opencomputeproject/Time-Appliance-Project/SOM/FPGA/Binaries/200T/README.md

# 200T FPGA version for the Artix 7 AC7200 SOM Module

* TimeCard200T.bit to flash the FPGA (volatile)
* Factory_TimeCard200T.bin to load the SPI flash via JTAG (Golden Image + Update Image)
* **IMPORTANT**: TimeCard200T.bin to updated the SPI flash via SPI starting @ **0x00800000** (Update Image only)
* TimeCard200T_Gotham.bin is basically the same as TimeCard200T.bin but the file has additional header information ([See tft tool](https://github.com/opencomputeproject/Time-Appliance-Project/tree/master/Software/tft))
