opencomputeproject/Time-Appliance-Project/FPGA/Binary/Production/Readme_Production.pdf

## 1 Design Overview

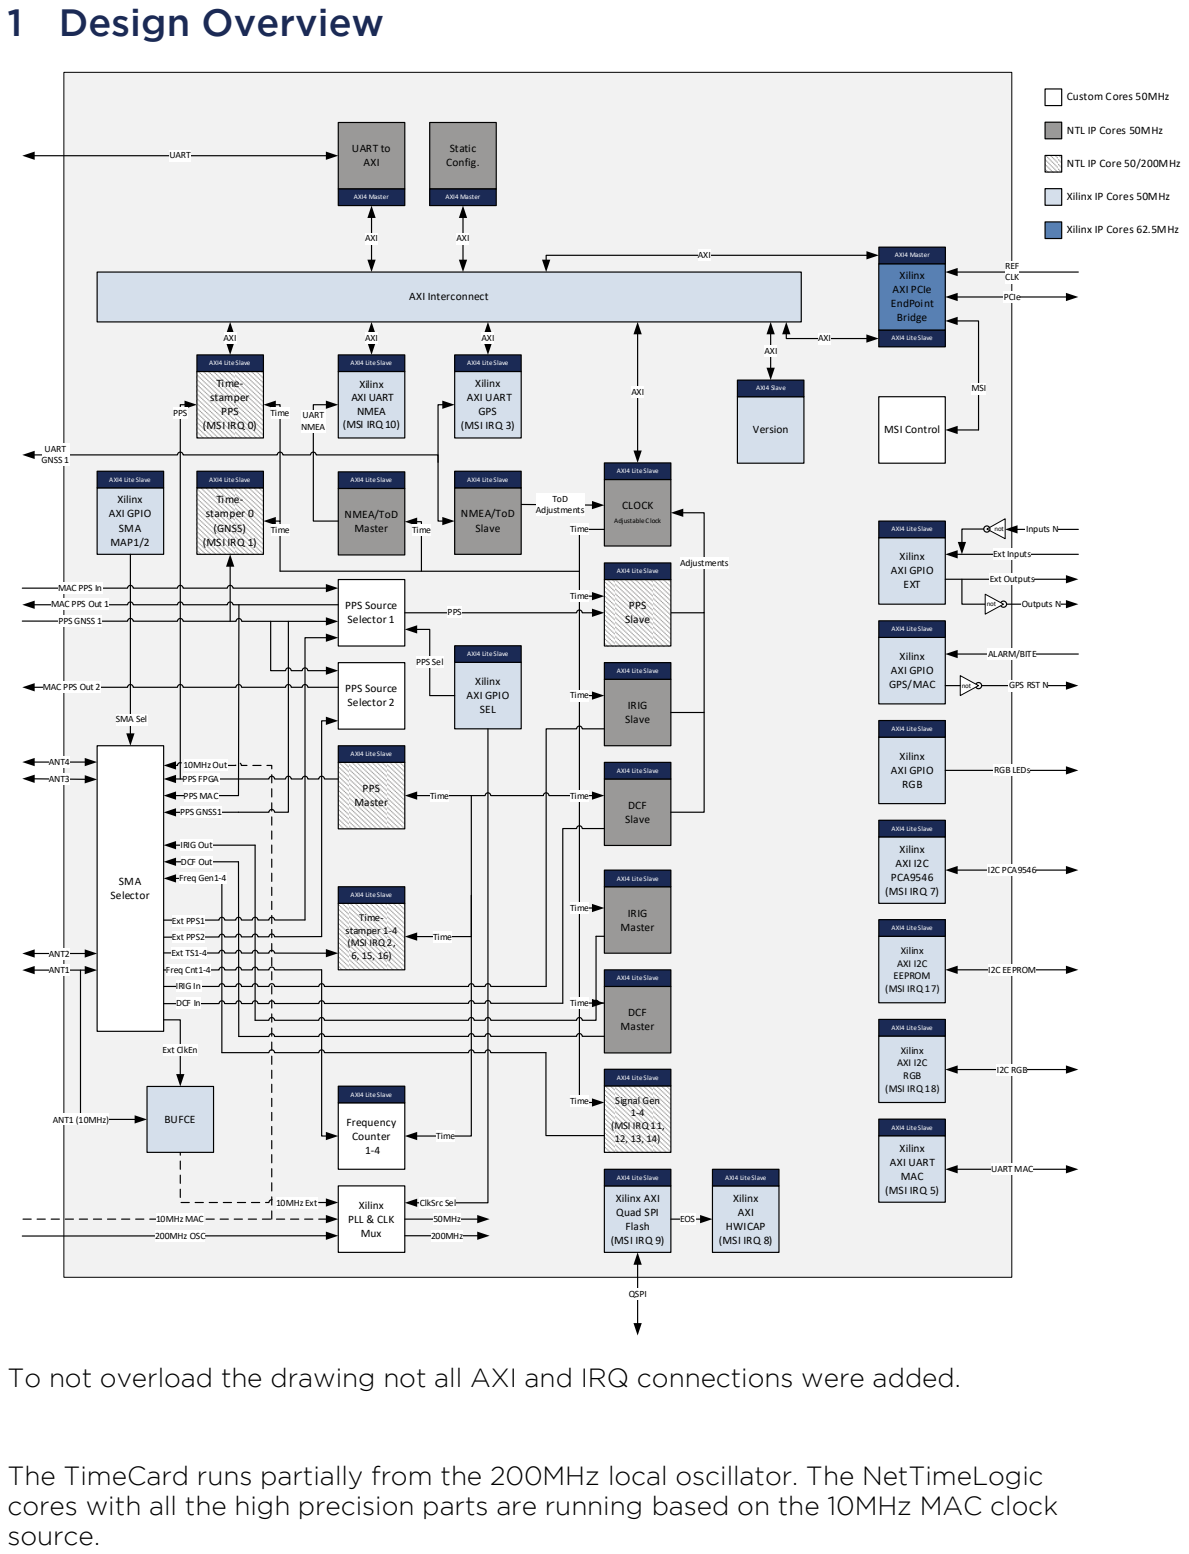
[picture p84: page 1]
Time; PPS; 200MHz OSC; ToD Adjustments; Adjustments; 50MHz; 200MHz; 10MHz Out; Xilinx AXI GPIO GPS/MAC; AXI4 Lite Slave; Xilinx AXI GPIO EXT; (MSI IRQ 5); Ext Outputs; Ext Inputs; GPS RST N; ALARM/BITE; not; 10MHz Ext; Xilinx AXI I2C PCA9546 (MSI IRQ 7); I2C PCA9546; AXI; Xilinx AXI Quad SPI Flash (MSI IRQ 9); QSPI; Xilinx AXI HWICAP (MSI IRQ 8); EOS; ANT2; ANT1; ANT4; ANT3; SMA Selector; Ext ClkEn; ANT1 (10MHz); BUFCE; Xilinx AXI PCIe EndPoint Bridge; AXI4 Master; PCIe; REF CLK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

NTL IP Cores 50MHz

NTL IP Core 50/200MHz

Xilinx IP Cores 50MHz

Xilinx IP Cores 62.5MHz

NMEA/ToD Master

MAC PPS In
MAC PPS Out 1
PPS GNSS 1

MAC PPS Out 2

AXI4 Lite Slave
Xilinx
AXI UART MAC

PLL & CLK Mux

To not overload the drawing not all AXI and IRQ connections were added.

The TimeCard runs partially from the 200MHz local oscillator. The NetTimeLogic
cores with all the high precision parts are running based on the 10MHz MAC clock
source.

## 1.1 Status LEDs

At the moment the Status LEDs are not connected to the AXI GPIO Ext and they

are used directly by the FPGA.

LED1: Alive LED of the FPGA internal Clock (50MHz)

LED2: Alive LED of the PCIe clocking part (62.5MHz)

LED3: PPS of the FPGA (Time of the Local Clock via PPS Master)

LED4: PPS of the MAC (differential inputs from the MAC via diff-buffer)

The RGB LEDs (SMA1-4 and GNSS) can be controlled via I2C or GPIO (depending

on assembly option).
In case the Fall-Back image is loaded all four SMA LEDs are blinking red.

## 1.2 AXI Address Mapping

The AXI interconnect has three masters which all have access to the slaves. One is the AXI PCIe interface and the other UART to AXI have all the time access. The

Static Configuration only does a basic configuration after reset.

The AXI Slave Interfaces have following addresses:

AXI Slave interface | Slave | Offset Address | High Address
S_AXI_CTL | AXI PCIe Control | 0x0001_0000 | 0x0001_0FFF
axi4l_slave | Version | 0x0002_0000 | 0x0002_0FFF
S_AXI | AXI GPIO Ext | 0x0010_0000 | 0x0010_0FFF
S_AXI | AXI GPIO GPS/MAC | 0x0011_0000 | 0x0011_0FFF
S_AXI | AXI GPIO SEL | 0x0013_0000 | 0x0013_0FFF
S_AXI | AXI GPIO SMA MAP1 | 0x0014_0000 | 0x0014_0FFF
S_AXI | AXI I2C PCA9546 | 0x0015_0000 | 0x0015_FFFF
S_AXI | AXI UART 16550 GPS | 0x0016_0000 | 0x0016_FFFF
S_AXI | AXI UART 16550 GPS2 | 0x0017_0000 | 0x0017_FFFF
S_AXI | AXI UART 16550 MAC | 0x0018_0000 | 0x0018_FFFF
S_AXI | AXI UART 16550 NMEA | 0x0019_0000 | 0x0019_FFFF
S_AXI | AXI I2C EEPROM | 0x0020_0000 | 0x0020_FFFF
S_AXI | AXI I2C RGB | 0x0021_0000 | 0x0021_FFFF
S_AXI | AXI GPIO SMA MAP2 | 0x0022_0000 | 0x0022_0FFF
S_AXI | AXI GPIO RGB | 0x0023_0000 | 0x0023_FFFF
S_AXI_LITE | AXI HWICAP | 0x0030_0000 | 0x0030_FFFF
AXI_LITE | AXI Quad SPI Flash | 0x0031_0000 | 0x0031_FFFF
axi4l_slave | NTL Adj. Clock | 0x0100_0000 | 0x0100_FFFF

axi4l_slave | NTL Signal TS0 (GNSS) | 0x0101_0000 | 0x0101_FFFF
axi4l_slave | NTL Signal TS1 | 0x0102_0000 | 0x0102_FFFF
axi4l_slave | NTL PPS Master | 0x0103_0000 | 0x0103_FFFF
axi4l_slave | NTL PPS Slave | 0x0104_0000 | 0x0104_FFFF
axi4l_slave | NTL TOD Slave | 0x0105_0000 | 0x0105_FFFF
axi4l_slave | NTL Signal TS2 | 0x0106_0000 | 0x0106_FFFF
axi4l_slave | NTL IRIG Slave | 0x0107_0000 | 0x0107_FFFF
axi4l_slave | NTL IRIG Master | 0x0108_0000 | 0x0108_FFFF
axi4l_slave | NTL DCF Slave | 0x0109_0000 | 0x0109_FFFF
axi4l_slave | NTL DCF Master | 0x010A_0000 | 0x010A_FFFF
axi4l_slave | NTL TOD Master | 0x010B_0000 | 0x010B_FFFF
axi4l_slave | NTL Signal TS PPS | 0x010C_0000 | 0x010C_FFFF
axi4l_slave | NTL Signal Generator1 | 0x010D_0000 | 0x010D_FFFF
axi4l_slave | NTL Signal Generator2 | 0x010E_0000 | 0x010E_FFFF
axi4l_slave | NTL Signal Generator3 | 0x010F_0000 | 0x010F_FFFF
axi4l_slave | NTL Signal Generator4 | 0x0110_0000 | 0x0110_FFFF
axi4l_slave | NTL Signal TS3 | 0x0111_0000 | 0x0111_FFFF
axi4l_slave | NTL Signal TS4 | 0x0112_0000 | 0x0112_FFFF
axi4l_slave | Frequency Counter 1 | 0x0120_0000 | 0x0120_FFFF
axi4l_slave | Frequency Counter 2 | 0x0121_0000 | 0x0121_FFFF
axi4l_slave | Frequency Counter 3 | 0x0122_0000 | 0x0122_FFFF
axi4l_slave | Frequency Counter 4 | 0x0123_0000 | 0x0123_FFFF

NOTE:

The Version Slave has one single 32-Bit Register. The upper 16 Bits show the version number of the golden image and the lower 16 Bits the version number of

the regular image.

E.g.
Register 0x0200_0000 of the Golden image shows: 0x8001_0000

Register 0x0200_0000 of the Regular image shows: 0x0000_8003

If the lower 16 Bits are 0x0000 the Golden image has booted. Additionally, the SMA LEDs are blinking red.

## 1.3 Clock Adjustment Sources

The Adjustable Clock supports different adjustment sources:

- PPS (with GNSS) (register value 3)
- IRIG (register value 2)
- DCF (register value 6)

By default, PPS with GNSS is selected. The other time sources can be selected via

the NTL Adj. Clock ClockSelect Register (Offset: 0x0100_0008).

## 1.4 Message-Signaled Interrupt Mapping

The interrupts in the design are connected to the MSI Vector of the AXI Memory

Mapped to PCI Express Core via a MSI controller. The PCI Express Core needs to set the MSI_enable to ‘1’. The MSI controller sends INTX_MSI Request with the

MSI_Vector_Num to the PCI Express Core and with the INTX_MSI_Grant the interrupt is acknowledged. If there are several interrupts pending the messages are sent with the round-robin principle. Level interrupts (e.g. AXI UART 16550) are taking at least one round for the next interrupt.

MSI Number | Interrupt Source
0 | NTL Signal TS PPS
1 | NTL Signal TS0
2 | NTL Signal TS1
3 | AXI UART 16550 GPS
4 | AXI UART 16550 GPS2
5 | AXI UART 16550 MAC
6 | NTL Signal TS2
7 | AXI I2C PCA9546
8 | AXI HWICAP
9 | AXI Quad SPI Flash
10 | AXI UART 16550 NMEA
11 | NTL Signal Generator1
12 | NTL Signal Generator2
13 | NTL Signal Generator3
14 | NTL Signal Generator4
15 | NTL Signal TS3
16 | NTL Signal TS4
17 | AXI I2C EEPROM
18 | AXI I2C RGB

## 1.5 Connectors (SMA) / SMA Connection Matrix

The SMA connectors have following default mapping:

ANT1:

10MHz Clock input

ANT2:

PPS Input

ANT3:
10MHz Clock output (looped 10MHz Clock →MAC RF OUT

(after clock buffer)

ANT4:
PPS Output from the PPS Master

This default mapping and the direction can be changed via AXI GPIO SMA MAP1 and AXI GPIO SMA MAP2.

GPIO is used to select the inputs and GPIO2 to select the outputs.

AXI GPIO SMA MAP1

Mapping of Input 1 (ANT1) with GPIO Bit 15 downto 0:

0 | 10MHz Clock from SMA connector (default)
1 | External PPS 1 (goes to PPS Source Selector 1)
2 | External PPS 2 (goes to PPS Source Selector 2)
4 | Signal goes to TS1
8 | Signal goes to TS2
16 | Signal goes IRIG Slave
32 | Signal goes to DCF Slave
64 | Signal goes to TS3
128 | Signal goes to TS4
256 | Signal goes to Frequency Counter 1
512 | Signal goes to Frequency Counter 2

1024 Signal goes to Frequency Counter 3

2048 Signal goes to Frequency Counter 4

32768 | Input Enable (default 1 → ANT1 is input)

The input can be mapped to several sinks. As example with the value 5 the

input is mapped as external PPS 1 and additionally it goes to TS1.

NOTE:
To use ANT1 as a system clock source only 0 is possible.

GNSS

INPUT: Default 10MHz

INPUT: Default 1 PPS

Output: Default 10MHz

Output: Default 1 PPS

ANT1

ANT2

ANT3

ANT4

Mapping of Input 2 (ANT2) with GPIO Bit 31 downto 16:

0 | no mapping of ANT2
1 | External PPS 1 (goes to PPS Source Selector 1) (default)
2 | External PPS 2 (goes to PPS Source Selector 2)
4 | Signal goes to TS1
8 | Signal goes to TS2
16 | Signal goes IRIG Slave
32 | Signal goes to DCF Slave
64 | Signal goes to TS3
128 | Signal goes to TS4
256 | Signal goes to Frequency Counter 1
512 | Signal goes to Frequency Counter 2

1024 Signal goes to Frequency Counter 3

2048 Signal goes to Frequency Counter 4

32768 | Input Enable (default 1 → ANT2 is input)

The input can be mapped to several sinks. As example with the value 9 the

input is mapped as external PPS 1 and additionally it goes to TS2.

NOTE:
If a lower input has already a mapping to a sink the Input2 mapping will be

ignored.

Mapping of Output 3 (ANT3) with GPIO2 Bit 15 downto 0:
0 | 10MHz Clock Output from the MAC (default)
1 | PPS from the FPGA (PPS Master)
2 | PPS from the MAC
4 | PPS from GNSS 1
8 | PPS from GNSS 2
16 | IRIG Master Output
32 | DCF Master Output
64 | Signal Generator 1 Output
128 | Signal Generator 2 Output
256 | Signal Generator 3 Output
512 | Signal Generator 4 Output

8192 GND

16384 VCC

32768 | Output Enable (default 1 → ANT3 is output)

Every other value maps the 10MHz Clock Output from the MAC to the

output

Mapping of Output 4 (ANT4) with GPIO2 Bit 31 downto 16:

0 | 10MHz Clock Output from the MAC
1 | PPS from the FPGA (PPS Master) (default)
2 | PPS from the MAC
4 | PPS from GNSS 1
8 | PPS from GNSS 2
16 | IRIG Master Output
32 | DCF Master Output
64 | Signal Generator 1 Output
128 | Signal Generator 2 Output
256 | Signal Generator 3 Output
512 | Signal Generator 4 Output

8192 GND
16384 VCC
32768 | Output Enable (default 1 → ANT4 is output)

Every other value maps the PPS from the FPGA (PPS Master) to the output

AXI GPIO SMA MAP2
Mapping of Input 3 (ANT3) with GPIO Bit 15 downto 0:
0 | no mapping of ANT3
1 | External PPS 1 (goes to PPS Source Selector 1)
2 | External PPS 2 (goes to PPS Source Selector 2)
4 | Signal goes to TS1
8 | Signal goes to TS2
16 | Signal goes IRIG Slave
32 | Signal goes to DCF Slave
64 | Signal goes to TS3
128 | Signal goes to TS4
256 | Signal goes to Frequency Counter 1
512 | Signal goes to Frequency Counter 2

1024 Signal goes to Frequency Counter 3

2048 Signal goes to Frequency Counter 4

32768 | Input Enable (default 0 → ANT3 is output)

The input can be mapped to several sinks. As example with the value 5 the

input is mapped as external PPS 1 and additionally it goes to TS1.

Mapping of Input 4 (ANT4) with GPIO Bit 31 downto 16:

0 | no mapping of ANT2
1 | External PPS 1 (goes to PPS Source Selector 1)
2 | External PPS 2 (goes to PPS Source Selector 2)
4 | Signal goes to TS1
8 | Signal goes to TS2
16 | Signal goes IRIG Slave
32 | Signal goes to DCF Slave
64 | Signal goes to TS3
128 | Signal goes to TS4
256 | Signal goes to Frequency Counter 1
512 | Signal goes to Frequency Counter 2

1024 Signal goes to Frequency Counter 3

2048 Signal goes to Frequency Counter 4

32768 | Input Enable (default 0 → ANT4 is output)

The input can be mapped to several sinks. As example with the value 9 the

input is mapped as external PPS 1 and additionally it goes to TS2.

NOTE:
If a lower input has already a mapping to a sink the Input4 mapping will be ignored.

Mapping of Output 1 (ANT1) with GPIO2 Bit 15 downto 0:

0 | 10MHz Clock Output from the MAC
1 | PPS from the FPGA (PPS Master)
2 | PPS from the MAC
4 | PPS from GNSS 1
8 | PPS from GNSS 2
16 | IRIG Master Output
32 | DCF Master Output
64 | Signal Generator 1 Output
128 | Signal Generator 2 Output
256 | Signal Generator 3 Output
512 | Signal Generator 4 Output

8192 GND

16384 VCC

32768 | Output Enable (default 0 → ANT1 is input)

Every other value maps the 10MHz Clock Output from the MAC to the

output

Mapping of Output 2 (ANT2) with GPIO2 Bit 31 downto 16:
0 | 10MHz Clock Output from the MAC
1 | PPS from the FPGA (PPS Master)
2 | PPS from the MAC
4 | PPS from GNSS 1
8 | PPS from GNSS 2
16 | IRIG Master Output
32 | DCF Master Output
64 | Signal Generator 1 Output
128 | Signal Generator 2 Output
256 | Signal Generator 3 Output
512 | Signal Generator 4 Output

8192 GND

16384 VCC

32768 | Output Enable (default 0 → ANT2 is input)

Every other value maps the PPS from the FPGA (PPS Master) to the output.

## 1.6 GPIO Mapping

GPIO (Offset 0x0000)
GPIO2 (Offset 0x0008)

Inputs or Outputs might high or low active for the external signal level. The inversion is done in the FPGA. On the AXI GPIO always

active high is used. The inverted signals are underlined in the tables below.

AXI GPIO Ext

REG | Bit7 | Bit6 | Bit5 | Bit4 | Bit3 | Bit2 | Bit1 | Bit0
GPIO (in) | - Board | Rev2 | Board Rev1 | Board Rev0 | - | - | - | -
GPIO2 (out) | - | - | - | EEPROM WP | LED4 (NC atm) | LED3 (NC atm) | LED2 (NC atm) | LED1 (NC atm)
REG | Bit15 | Bit14 | Bit13 | Bit12 | Bit11 | Bit10 | Bit9 | Bit8
GPIO (in) | - | - | - | Bno Int | Lm75B Int3 | Lm75B Int2 | Lm75B Int1 | Sht3x Alert
GPIO2 (out) | - | Debug USB MuxSel | SMBUS I2C BufEn | Bno Boot | Bno Rst | Sht3x Rst | RGB Shut Down | Pca9546 Rst

AXI GPIO GPS/MAC

REG | Bit7 | Bit6 | Bit5 | Bit4 | Bit3 | Bit2 | Bit1 | Bit0
GPIO (in) | - | - | - | - | - | - | MAC BITE | MAC ALARM
GPIO2 (out) | - | - | - | - | - | - | - | GPS RST

AXI GPIO SEL

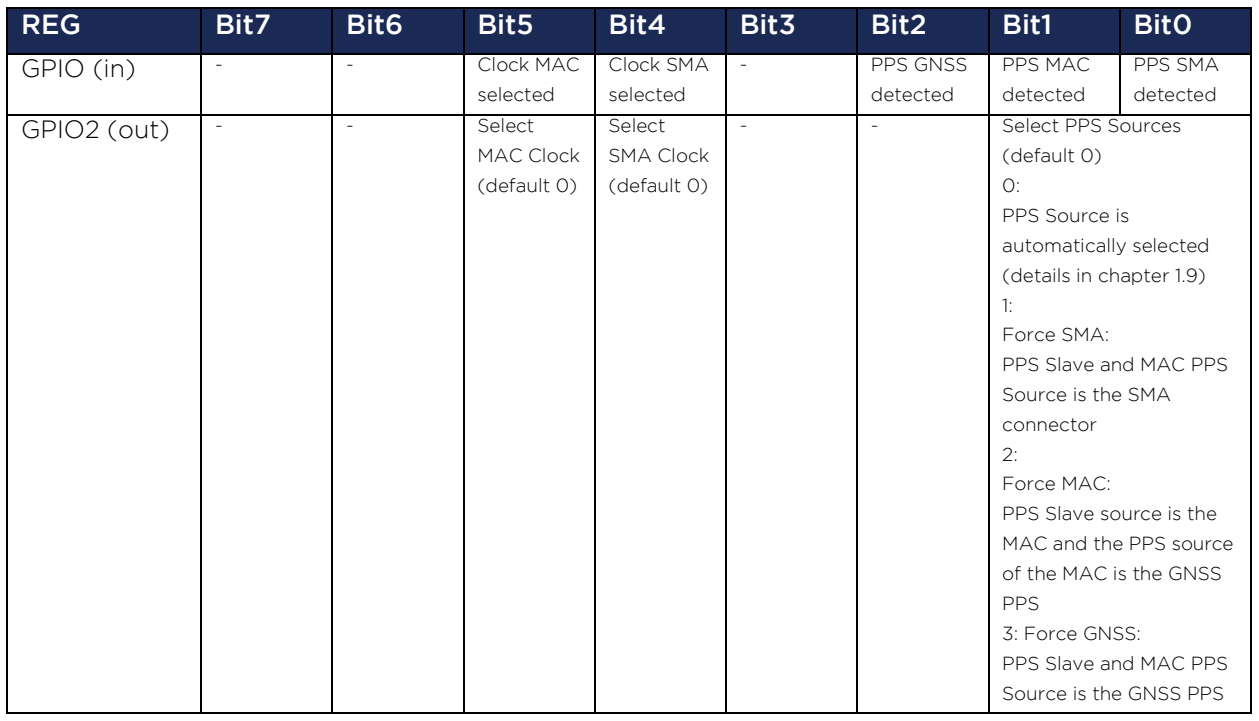
[picture p85: figure]
GPIO2 (out); Select; MAC Clock; (default 0); SMA Clock; Select PPS Sources; PPS Source is; automatically selected; (details in chapter 1.9); Force SMA:; PPS Slave and MAC PPS; Source is the SMA; connector; Force MAC:; PPS Slave source is the; MAC and the PPS source; of the MAC is the GNSS; PPS; 3: Force GNSS:; Source is the GNSS PPS

REG | Bit7 | Bit6 | Bit5 | Bit4 | Bit3 | Bit2 | Bit1 | Bit0
GPIO (in) | - | - | Clock MAC selected | Clock SMA selected | - PPS GNSS | detected | PPS MAC detected | PPS SMA detected

AXI GPIO RGB

‘1’: ON; ‘0’: OFF

| Bit7 | Bit6 | Bit5 | Bit4 | Bit3 | Bit2 | Bit1 | Bit0
GPIO (out) | - | SMA2 Blue | SMA2 Green | SMA2 Red | - SMA1 | Blue | SMA1 Green | SMA1 Red
| Bit15 | Bit14 | Bit13 | Bit12 | Bit11 | Bit10 | Bit9 | Bit8
GPIO (out) | - | SMA4 Blue | SMA4 Green | SMA4 Red | - SMA3 | Blue | SMA3 Green | SMA3 Red

| Bit23 | Bit22 | Bit21 | Bit20 | Bit19 | Bit18 | Bit17 | Bit16
GPIO (out) | - | - | - | - | - | GNSS Blue | GNSS Green | GNSS Red

AXI GPIO SMA MAP1 (ANT1/ANT2 as inputs, ANT3/ANT4 as outputs)

REG | Bit15 | Bit14-12 | Bit11 | B10 | Bit9 | Bit8 | Bit7 | Bit6 | Bit5 | Bit4 | Bit3 | Bit2 | Bit1 | Bit0
GPIO (out) | Input Enable | unused | ANT1 to Freq Cnt 4 input | ANT1 to Freq Cnt 3 input | ANT1 to Freq Cnt 2 input | ANT1 to Freq Cnt 1 input | ANT1 to TS4 input | ANT1 to TS3 input | ANT1 to DCF Slave | ANT1 to IRIG Slave | ANT1 to TS2 input | ANT1 to TS1 input | ANT1 to PPS 2 input | ANT1 to PPS 1 input
GPIO2 (out) | Output Enable

Bit 14-0 are 0: 10MHz to ANT3

Bit 0 is set: FPGA PPS to ANT3

Bit 1 is set: MAC PPS to ANT3

Bit 2 is set: GNSS1 PPS to ANT3

Bit 3 is set: GNSS2 PPS to ANT3

Bit 4 is set: IRIG Output to ANT3

Bit 5 is set: DCF Output to ANT3

Bit 6 is set: Signal Generator 1 to ANT3

Bit 7 is set: Signal Generator 2 to ANT3

Bit 8 is set: Signal Generator 3 to ANT3

Bit 9 is set: Signal Generator 4 to ANT3

Bit 13 is set: GND to ANT3

Bit 14 is set: VCC to ANT3

NOTE: only one single Bit (of Bit 14-0) can be set at the same time
REG | Bit31 | Bit30-28 | Bit27 | Bit26 | Bit25 | Bit24 | Bit23 | Bit22 | Bit21 | Bit20 | Bit19 | Bit18 | Bit17 | Bit16
GPIO (out) | Input Enable | unused | ANT2 to Freq Cnt 4 input | ANT2 to Freq Cnt 3 input | ANT2 to Freq Cnt 2 input | ANT2 to Freq Cnt 1 input | ANT2 to TS4 input | ANT2 to TS3 input | ANT2 to DCF Slave | ANT2 to IRIG Slave | ANT2 to TS2 input | ANT2 to TS1 input | ANT2 to PPS 2 input | ANT2 to PPS 1 input
GPIO2 (out) | Output Enable | Bit 30-16 are 0: 10MHz to ANT4 Bit 16 is set: FPGA PPS to ANT4

Bit 17 is set: MAC PPS to ANT4

Bit 18 is set: GNSS1 PPS to ANT4

Bit 19 is set: GNSS2 PPS to ANT4

Bit 20 is set: IRIG Output to ANT4

Bit 21 is set: DCF Output to ANT4

Bit 22 is set: Signal Generator 1 to ANT4

Bit 23 is set: Signal Generator 2 to ANT4

Bit 24 is set: Signal Generator 3 to ANT4

Bit 25 is set: Signal Generator 4 to ANT4

Bit 26 is set: GND to ANT4

Bit 27 is set: VCC to ANT4

NOTE: only one single Bit (of Bit 30-16) can be set at the same time

AXI GPIO SMA MAP2 (ANT1/ANT2 as outputs, ANT3/ANT4 as inputs)

REG | Bit15 | Bit14-12 | Bit11 | B10 | Bit9 | Bit8 | Bit7 | Bit6 | Bit5 | Bit4 | Bit3 | Bit2 | Bit1 | Bit0
GPIO (out) | Input Enable | unused | ANT3 to Freq Cnt 4 input | ANT3 to Freq Cnt 3 input | ANT3 to Freq Cnt 2 input | ANT3 to Freq Cnt 1 input | ANT3 to TS4 input | ANT3 to TS3 input | ANT3 to DCF Slave | ANT3 to IRIG Slave | ANT3 to TS2 input | ANT3 to TS1 input | ANT3 to PPS 2 input | ANT3 to PPS 1 input
GPIO2 (out) | Output Enable

Bit 14-0 are 0: 10MHz to ANT1

Bit 0 is set: FPGA PPS to ANT1

Bit 1 is set: MAC PPS to ANT1

Bit 2 is set: GNSS1 PPS to ANT1

Bit 3 is set: GNSS2 PPS to ANT1

Bit 4 is set: IRIG Output to ANT1

Bit 5 is set: DCF Output to ANT1

Bit 6 is set: Signal Generator 1 to ANT1

Bit 7 is set: Signal Generator 2 to ANT1

Bit 8 is set: Signal Generator 3 to ANT1

Bit 9 is set: Signal Generator 4 to ANT1

Bit 13 is set: GND to ANT1

Bit 14 is set: VCC to ANT1

NOTE: only one single Bit (of Bit 14-0) can be set at the same time

REG | Bit31 | Bit30-28 | Bit27 | Bit26 | Bit25 | Bit24 | Bit23 | Bit22 | Bit21 | Bit20 | Bit19 | Bit18 | Bit17 | Bit16
GPIO (out) | Input Enable | unused | ANT4 to Freq Cnt 4 input | ANT4 to Freq Cnt 3 input | ANT4 to Freq Cnt 2 input | ANT4 to Freq Cnt 1 input | ANT4 to TS4 input | ANT4 to TS3 input | ANT4 to DCF Slave | ANT4 to IRIG Slave | ANT4 to TS2 input | ANT4 to TS1 input | ANT4 to PPS 2 input | ANT4 to PPS 1 input
GPIO2 (out) | Output Enable

Bit 30-16 are 0: 10MHz to ANT2

Bit 16 is set: FPGA PPS to ANT2

Bit 17 is set: MAC PPS to ANT2

Bit 18 is set: GNSS1 PPS to ANT2

Bit 19 is set: GNSS2 PPS to ANT2

Bit 20 is set: IRIG Output to ANT2

Bit 21 is set: DCF Output to ANT2

Bit 22 is set: Signal Generator 1 to ANT2

Bit 23 is set: Signal Generator 2 to ANT2

Bit 24 is set: Signal Generator 3 to ANT2

Bit 25 is set: Signal Generator 4 to ANT2

Bit 26 is set: GND to ANT2

Bit 27 is set: VCC to ANT2

NOTE: only one single Bit (of Bit 30-16) can be set at the same time

AXI GPIO SMA Status (all inputs):

REG | Bit13 | Bit12 | Bit11 | B10 | Bit9 | Bit8 | Bit7 | Bit6 | Bit5 | Bit4 | Bit3 | Bit2 | Bit1 | Bit0
GPIO (in) | ANT4 Input Value ‘0’ → low ‘1’ → high | ANT4 Input valid | - | - | ANT3 Input Value ‘0’ → low ‘1’ → high | ANT3 Input valid | - | - | ANT2 Input Value ‘0’ → low ‘1’ → high | ANT2 Input valid | - | - | ANT1 Input Value ‘0’ → low ‘1’ → high | ANT1 Input valid

## 1.7 Register Description

The detailed register descriptions of the NetTimeLogic Cores are available in the reference manuals:

../TimeCard/Doc/

The Documentations of the Xilinx Cores are online available.

AXI Memory Mapped to PCI Express:

https://www.xilinx.com/support/documentation/ip_documentation/axi_pcie/v2_8/pg055-axi-bridge-pcie.pdf
AXI GPIO:

https://www.xilinx.com/support/documentation/ip_documentation/axi_gpio/v2_0/pg144-axi-gpio.pdf
AXI I2C:

https://www.xilinx.com/support/documentation/ip_documentation/axi_iic/v2_0/pg090-axi-iic.pdf
AXI UART 16550:

https://www.xilinx.com/support/documentation/ip_documentation/axi_uart16550/v2_0/pg143-axi-uart16550.pdf
AXI Quad SPI:

https://www.xilinx.com/support/documentation/ip_documentation/axi_quad_spi/v3_2/pg153-axi-quad-spi.pdf
AXI HWICAP :

https://www.xilinx.com/support/documentation/ip_documentation/axi_hwicap/v3_0/pg134-axi-hwicap.pdf

### 1.7.1 IP Version remarks

In some FPGA upgrades new features were added. This means that some registers

might be only available in the latest version.
Read from not existing registers cause an AXI bus fault.

1.7.1.1 Production TimeCard V10

- New GNSS Status information/registers added (check TOD Slave reference

manual for all details)

- Added TSIPv1 message support for GNSS modules (check TOD Slave

reference manual for all details)

- Reduced Address Range of AXI GPIO IPs to 4k (0x0FFF)

### 1.7.2 Frequency Counter Registers

Since the frequency counter does not have a complete manual the register description is directly here:

Control Reg

Reg Description

31 | 30 | 29 | 28 | 27 | 26 | 25 | 24 | 23 | 22 | 21 | 20 | 19 | 18 | 17 | 16 | 15 | 14 | 13 | 12 | 11 | 10 | 9 | 8 | 7 | 6 | 5 | 4 | 3 | 2 | 1 | 0
- Number of Seconds
- Enable
RO | RW | RO | RW
Reset: 0x00000100

Offset: 0x0000

Name | Description | Bits | Access
- | Reserved, read 0 | Bit: 31:16 | RO
Number of Seconds | Number of seconds to measure the frequency over | Bit: 15:8 | RW
- | Reserved, read 0 | Bit: 7:1 | RO
Enable | Enable the Frequency Counter | Bit: 0 | RW

Frequency Reg

Reg Description

31 | Error 30 | Overrun 29 | 28 27 26 25 24 | 23 22 21 20 19 18 17 16 15 14 13 12 11 10 9 8 7 6 5 4 3 2 1 0 Valid
RO | RO | RO | RO | RO
- Frequency

Reset: 0x00000000

Offset: 0x0004

Name | Description | Bits | Access
Valid | Measurement is valid | Bit: 31 | RO
Error | Measurement error | Bit: 30 | RO
Overrun | Measurement exceeded 10000000 | Bit: 29 | RO
- | Reserved, read 0 | Bit: 28:24 | RO
Frequency | Frequency in Hz, min 0, max 10000000 | Bit: 23:0 | RO

## 1.8 Clock Selector

The design can run on different source clocks. It’s important that at least the source

clock of the SOM module is always available. In the FPGA design an automatic

source clock selection is running. The design detects if a clock is available and does

then the selection base on following priorities:

1. External 10MHz Clock from SMA connector
2. 10MHz Clock of MAC

This selection can be overwritten by the AXI GPIO Sel GPIO2. When a clock is selected the FPGA checks if this clock is available. If the selected clock is not

detected the automatic selection is applied.

Via the GPIO Sel GPIO it can be checked which one is the selected clock. If all

values are 0 the full design is running from the SOM Module Clock.

## 1.9 PPS Source Selector

The PPS Source Selector 1 can be controlled by AXI GPIO Sel GPIO2 Bit 0 and 1. There are three different PPS Sources (GNSS, MAC, SMA Connector) which can go to the two PPS Sinks (PPS Slave, MAC PPS Input). By default, the selection is done

automatically. The source selector checks if a PPS is detected.

Depending on the availability the automatic selection has following priorities:

1. PPS SMA connector
2. PPS MAC
3. PPS GNSS

The switch happens once the PPS Sources are logical 0.

Following selection is done if a source is available:

1. SMA PPS is detected:

SMA PPS source to PPS MAC sink

SMA PPS source to PPS Slave sink

2. MAC PPS is detected:

GNSS PPS source to PPS MAC sink

MAC PPS source to PPS Slave sink

3. GNSS PPS is detected:
GNSS PPS source to PPS MAC sink

GNSS PPS source to PPS Slave sink

The PPS Source Selector 2 selects only the PPS toward the MAC PPS 2. There is no

control or supervision via GPIO available. Possible sources are the 2

nd GNSS PPS
and a PPS from ANT1/2. From the available sources the ANT1/2 has higher priority

over the 2

nd GNSS PPS.

## 1.10GNSS Requirements

The GNSS Source must be GPS, Galileo or Beidou. GLONASS only will not work.

## 1.11 Static configuration

The FPGA starts with a static configuration with following settings:

- PPS (including TOD) is used as correction input for the clock
- PPS Slave Pulse detection on rising edge
- PPS Slave cable delay 0
- TOD Slave UART Baudrate is 115200
- TOD Slave UART polarity default
- TOD Slave in UBX Mode, all GNSS and no messages disabled
- PPS Master polarity rising edge
- PPS Master cable delay 0
- PPS Master pulse width 100 ms
- Clock, PPS Slave, TOD Slave and PPS Master are enabled
- All Timestampers are disabled
- IRIG Slave/Master are disabled
- DCF Slave/Master are disabled
- TOD/NMEA Master is disabled

## 2 Program FPGA and SPI Flash

For the initial programming of the FPGA and SPI Flash the JTAG programmer is

needed and has to be connected to the USB JTAG.
After a successfully programmed FPGA, the design contains an AXI QUAD SPI Core which allows field updates.

## 2.1 Bitstreams with Fallback Configuration

The FPGA design in split into two different bitstreams/bin-files to allow a failsafe

field update. The FPGA configuration starts always at Addr0 where the Golden

image with the start address of the Update image is located. It jumps directly to

this address and tries to load the Update image. If this load fails it falls back to the

Golden image.

Details about this Multiboot/Fallback approach can be found in following

Application Note:

https://www.xilinx.com/support/documentation/application_notes/xapp1246-multiboot-bpi.pdf

The Golden/Fallback image contains only a limited functionality which provides

access to the SPI Flash. The second image is used for normal operation and it is the

one which is replaced in a field update.

Factory_TimeCardProduction.bin
This image contains two bitstreams and it shall be used to program the SPI flash

for the first time as example in the factory. The first bitstream is the Golden/Fallback image and the second the latest version of the regular image.

This combined image has following structure:

===================================

Configuration Memory information

===================================

File Format | BIN
Interface | SPIX4
Size | 32M
Start Address | 0x00000000
End Address | 0x01FFFFFF
Addr1 | Addr2 | File(s)
0x00000000 | 0x002856FF | Golden_TimeCardProduction.bit
0x00400000 | 0x0069B5AB | TimeCardProduction.bit

TimeCardProduction.bin
This is the update/regular image and it shall be used for the field update via SPI.

For the update this bitstream must be placed at 0x00400000 in the SPI flash.

## 2.2 JTAG Programming (volatile)

This will only load the FPGA SRAM, after a power cycle this will be lost.

1. Go to the Hardware Manager in Vivado and Select “Open Target” → “Auto

Connect”. After this step following view is available:


2. Right klick on “xc7a100t_0(1)”, a menu will popup
3. Choose “Program Device” from the menu, the following window will pop up


4. Select the bitstream you want to program:

TimeCardProduction.bit
5. Press Program and wait for completion
6. The RUN LED will blink

## 2.3 SPI Programming (non-volatile)

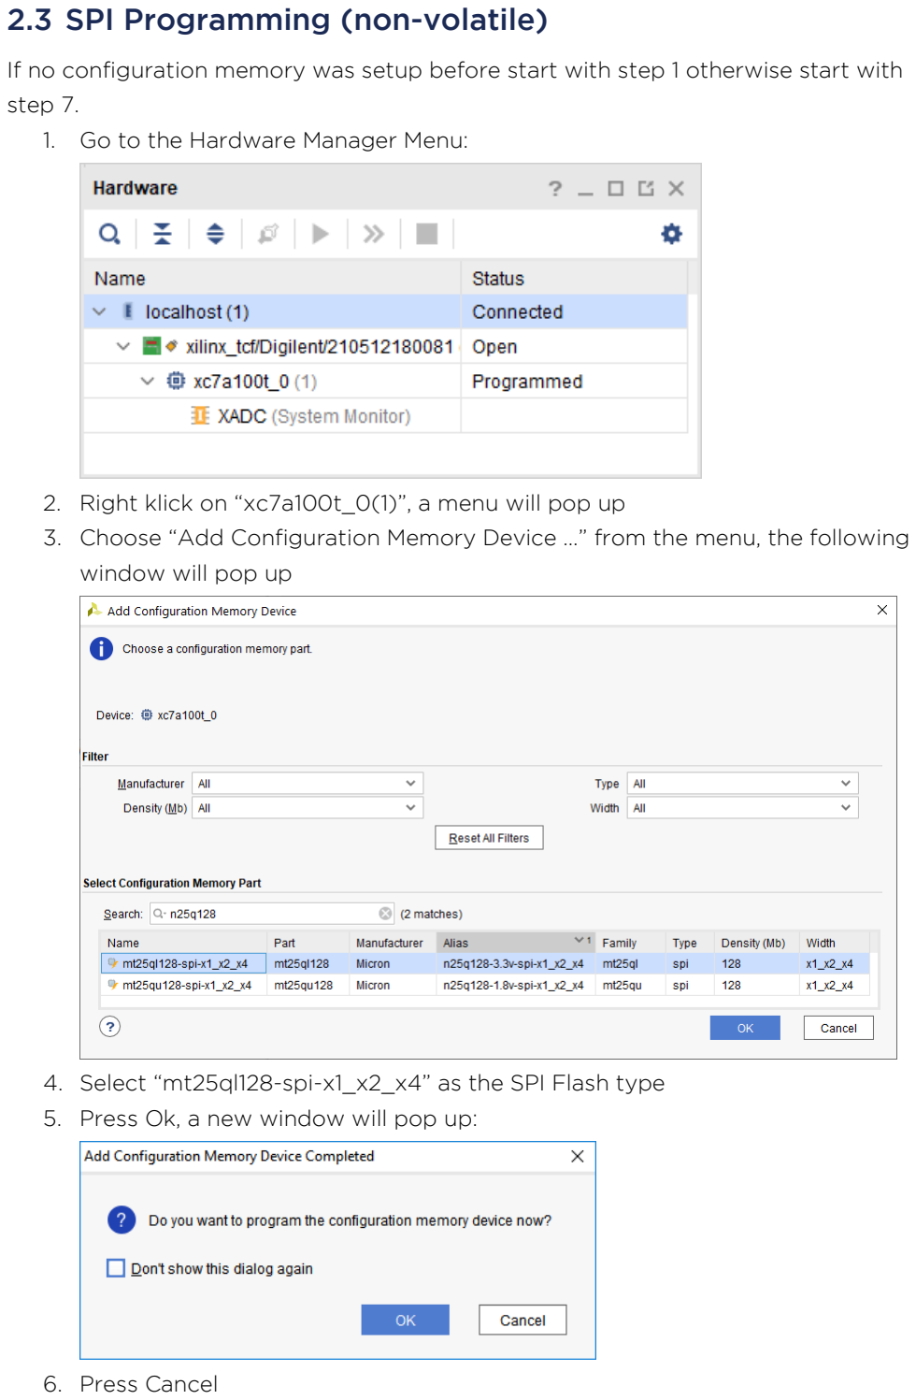
[picture p86: page 22]

If no configuration memory was setup before start with step 1 otherwise start with

step 7.
1. Go to the Hardware Manager Menu:
2. Right klick on “xc7a100t_0(1)”, a menu will pop up
3. Choose “Add Configuration Memory Device …” from the menu, the following

window will pop up

4. Select “mt25ql128-spi-x1_x2_x4” as the SPI Flash type
5. Press Ok, a new window will pop up:
6. Press Cancel

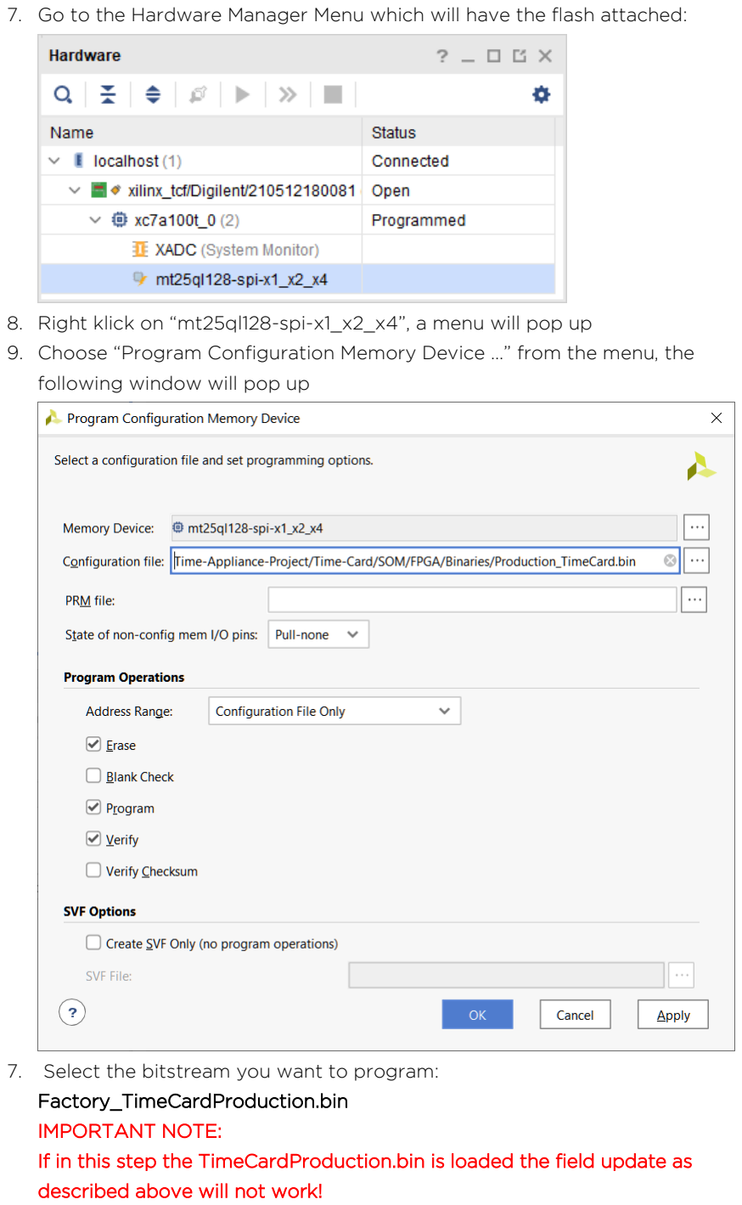
[picture p87: page 23]

7. Go to the Hardware Manager Menu which will have the flash attached:
8. Right klick on “mt25ql128-spi-x1_x2_x4”, a menu will pop up
9. Choose “Program Configuration Memory Device …” from the menu, the

following window will pop up

7. Select the bitstream you want to program:

Factory_TimeCardProduction.bin

IMPORTANT NOTE:
If in this step the TimeCardProduction.bin is loaded the field update as

described above will not work!

8. Press Ok and wait for completion
9. Disconnect the JTAG interface from the board
10. Power cycle or Reset the board / Cold start of the PC
11. The RUN LED will blink

## 2.4 Connect NetTimeLogic Configuration Manager to FPGA

1. Connect the USB/UART to a Host PC running Windows.
2. Start NetTimeLogic’s UniversalConfigurationManager Tool
3. Select the COM Port where the Board is connected to and press Open. Then the Address map of the cores instantiated are shown and 111 new Tabs

appear (CLK Clock, PPS Master, PPS Slave, TOD Slave, IRIG Slave, IRIG

Master, DCF Slave, DCF Master, TOD Master, Clk Signal Generator and Clk

Timestamper):


4. Change your configuration as you need it and press write. E.g.
In the Advanced Tab it is possible to load configuration files by selecting a

config file and pressing Load Config. Additionally, manual read or write of

registers with the Field Address and Value is possible.

NOTE:
The Universal Configuration Manager communicates via UART commands and an

internal IP Core converts them into AXI Memory Mapped register accesses.

Details about the protocol which can be used over any serial terminal is available

here:
https://www.nettimelogic.com/resources/Ucm_UniversalConfigurationManager_R

eferenceManual.pdf (https://www.nettimelogic.com/resources/Ucm_UniversalConfigurationManager_ReferenceManual.pdf)

## 3 TestApp

The TestApp is used to do some basic testing of the Hardware. It basically uses

mmap to the address space of the PCIe mapped address.

Before access two the PCIe end device is possible two steps are required. First the PCIe device must be detected by the system this can be checked with following

command:

lspci -v

01:00.0 Memory controller: Xilinx Corporation Device 7011

Subsystem: Xilinx Corporation Device 0007

Flags: fast devsel

Memory at 90000000 (32-bit, non-prefetchable) [disabled] [size=32M]

Capabilities: <access denied>

The PCIe device is detected at address 0x9000_0000 but it is disabled. As a

second step the device must be enabled:

sudo setpci -s "01:00.0" COMMAND=0x02

Now the TestApp is ready to start. The TestApp requires the PCIe base address as

an argument:

sudo ./TestApp 0x90000000

The App reads the version of the NetTimeLogic IP cores and set the system time to

the Adjustable Clock. After that it ready every second the time back from the

Adjustable Clock:

PCIe Base Address is set to 0x90000000

Clock IP Core Version = 0x1020000

Signal TS IP Core Version = 0x1020001

Signal TS IP Core Version = 0x1020001

PPS Master IP Core Version = 0x1020000

PPS Slave IP Core Version = 0x1020000

TOD Slave IP Core Version = 0x2000001

Selected Clk Source is: PPS

Selected Clk Source is: REGS

Set the current local time and date: Fri Oct 23 14:00:35 2020

The time is: 14:00:35 and 3240 ns

The time is: 14:00:36 and 305900 ns

The time is: 14:00:37 and 490780 ns

The time is: 14:00:38 and 671200 ns

The time is: 14:00:39 and 1031680 ns

The time is: 14:00:40 and 1359140 ns

The time is: 14:00:41 and 1542180 ns

The time is: 14:00:42 and 1671980 ns

The time is: 14:00:43 and 1799580 ns
