opencomputeproject/Time-Appliance-Project/SOM/FPGA/Binaries/LitePCIe/README.md

**IMPORTANT**

**This is a preliminary (experimental) version of the Time Card with the [LitePcie](https://github.com/enjoy-digital/litepcie) core as the PCIe to AXIMM bridge.**

The Version with LitePCIe has different Memory-Mapped Offsets (+ 0x0200_0000) as well as different MSI-Numbers (+ 32).
The latest driver supports both versions of the Time Card

The LitePCIe Core supports MSI-X as well as PTM.
More details about PTM and LitePCIe can be found here: https://github.com/enjoy-digital/litepcie_ptm_test
