opencomputeproject/Time-Appliance-Project/GNSS/UBlox/NEO-M9N/Configs/README.md

# UBX NEO-M9N module configurations

- NEO-M9N-00B-00

In the subfolder are example base configurations available which should work with the Time-Card. They have the correct messages enabled and the correct settings for the Pulse Per Second. However, depending on the use-case there might be changes required.

# Required Messages
- NAV_TIME_UTC
- NAV_TIME_LS

# Optional Messages (for additional status information)
- NAV_STATUS
- MON_HW
- NAV_SAT
