opencomputeproject/Time-Appliance-Project/HW/MCAD/PCIE Bracket V4/time_card_bracket_v4.pdf

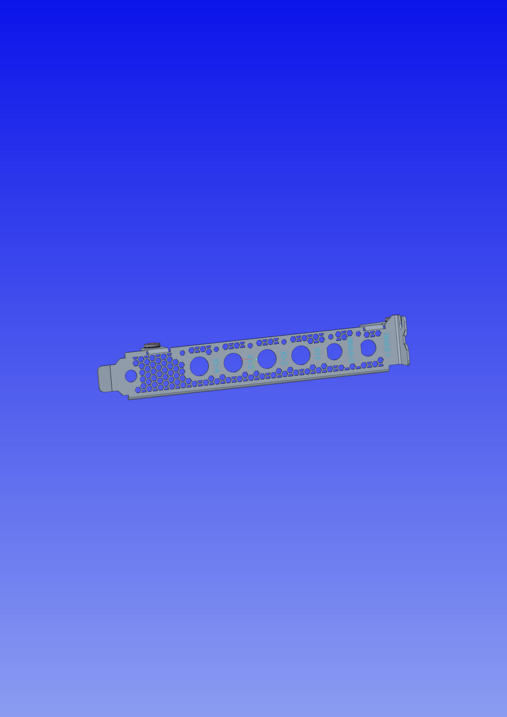
[picture p174: page 1]
