opencomputeproject/Time-Appliance-Project/DOC/Artwork/background.jpg

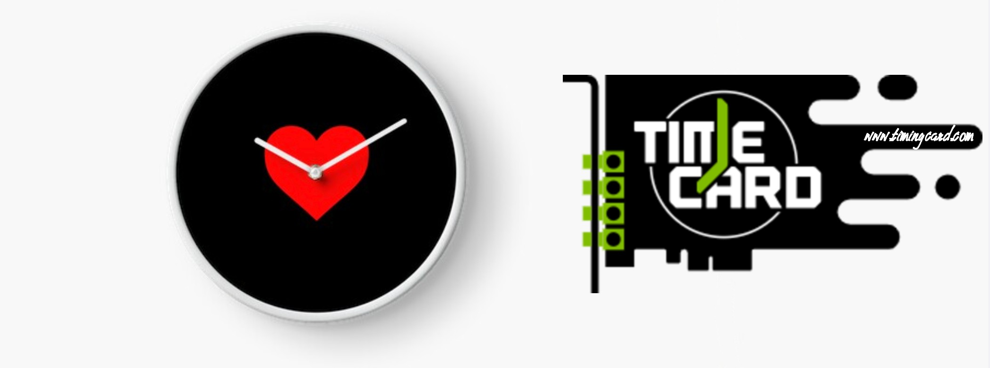
DOC/Artwork/background.jpg
