opencomputeproject/Time-Appliance-Project/DOC/Artwork/TIMECARD.jpg

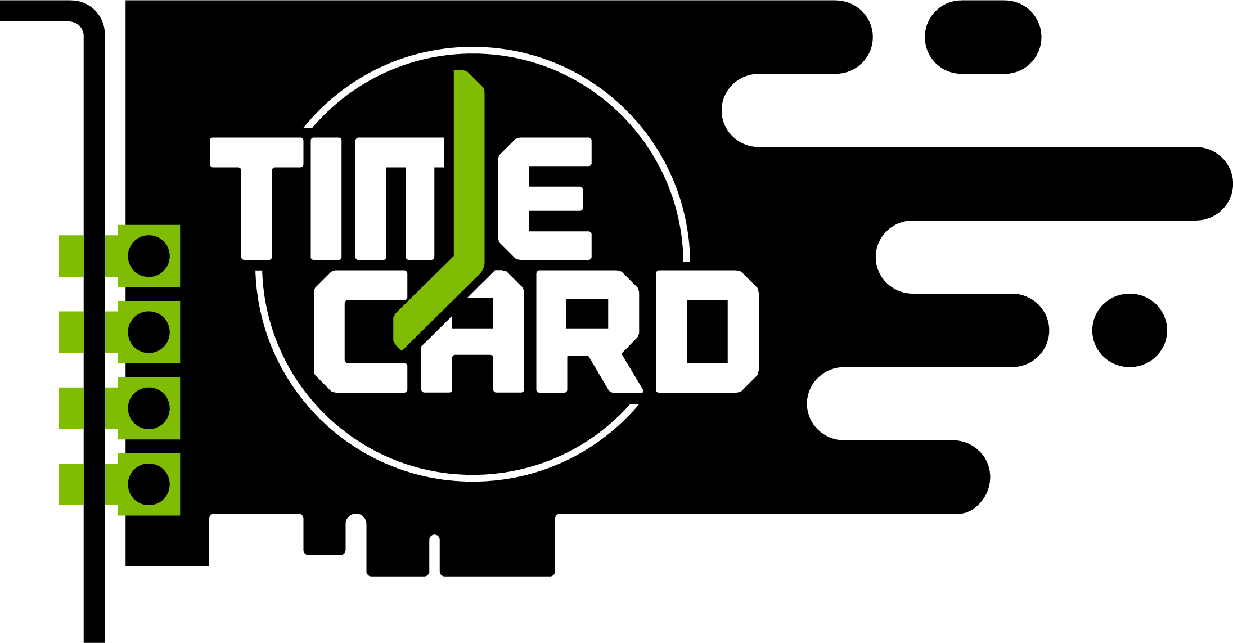
DOC/Artwork/TIMECARD.jpg
