opencomputeproject/Time-Appliance-Project/GNSS/UBlox/NEO-M9N/Altium/Stackup/Stack-Up.PNG

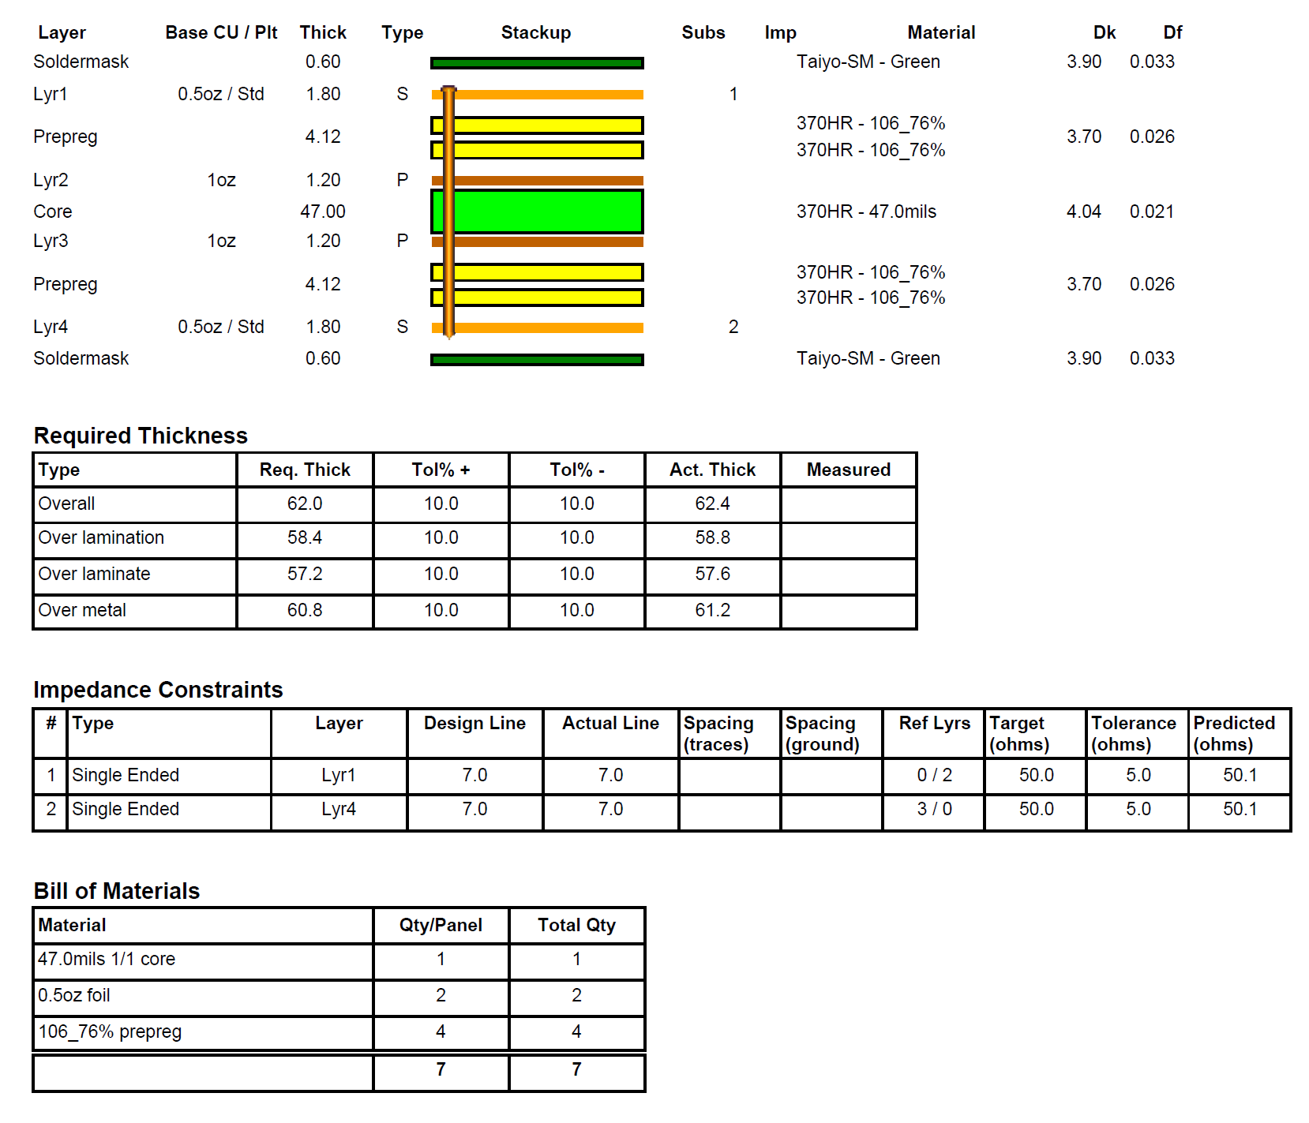
GNSS/UBlox/NEO-M9N/Altium/Stackup/Stack-Up.PNG
