opencomputeproject/Time-Appliance-Project/GNSS/UBlox/RCB-F9T/remote_access_GNSS.png

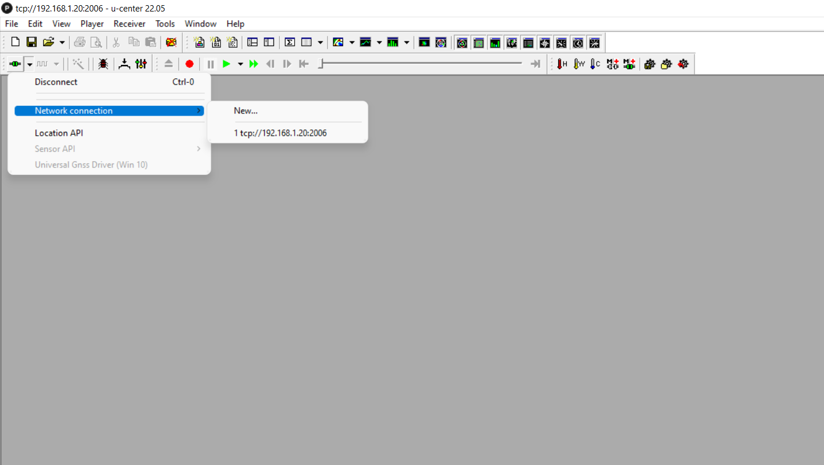
GNSS/UBlox/RCB-F9T/remote_access_GNSS.png
