opencomputeproject/Time-Appliance-Project/images/idea-2.png

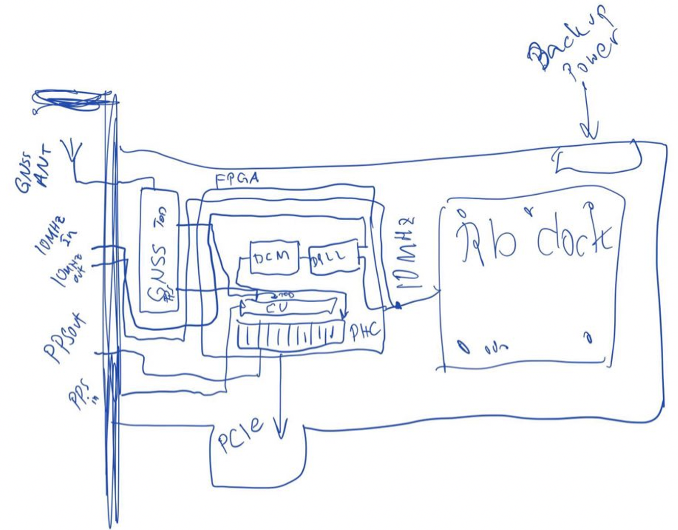
images/idea-2.png
