opencomputeproject/Time-Appliance-Project/images/overall-2.png

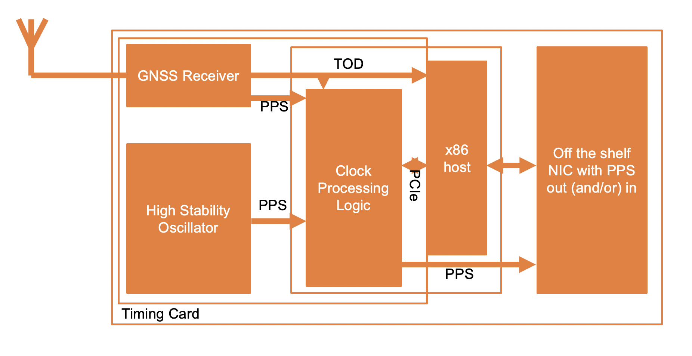
images/overall-2.png
