opencomputeproject/Time-Appliance-Project/images/precision_pps.png

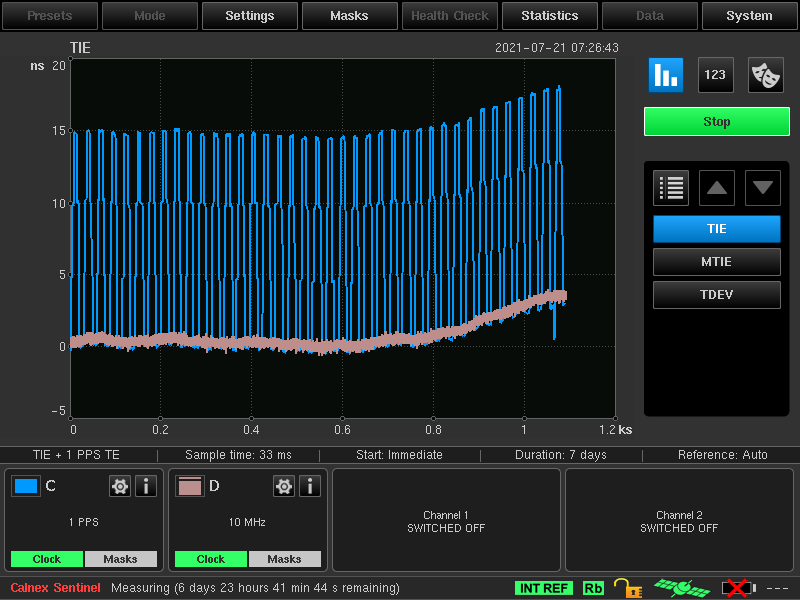
images/precision_pps.png
