opencomputeproject/Time-Appliance-Project/images/timecard-7.jpg

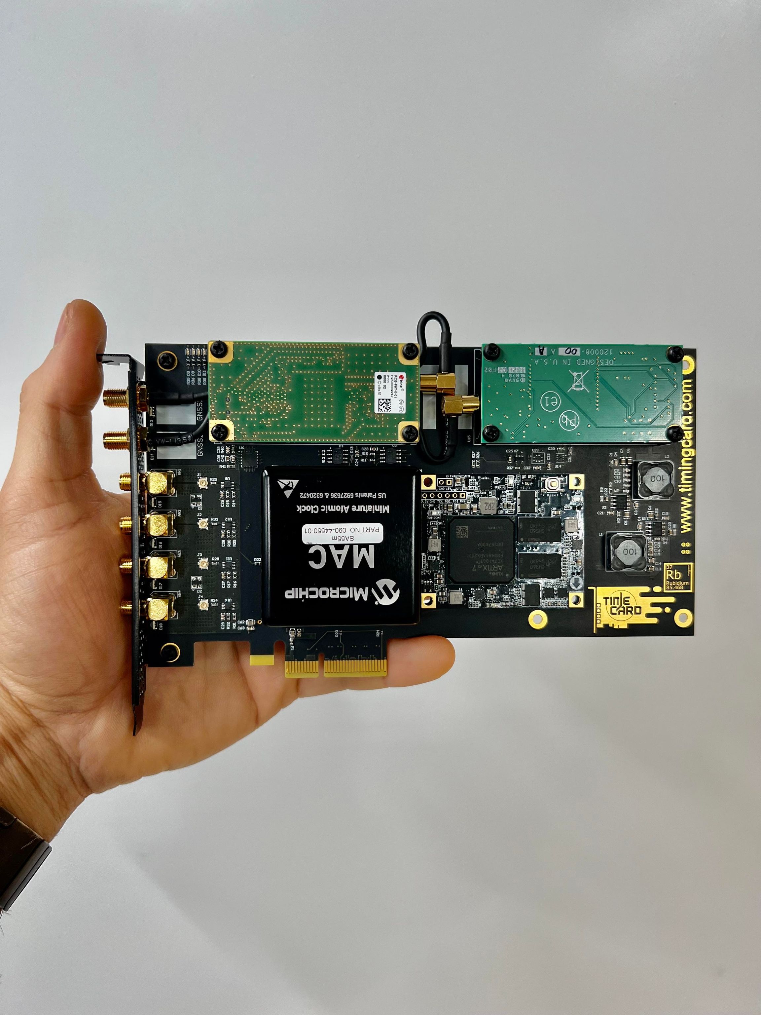
images/timecard-7.jpg
