opencomputeproject/Time-Appliance-Project/Time-Card/images/timecard-2.png

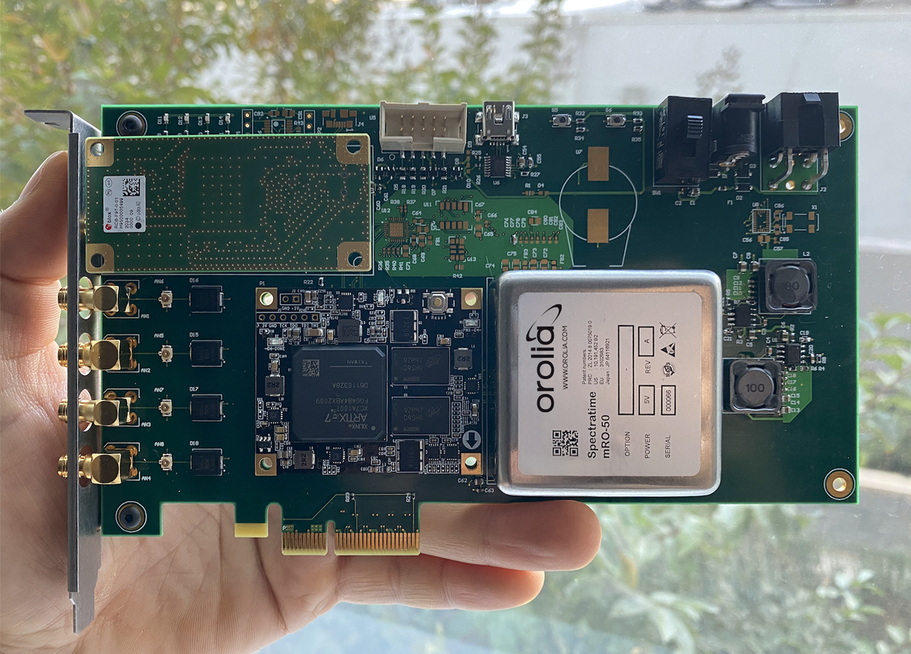
Time-Card/images/timecard-2.png
