opencomputeproject/Time-Appliance-Project/GNSS/UBlox/RCB-F9T/Altium/FAB/GPS_MODULE_ZED-F9T-00B_BOM_smb_ver.xlsx

Designator | Quantity | Manufacturer | Manufacturer 1 | Manufacturer Part Number | Manufacturer Part Number 1 | Supplier 1 | Supplier Part Number 1 | Description | Case/Package
C1, C2, C3, C4, C5 | 5 | Murata |  | GRM155R61E105KA12D |  | Digikey | 490-10017-1-ND | CAP, CER, X5R, 1UF, 10%, 25V, 0402, 0.55MM T | 0402 (1005 Metric)
C6, C7, C8, C9 | 4 |  | Taiyo Yuden |  | UMK105BJ104KV-F | Farnell | 2779049 | None | 0402
C10 | 1 |  | Murata |  | GRM033R71C103KE14D | Farnell | 2990695 | Chip Multilayer Ceramic Capacitors for General Purpose, 0201, 10000pF, X7R, 15%, 10%, 16V
D1 | 1 | Littelfuse Inc. | Littelfuse | PESD0402-140 | PESD0402-140 | Future Electronics | 1128358 | TVS DIODE 14V 40V 0402
DS1, DS2, DS3 | 3 | Lumex Opto/Components Inc. |  | SML-LXFM0603SUGCTR |  | Digikey | 67-2320-1-ND | LED, GREEN, 574NM, 20MA, 20MCD MIN, 2.5VF MAX, 0603, 1.10MM T | 0603 (1608 Metric)
J1 | 1 | Sullins | Sullins | NRPN042MAMS-RC | NRPN042MAMS-RC | Digi-Key | S6009-04-ND | Dual Row 8 Position 2 mm Pitch Surface Mount Header
J2 | 1 | Bel Cinch | Bel Cinch | 142-0711-301 | 142-0711-301 | Digi-Key | J717-ND | Rf Coaxial Board Mount Connector | SMB
L1 | 1 |  | Murata |  | LQG15HS47NJ02D | Future Electronics | 1091743 | Multilayer type RF Inductor 47nH ±5% 0.72Ω 300mA 0402 | 0402
Q1 | 1 | onsemi |  | NTR2101PT1G |  | Digikey | NTR2101PT1GOSCT-ND | MOSFET, P-CH, 8VDS, 3.7A ID, 0.052 OHM RDS(ON)@4.5VGS/3.5A, SOT-23-3 | TO-236-3, SC-59, SOT-23-3
R1, R2, R3, R10, R13, R14 | 6 |  | Stackpole Electronics |  | RMCF0402FT1K00 | Future Electronics | 6297634 | 1kΩ ±1% 0.063W 0402 Thick Film Chip Resistor AEC-Q200 compliant | 0402
R4, R7, R8 | 3 |  | Stackpole Electronics |  | RMCF0402FT10K0 | Future Electronics | 1731694 | 10kΩ ±1% 0.063W 0402 Thick Film Chip Resistor AEC-Q200 compliant | 0402
R9, R11 | 2 |  | Stackpole Electronics |  | RMCF0402FT100K | Future Electronics | 8519472 | 100kΩ ±1% 0.063W 0402 Thick Film Chip Resistor AEC-Q200 compliant | 0402
R12 | 1 | Vishay |  | RCP0603W25R0GEB |  | Digikey | 541-2654-1-ND | RES, 25 OHM, 2%, 1.5W, 150PPM/C, 0603 | 0603 (1608 Metric)
U1 | 1 | u-blox | u-blox | ZED-F9T-00B | ZED-F9T-00B | Digi-Key | 672-1197-1-ND | Multi-band GNSS Receiver with Nanosecond-level Timing Accuracy | SMD/SMT
U2, U3 | 2 | Texas Instruments | Texas Instruments |  | SN74LVC3G07DCUR | Farnell | 2460000 | Triple Buffer/Driver With Open-Drain Output, DCU0008A, LARGE T&R
U4 | 1 | Texas Instruments | TI National Semiconductor |  | LPV511MGX/NOPB | Digi-Key | 296-44295-1-ND | micropower Rail-to-Rail Input and Output Operational Amplifier, 5-pin SC-70, Pb-Free
