opencomputeproject/Time-Appliance-Project/Time-Card/HW/BOM/Latest/V7/Timingcard_PROJECT_BOMv7.xlsx

Line # | DNP | Name | Description | Designator | Revision ID | Revision State | Revision Status | Quantity | Manufacturer 1 | Manufacturer Part Number 1 | Manufacturer Lifecycle 1 | Supplier 1 | Supplier Part Number 1 | Supplier Unit Price 1 | Supplier Subtotal 1
 |  | AT24MAC402-STUM-T | IC EEPROM 2K I2C 1MHZ SOT23-5 | U7 | CMP-06313-000011-1 | New From Design | Up to date | 1 | Microchip | AT24MAC402-STUM-T | Unknown | Digi-Key | AT24MAC402-STUM-TCT-ND | 0.42 | 0.42
 |  | LTST-C191TBKT | LED BLUE CLEAR CHIP SMD | D3, D9, D10, D11 | CMP-22017-000008-1 | New From Design | Up to date | 4 | Vishay Lite-On | LTST-C191TBKT | Volume Production | Digi-Key | 160-1647-1-ND | 0.33 | 1.32
 |  | STPS5L60S | DIODE SCHOTTKY 60V 5A SMC | D12, D19 | CMP-12187-000009-2 | New From Design | Up to date | 2 | STMicroelectronics | STPS5L60S | Volume Production | Digi-Key | 497-8487-1-ND | 0.97 | 1.94
 |  | TMK212BBJ106KG-T | None | C34, C35, C58, C60 | CMP-14477-000079-2 | New From Design | Out of date | 4 | Taiyo Yuden | TMK212BBJ106KG-T | Volume Production | Digi-Key | 587-2985-1-ND | 0.18 | 0.72
 | DNP | BME280 | SENSOR PRESSURE HUMIDITY TEMP | U14 | CMP-2000-05073-3 | New From Design | Up to date | 1
 | DNP | BMX160 | IMU ACCEL/GYRO/MAG | U13 | CMP-191067-000010-1 | New From Design | Out of date | 1
 |  | 39-30-1060 | CONN, HDR, 2X3, R/A, 4.2MM, TH, MINI-FIT JR | J38 |  | Not managed |  | 1 | Molex | 105314-1206 | Volume Production | Digi-Key | WM14977-ND | 2.27 | 2.27
 |  | 155124M173200 | LED (Multiple) | D13, D14, D15, D16, D17, D18 |  | Not managed |  | 6 | Wurth Electronics | 155124M173200 | Unknown | Digi-Key | 732-11414-1-ND | 0.53 | 3.18
 |  | AUX Sensor | Header, 4-Pin | P1 |  | Not managed |  | 1 | Molex | 87937-0406 | Unknown | Digi-Key | WM20573-ND | 0.49 | 0.49
 |  | BAT54SW | DIO, SCHOTTKY, BAT54S, DUAL SERIES, 30V, 200MA, SC-70 | D5, D6, D7, D8 |  | Not managed |  | 4 | Diodes | BAT54SWQ-7-F | Volume Production | Digi-Key | BAT54SWQ-7-FDICT-ND | 0.35 | 1.4
 |  | CAP_0402_0.1UF_50V | CAP, CER, 0.1UF, 50V, 10%, X7R, AEC-Q200, 0402 | C44, C45, C46, C47, C48, C49, C50, C51, C52, C53 |  | Not managed |  | 10 | TDK | CGA2B3X7R1H104K050BB | Volume Production | Digi-Key | 445-6899-1-ND | 0.103 | 1.03
 |  | CAP_0603_0.01UF_50V | CAP, CER, 0.01UF, 50V, 10%, X7R, 0603 | C3, C4 |  | Not managed |  | 2 | KEMET | C0603C103K5RACTU | Volume Production | Digi-Key | 399-1091-1-ND
 |  | CAP_0805_10UF_25V | CAP, CER, 10.UF, 25V, 10%, X5R, 0805 | C1, C5, C6, C7, C8, C13, C14, C62 |  | Not managed |  | 8 | Taiyo Yuden | TMK212BBJ106KG-T | Volume Production | Mouser | 963-TMK212BBJ106KG-T | 0.081 | 0.81
 |  | CRCW080533R0FKEA | RES, 33 OHM, 1%, 1/8W, TF, 0805 | R18, R19, R20, R21 |  | Not managed |  | 4 | Vishay | CRCW080533R0FKEA | Volume Production | Digi-Key | 541-33.0CCT-ND | 0.1 | 0.4
 |  | ERJ-2GE0R00X | RES, 0. OHM, 1%, 1/16W, TF, AEC-Q200, 0402 | R23, R24 |  | Not managed |  | 2 | Panasonic | ERJ-2GE0R00X | Volume Production | Digi-Key | P0.0JCT-ND | 0.1 | 0.2
 |  | ERJ-3EKF1002V | RES, 10K, 1%, 1/10W, TF, 0603 | R6, R7 |  | Not managed |  | 2 | Panasonic | ERJ-3EKF1002V | Volume Production | Digi-Key | P10.0KHCT-ND | 0.1 | 0.2
 |  | ERJ-3EKF2000V | RES, 200 OHM, 1%, 1/10W, TF, 0603 | R1 |  | Not managed |  | 1 | Panasonic | ERJ-3EKF2000V | Volume Production | Digi-Key | P200HCT-ND
 |  | ERJ-3EKF2201V | RES, 2.2K, 1%, 1/10W, TF, 0603 | R8, R9 |  | Not managed |  | 2 | Panasonic | ERJ-3EKF2201V | Volume Production | Digi-Key | P2.20KHCT-ND | 0.1 | 0.2
 |  | ERJ-3EKF2612V | RES, 26.1K, 1%, 1/10W, TF, 0603 | R5 |  | Not managed |  | 1 | Panasonic | ERJ-3EKF2612V | Volume Production | Digi-Key | P26.1KHCT-ND | 0.1 | 0.1
 |  | ERJ-3EKF4701V | RES, 4.7K, 1%, 1/10W, TF, 0603 | R22 |  | Not managed |  | 1 | Panasonic | ERJ-3EKF4701V | Volume Production | Digi-Key | P4.70KHCT-ND | 0.1 | 0.1
 |  | ERJ-3EKF4702V | RES, 47K, 1%, 1/10W, TF, 0603 | R2, R3, R4 |  | Not managed |  | 3 | Panasonic | ERJ-3EKF4702V | Unknown | Digi-Key | P47.0KHCT-ND
 |  | FUSE_0603_2.00A | FUSE SLOW 2.00A 32V M 0603 | F1 |  | Not managed |  | 1 | Bourns | SF-0603S200-2 | Volume Production | Digi-Key | SF-0603S200-2CT-ND | 0.71 | 0.71
 |  | GNSS Header | 8-pin GNSS header | J6, J13 |  | Not managed |  | 2 | Samtec | SQW-104-01-F-D-VS | Volume Production | Digi-Key | SAM11876-ND | 2.59 | 5.18
 |  | GNSS Standoff |  | J5, J7, J8, J9, J10, J11, J12, J14 |  | Not managed |  | 8 | Keystone Electronics | 24393 | Volume Production | Digi-Key | 36-24393-ND | 0.75 | 6
 |  | IS32FL3207 |  | U6 |  | Not managed |  | 1 | ISSI | IS32FL3207-QWLA3-TR | Unknown | Digi-Key | 2521-IS32FL3207-QWLA3-TRCT-ND | 2.35 | 2.35
 |  | M3 screw |  | J15, J16, J17, J18, J19, J20, J21, J22, J23, J24, J25, J26, J27, J28, J29, J30, J32, J33 |  | Not managed |  | 18 | APM Hexseal | RM3X6MM2701 | Volume Production | Digi-Key | 335-1156-ND | 0.454 | 8.17
 |  | MP1482DS-LF | IC, DC/DC, MP1482DS, >4.75VIN, 0.923-15V OUT, SOIC8 | U1, U2 |  | Not managed |  | 2 | Monolithic Power Systems | MP1482DS-LF-Z | Unknown | Digi-Key | 1589-1524-1-ND | 3.1 | 6.2
 |  | NC7WV125K8X | Integrated Circuit | U8, U11, U12, U16 |  | Not managed |  | 4 | ON Semiconductor / Fairchild | NC7WV125K8X | Volume Production | Digi-Key | NC7WV125K8XCT-ND | 0.8 | 3.2
 |  | PM124SH-100M-RC | IND, PWR, 10.uH, 20%, 4A, 0.04DCR, 12.5X12.5MM, SHLD | L1, L2 |  | Not managed |  | 2 | Bourns JW Miller | PM124SH-100M-RC | Volume Production | Digi-Key | PM124SH-100M-RCCT-ND | 1.18 | 2.36
 |  | RED | LED, RED, SML-LX0603, 635NM, 2V, 20MA, 0603 | D4 |  | Not managed |  | 1 | Lumex | SML-LX0603IW-TR | Volume Production | Digi-Key | 67-1548-1-ND | 0.33 | 0.33
 |  | SA53_Header |  | J31 |  | Not managed |  | 1 | Molex | 0529910208+ | Unknown | Digi-Key | WM24007CT-ND | 1.46 | 1.46
 |  | Single FPGA Conn |  | J34, J35, J36, J37 |  | Not managed |  | 4 | Panasonic | AXK680347YG | Volume Production | Digi-Key | 255-3246-1-ND | 3.13 | 12.52
 |  | HTST-105-01-L-DV-A | CONN, HDR, 2X5, VERT, 0.1IN SHROUDED, SMT, HTSH SERIES | U5 |  | Not managed |  | 1 | Samtec | HTST-105-01-L-DV-A | Volume Production | Digi-Key | SAM8809-ND | 4.42 | 4.42
 | DNP | EXT GPIO | Header, 6-Pin, Dual row | P3 |  | Not managed |  | 1
 | DNP | MAC-SA5X | MOD, MAC, MAC-SA5X, ATOMIC CLOCK | U10 |  | Not managed |  | 1
 | DNP | PCIex4 | PCIE x4 Edge Connector,OrCAD Symbol,NC | P2 |  | Not managed |  | 1
 | DNP | RCB-F9T | MOD, GPS | U9 |  | Not managed |  | 1 | u-blox | RCB-F9T | Unknown | Digi-Key | 672-RCB-F9T-ND | 247.5 | 247.5
 | DNP | RCB-F9T-1 | MOD, GPS | U15 |  | Not managed |  | 1 | u-blox | RCB-F9T | Unknown | Digi-Key | 672-RCB-F9T-ND | 247.5 | 247.5
 |  | 901-143-6RFX | Coaxial connector, 50 Ohm, -65 to 165 degC, 5-Pin THD, RoHS, Bulk | AN1, AN2, AN3, AN4 | CMP-2000-05705-1 | Released | Up to date | 4 | Amphenol RF | 901-143-6RFX | Volume Production
 |  | 1909763-1 | Ultra Miniature Coaxial Connector Jack, 60 V, 50 Ohm, -40 to 90 degC, RoHS, Tape and Reel | J1, J2, J3, J4 | CMP-2000-07505-1 | Released | Out of date | 4 | TE Connectivity AMP | 1909763-1 | Volume Production | Digi-Key | A118077CT-ND | 0.6 | 2.4
 |  | 8240136 | TVS Diode WE-TVS-HS, VRWM=3.3V | D1, D2 | CMP-1486-00002-1 | Released | Up to date | 2 | Wurth Electronics | 8240136 | Volume Production | Digi-Key | 732-4472-1-ND | 1.28 | 2.56
 |  | C0603C105K3PACTU | CAP CER 1UF 25V X5R 0603 | C38 | CMP-2006-02216-3 | Released | Up to date | 1 | KEMET | C0603C105K3PACTU | Volume Production | Digi-Key | 399-C0603C105K3PAC7867CT-ND | 0.18 | 0.18
 |  | C0603X104K5RACAUTO |  | C2, C9, C10, C11, C12, C15, C16, C17, C18, C19, C21, C23, C24, C25, C26, C27, C28, C29, C30, C31, C32, C33, C36, C37, C39, C40, C59, C61, C63 | CMP-2006-00003-1 | Released | Out of date | 29 | KEMET | C0603X104K5RACAUTO | Volume Production | Digi-Key | 399-6912-1-ND | 0.133 | 3.86
 |  | CRCW0603110RFKEA |  | R12 | CMP-2000-03854-1 | Released | Up to date | 1 | Vishay | CRCW0603110RFKEA | Volume Production
 |  | CRCW12060000Z0EAHP |  | R45 | CMP-2003-04873-1 | Released | Up to date | 1 | Vishay Dale | CRCW12060000Z0EAHP | Volume Production | Digi-Key | 541-0.0UBCT-ND | 0.37 | 0.37
 |  | DS90LV027AQMA | Automotive LVDS Dual Differential Driver, 8-pin Narrow SOIC | U3 | CMP-0058-01000-2 | Released | Up to date | 1
 |  | DS90LV028AQMA | Automotive LVDS Dual Differential Line Receiver, 8-pin Narrow SOIC | U4 | CMP-0058-01010-2 | Released | Up to date | 1
 |  | ERJ-3EKF2000V |  | R35, R36, R38, R39 | CMP-2000-00316-1 | Released | Out of date | 4 | Panasonic | ERJ-3EKF2000V | Volume Production
 |  | ERJ-3EKF4701V | Precision Thick Film Chip Resistor, 4.7 KOhm, +/- 1%, -55 to 155 degC, 0603 (1608 Metric), RoHS, Tape and Reel | R14, R15, R16, R17, R26, R27, R29, R30, R31, R32, R41 | CMP-1012-00586-3 | Released | Up to date | 11 | Yageo | RC0603FR-074K7L | Volume Production | Digi-Key | 311-4.70KHRCT-ND | 0.021 | 0.231
 |  | GCM188R71H333KA55D |  | C20, C22 | CMP-2006-02385-1 | Released | Up to date | 2 | Murata | GCM188R71H333KA55D | Unknown | Digi-Key | 490-8025-1-ND | 0.25 | 0.5
 |  | RC0603FR-074K7L | Chip Resistor, 4.7 KOhm, +/- 1%, 0.1 W, -55 to 155 degC, 0603 (1608 Metric), RoHS, Tape and Reel | R10, R11 | CMP-2000-06942-1 | Released | Up to date | 2 | Yageo | RC0603FR-074K7L | Volume Production | Digi-Key | 311-4.70KHRCT-ND | 0.1 | 0.2
 |  | RC0603FR-0749R9L | General Purpose Chip Resistor, 49.9 Ohm, +/- 1%, -55 to 155 degC, 0603 (1608 Metric), RoHS, Tape and Reel | R13, R25, R28, R33, R34 | CMP-1659-00036-1 | Released | Up to date | 5 | Yageo | RC0603FR-0749R9L | Volume Production | Digi-Key | 311-49.9HRCT-ND | 0.021 | 0.21
 |  | RC0603FR-07100KL | RES SMD 100K OHM 1% 1/10W 0603 | R40 | CMP-2100-03662-2 | Released | Up to date | 1 | Yageo | RC0603FR-07100KL | Volume Production | Digi-Key | 311-100KHRCT-ND | 0.1 | 0.1
 |  | RMCF0603FT10K0 | Chip Resistor, 10 KOhm, +/- 1%, 0.1 W, -55 to 155 degC, 0603 (1608 Metric), RoHS, Tape and Reel | R37 | CMP-2000-06990-1 | Released | Out of date | 1 | Stackpole Electronics | RMCF0603FT10K0 | Volume Production | Digi-Key | RMCF0603FT10K0CT-ND | 0.1 | 0.1
