opencomputeproject/Time-Appliance-Project/SOM/FPGA/Binaries/FirmwareUpdateTest/README.md

# Firmware Update Test Version

This is two times the same firmware with only a difference in the version number.

0x0016

and 

0x0017
