opencomputeproject/Time-Appliance-Project/images/Measurements/PTM/TimeCardLitePCIe_TGPIO.png

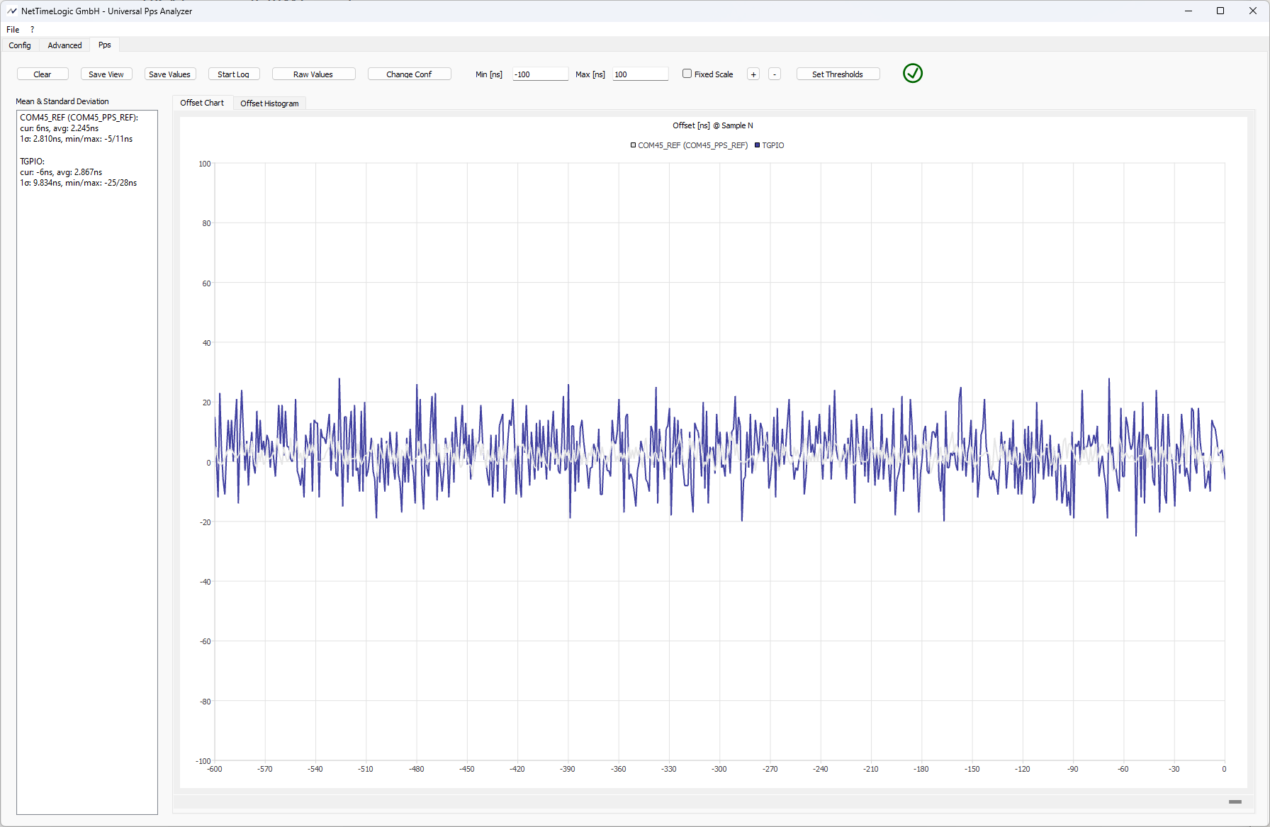
images/Measurements/PTM/TimeCardLitePCIe_TGPIO.png
