opencomputeproject/Time-Appliance-Project/images/Measurements/PTM/TimeCardPLitePCIe_TGPIO.png

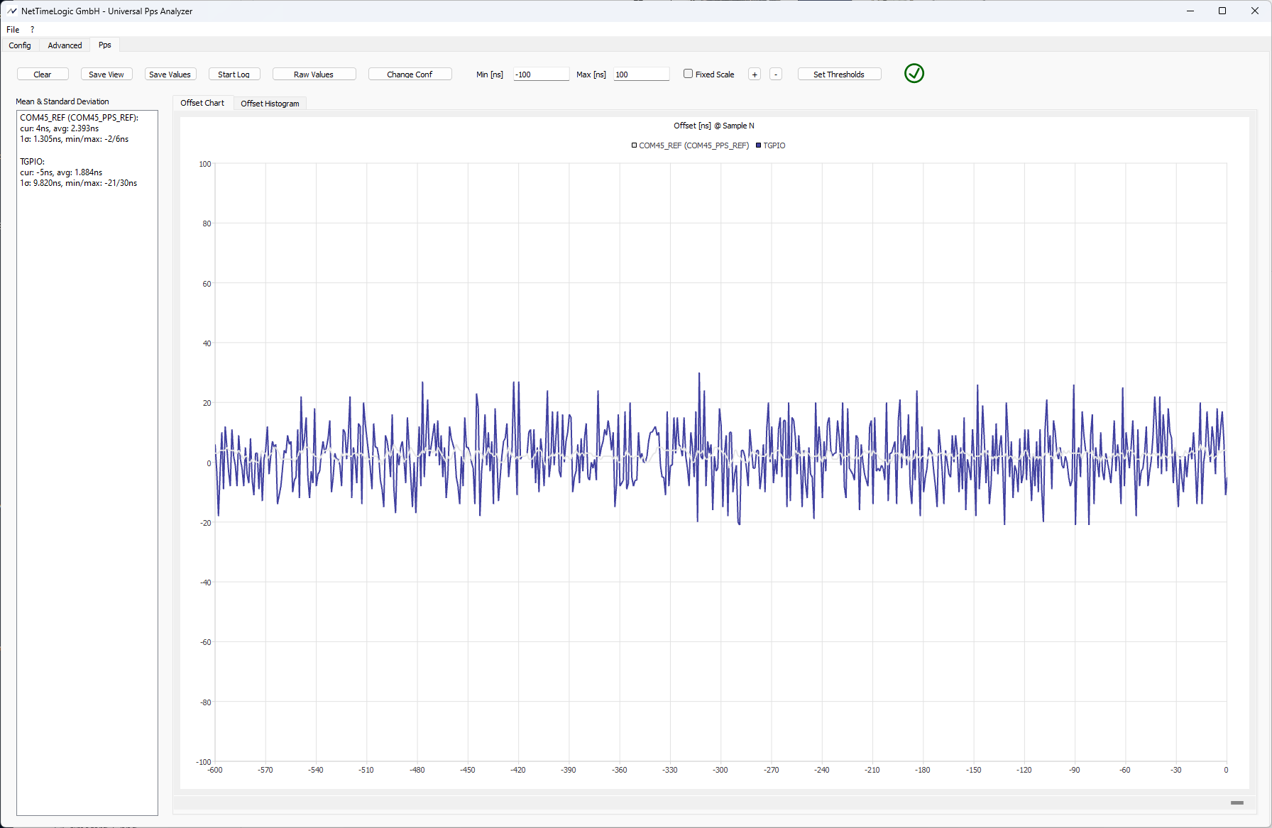
images/Measurements/PTM/TimeCardPLitePCIe_TGPIO.png
