opencomputeproject/Time-Appliance-Project/HW/ECAD/Latest/TimeCardV9_Schematic_8-28-2023.pdf

# INPUT/OUTPUT SIGNALS

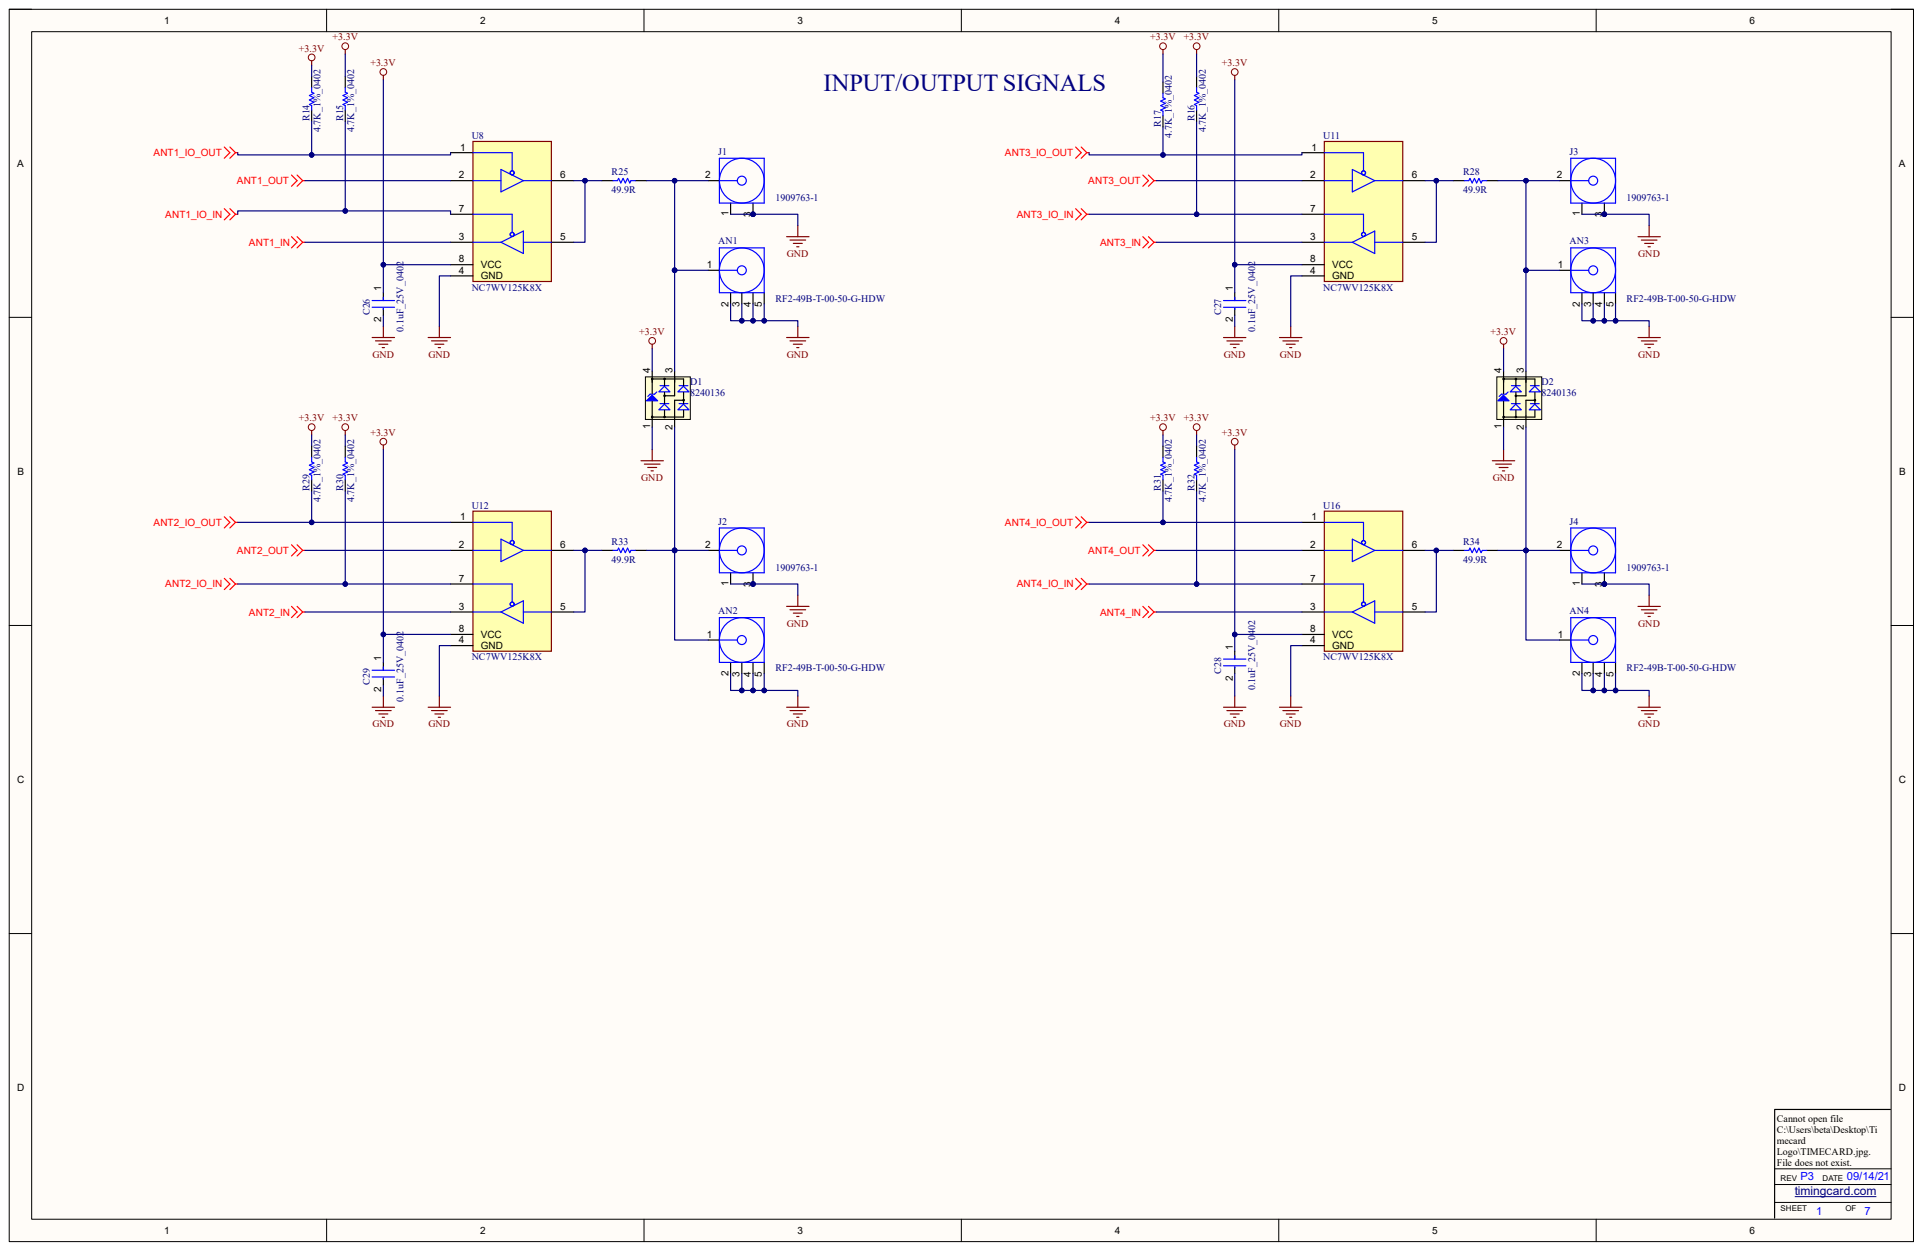
[picture p226: page 1]

Cannot open file
C:\Users\beta\Desktop\Ti
mecard
Logo\TIMECARD.jpg.
File does not exist.
timingcard.com

# SYSTEM STATUS LEDS

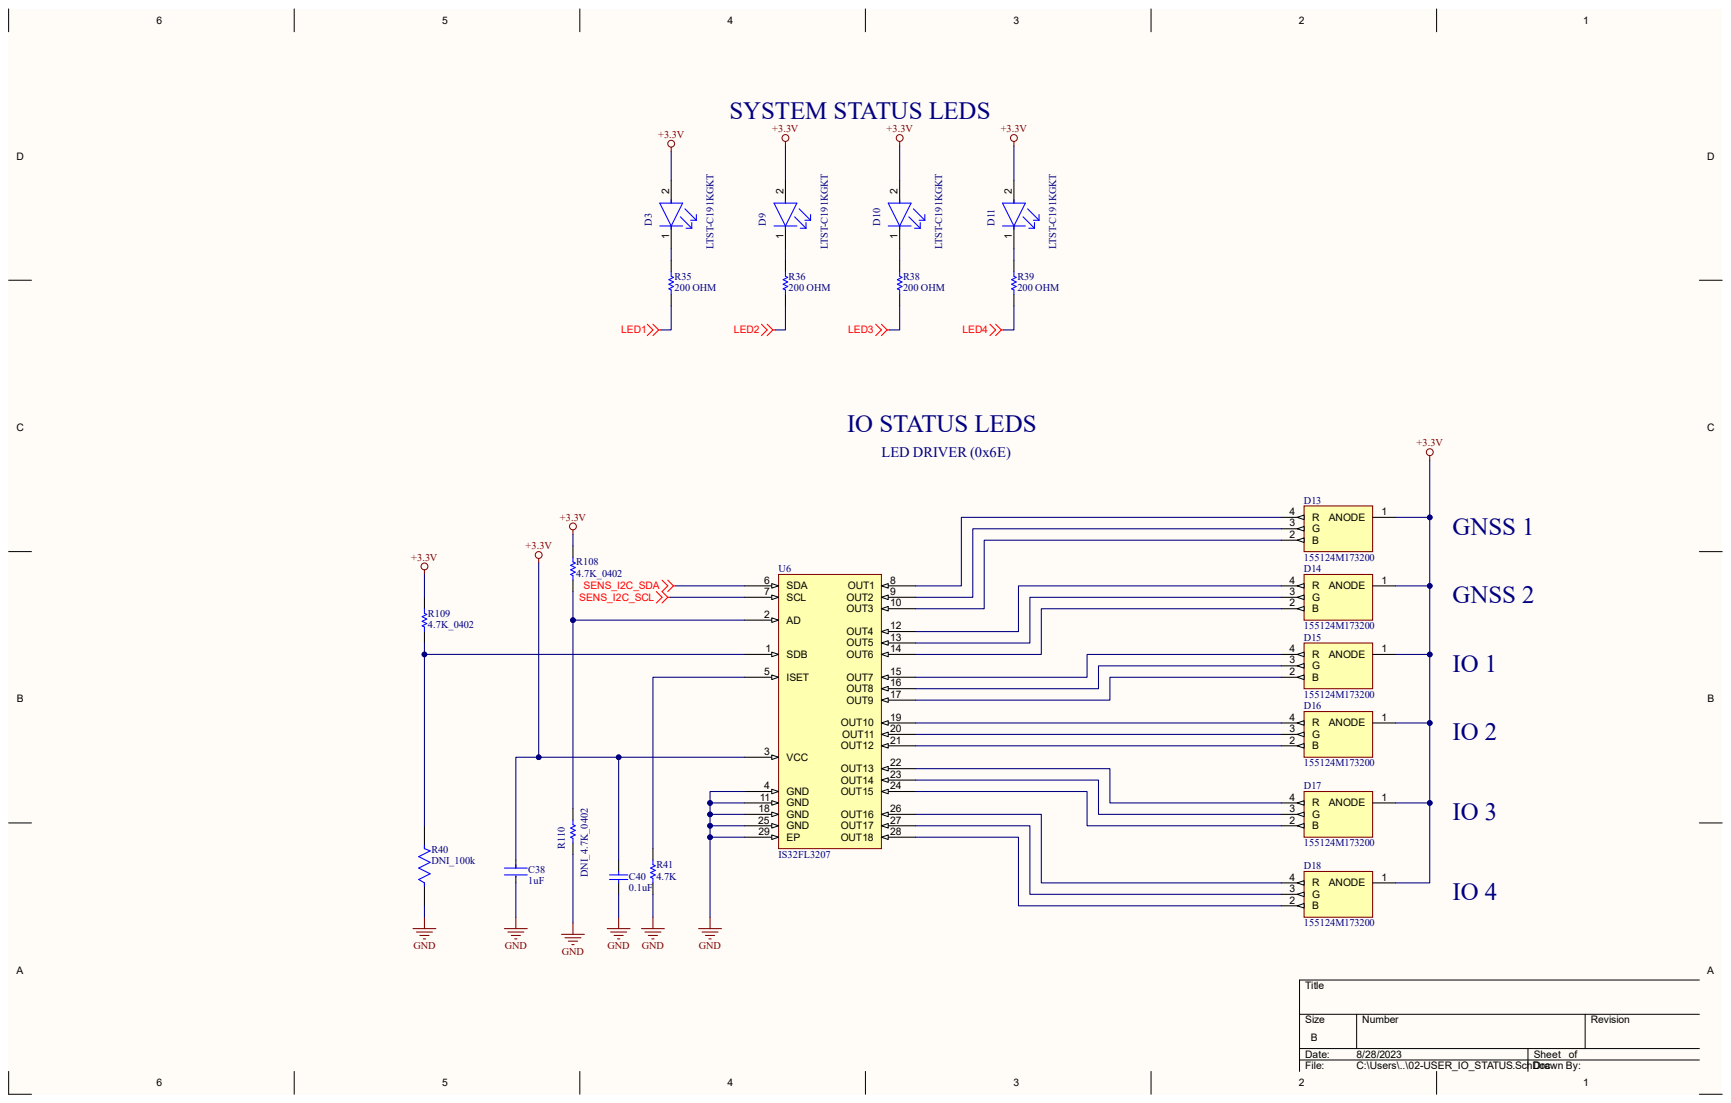
[picture p227: page 2]

# Two power supply options

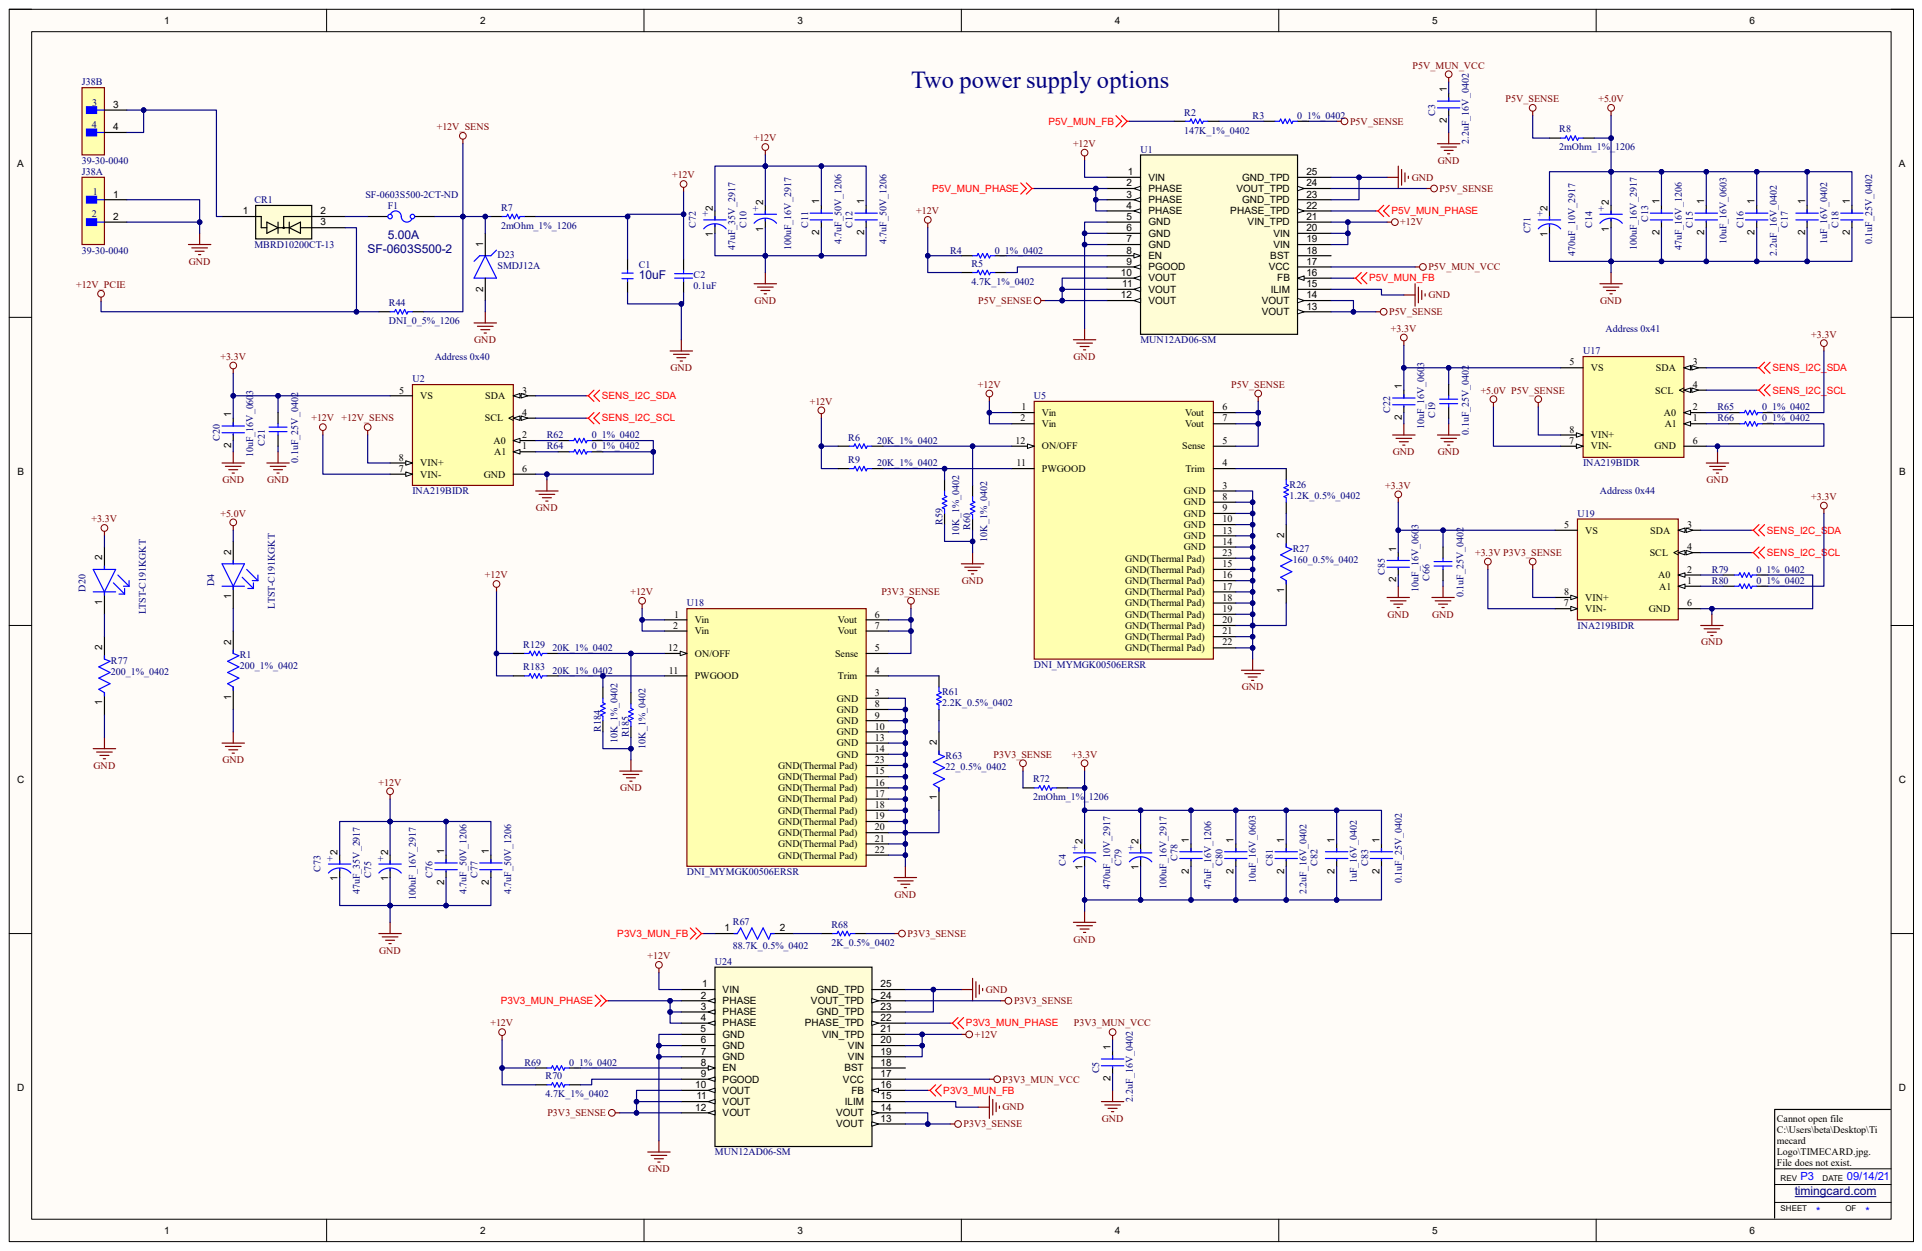
[picture p228: page 3]
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

# PCIe Connector

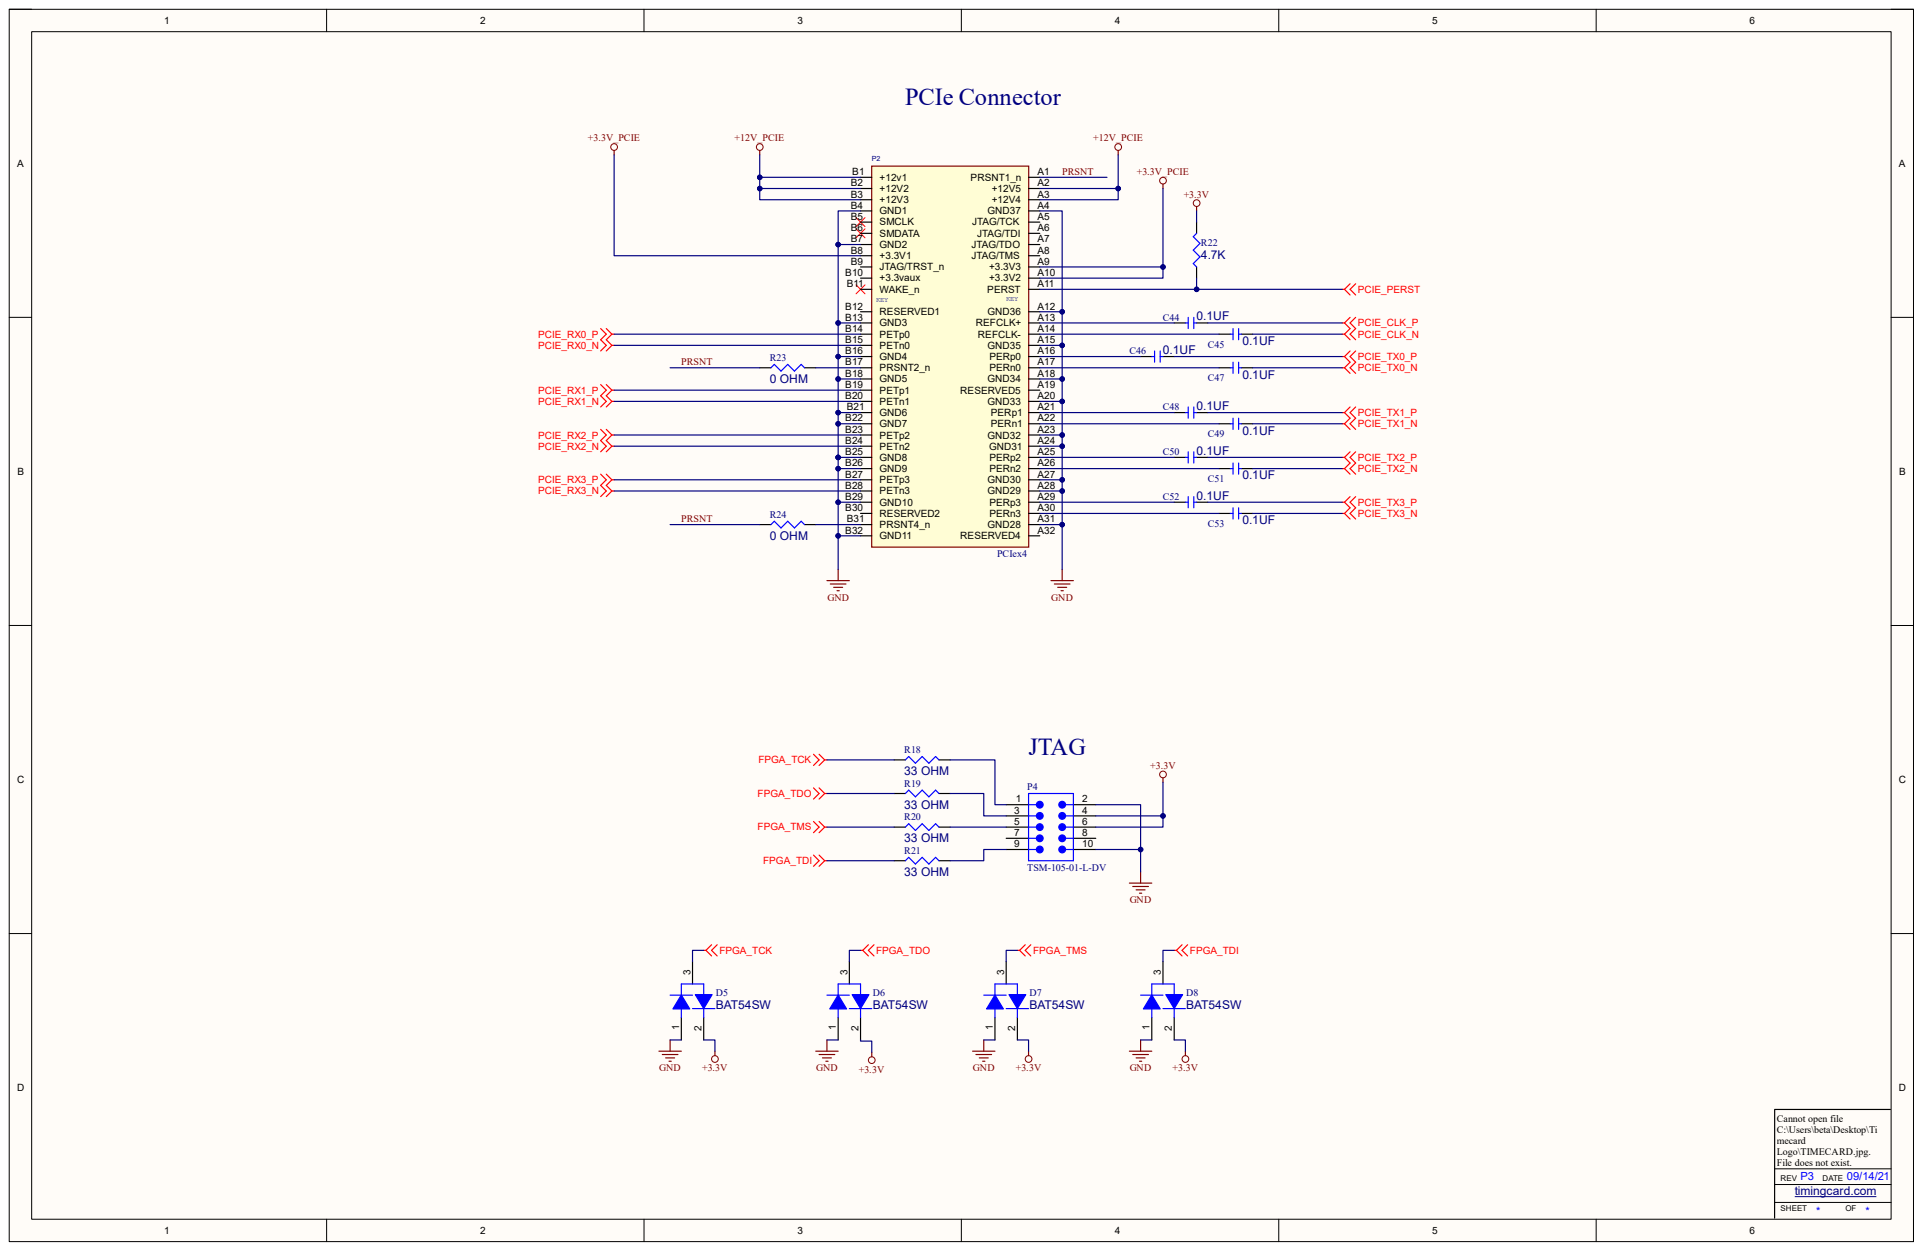
[picture p229: page 4]
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

# GPS

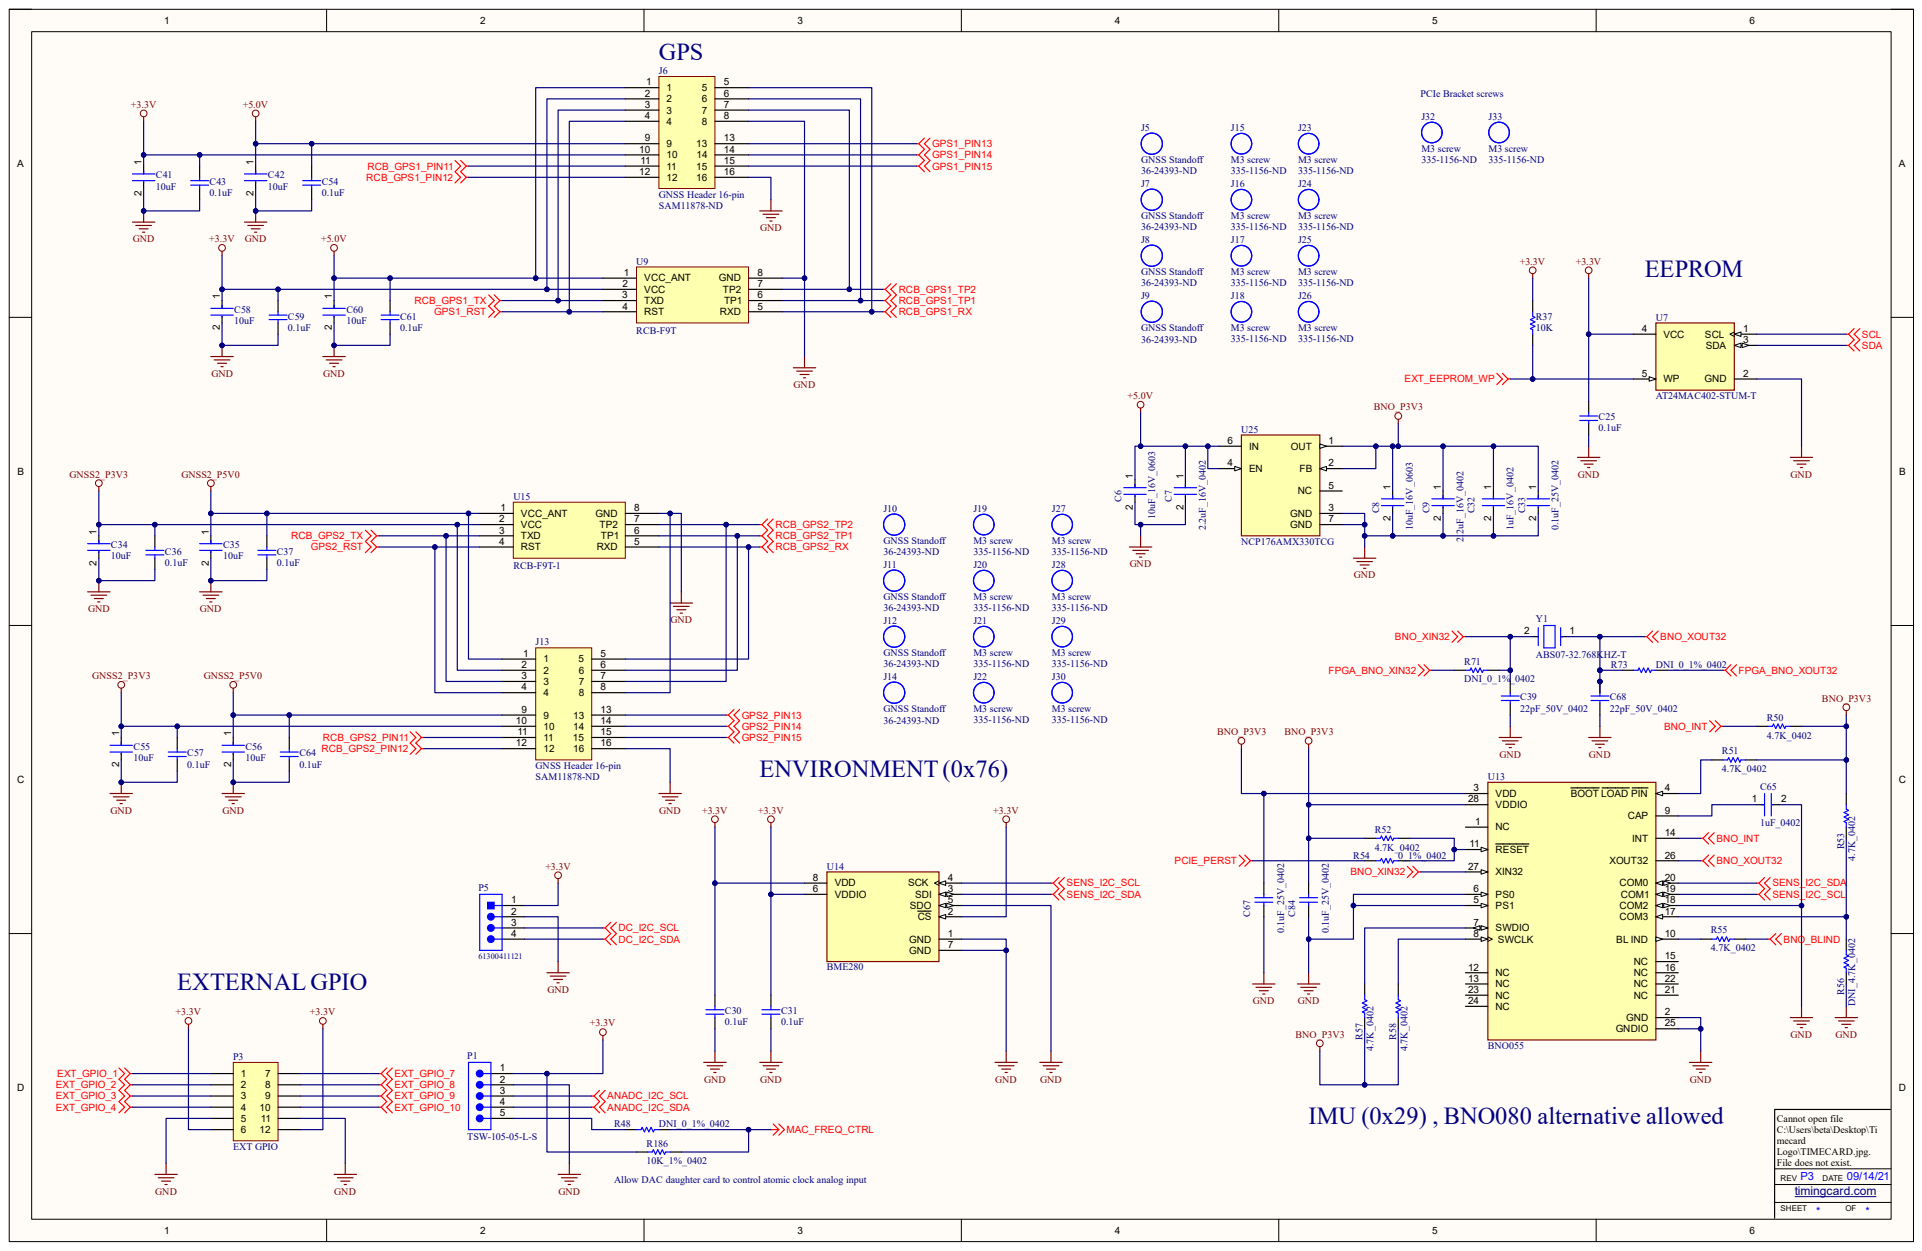
[picture p230: page 5]

ANADC_I2C_SCL
ANADC_I2C_SDA
Allow DAC daughter card to control atomic clock analog input

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

# MAC

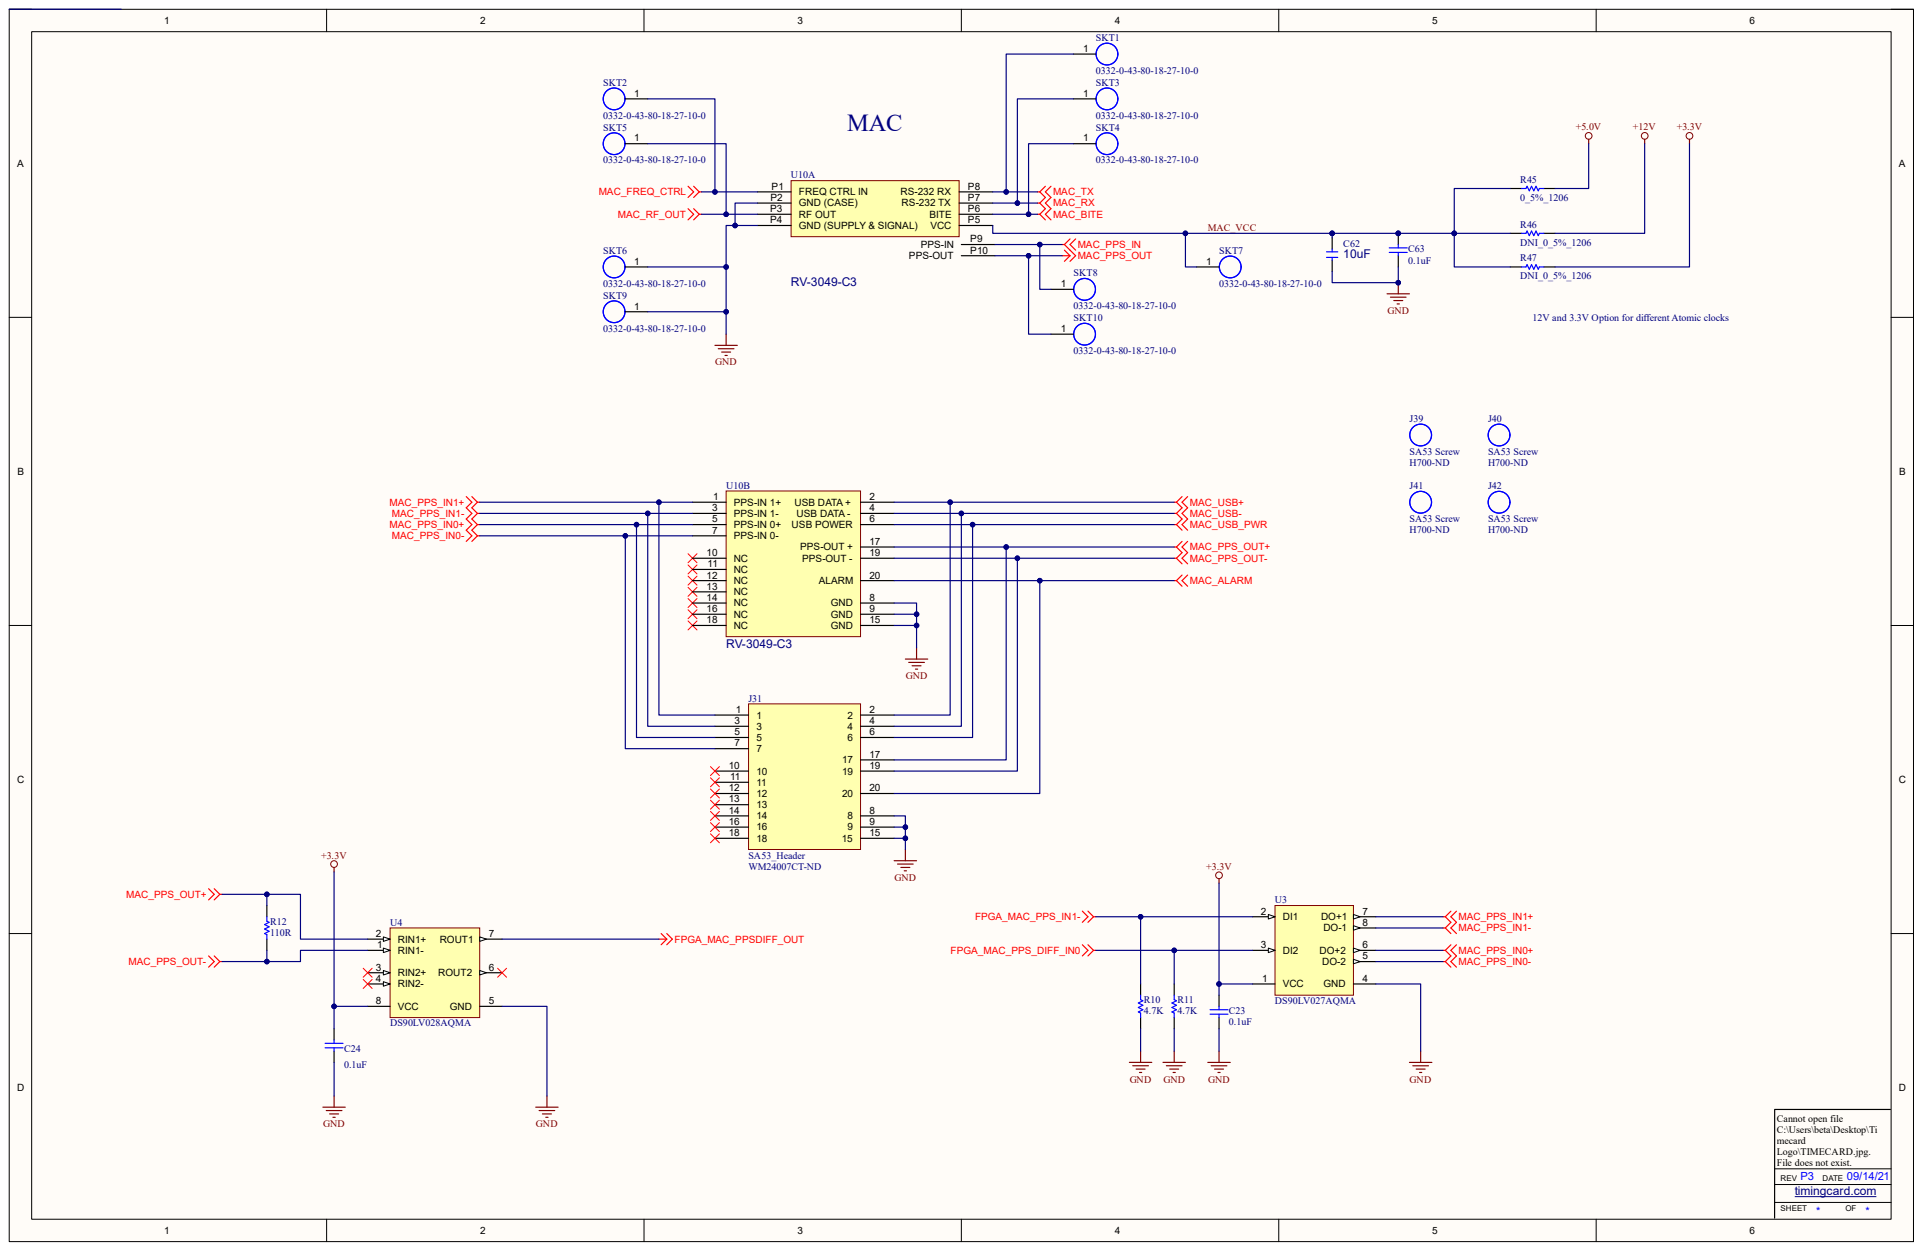
[picture p231: page 6]

12V and 3.3V Option for different Atomic clocks

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

# AXK680347YG 1

# AXK680347YG 1

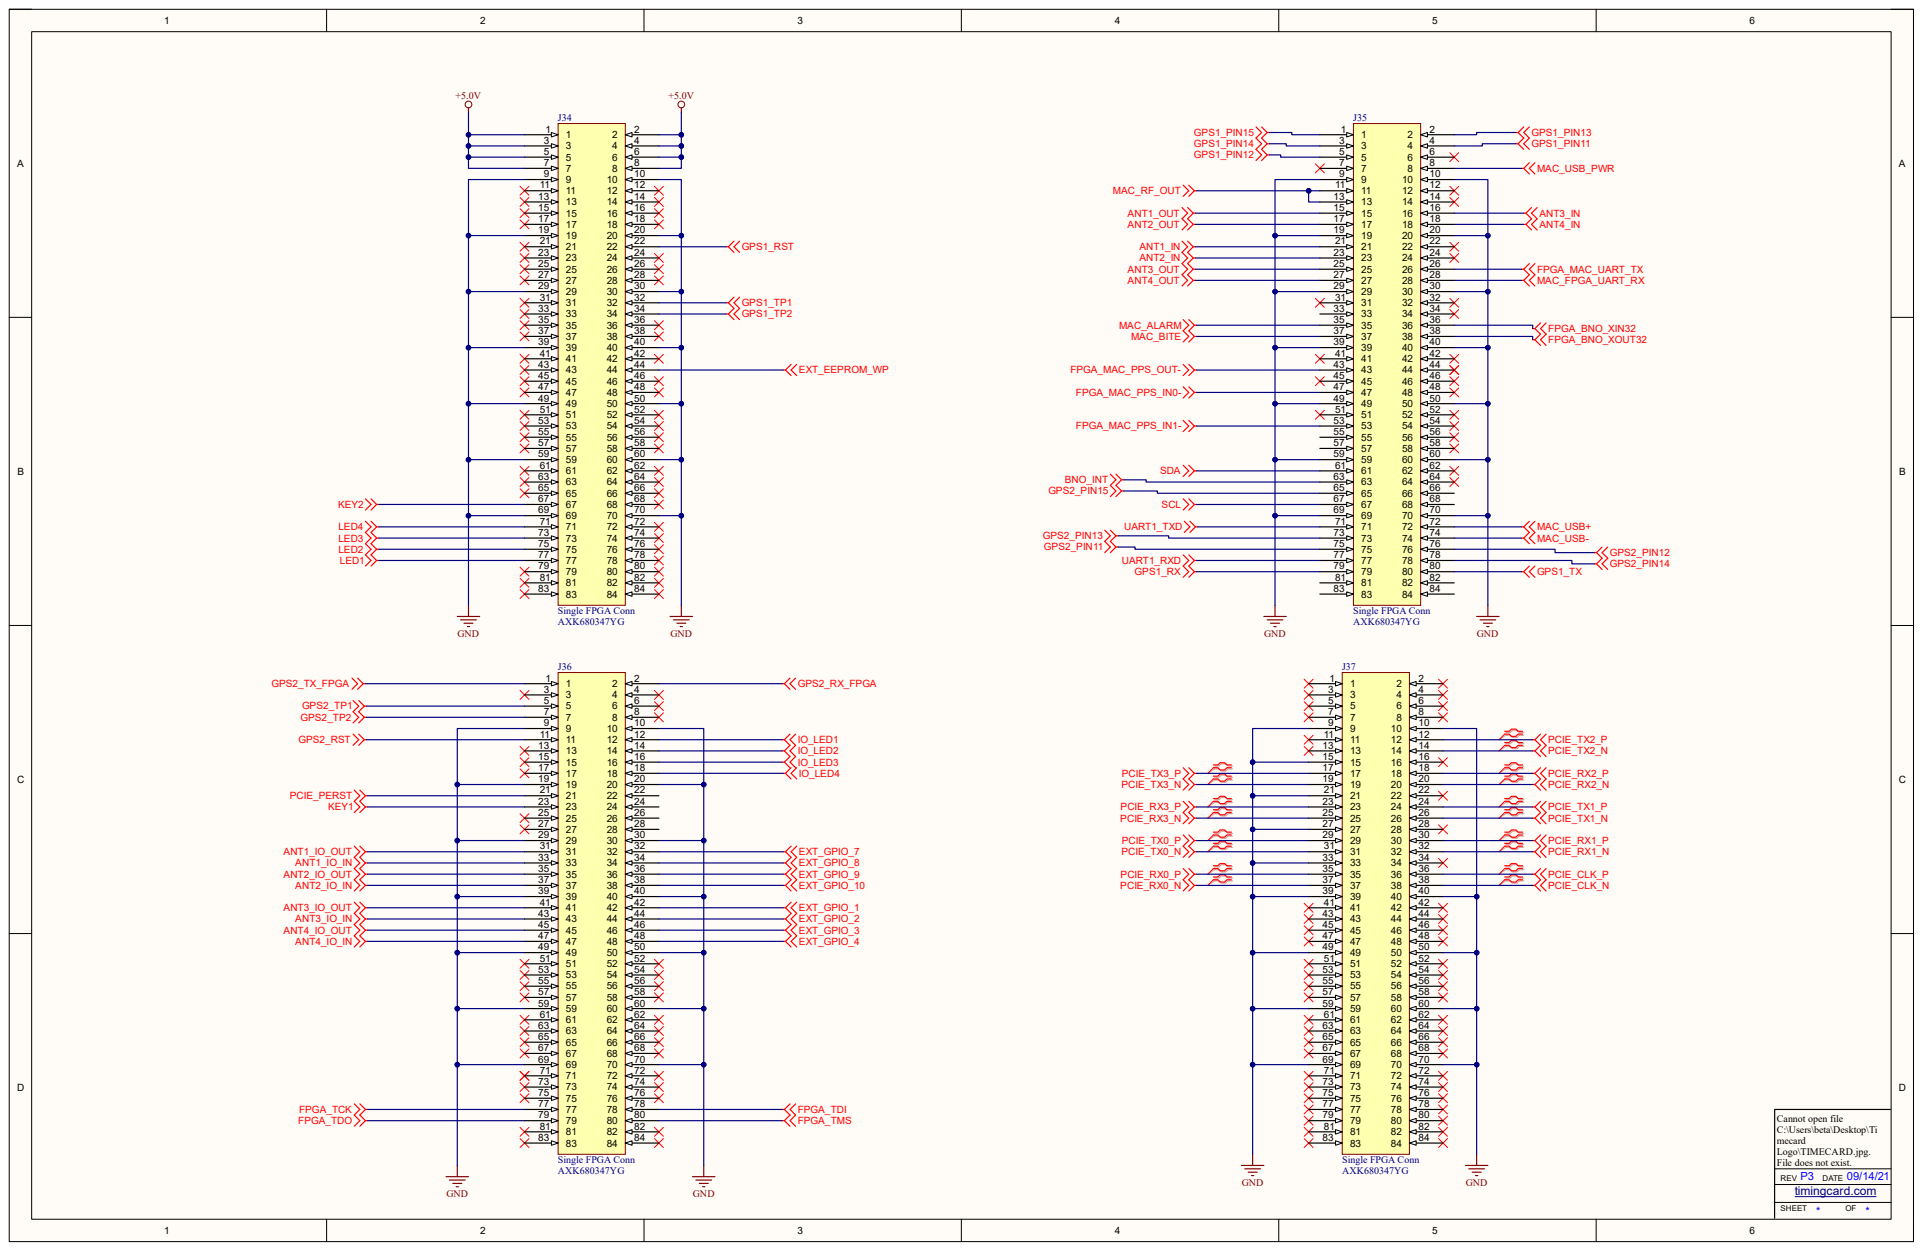
[picture p232: page 7]
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

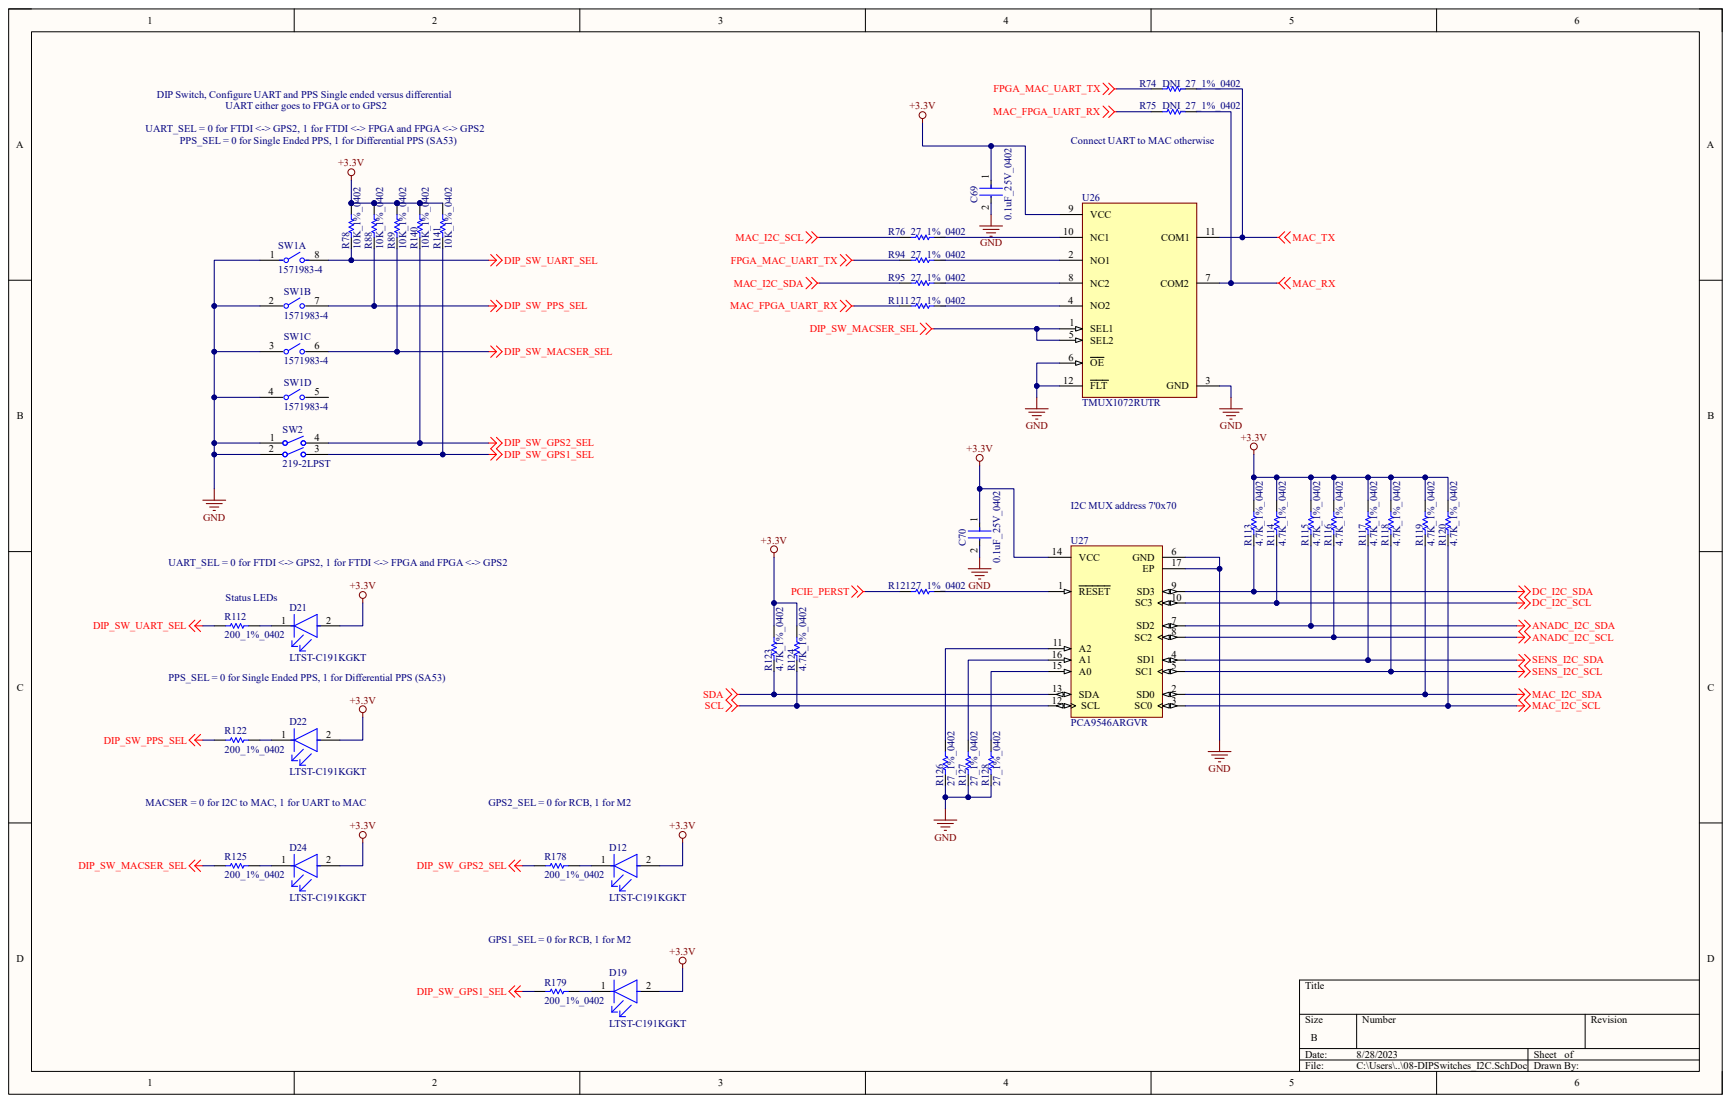
[picture p233: page 8]

DIP Switch, Configure UART and PPS Single ended versus differential

UART either goes to FPGA or to GPS2 R⁷⁸ 10K_1%_0402

UART_SEL = 0 for FTDI <-> GPS2, 1 for FTDI <-> FPGA and FPGA <-> GPS2

PPS_SEL = 0 for Single Ended PPS, 1 for Differential PPS (SA53) R⁸⁹ 10K_1%_0402

Connect UART to MAC otherwise

I2C MUX address 7'0x70 R¹²⁶ 27_1%_0402 R¹²⁷ 27_1%_0402 R¹²⁸ 27_1%_0402

PPS_SEL = 0 for Single Ended PPS, 1 for Differential PPS (SA53)

MACSER = 0 for I2C to MAC, 1 for UART to MAC

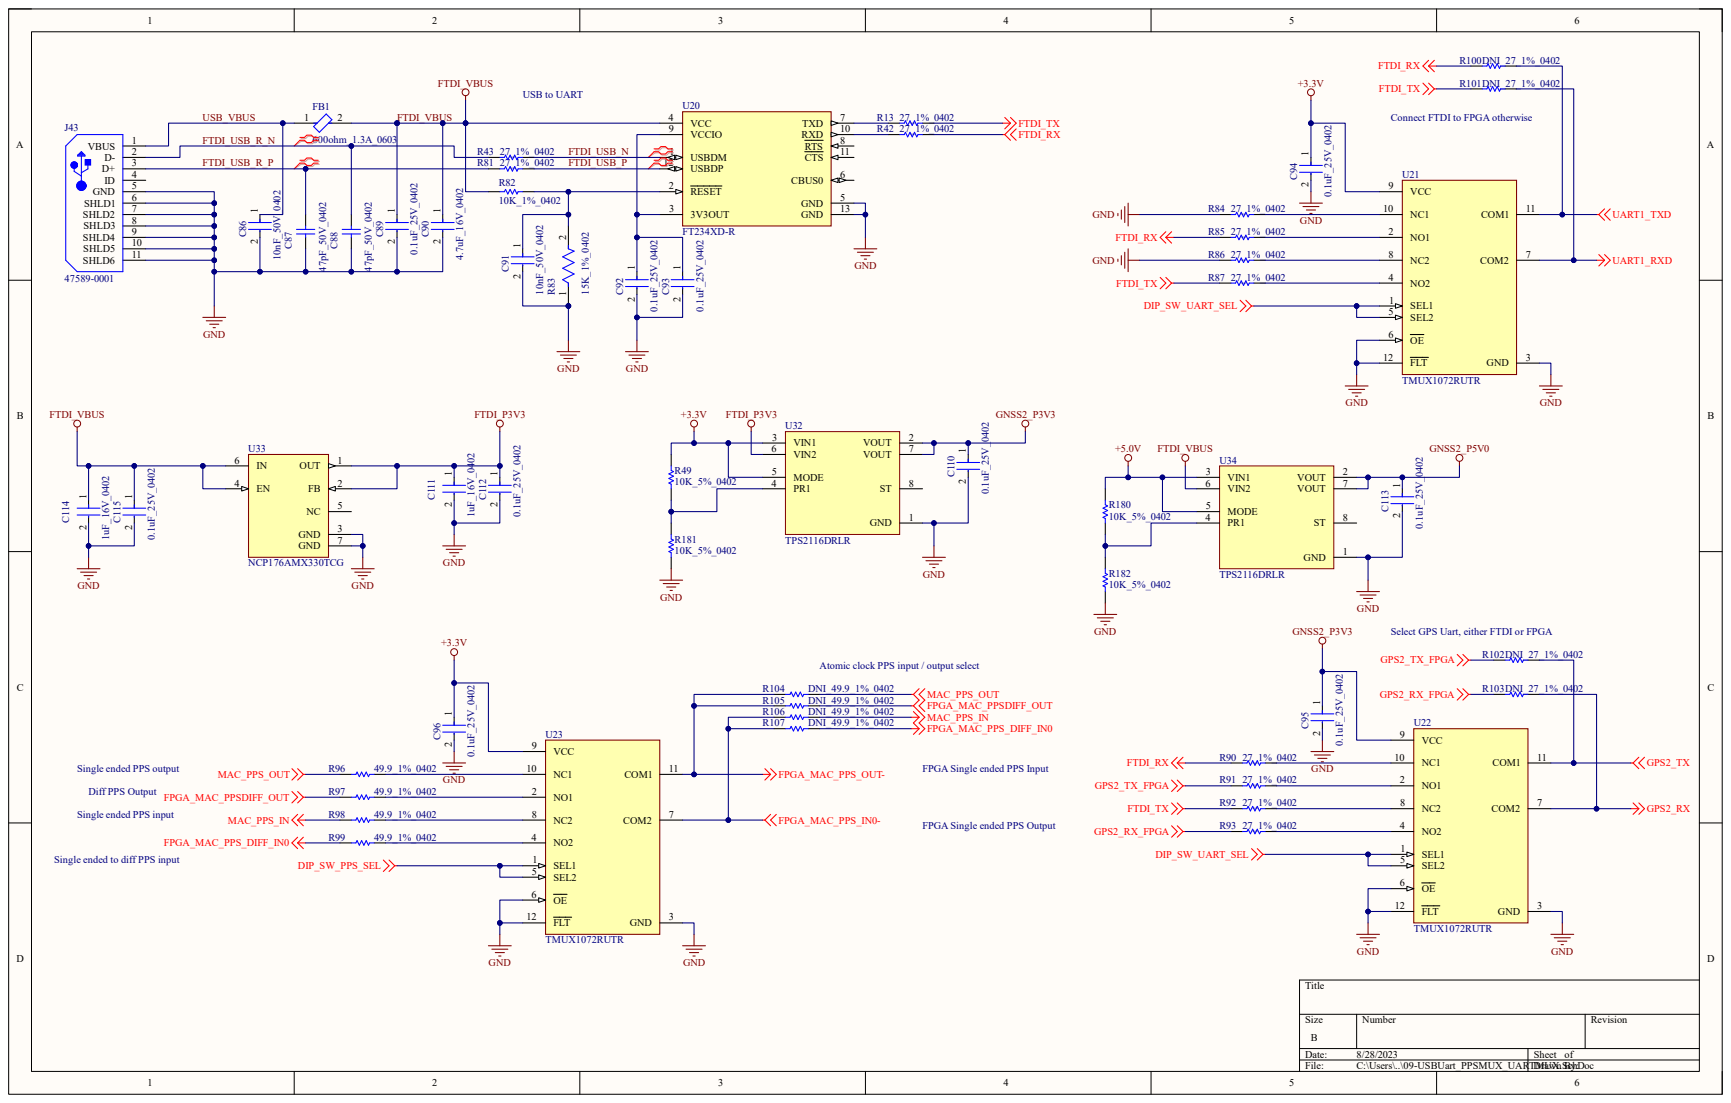
[picture p234: page 9]

Connect FTDI to FPGA otherwise

Select GPS Uart, either FTDI or FPGA

Atomic clock PPS input / output select

Single ended PPS input

Single ended to diff PPS input

# Socket 2 Key B PCIe-based WWAN Adapter Pinout , table 3-21 in M.2 spec

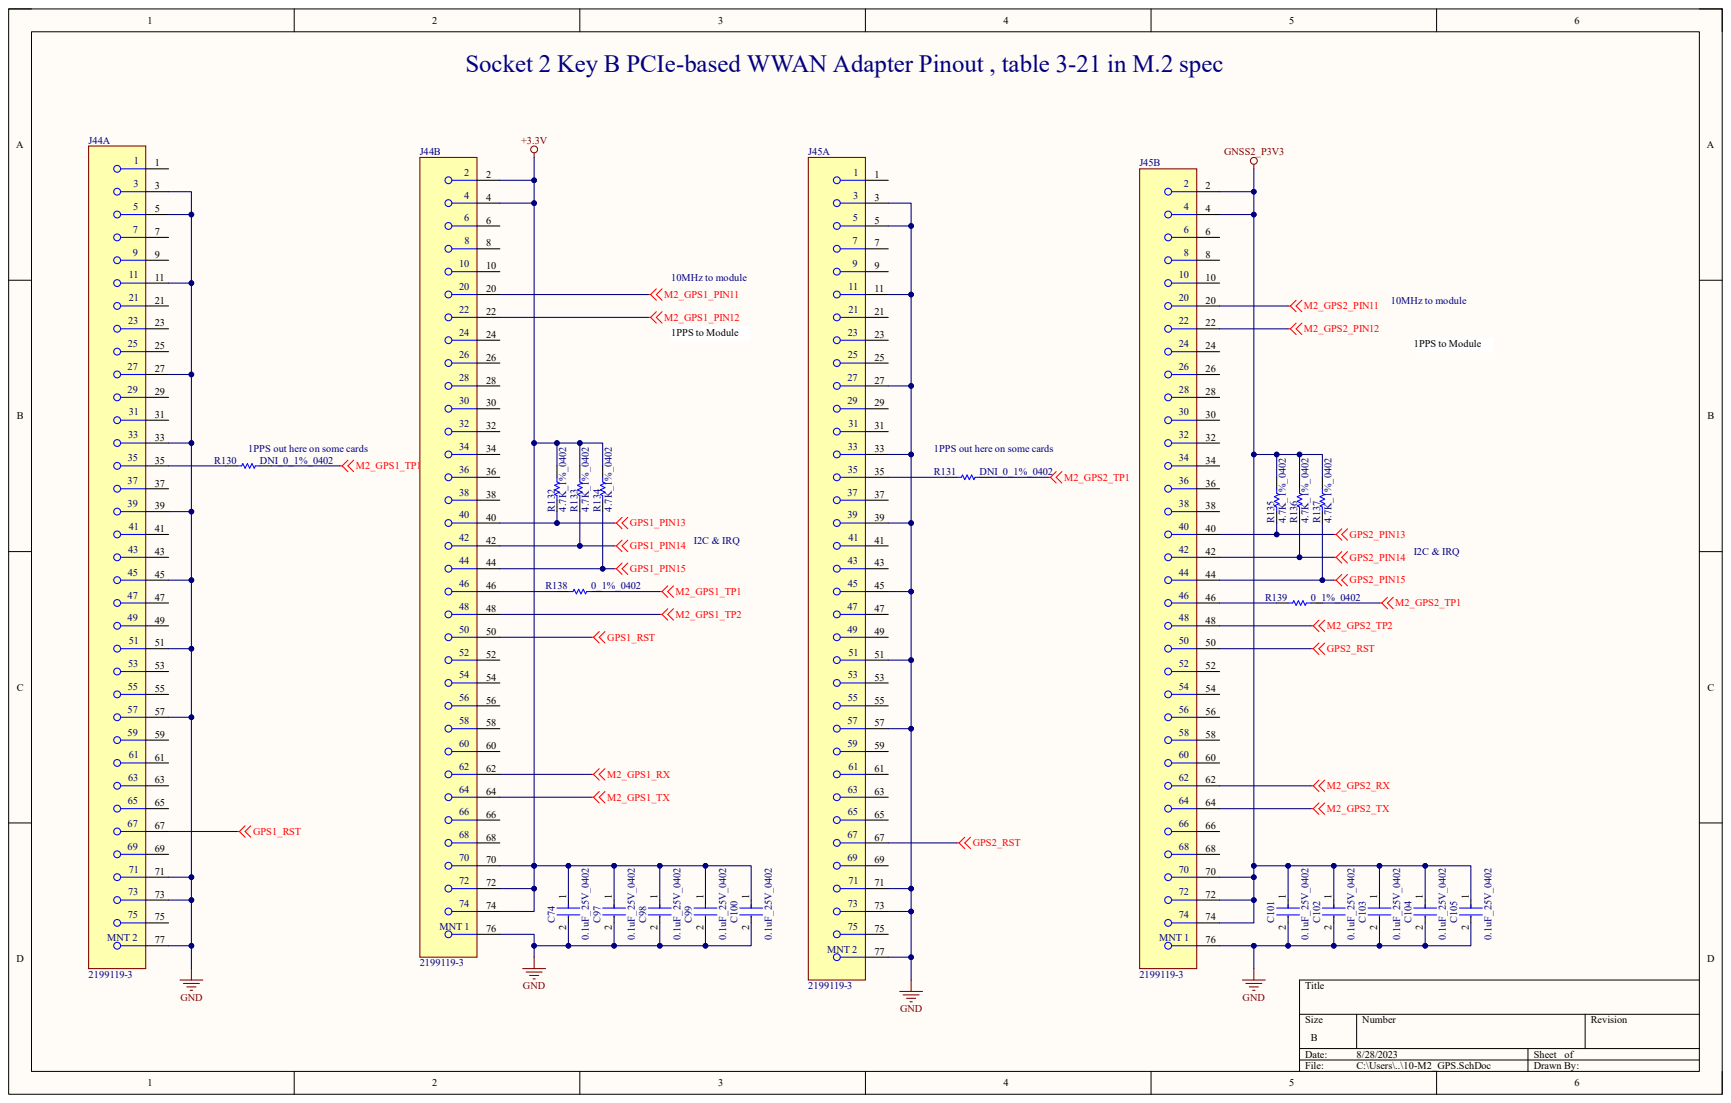
[picture p235: page 10]

1PPS out here on some cards

I2C & IRQ R¹³² 4.7K_1%_0402 R¹³³ 4.7K_1%_0402 R¹³⁴ 4.7K_1%_0402

I2C & IRQ R¹³⁵ 4.7K_1%_0402 R¹³⁶ 4.7K_1%_0402 R¹³⁷ 4.7K_1%_0402

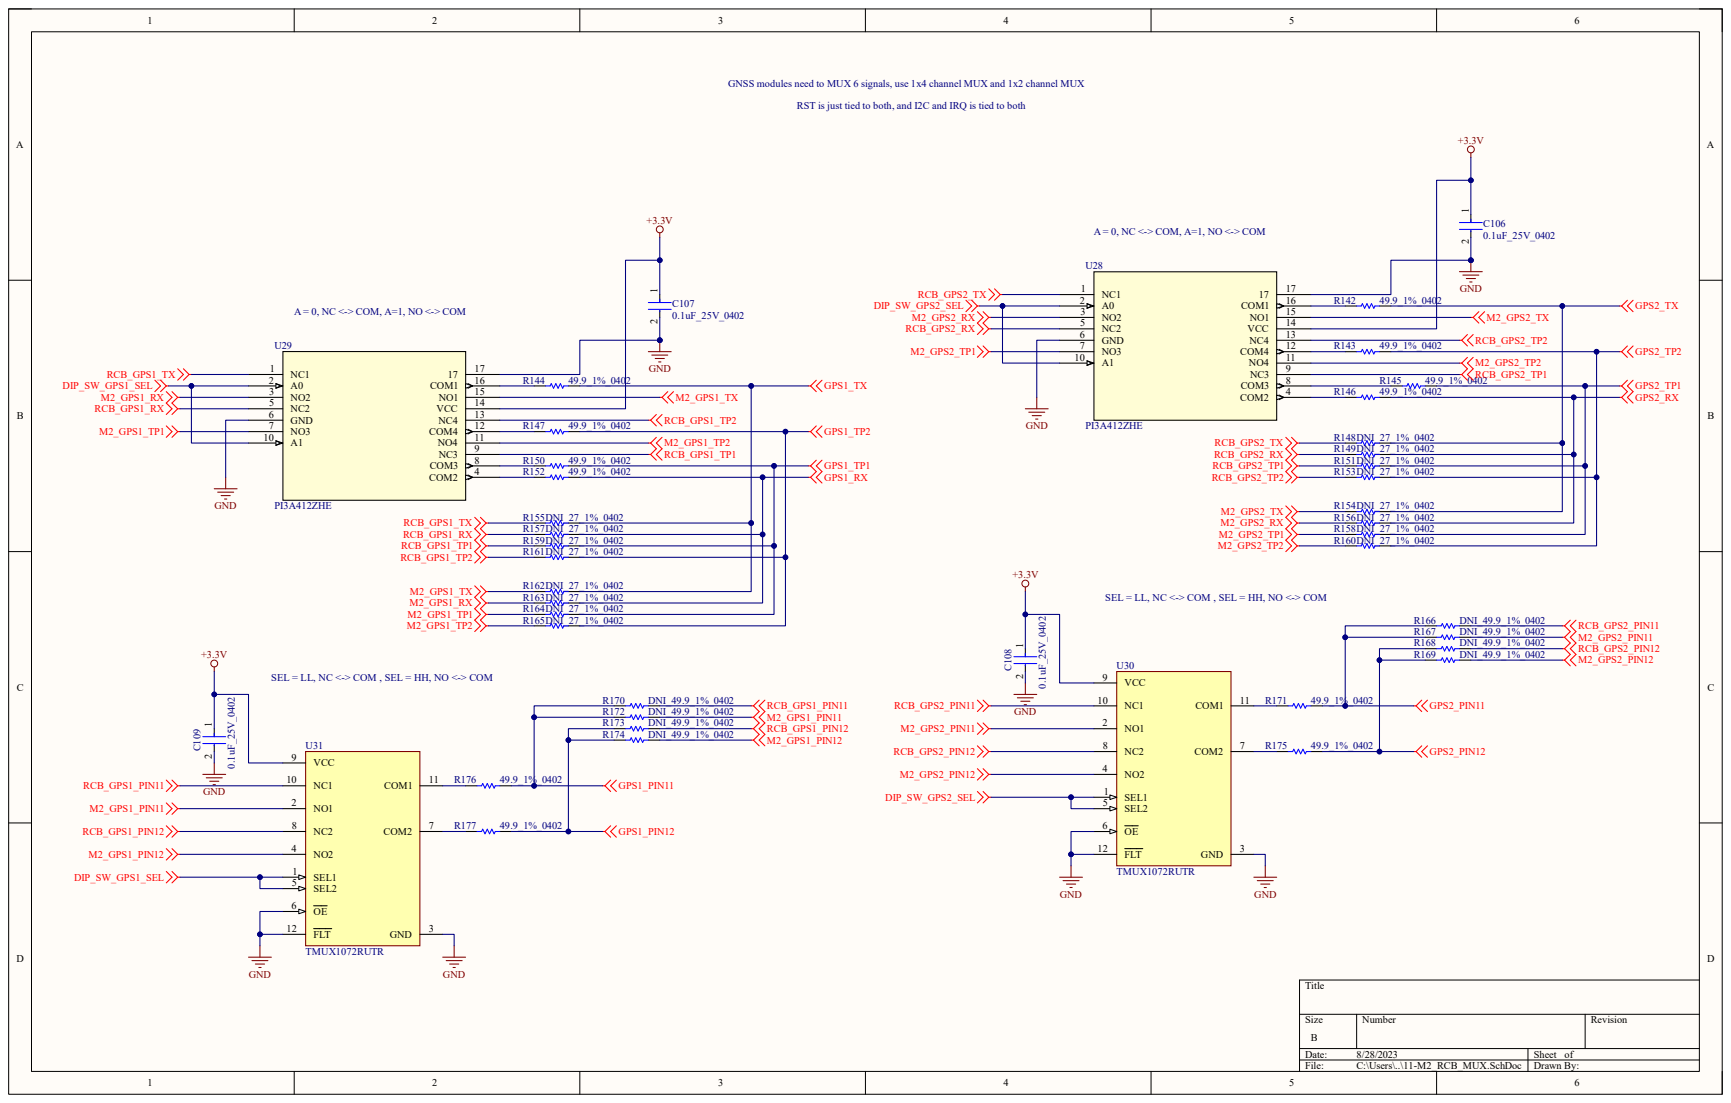
[picture p236: page 11]

GNSS modules need to MUX 6 signals, use 1x4 channel MUX and 1x2 channel MUX 1 2

RST is just tied to both, and I2C and IRQ is tied to both

A = 0, NC <-> COM, A=1, NO <-> COM

SEL = LL, NC <-> COM , SEL = HH, NO <-> COM
