opencomputeproject/Time-Appliance-Project/HW/Production/R4006-G0001-03-SC-REV02.pdf

## CR-1 : @TIMECARD_LIB.TIMECARD(SCH_1):PAGE1

4

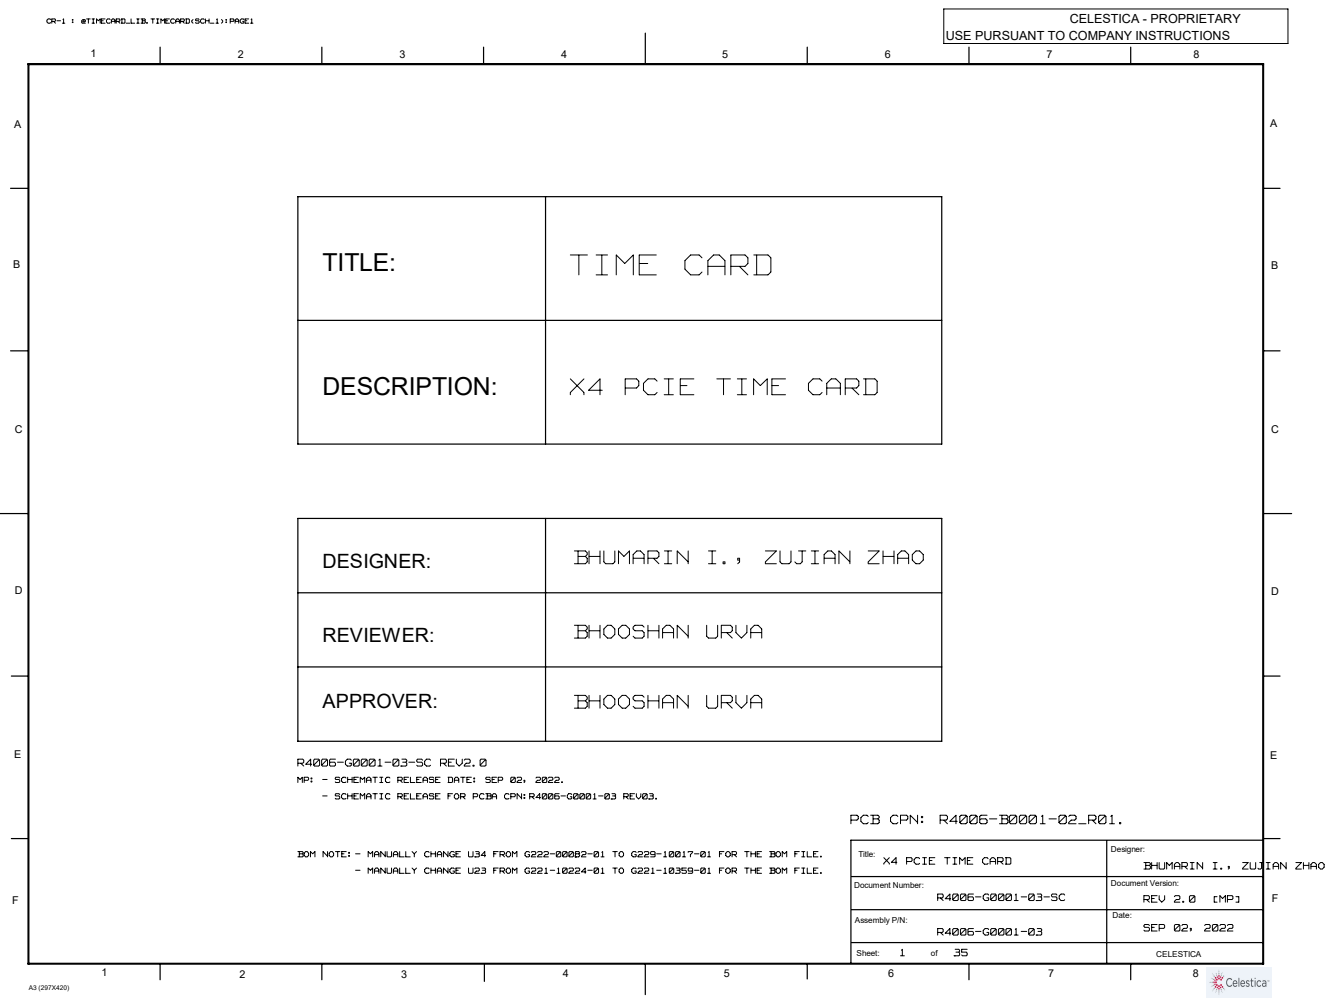
[picture p239: page 1]
PCB CPN: R4006-B0001-02_R01.; BOM NOTE:; CELESTICA - PROPRIETARY

USE PURSUANT TO COMPANY INSTRUCTIONS

TITLE: | TIME CARD

DESCRIPTION: | X4 PCIE TIME CARD

DESIGNER: | BHUMARIN I., ZUJIAN ZHAO

REVIEWER: | BHOOSHAN URVA

APPROVER: | BHOOSHAN URVA

R4006-G0001-03-SC REV2.0
MP: - SCHEMATIC RELEASE DATE: SEP 02, 2022.
- SCHEMATIC RELEASE FOR PCBA CPN:R4006-G0001-03 REV03.

- MANUALLY CHANGE U34 FROM G222-00082-01 TO G229-10017-01 FOR THE BOM FILE.
- MANUALLY CHANGE U23 FROM G221-10224-01 TO G221-10359-01 FOR THE BOM FILE.

Title: X4 PCIE TIME CARD | Designer:

BHUMARIN I., ZUJIAN ZHAO

Document Number: R4006-G0001-03-SC | Document Version: REV 2.0 [MP]

Assembly P/N: R4006-G0001-03 | Date: SEP 02, 2022

1 35 Sheet: of | CELESTICA

# PAGE 1

# PAGE 25

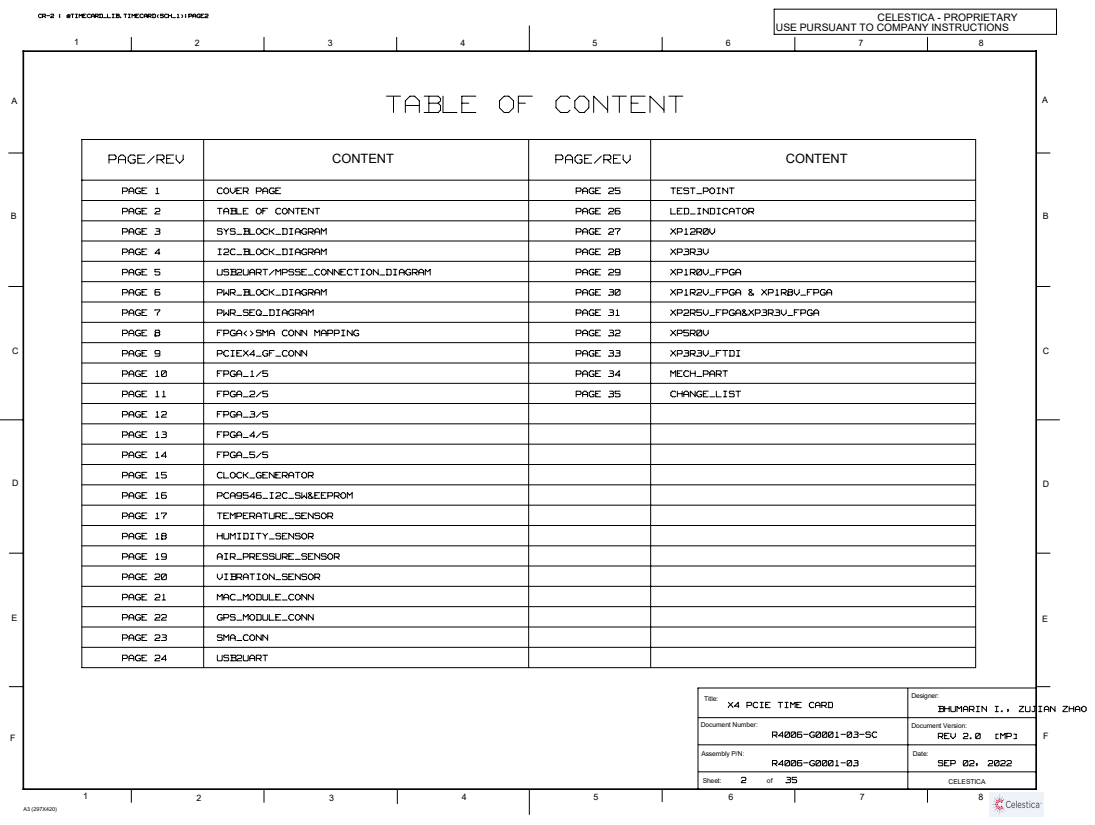
[picture p240: page 2]
PAGE 7; PAGE 5; PAGE 6; PAGE 8; PAGE 11; PAGE 20; PAGE 23; PAGE 4; PAGE 10; PAGE 3; PAGE 12; PAGE 18; PAGE 2; PAGE 17; PAGE 22; PAGE 19; PAGE 21; PAGE 31; PAGE 28; PAGE 29; PAGE 26; MECH_PART; XP1R2V_FPGA & XP1R8V_FPGA; XP3R3V_FTDI; XP2R5V_FPGA&XP3R3V_FPGA; CHANGE_LIST; PAGE 27; PAGE 30; PAGE 33; PAGE 32; PAGE 34; PAGE 35; XP1R0V_FPGA; LED_INDICATOR; TEST_POINT; SYS_BLOCK_DIAGRAM; I2C_BLOCK_DIAGRAM; USB2UART/MPSSE_CONNECTION_DIAGRAM; PWR_BLOCK_DIAGRAM; COVER PAGE; TABLE OF CONTENT; PAGE 15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

TABLE OF CONTENT

Title: X4 PCIE TIME CARD | Designer:

BHUMARIN I., ZUJIAN ZHAO

Document Number: R4006-G0001-03-SC | Document Version: REV 2.0 [MP]

Assembly P/N: R4006-G0001-03 | Date: SEP 02, 2022

Sheet: 2 35 of

# SYS_BLOCK_DIAGRAM

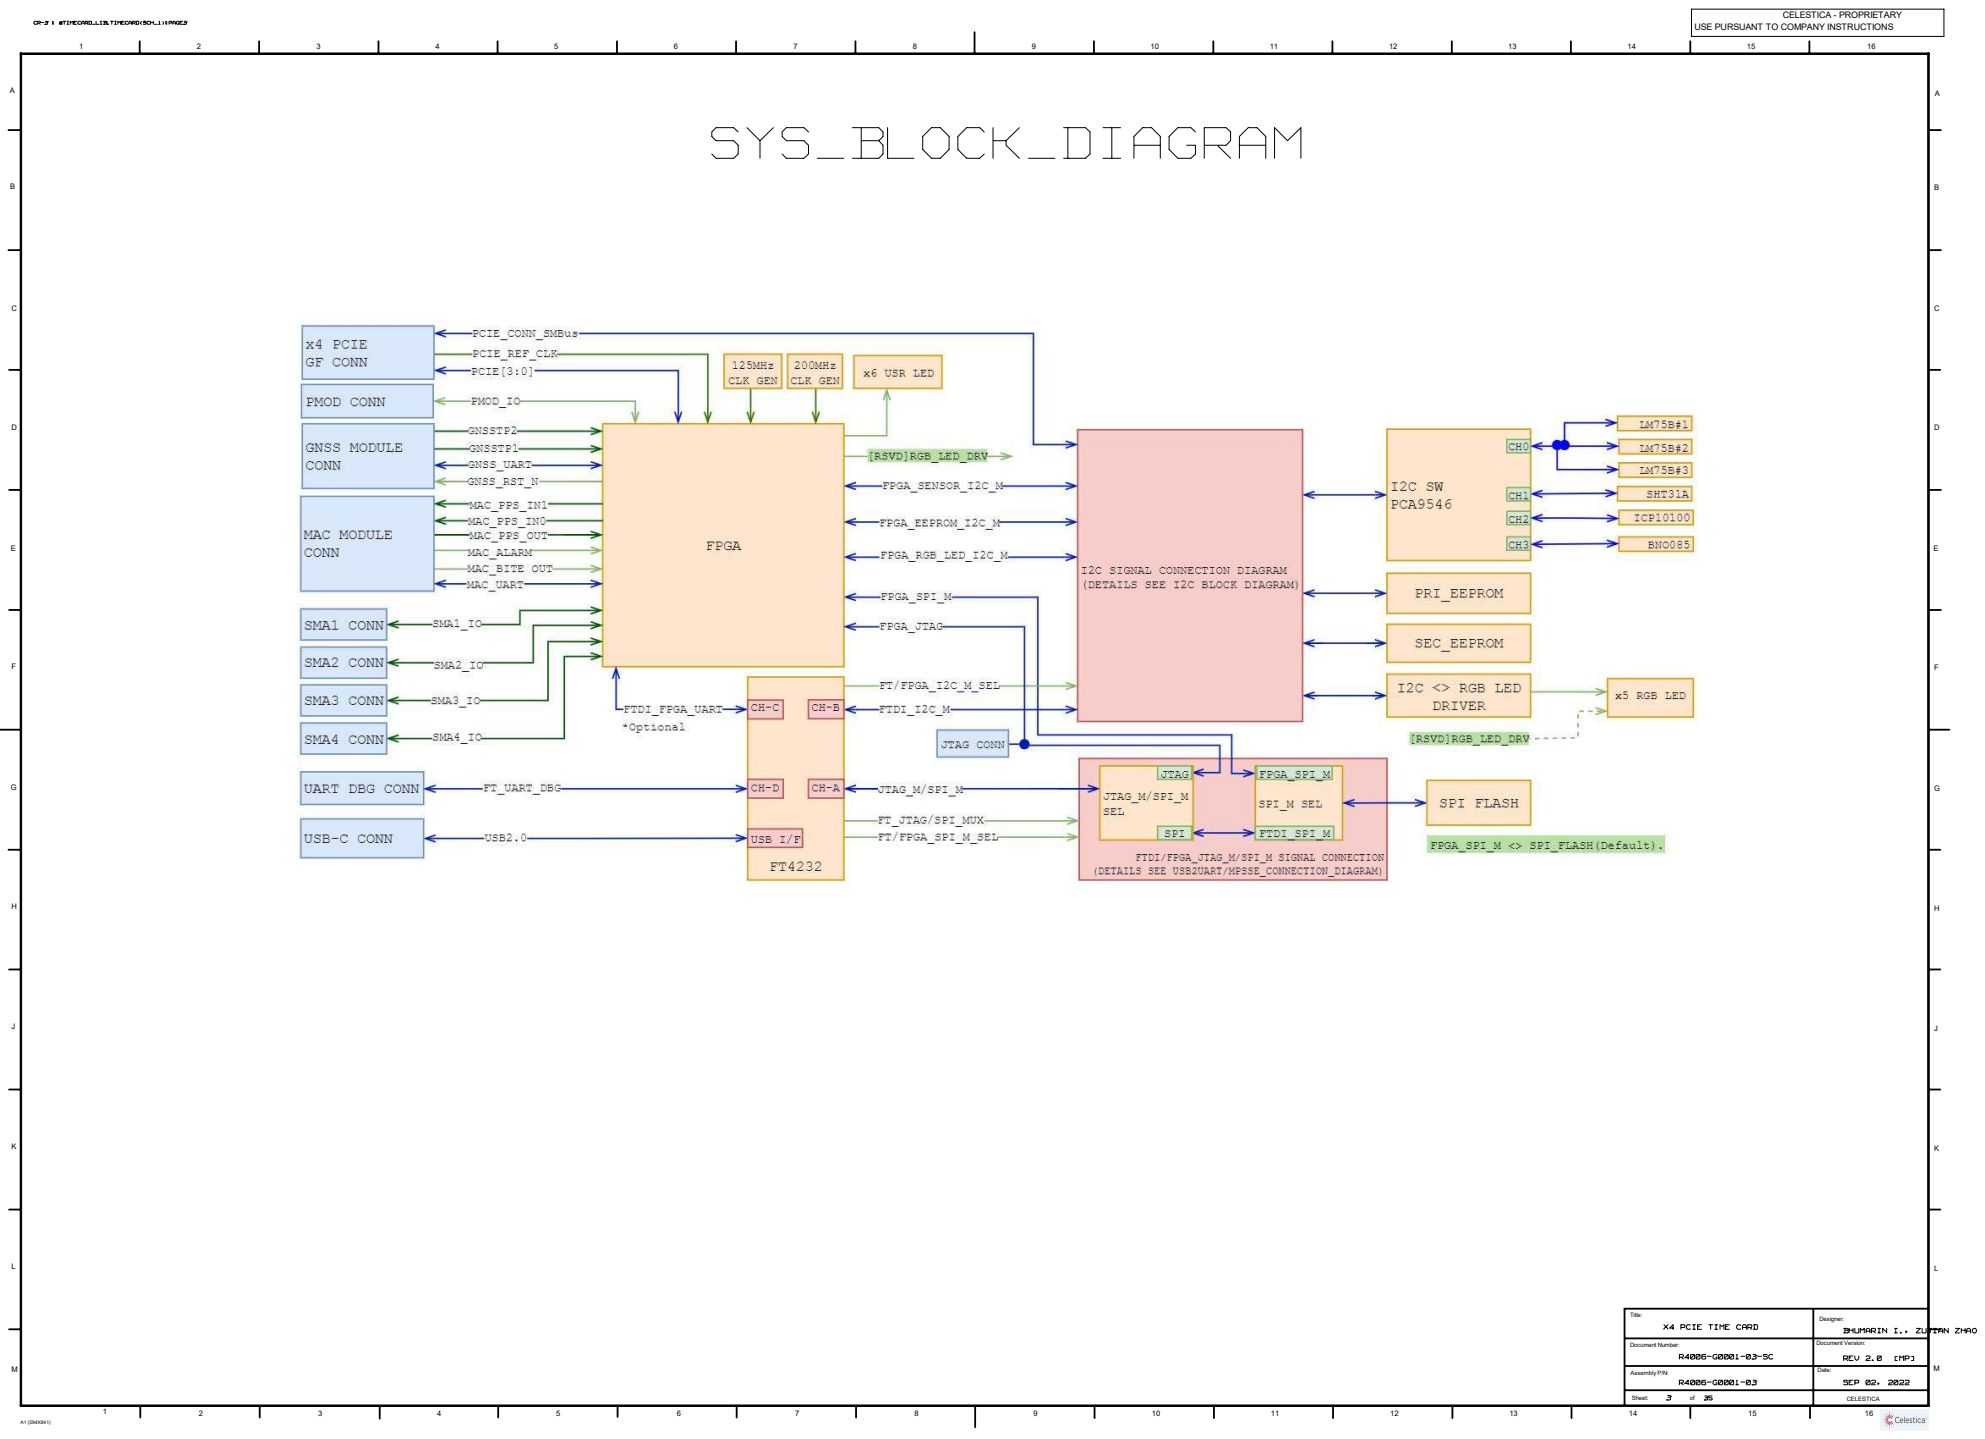
[picture p241: page 3]
CR-3 : @TIMECARD_LIB.TIMECARD(SCH_1):PAGE3; X4 PCIE TIME CARD; BHUMARIN I., ZUJIAN ZHAO

Title: | Designer:

Document Number: R4006-G0001-03-SC | Document Version: REV 2.0 [MP]

R4006-G0001-03 | Date: Assembly P/N: SEP 02, 2022

Sheet: of 35

# I2C_BLOCK_DIAGRAM

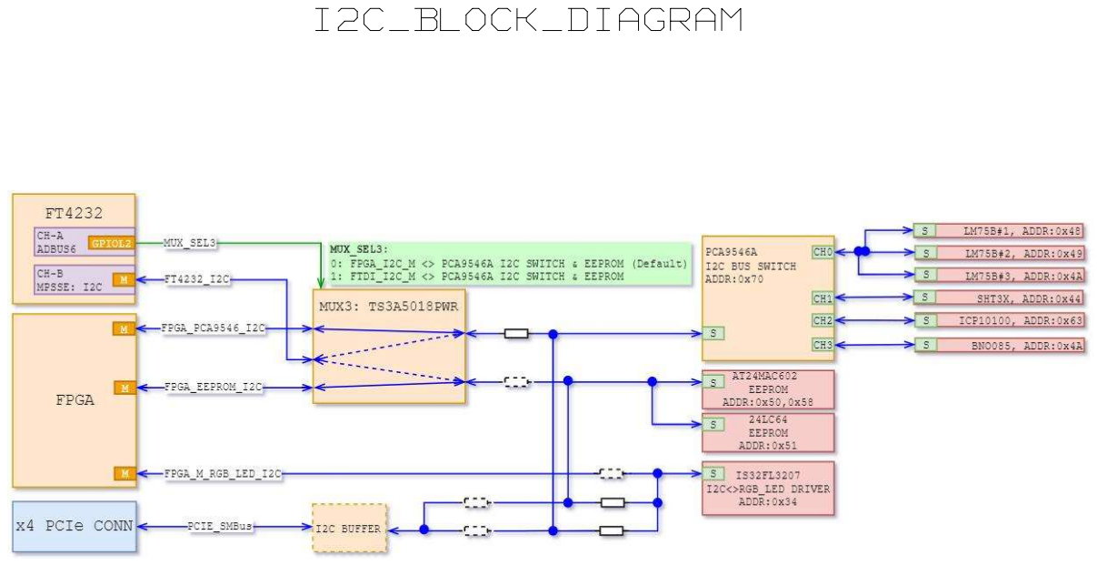
[picture p242: page 4]
CR-4 : @TIMECARD_LIB.TIMECARD(SCH_1):PAGE4; X4 PCIE TIME CARD; BHUMARIN I., ZUJIAN ZHAO

Title: | Designer:

Document Number: R4006-G0001-03-SC | Document Version:

# USB2UART/MPSSE_CONNECTION_DIAGRAM

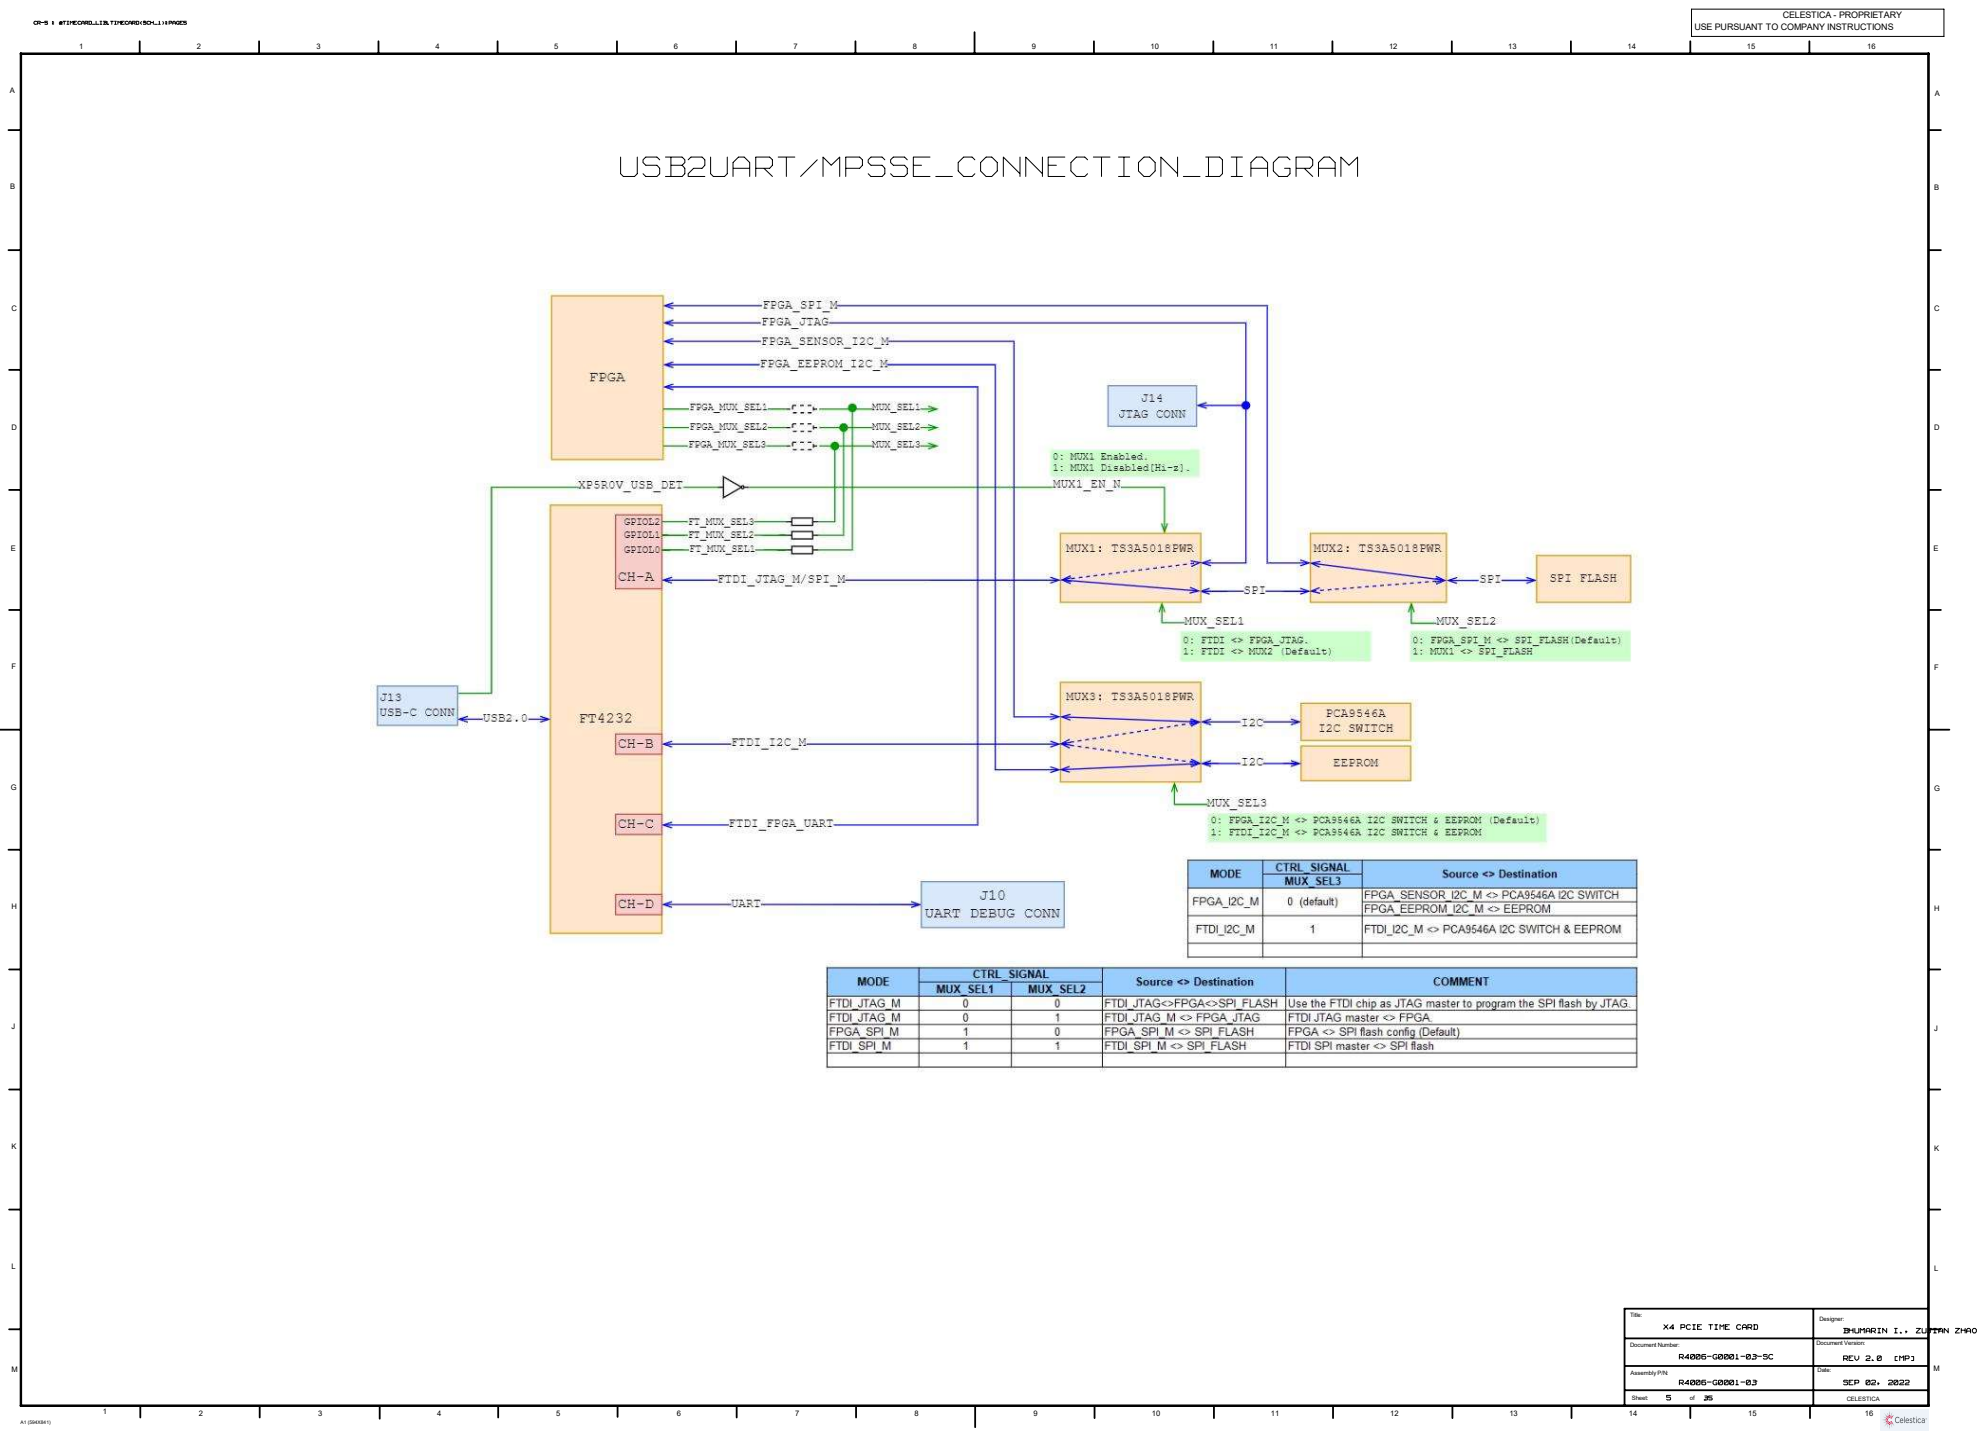
[picture p243: page 5]
CR-5 : @TIMECARD_LIB.TIMECARD(SCH_1):PAGE5; X4 PCIE TIME CARD; BHUMARIN I., ZUJIAN ZHAO

Title: | Designer:

Document Number: R4006-G0001-03-SC | Document Version:

# PWR_BLOCK_DIAGRAM

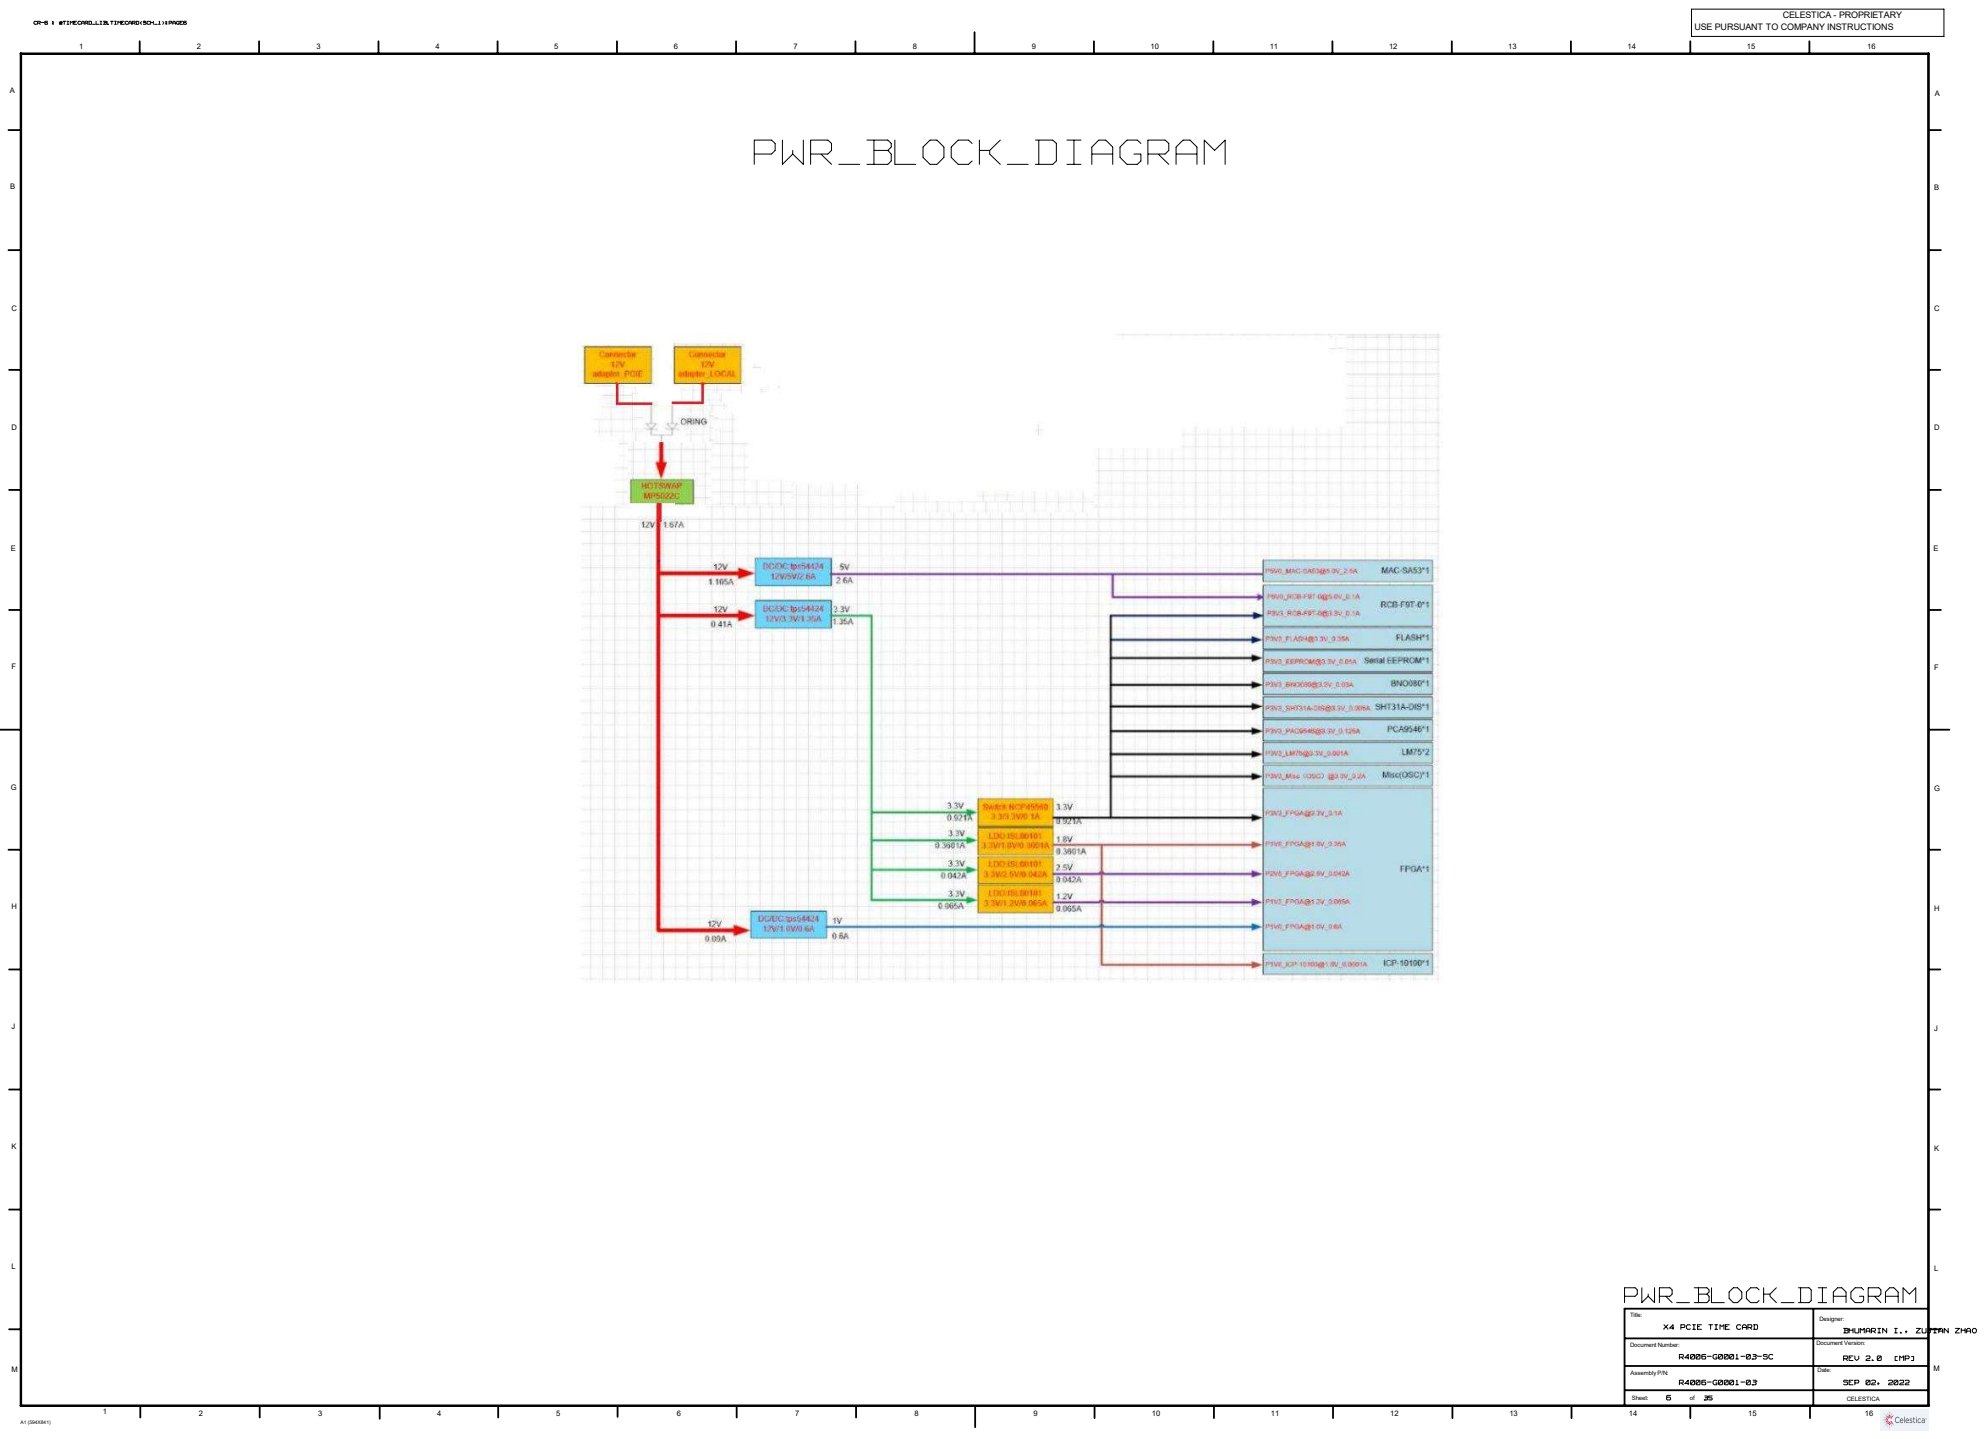
[picture p244: page 6]
CR-6 : @TIMECARD_LIB.TIMECARD(SCH_1):PAGE6; X4 PCIE TIME CARD; BHUMARIN I., ZUJIAN ZHAO; PWR_BLOCK_DIAGRAM

Title: | Designer:

Document Number: R4006-G0001-03-SC | Document Version:

# PWR_SEQ_DIAGRAM

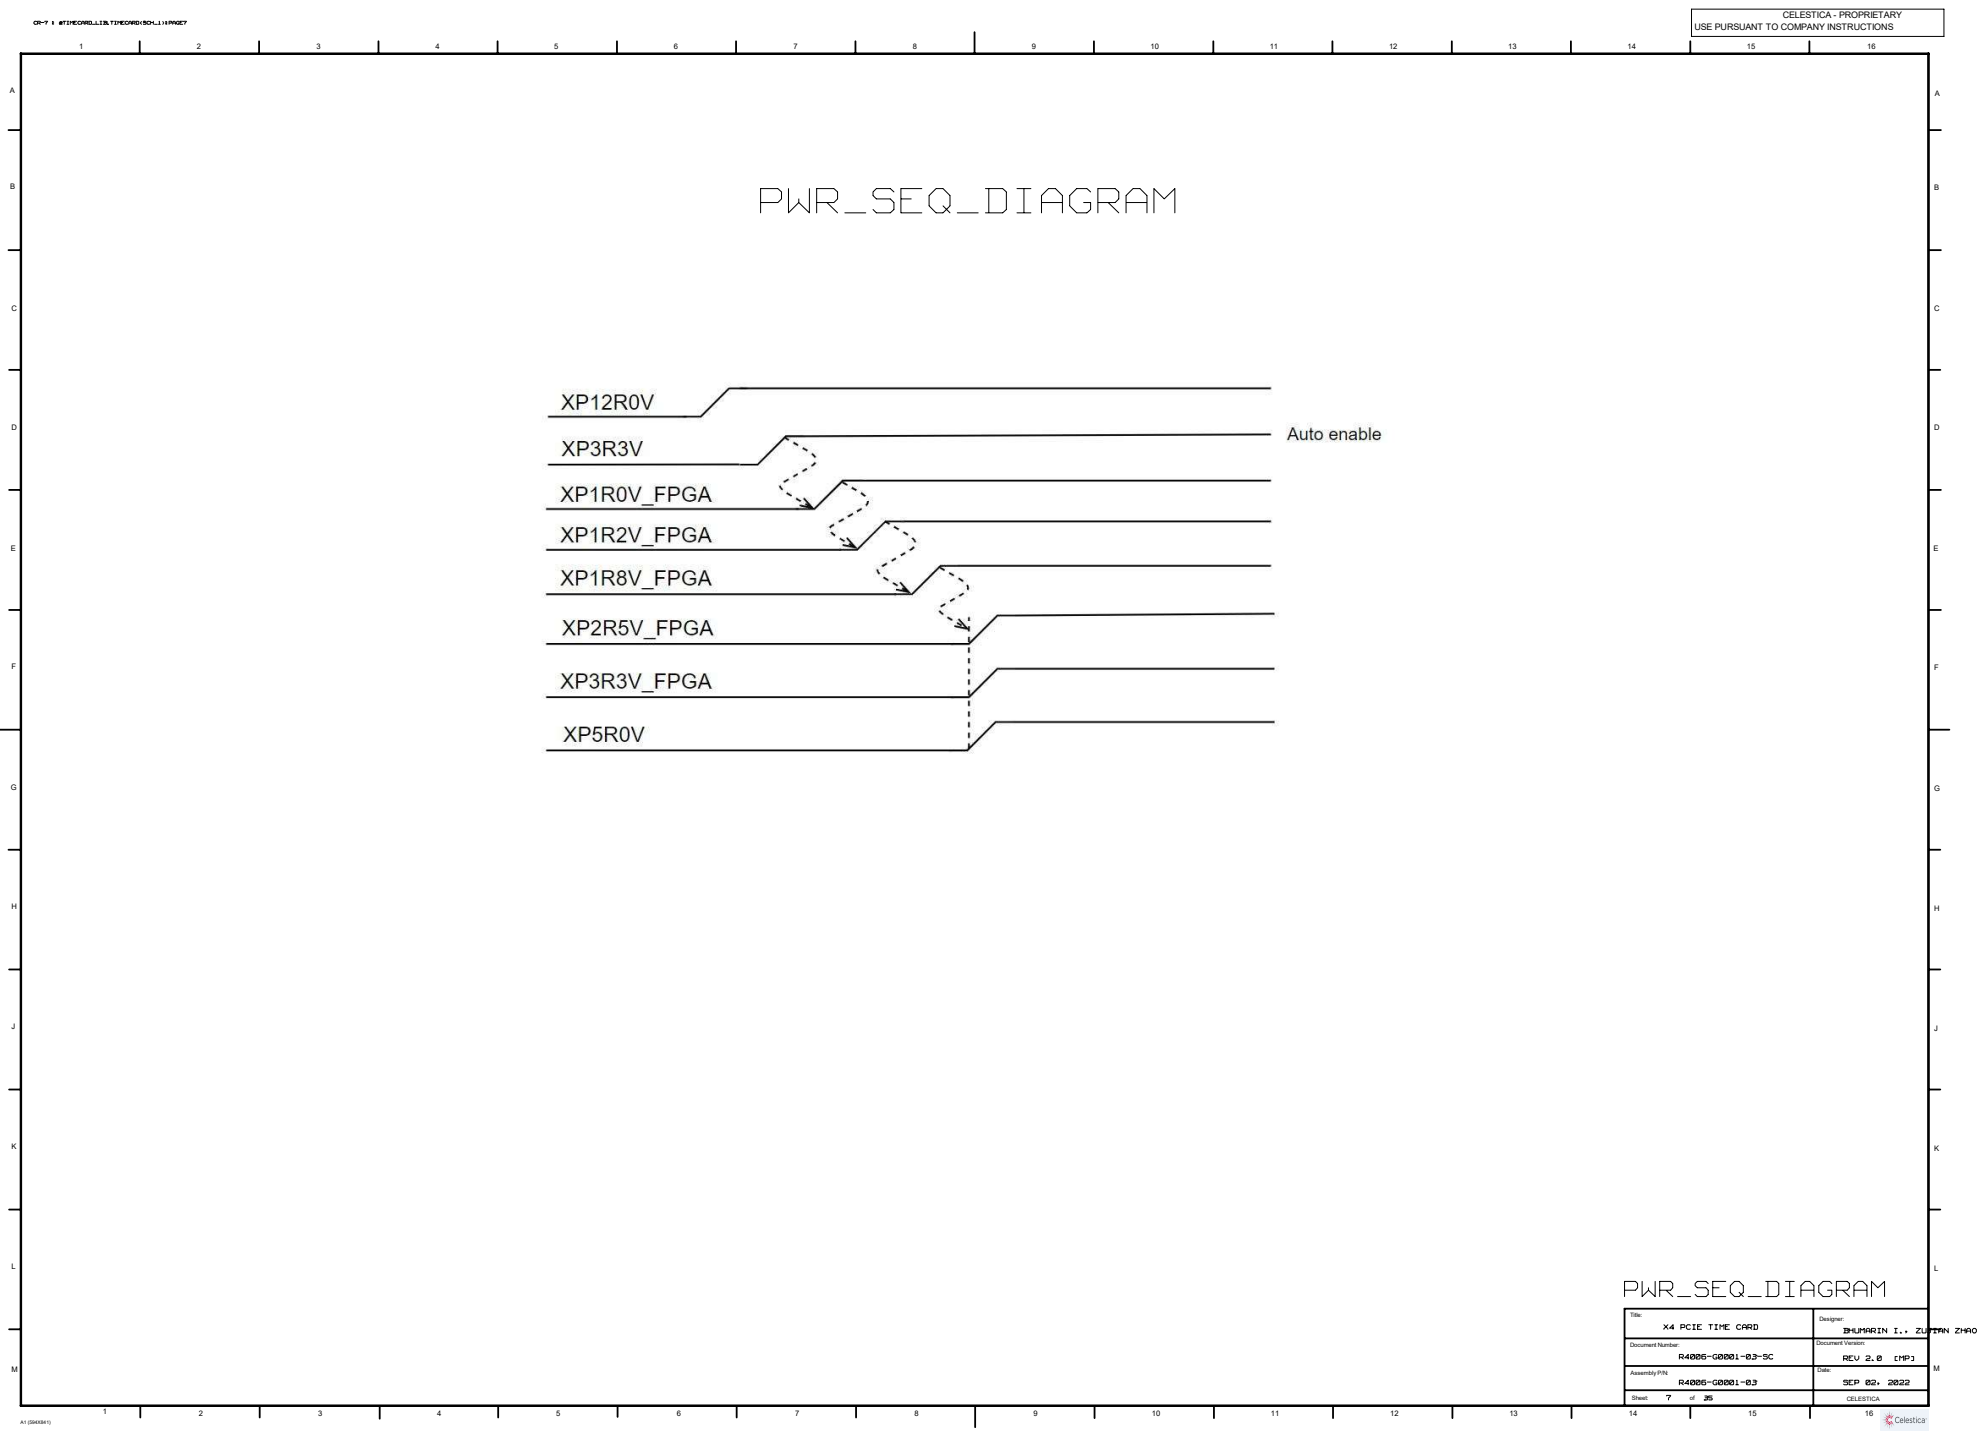
[picture p245: page 7]
CR-7 : @TIMECARD_LIB.TIMECARD(SCH_1):PAGE7; X4 PCIE TIME CARD; BHUMARIN I., ZUJIAN ZHAO; PWR_SEQ_DIAGRAM

Title: | Designer:

Document Number: R4006-G0001-03-SC | Document Version:

# FPGA<>SMA CONN MAPPING

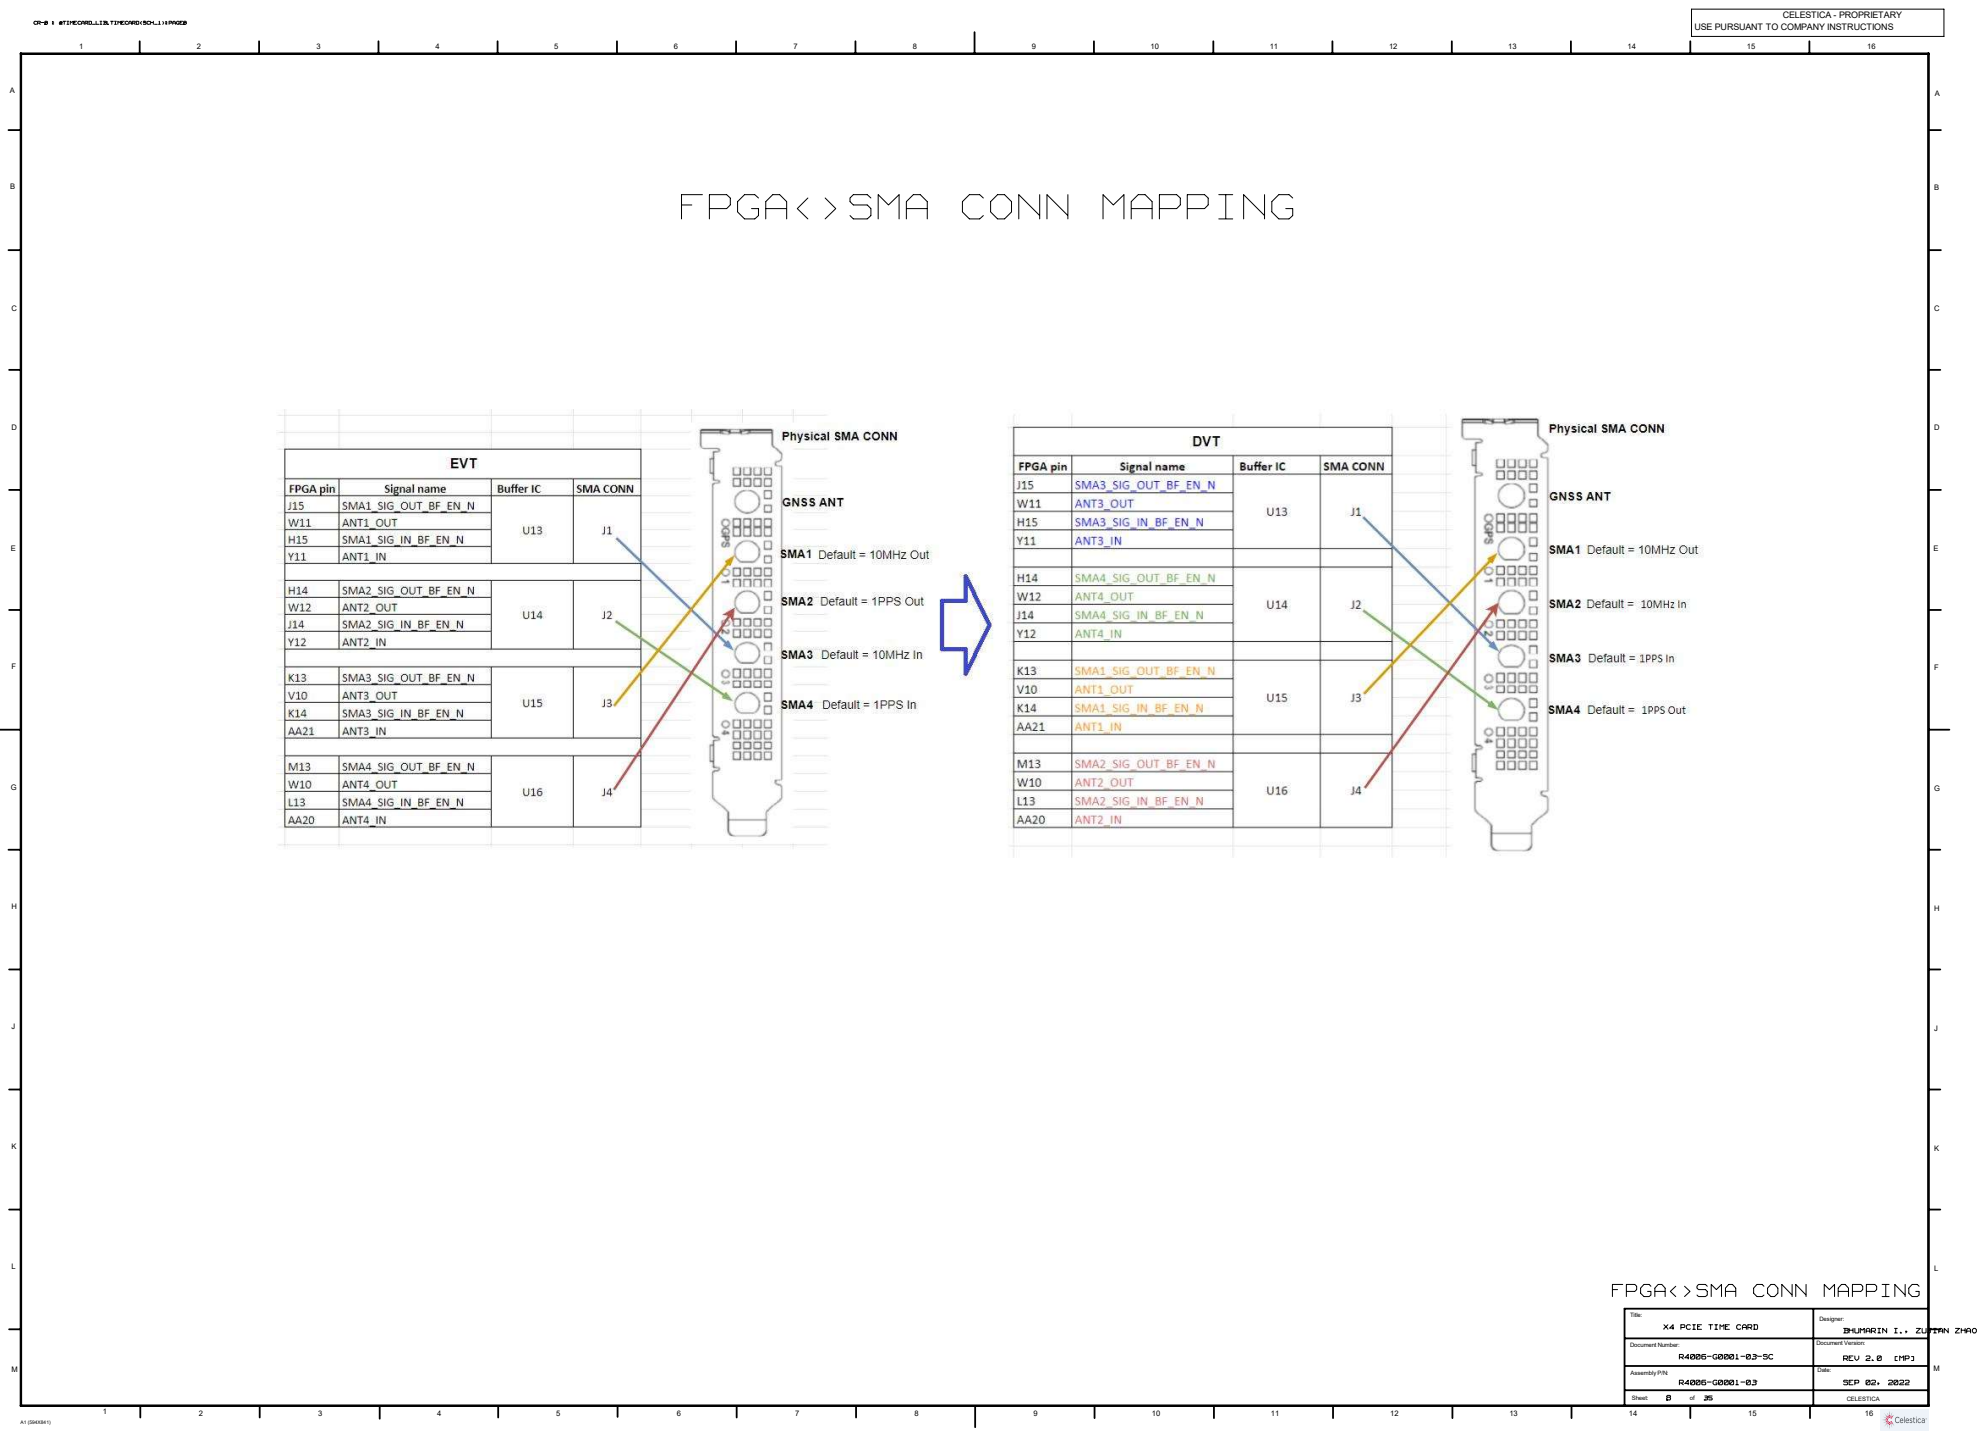
[picture p246: page 8]
CR-8 : @TIMECARD_LIB.TIMECARD(SCH_1):PAGE8; X4 PCIE TIME CARD; BHUMARIN I., ZUJIAN ZHAO

FPGA<>SMA CONN MAPPING

Title: | Designer:

Document Number: R4006-G0001-03-SC | Document Version:

# PCIE_X4_GF_CONN

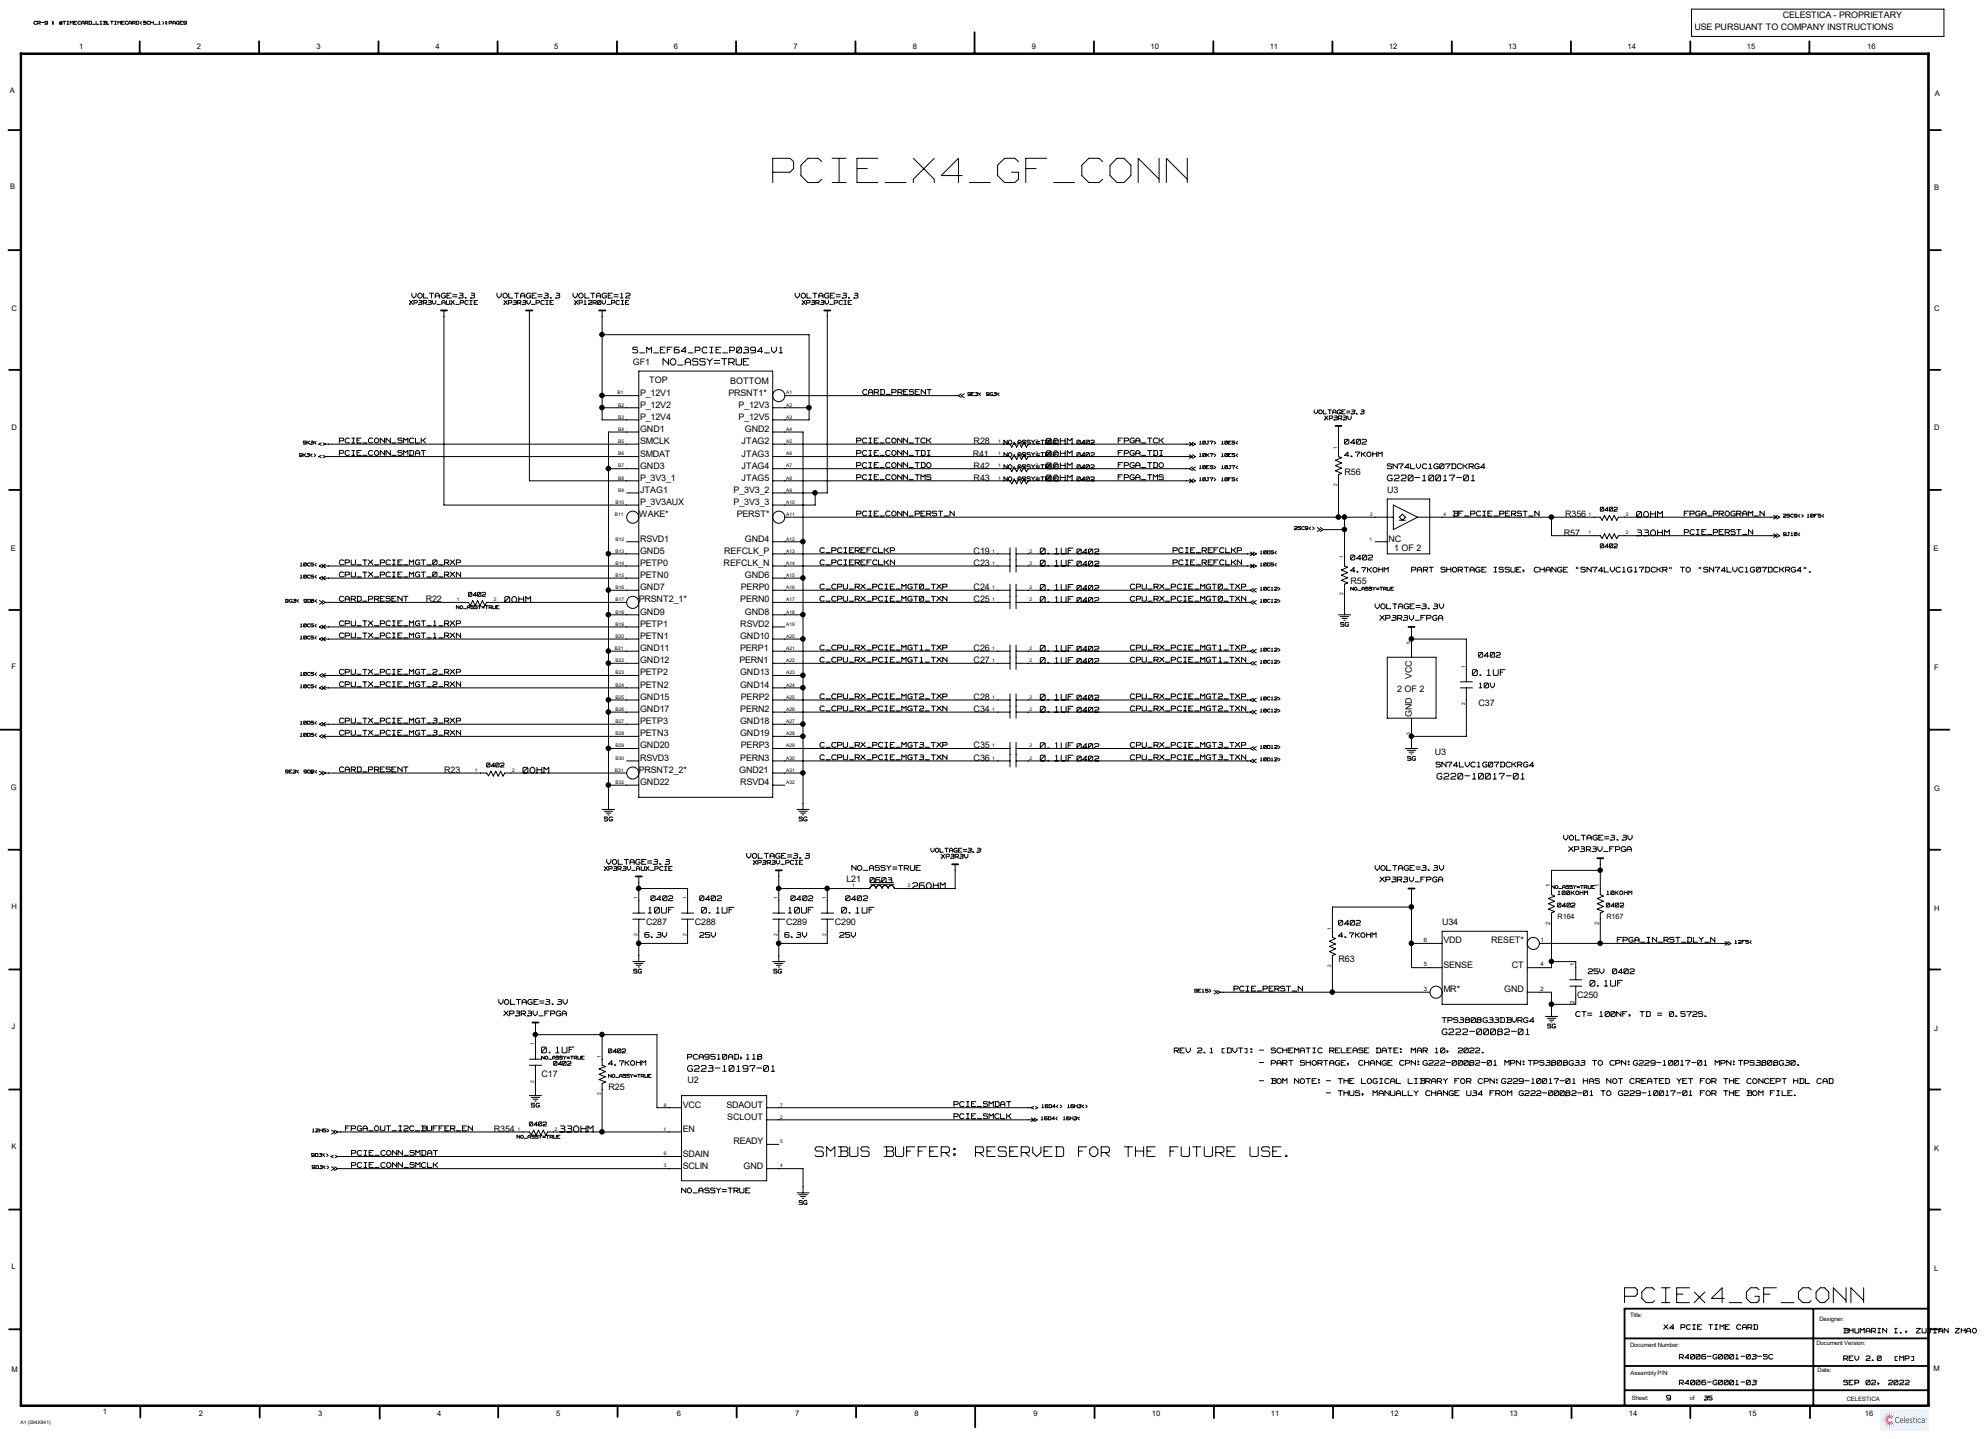
[picture p247: page 9]

PART SHORTAGE ISSUE, CHANGE "SN74LVC1G17DCKR" TO "SN74LVC1G07DCKRG4".

- SCHEMATIC RELEASE DATE: MAR 10, 2022.
- PART SHORTAGE, CHANGE CPN:G222-00082-01 MPN:TPS3808G33 TO CPN:G229-10017-01 MPN:TPS3808G30.
- BOM NOTE:

- THE LOGICAL LIBRARY FOR CPN:G229-10017-01 HAS NOT CREATED YET FOR THE CONCEPT HDL CAD
- THUS, MANUALLY CHANGE U34 FROM G222-00082-01 TO G229-10017-01 FOR THE BOM FILE.

SMBUS BUFFER: RESERVED FOR THE FUTURE USE.

Title: | Designer:

Document Number: R4006-G0001-03-SC | Document Version:

# FPGA 1/5

G240-10069-01

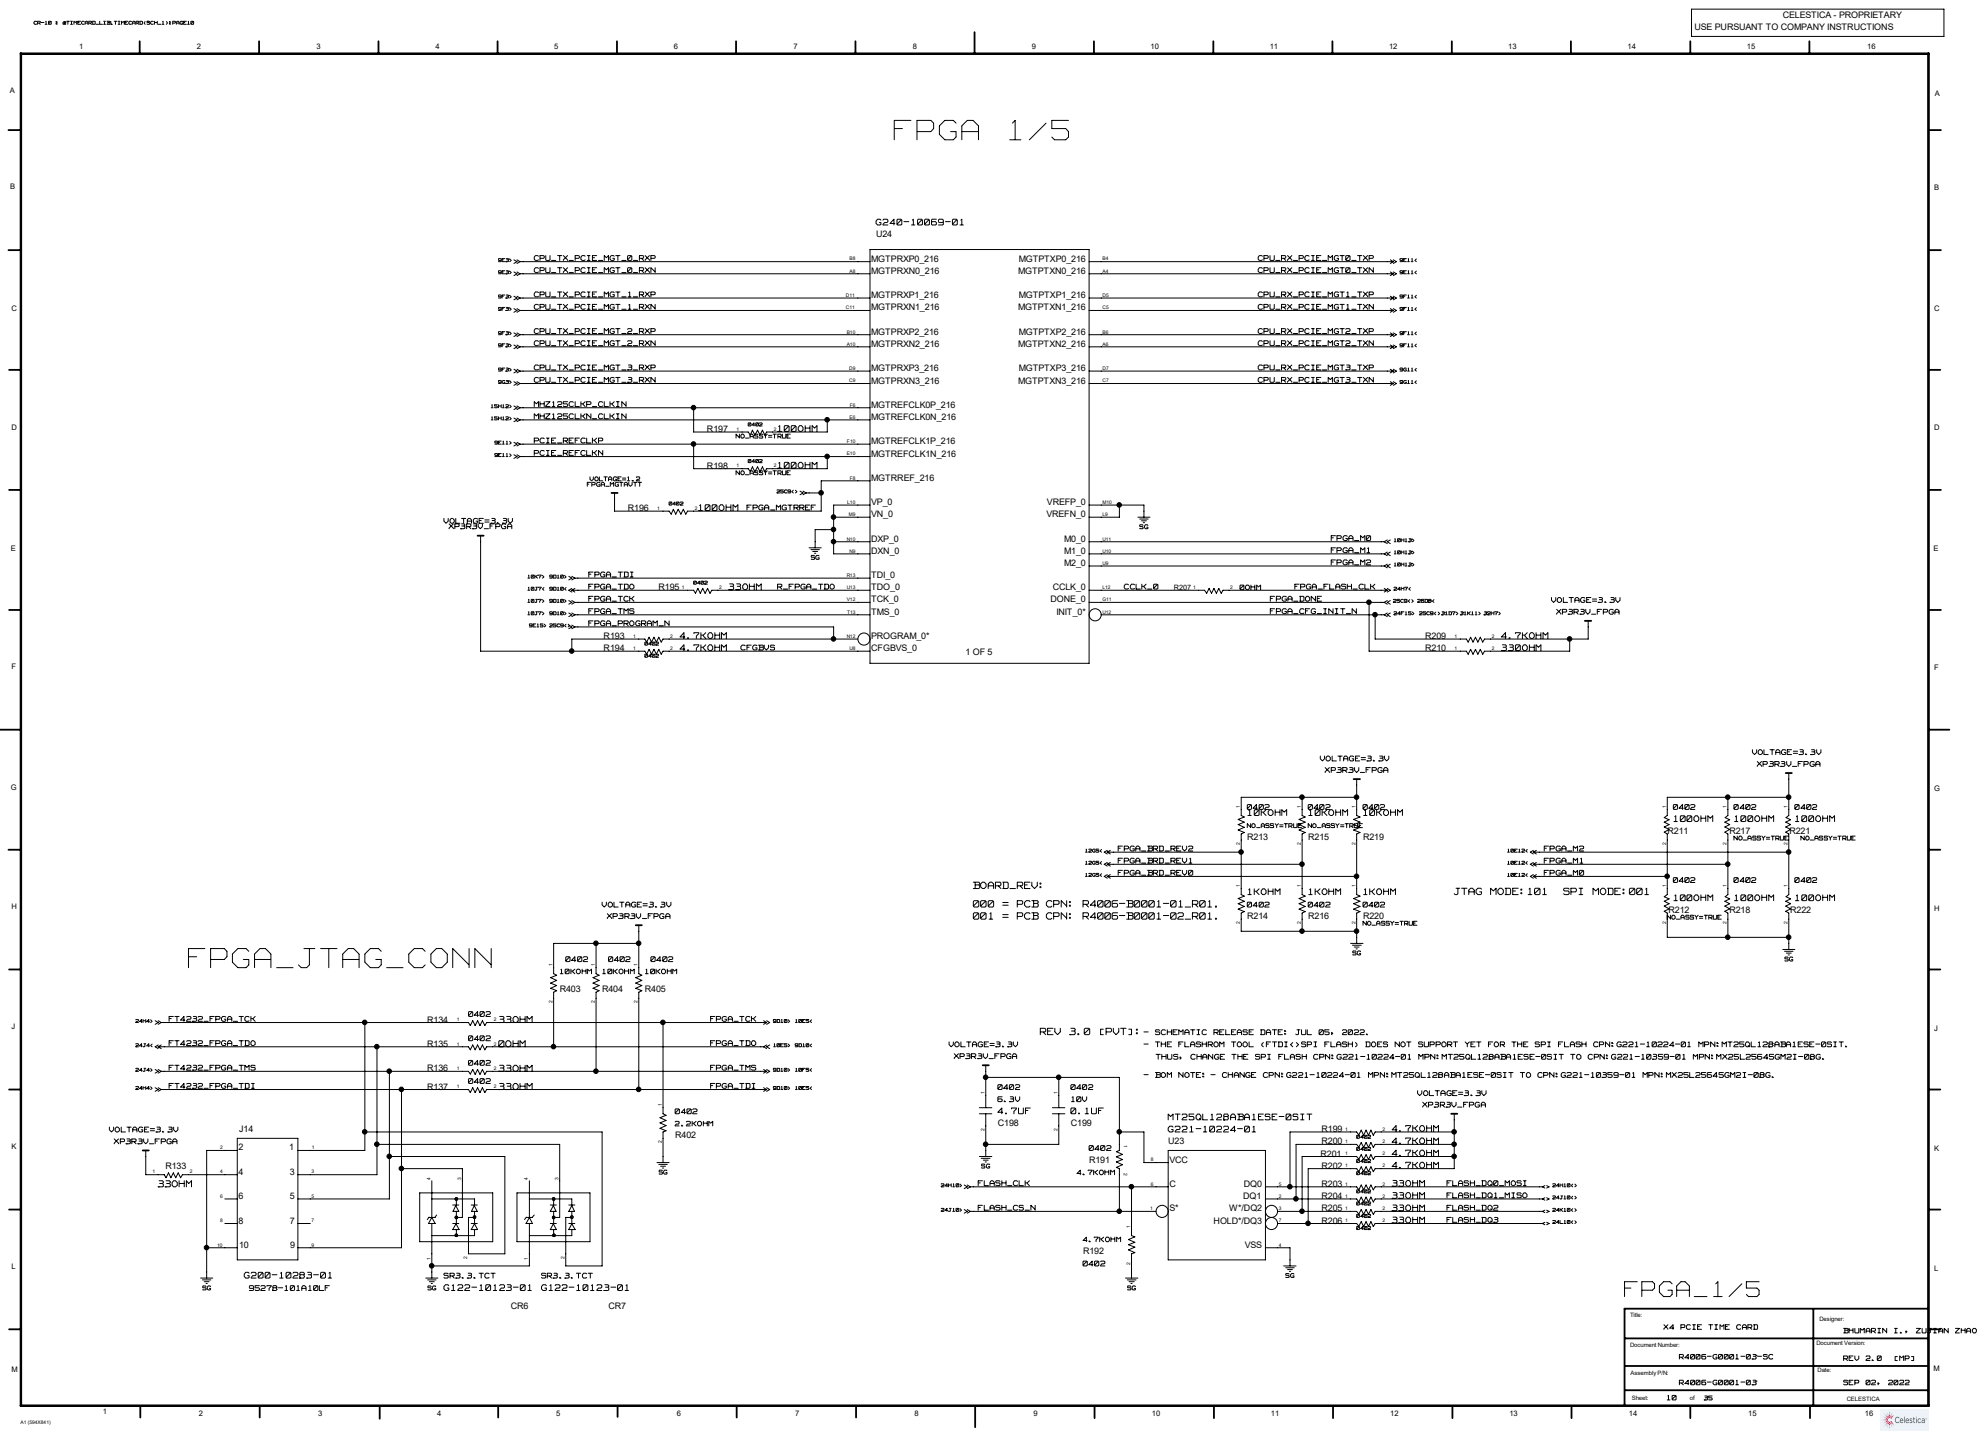
[picture p248: page 10]

REV 3.0 [PVT]: - SCHEMATIC RELEASE DATE: JUL 05, 2022.

- THE FLASHROM TOOL (FTDI<>SPI FLASH) DOES NOT SUPPORT YET FOR THE SPI FLASH CPN:G221-10224-01 MPN:MT25QL128ABA1ESE-0SIT.
THUS, CHANGE THE SPI FLASH CPN:G221-10224-01 MPN:MT25QL128ABA1ESE-0SIT TO CPN:G221-10359-01 MPN:MX25L25645GM2I-08G.
- BOM NOTE:

- CHANGE CPN:G221-10224-01 MPN:MT25QL128ABA1ESE-0SIT TO CPN:G221-10359-01 MPN:MX25L25645GM2I-08G.

Title: | Designer:

Document Number: R4006-G0001-03-SC | Document Version:

# FPGA 2/5

G240-10069-01

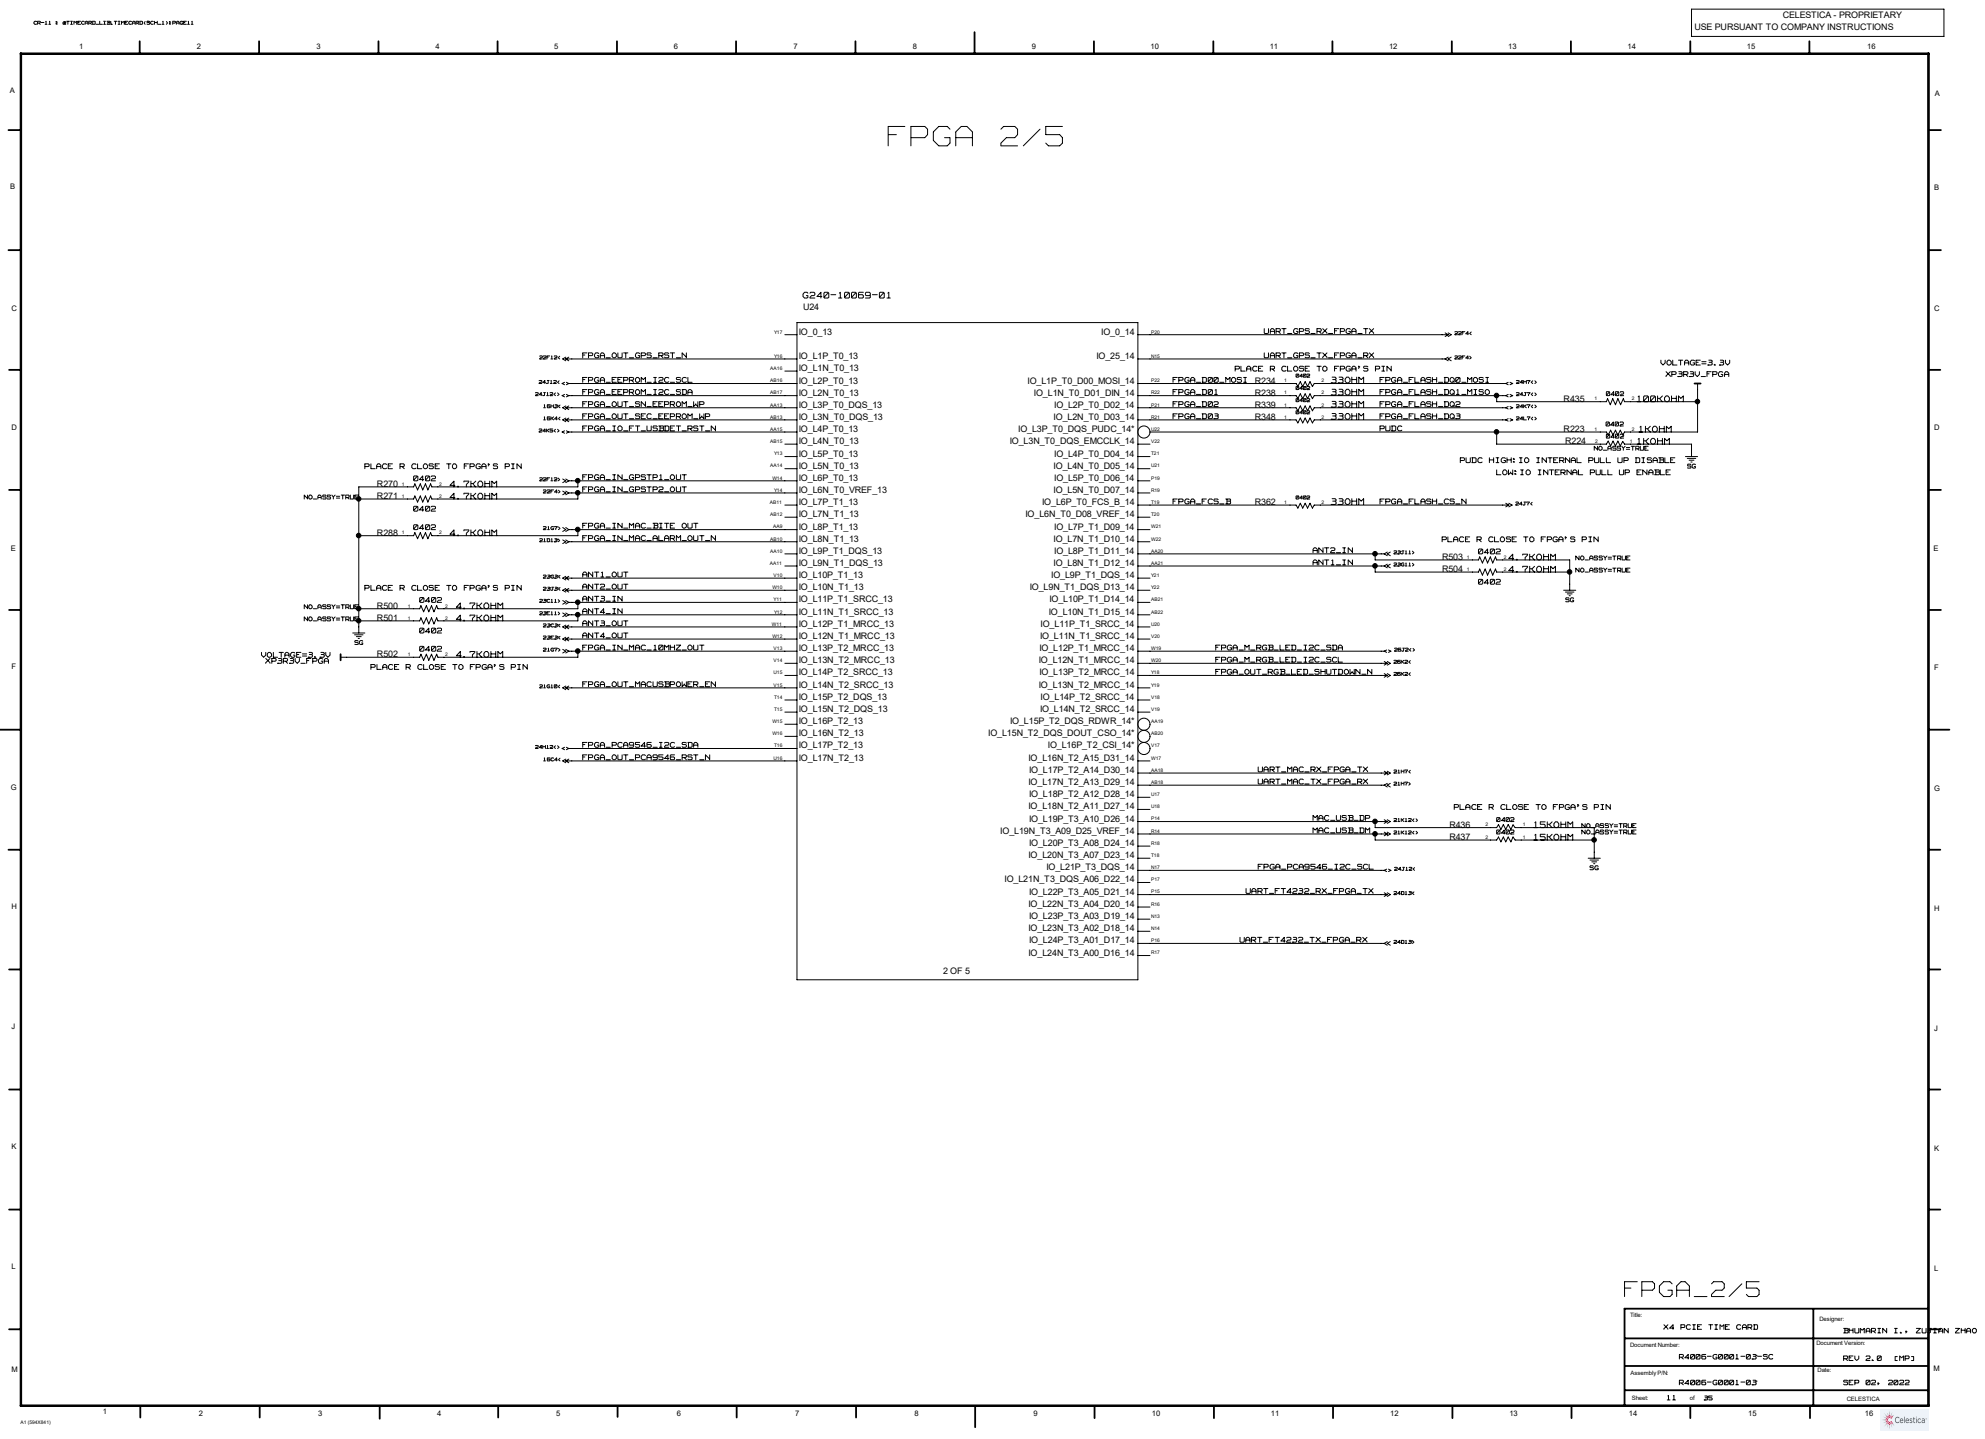
[picture p249: page 11]

PUDC HIGH:IO INTERNAL PULL UP DISABLE

LOW:IO INTERNAL PULL UP ENABLE

PLACE R CLOSE TO FPGA'S PIN

Title: | Designer:

Document Number: R4006-G0001-03-SC | Document Version:

# FPGA 3/5

G240-10069-01

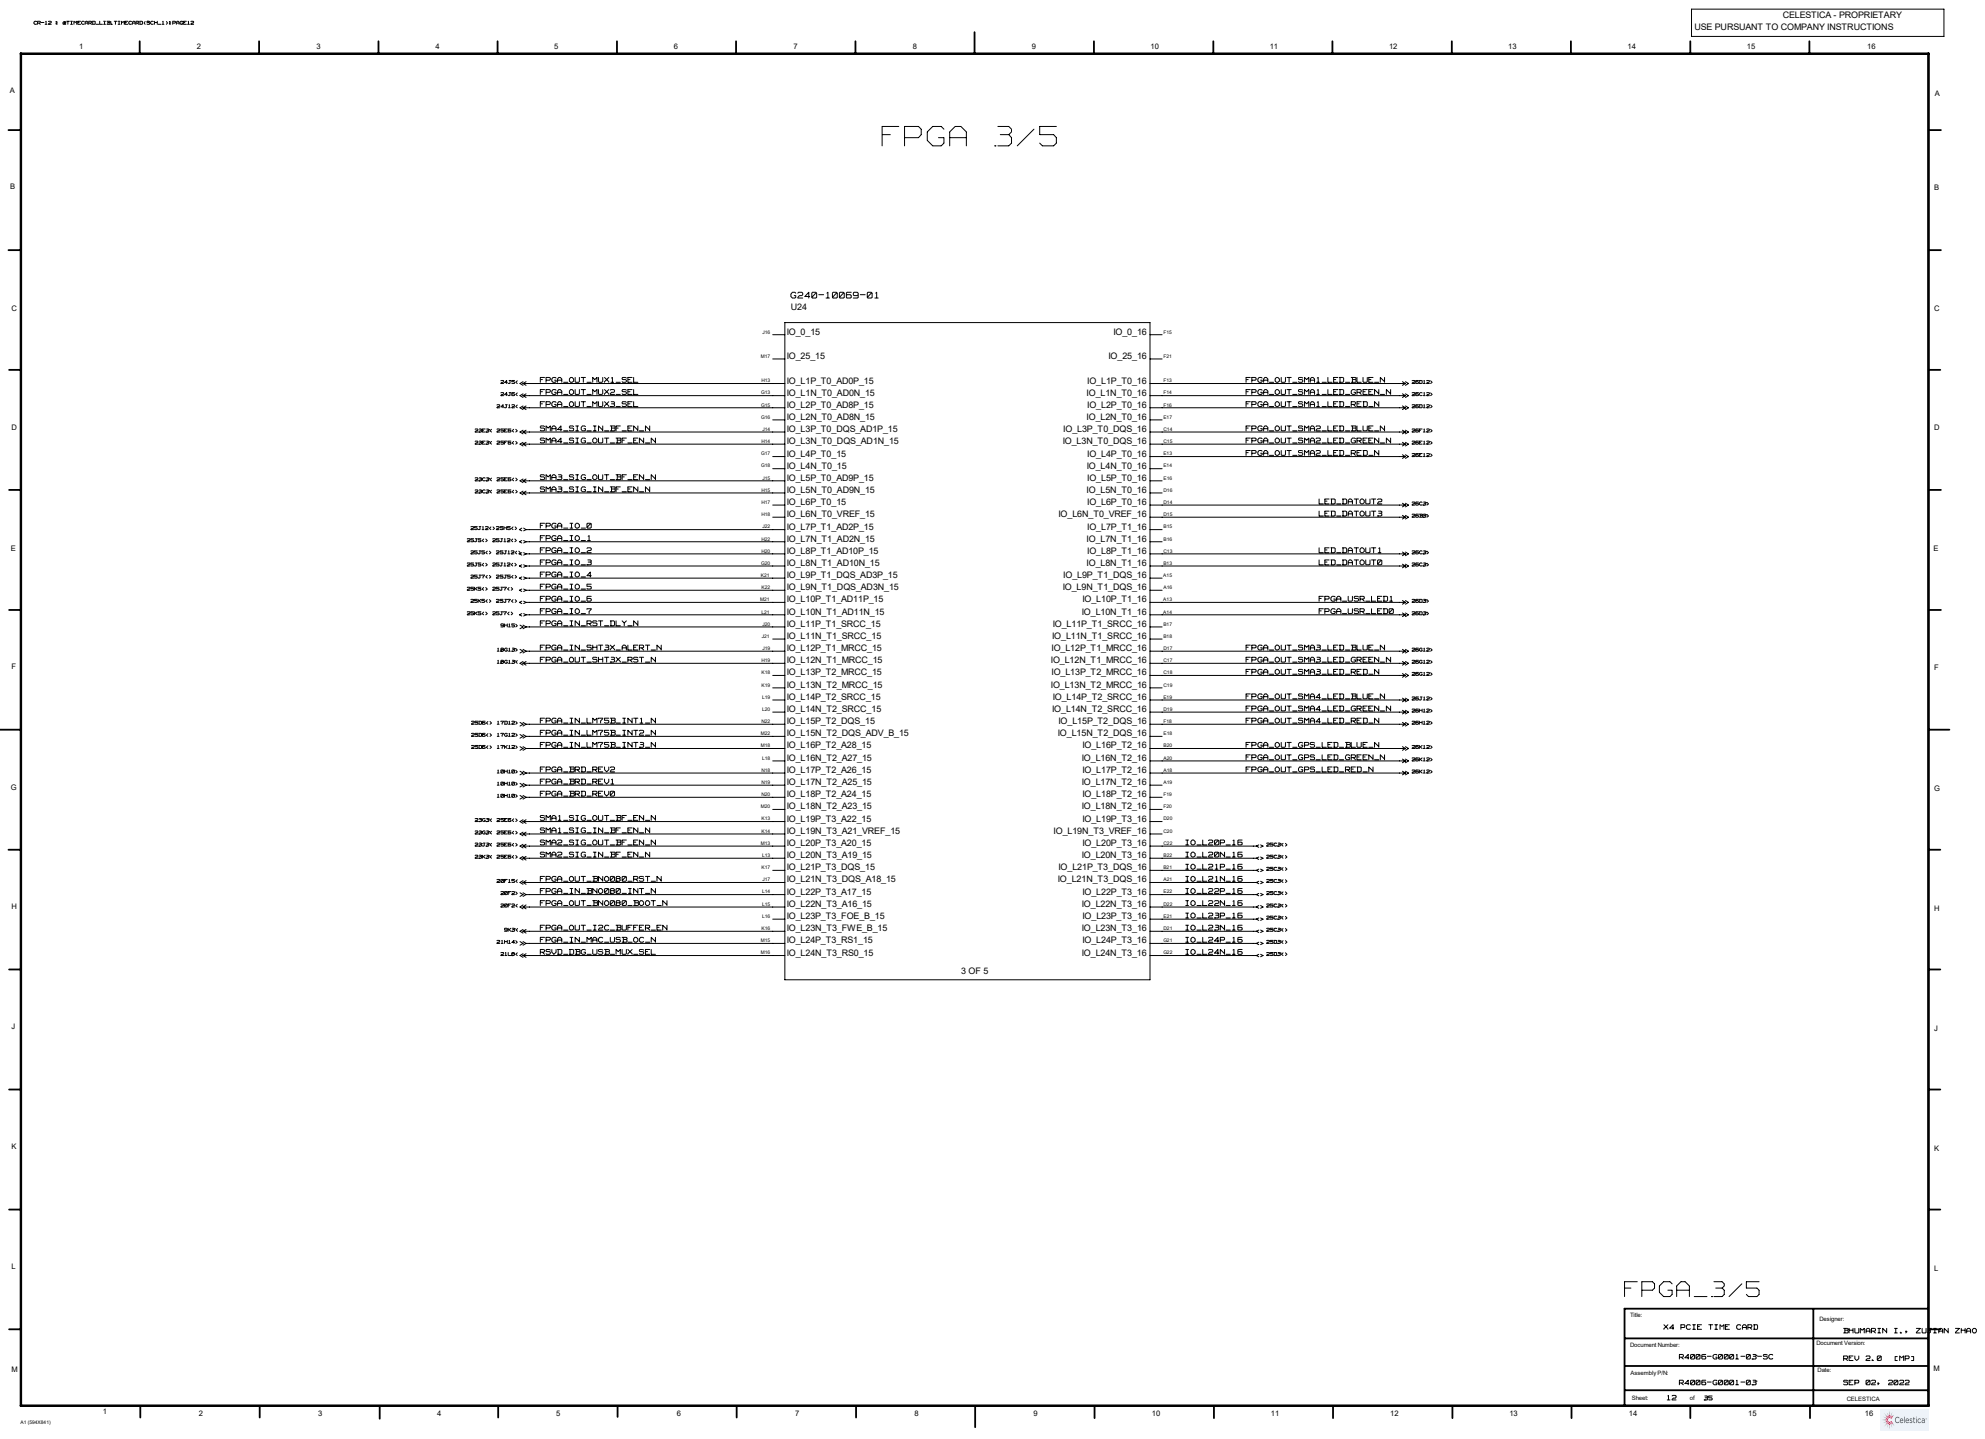
[picture p250: page 12]

Title: | Designer:

Document Number: R4006-G0001-03-SC | Document Version:

VCCIO = 2.5V.

# FPGA 4/5

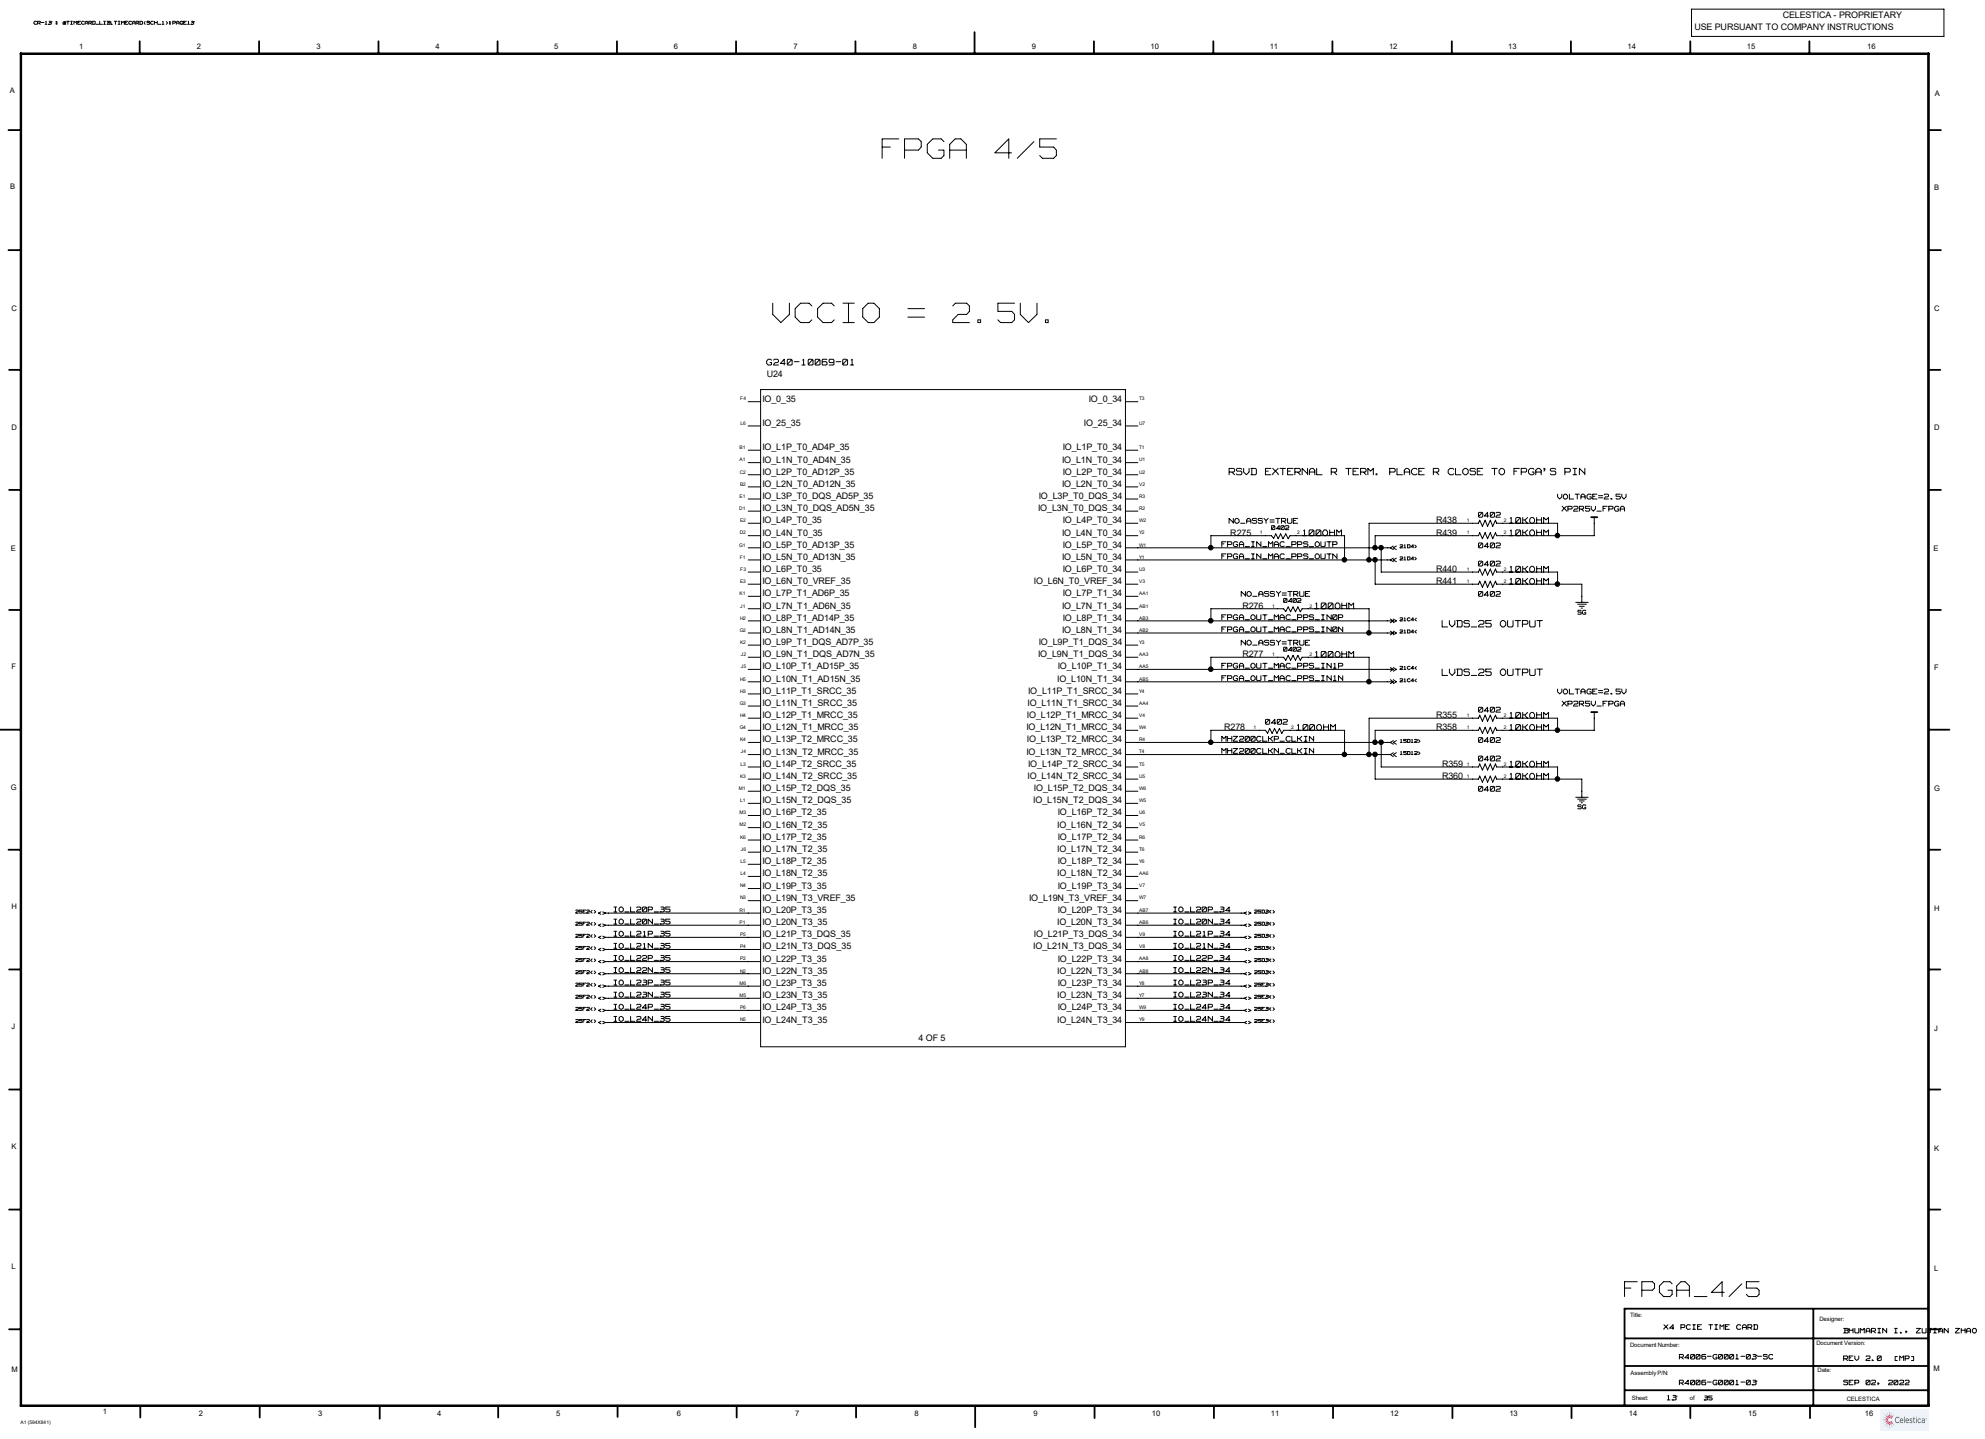
[picture p251: page 13]

RSVD EXTERNAL R TERM. PLACE R CLOSE TO FPGA'S PIN

Title: | Designer:

Document Number: R4006-G0001-03-SC | Document Version:

# FPGA 5/5

### 120OHM

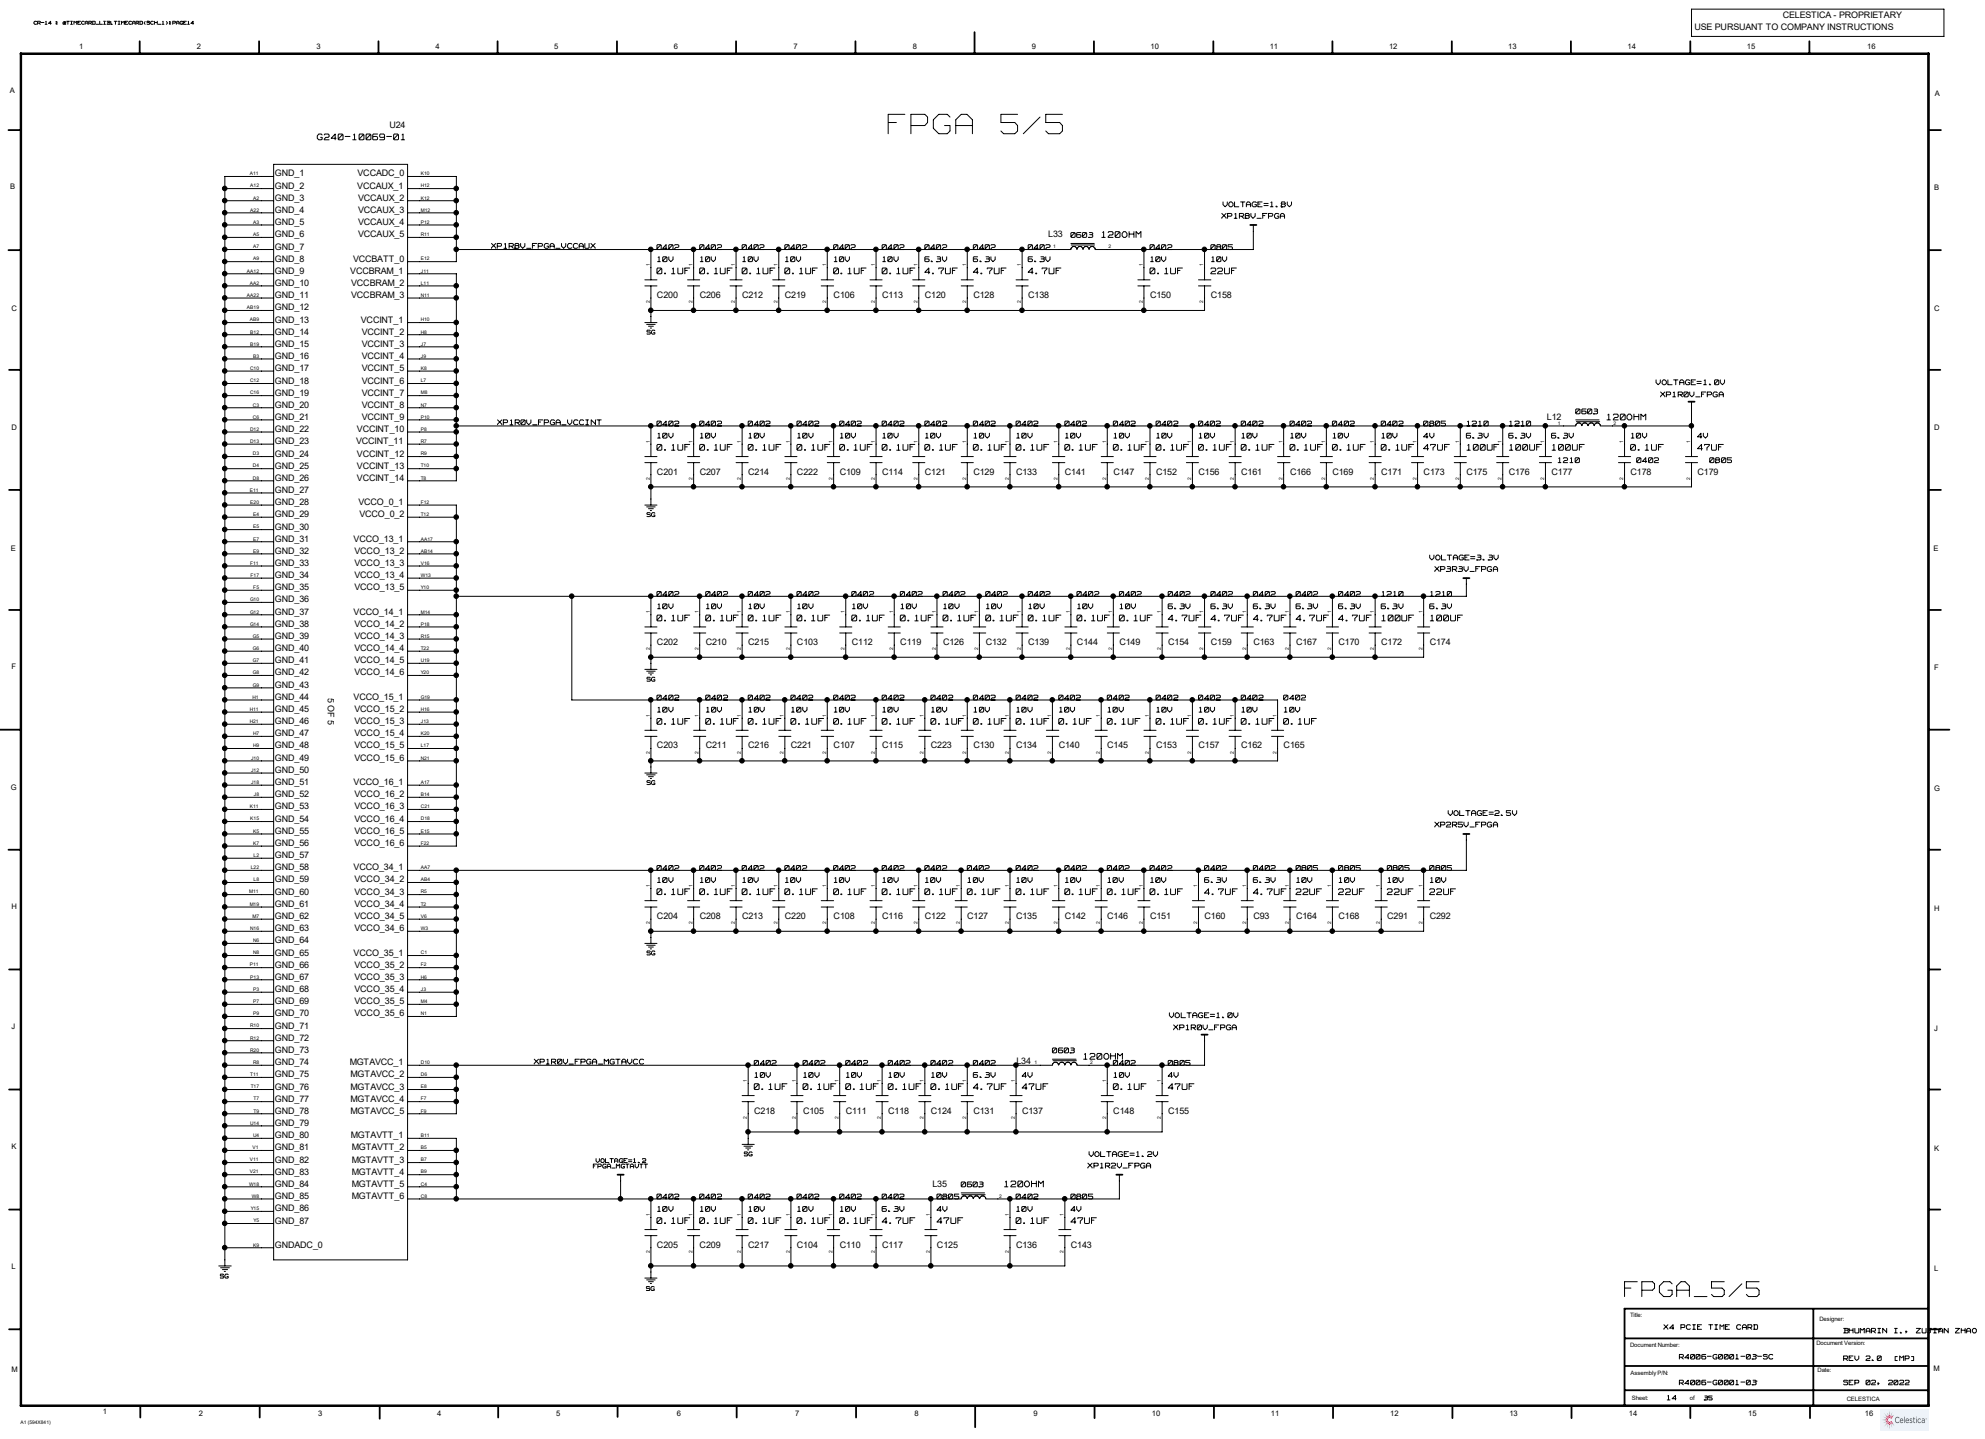
[picture p252: page 14]

Title: | Designer:

Document Number: R4006-G0001-03-SC | Document Version:

# CLOCK_GENERATOR

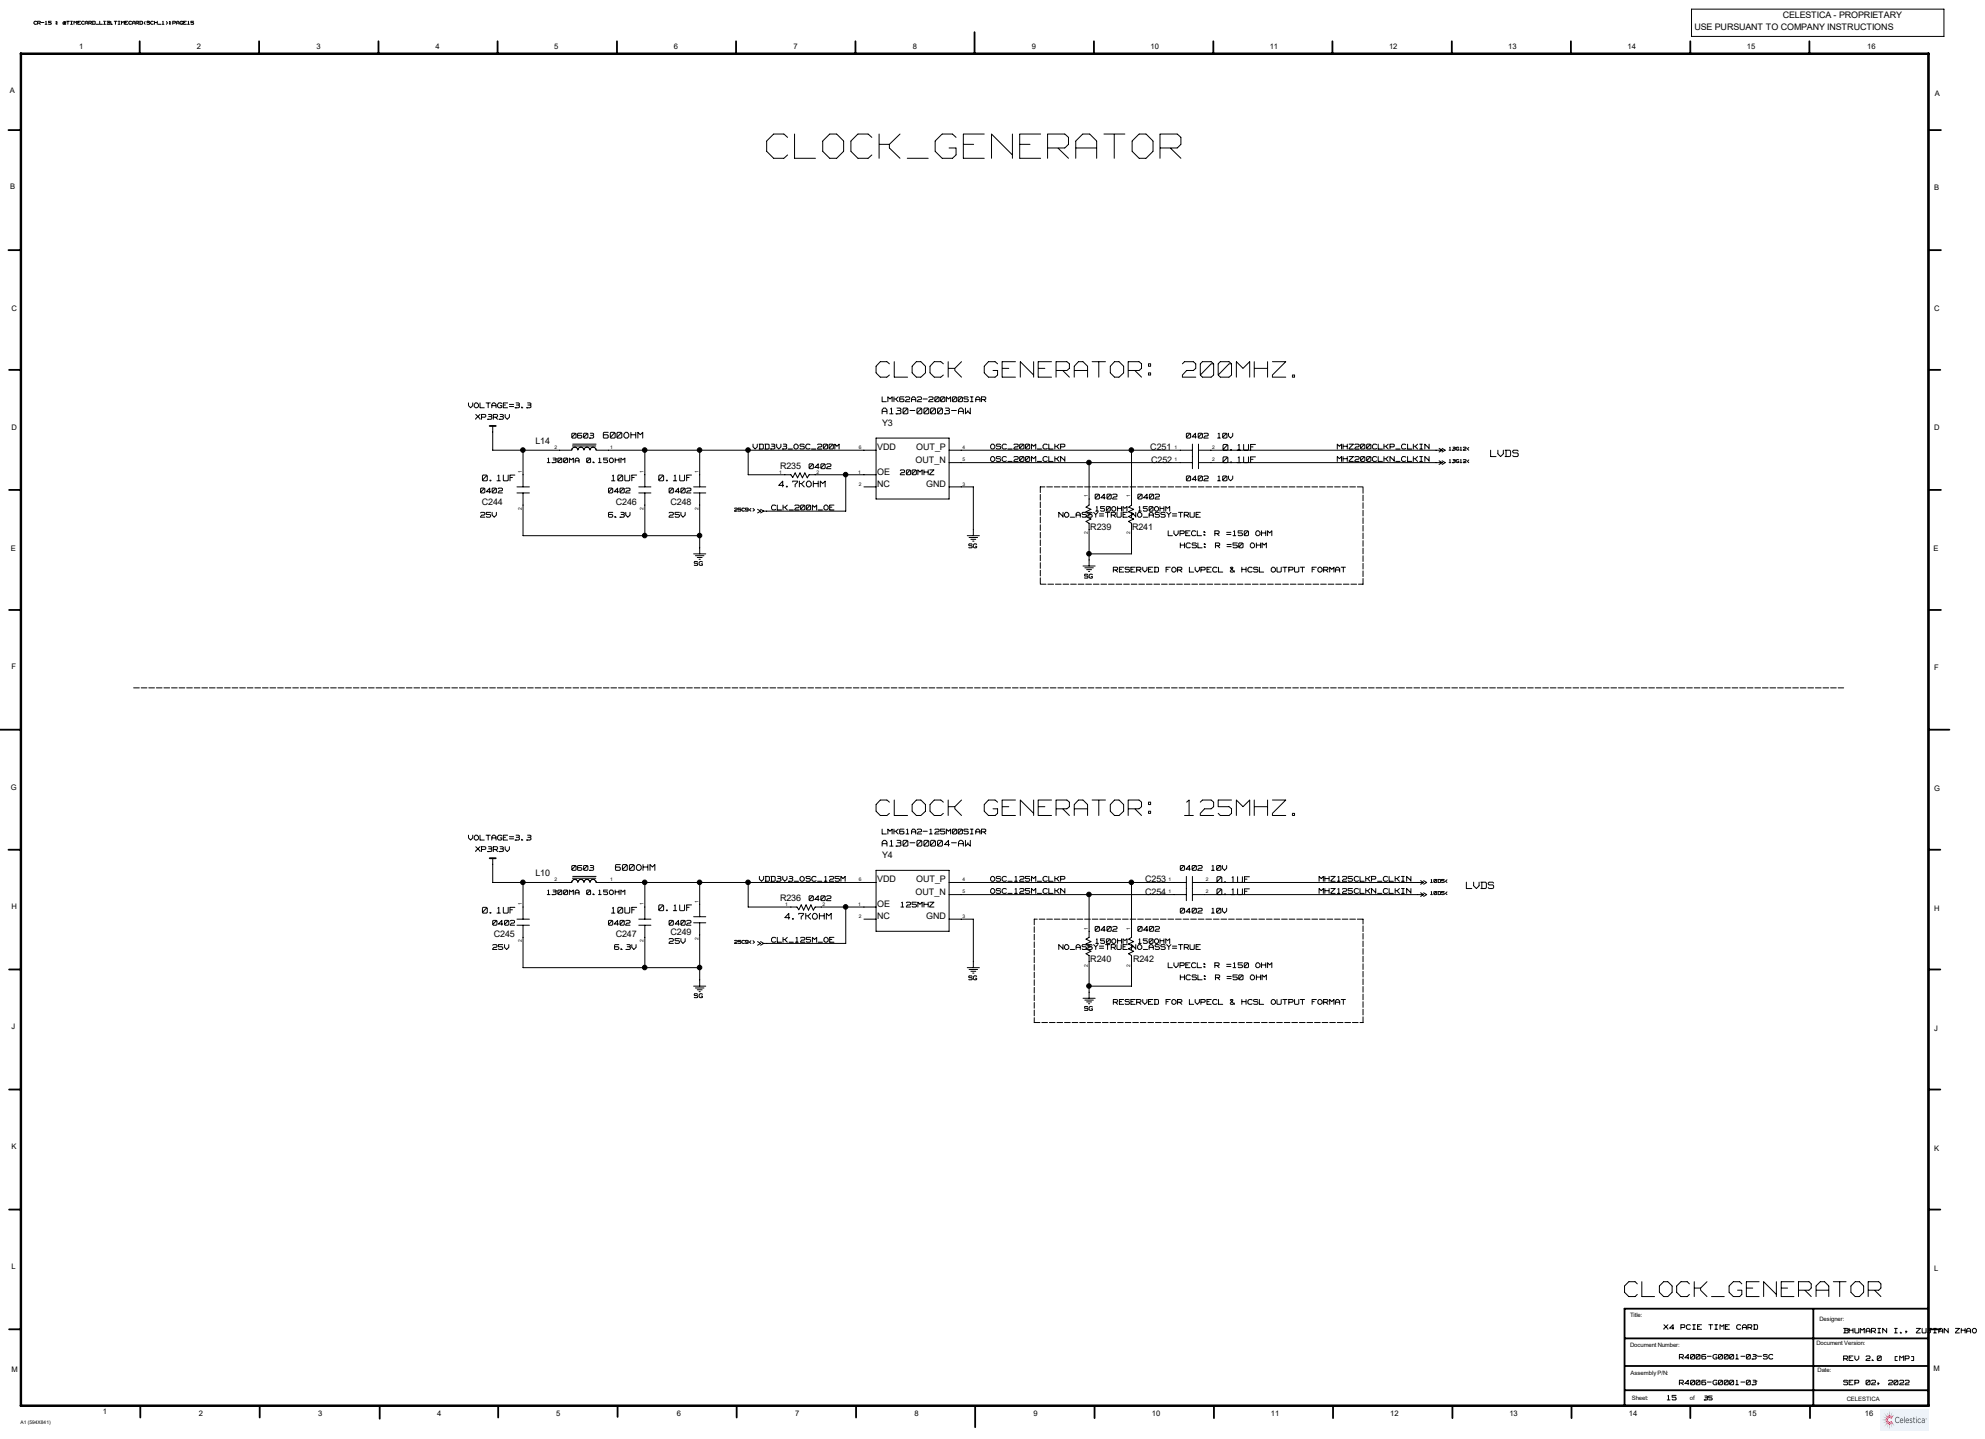
[picture p253: page 15]

RESERVED FOR LVPECL & HCSL OUTPUT FORMAT

Title: | Designer:

Document Number: R4006-G0001-03-SC | Document Version:

# PCA9546A_I2C_SWITCH

### 10KOHM

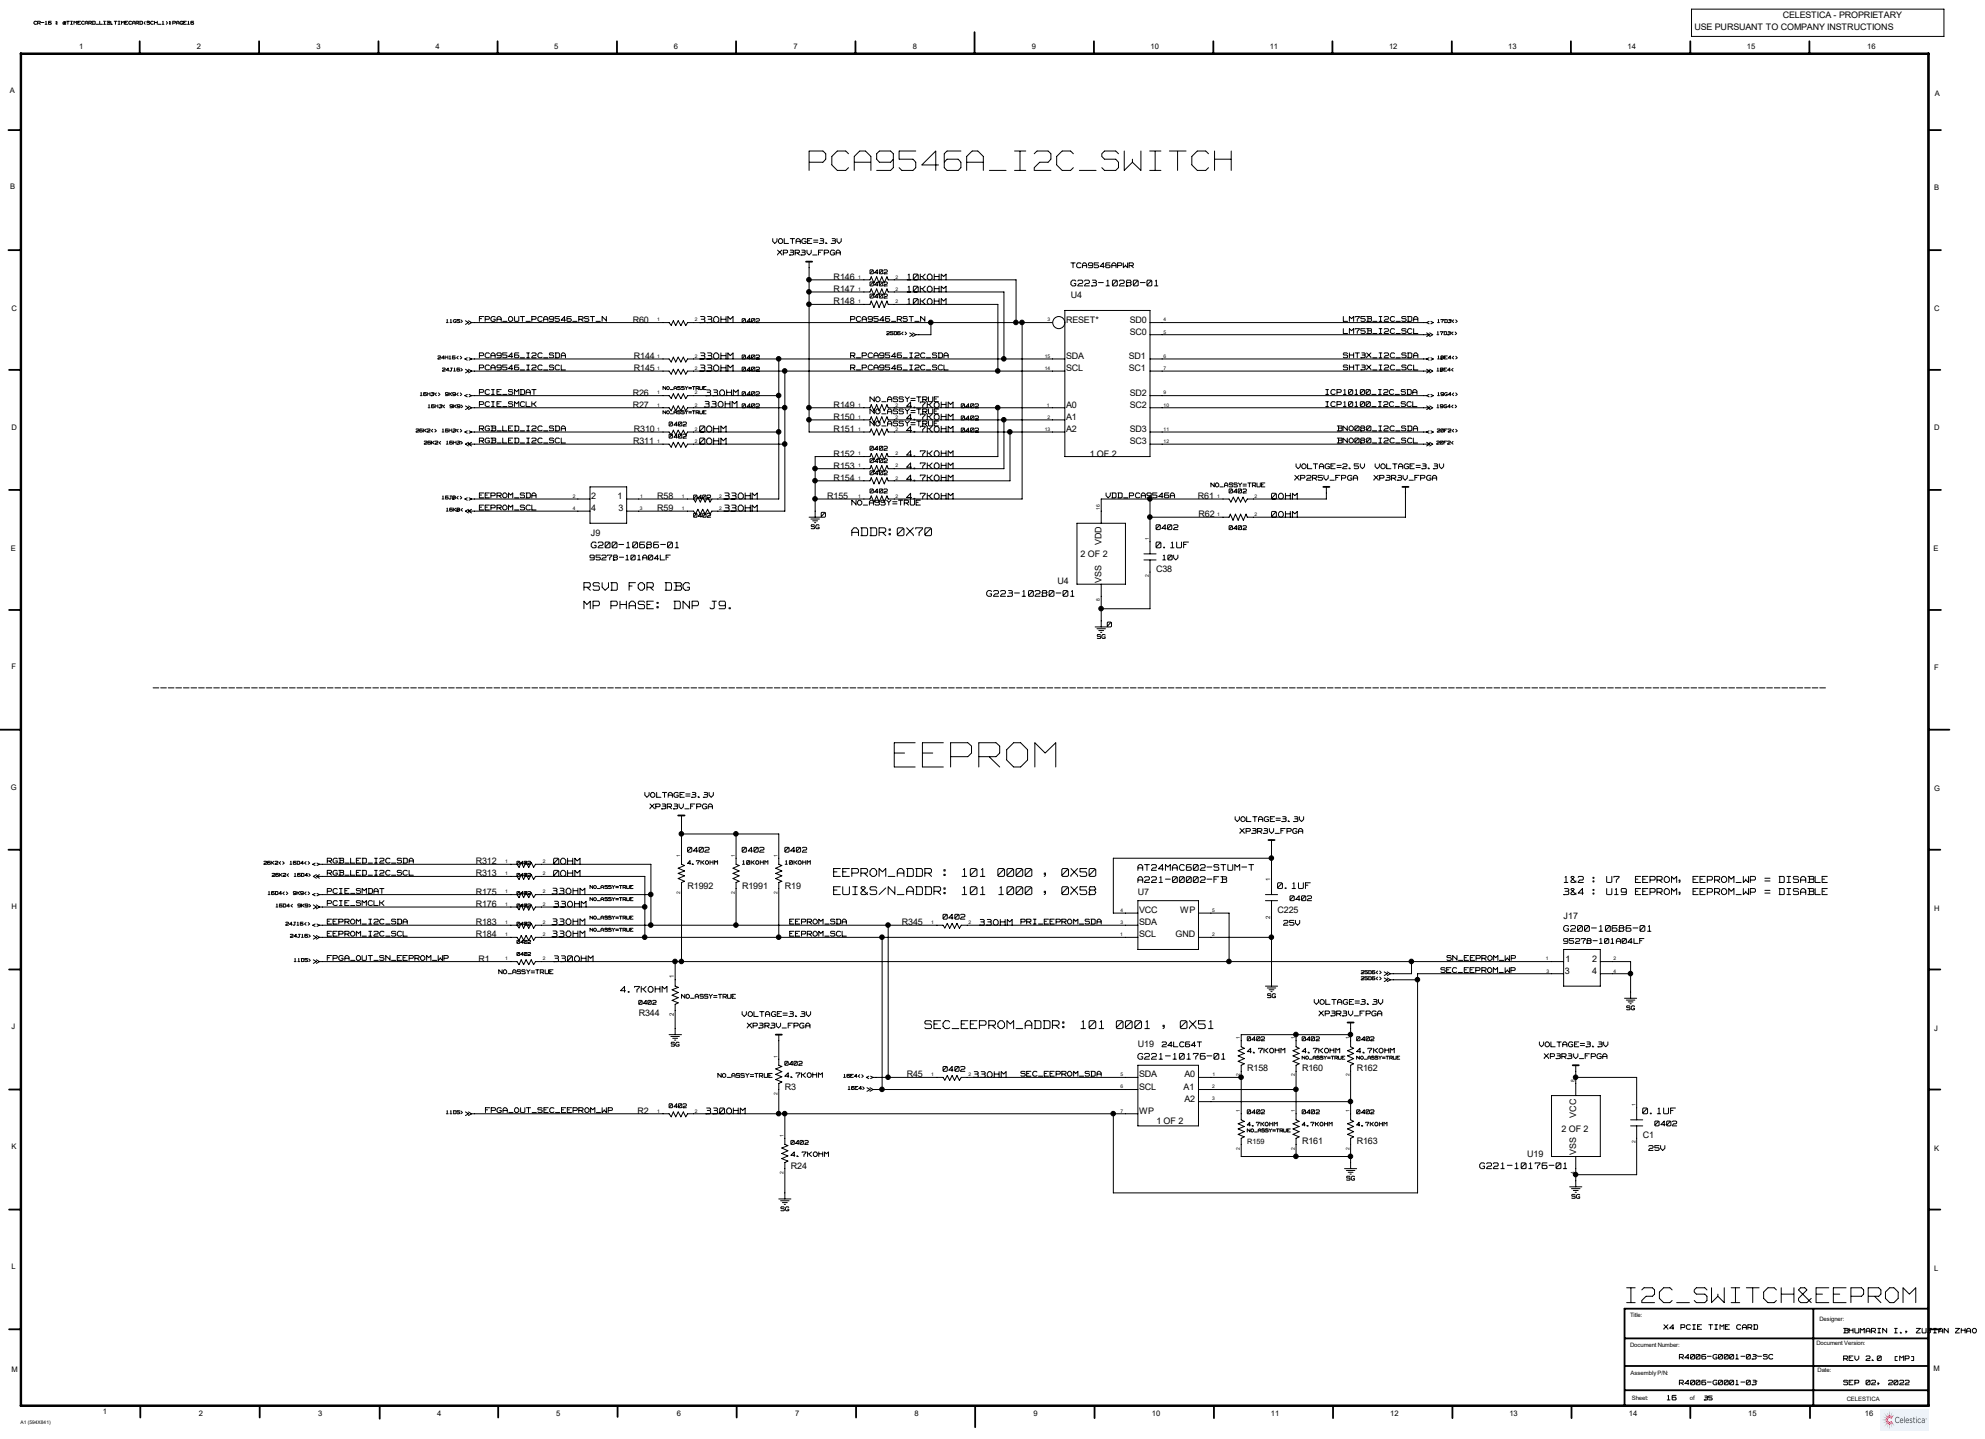
[picture p254: page 16]

Title: | Designer:

Document Number: R4006-G0001-03-SC | Document Version:

# TEMPERATURE_SENSOR

# LM75B_#1

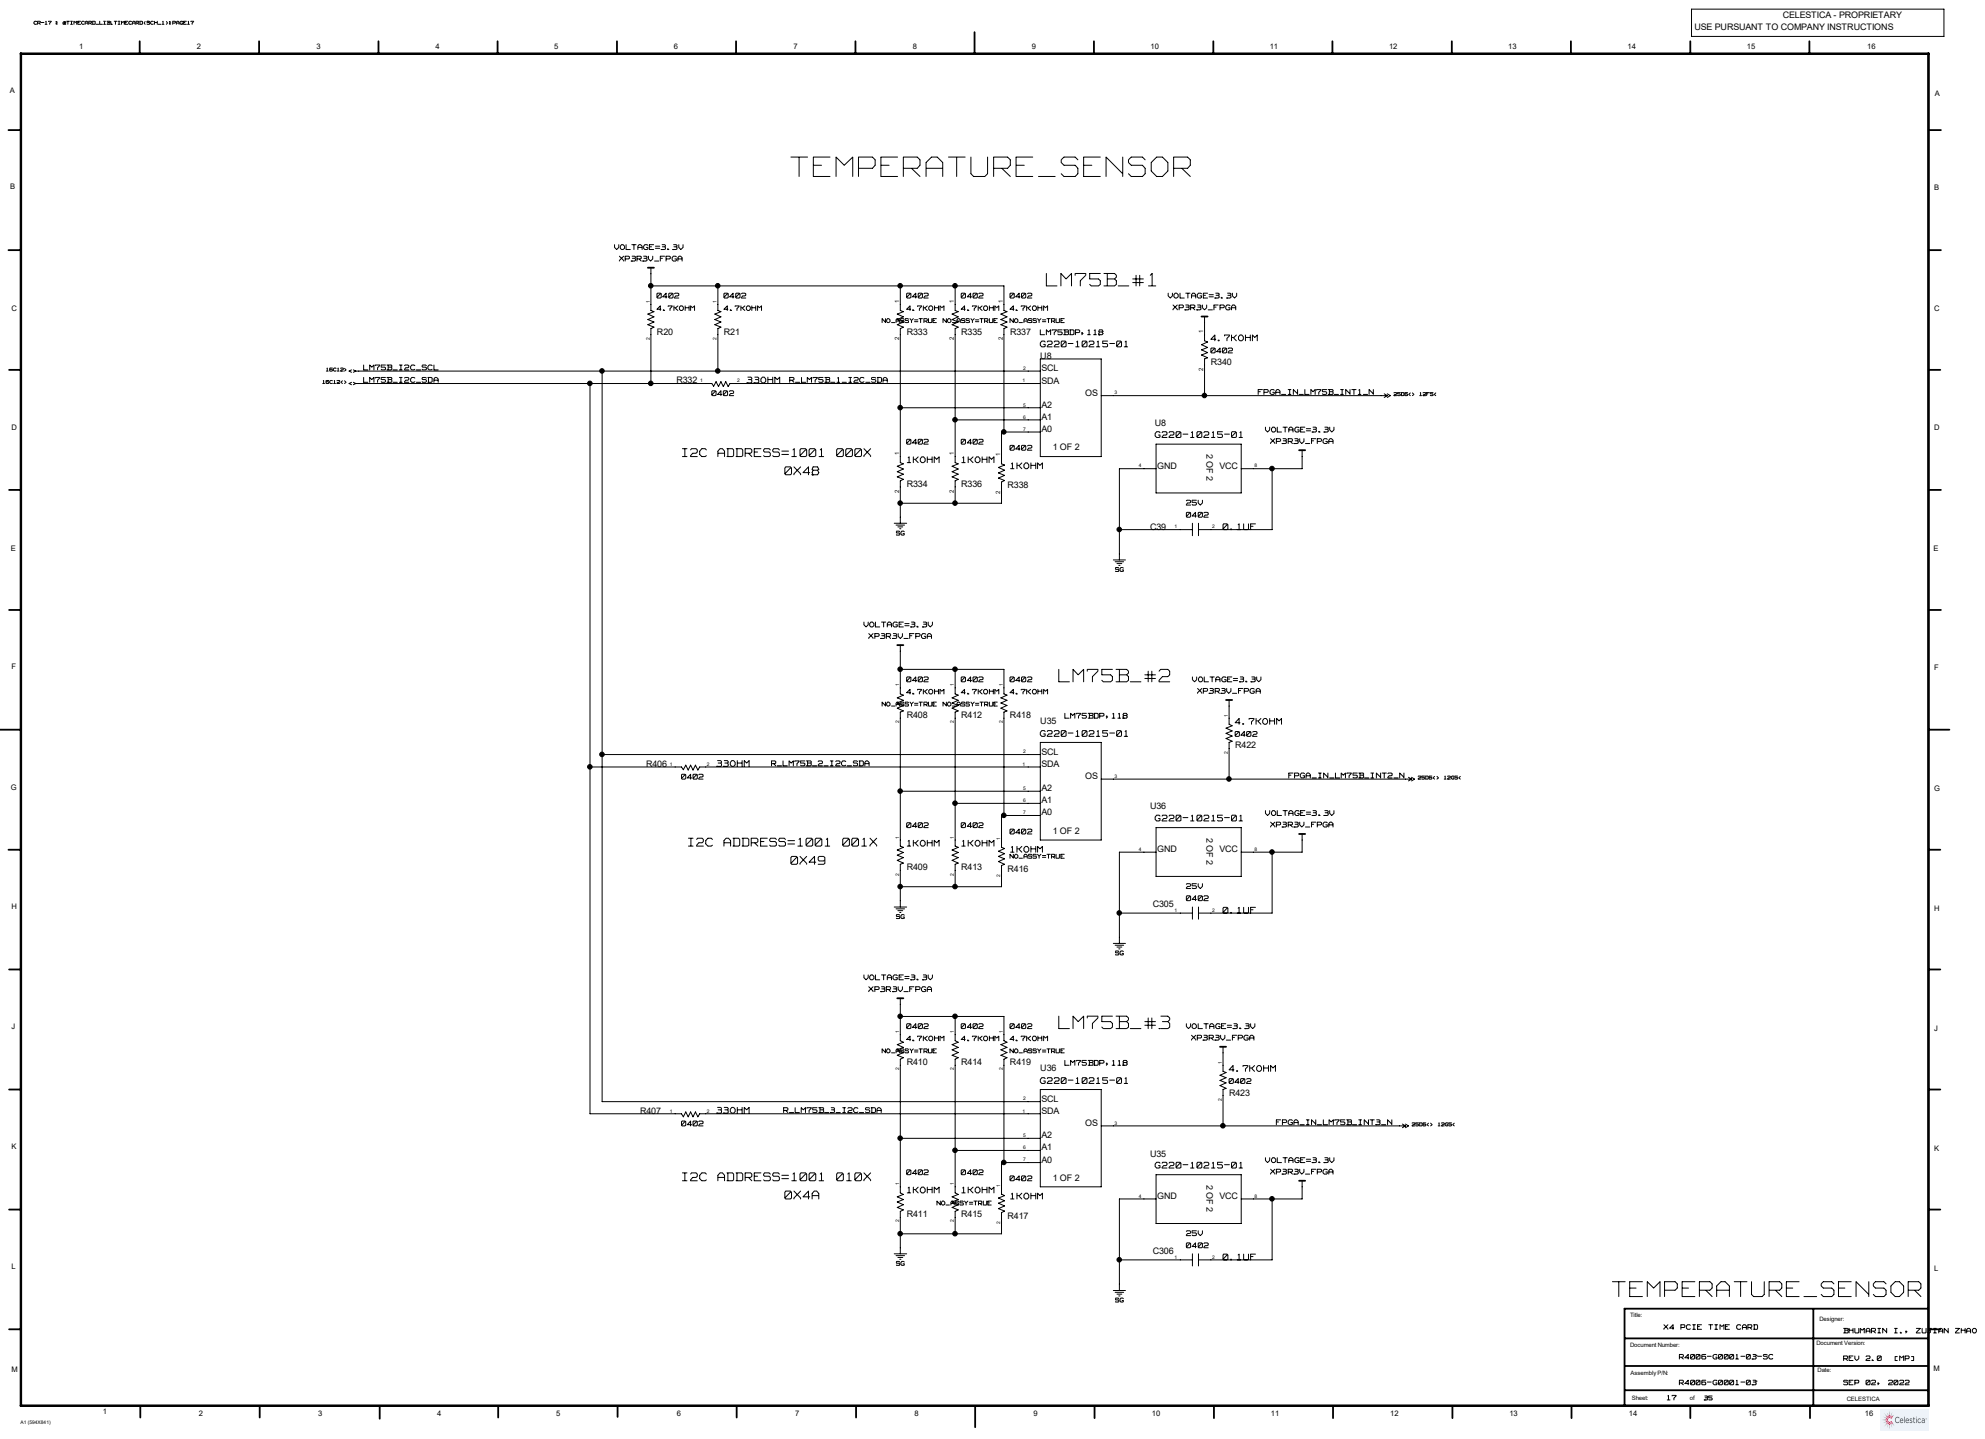
[picture p255: page 17]

Title: | Designer:

Document Number: R4006-G0001-03-SC | Document Version:

# HUMIDITY_SENSOR

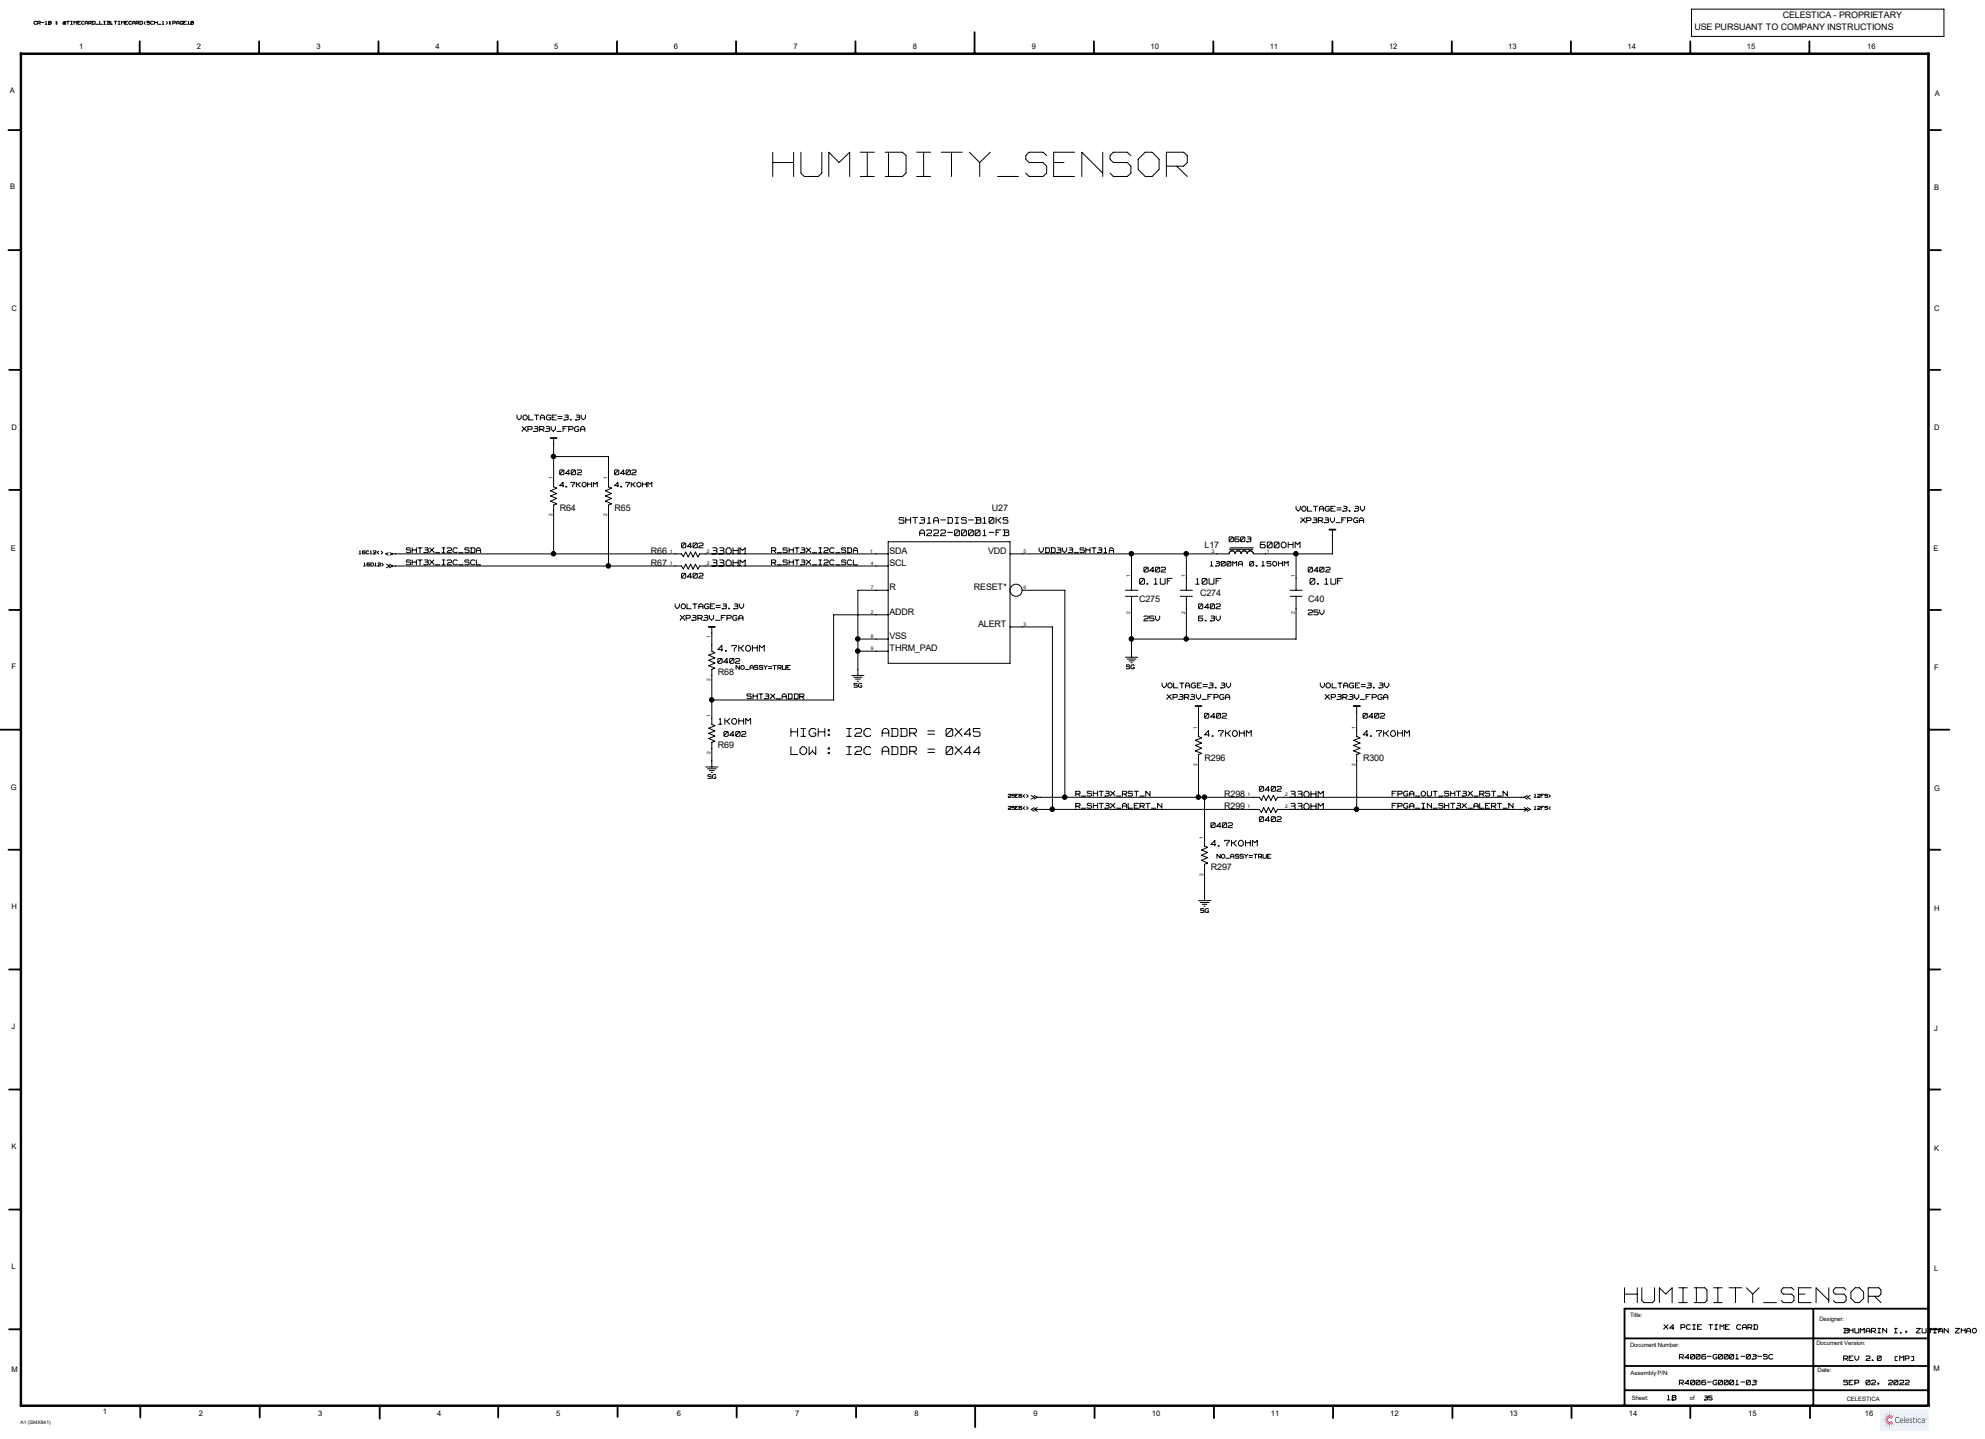
[picture p256: page 18]

Title: | Designer:

Document Number: R4006-G0001-03-SC | Document Version:

# AIR_PRESSURE_SENSOR

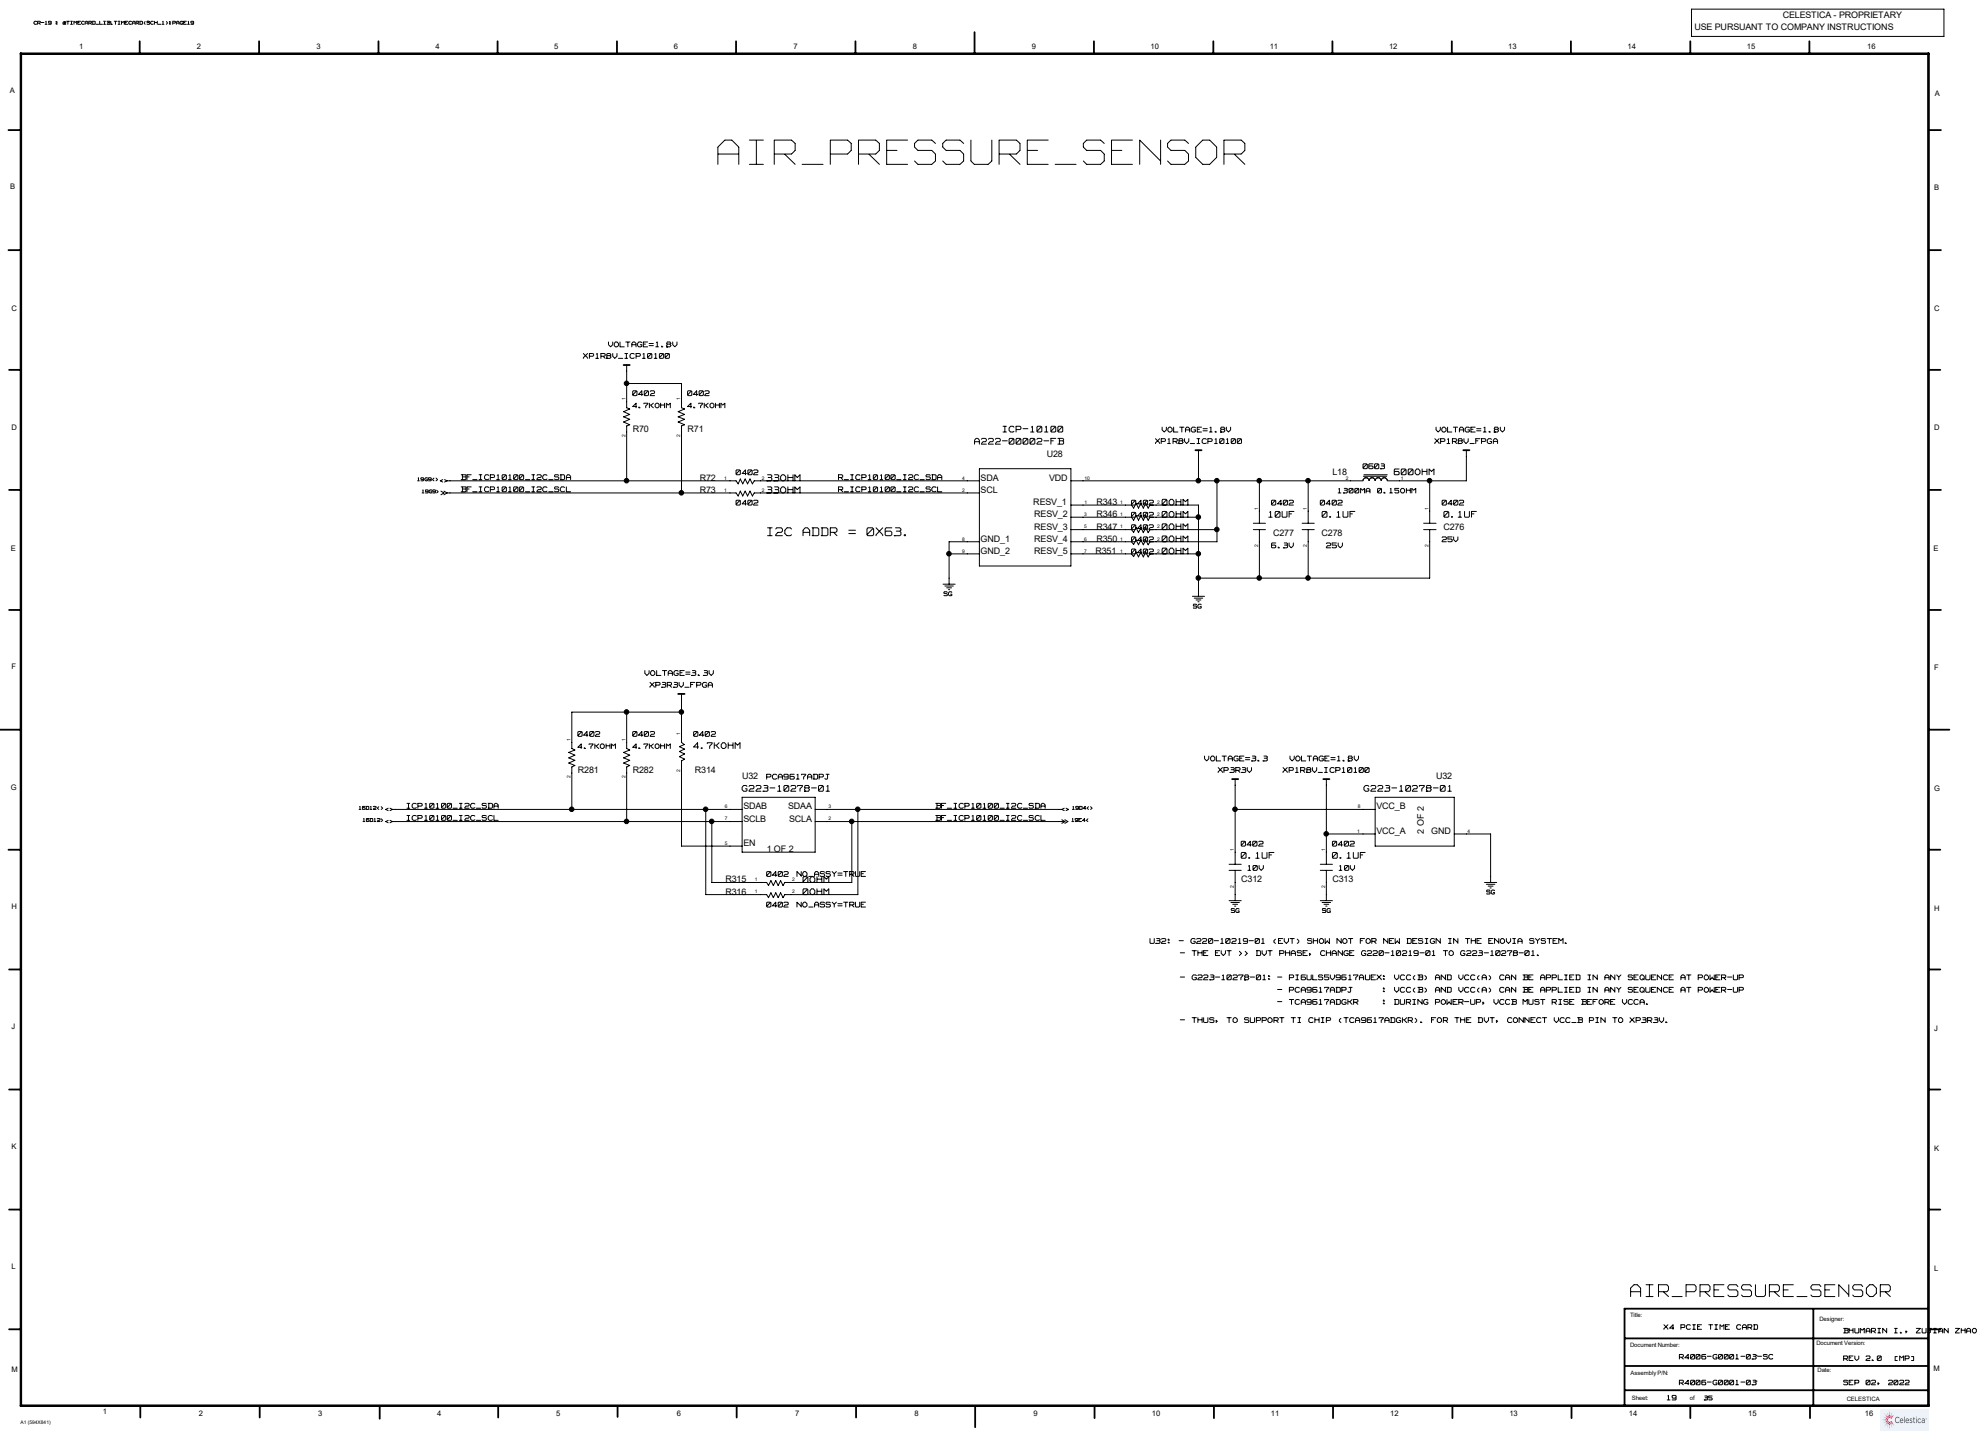
[picture p257: page 19]

U32: - G220-10219-01 (EVT) SHOW NOT FOR NEW DESIGN IN THE ENOVIA SYSTEM.
- THE EVT >> DVT PHASE, CHANGE G220-10219-01 TO G223-10278-01.

- PI6ULS5V9617AUEX: VCC(B) AND VCC(A) CAN BE APPLIED IN ANY SEQUENCE AT POWER-UP

- THUS, TO SUPPORT TI CHIP (TCA9617ADGKR). FOR THE DVT, CONNECT VCC_B PIN TO XP3R3V.

Title: | Designer:

Document Number: R4006-G0001-03-SC | Document Version:

# VIBRATION_SENSOR

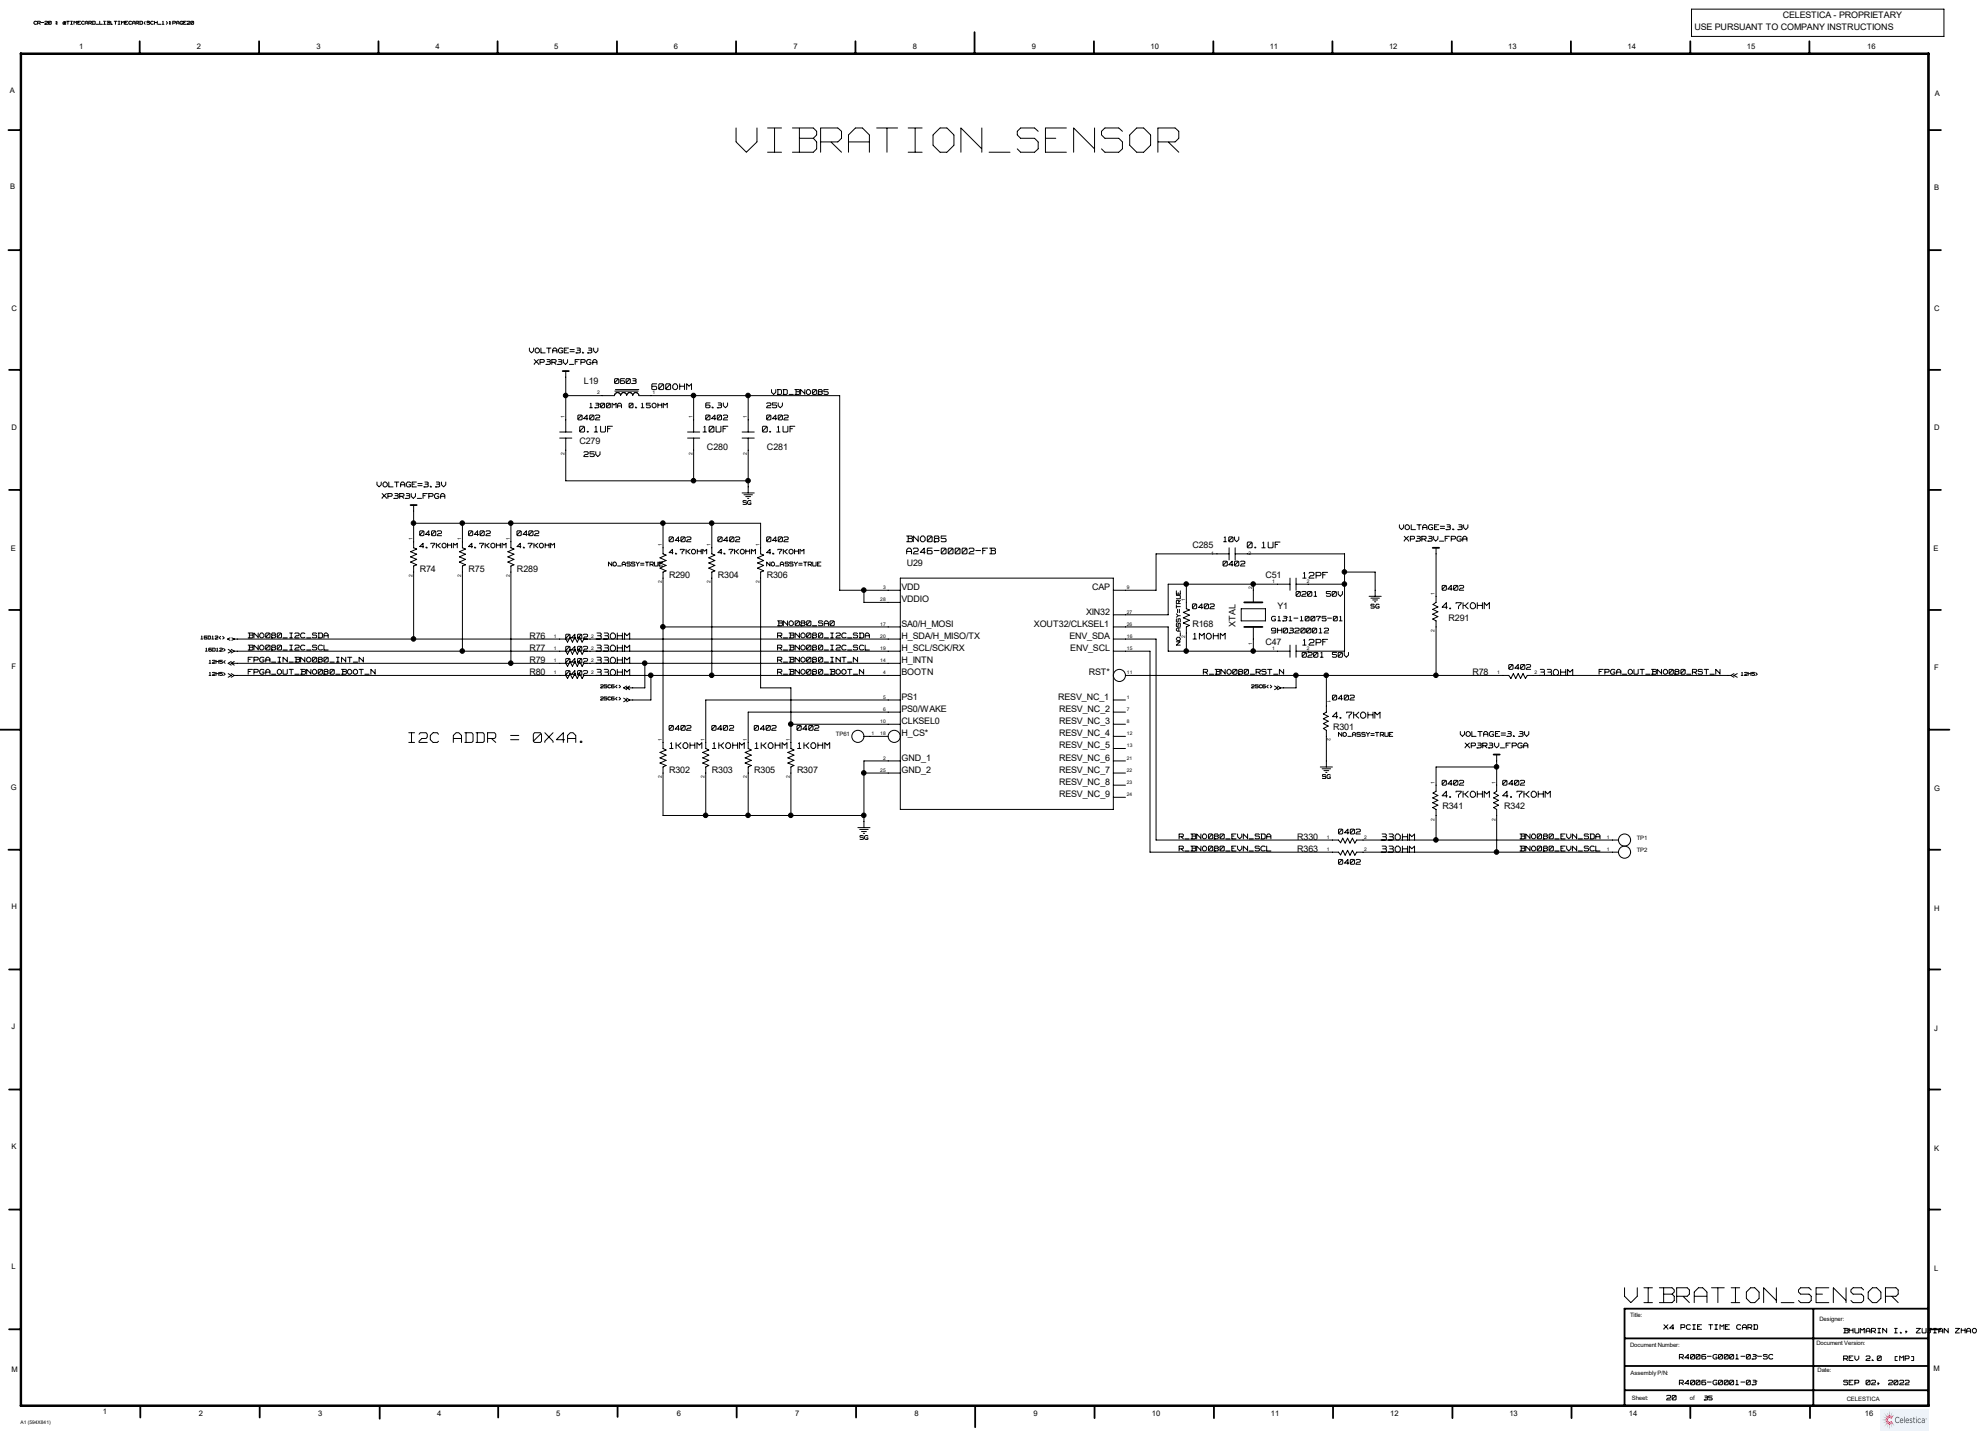
[picture p258: page 20]

Title: | Designer:

Document Number: R4006-G0001-03-SC | Document Version:

# MINIATURE_ATOMIC_CLOCK_MODULE

### 0OHM

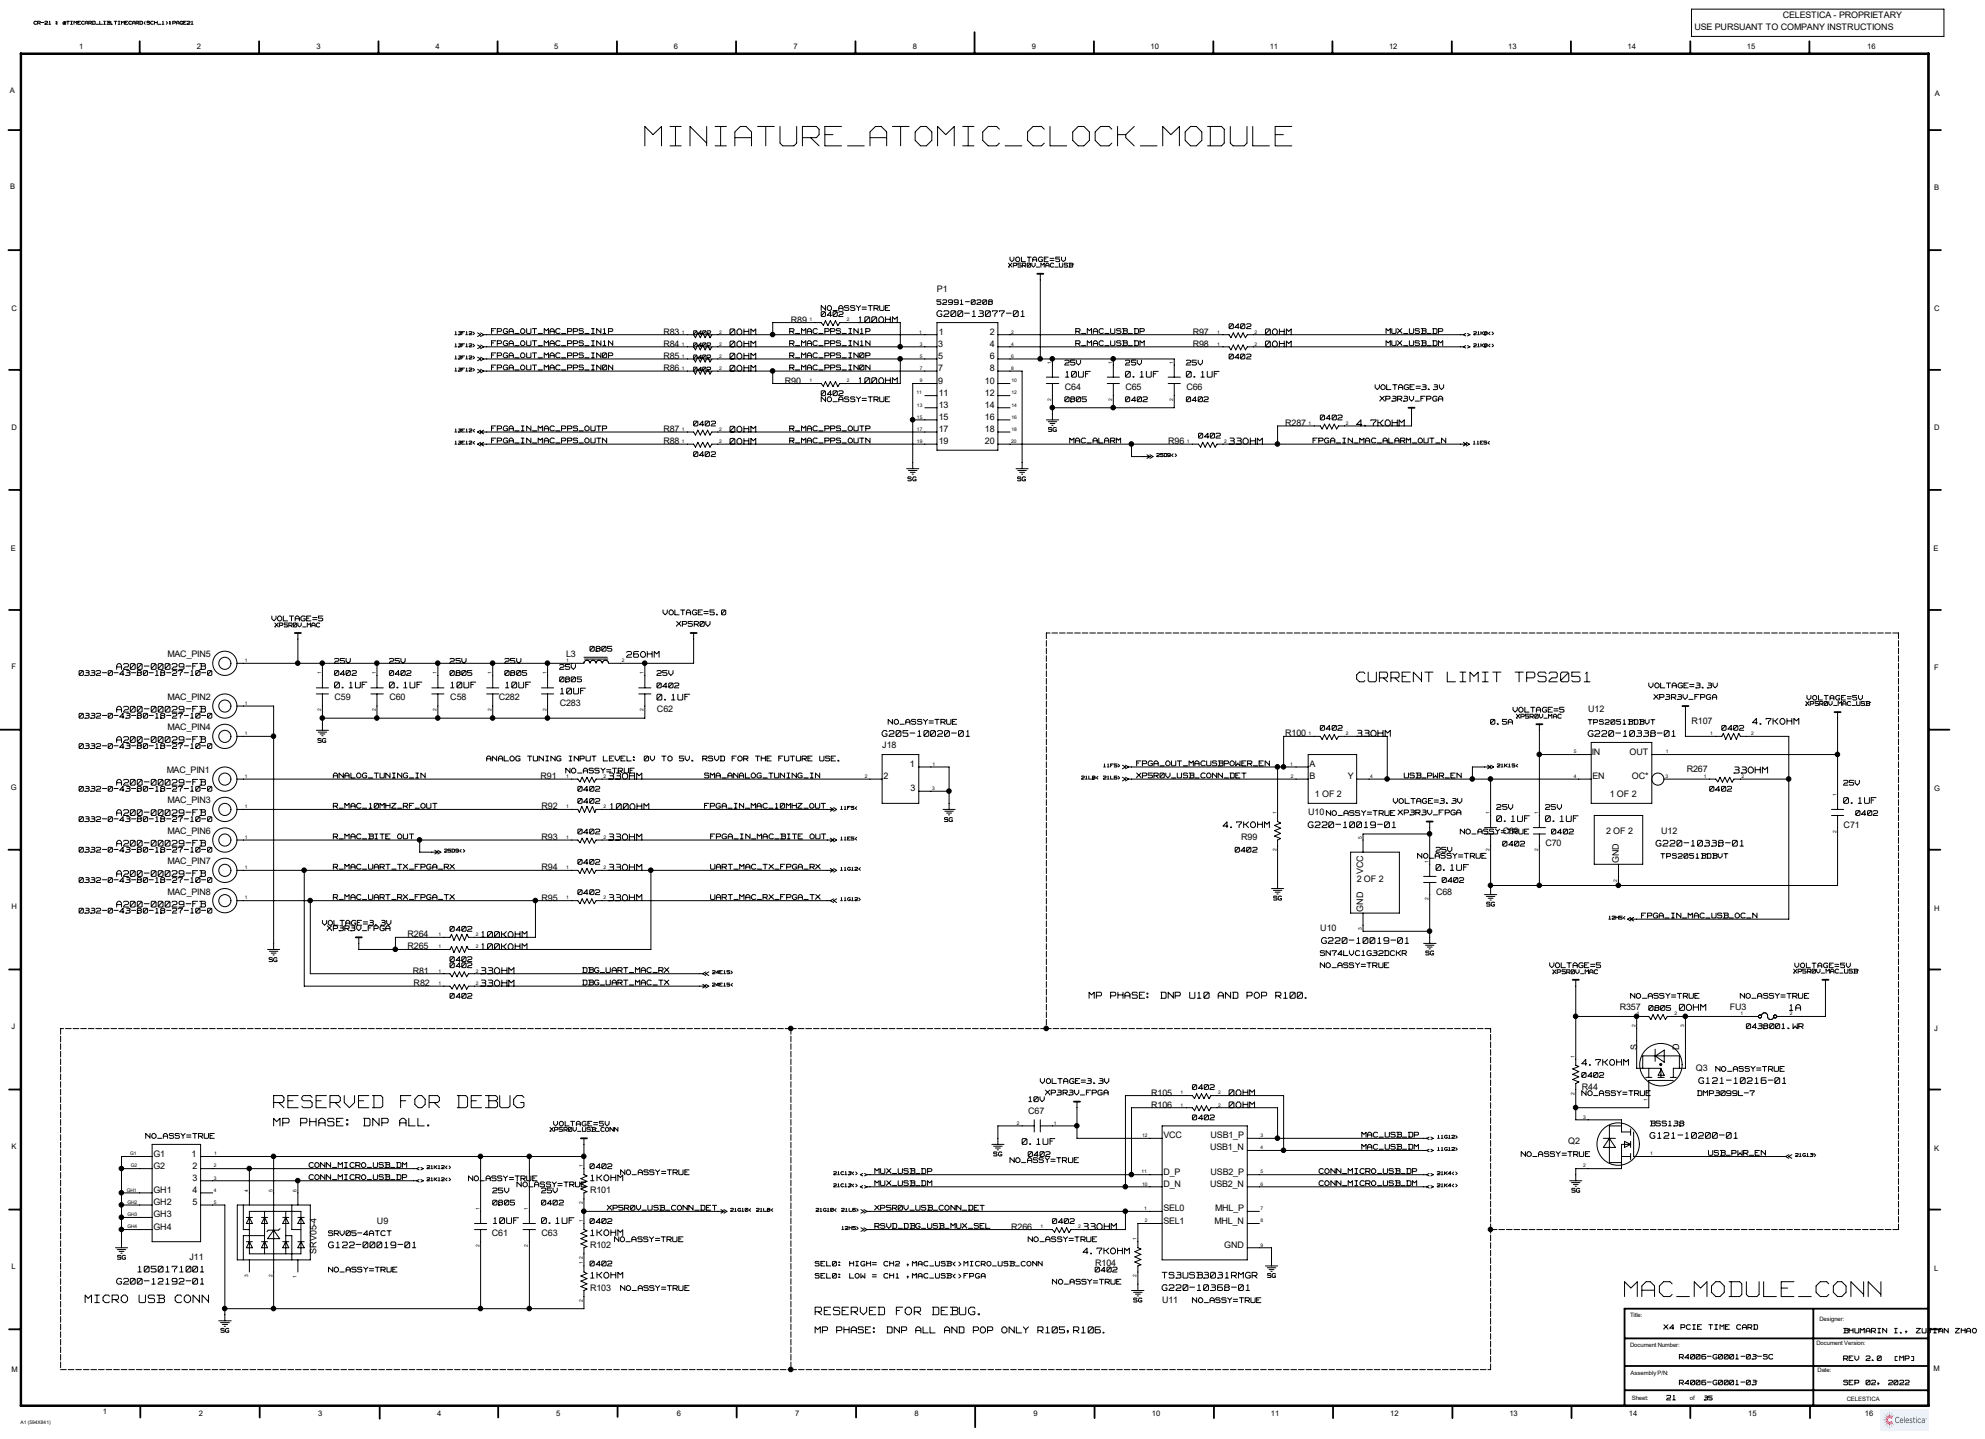
[picture p259: page 21]

ANALOG TUNING INPUT LEVEL: 0V TO 5V. RSVD FOR THE FUTURE USE.

MP PHASE: DNP U10 AND POP R100.

RESERVED FOR DEBUG
MP PHASE: DNP ALL.

RESERVED FOR DEBUG.
MP PHASE: DNP ALL AND POP ONLY R105,R106.

Title: | Designer:

Document Number: R4006-G0001-03-SC | Document Version:

# GPS_MODULE_CONN

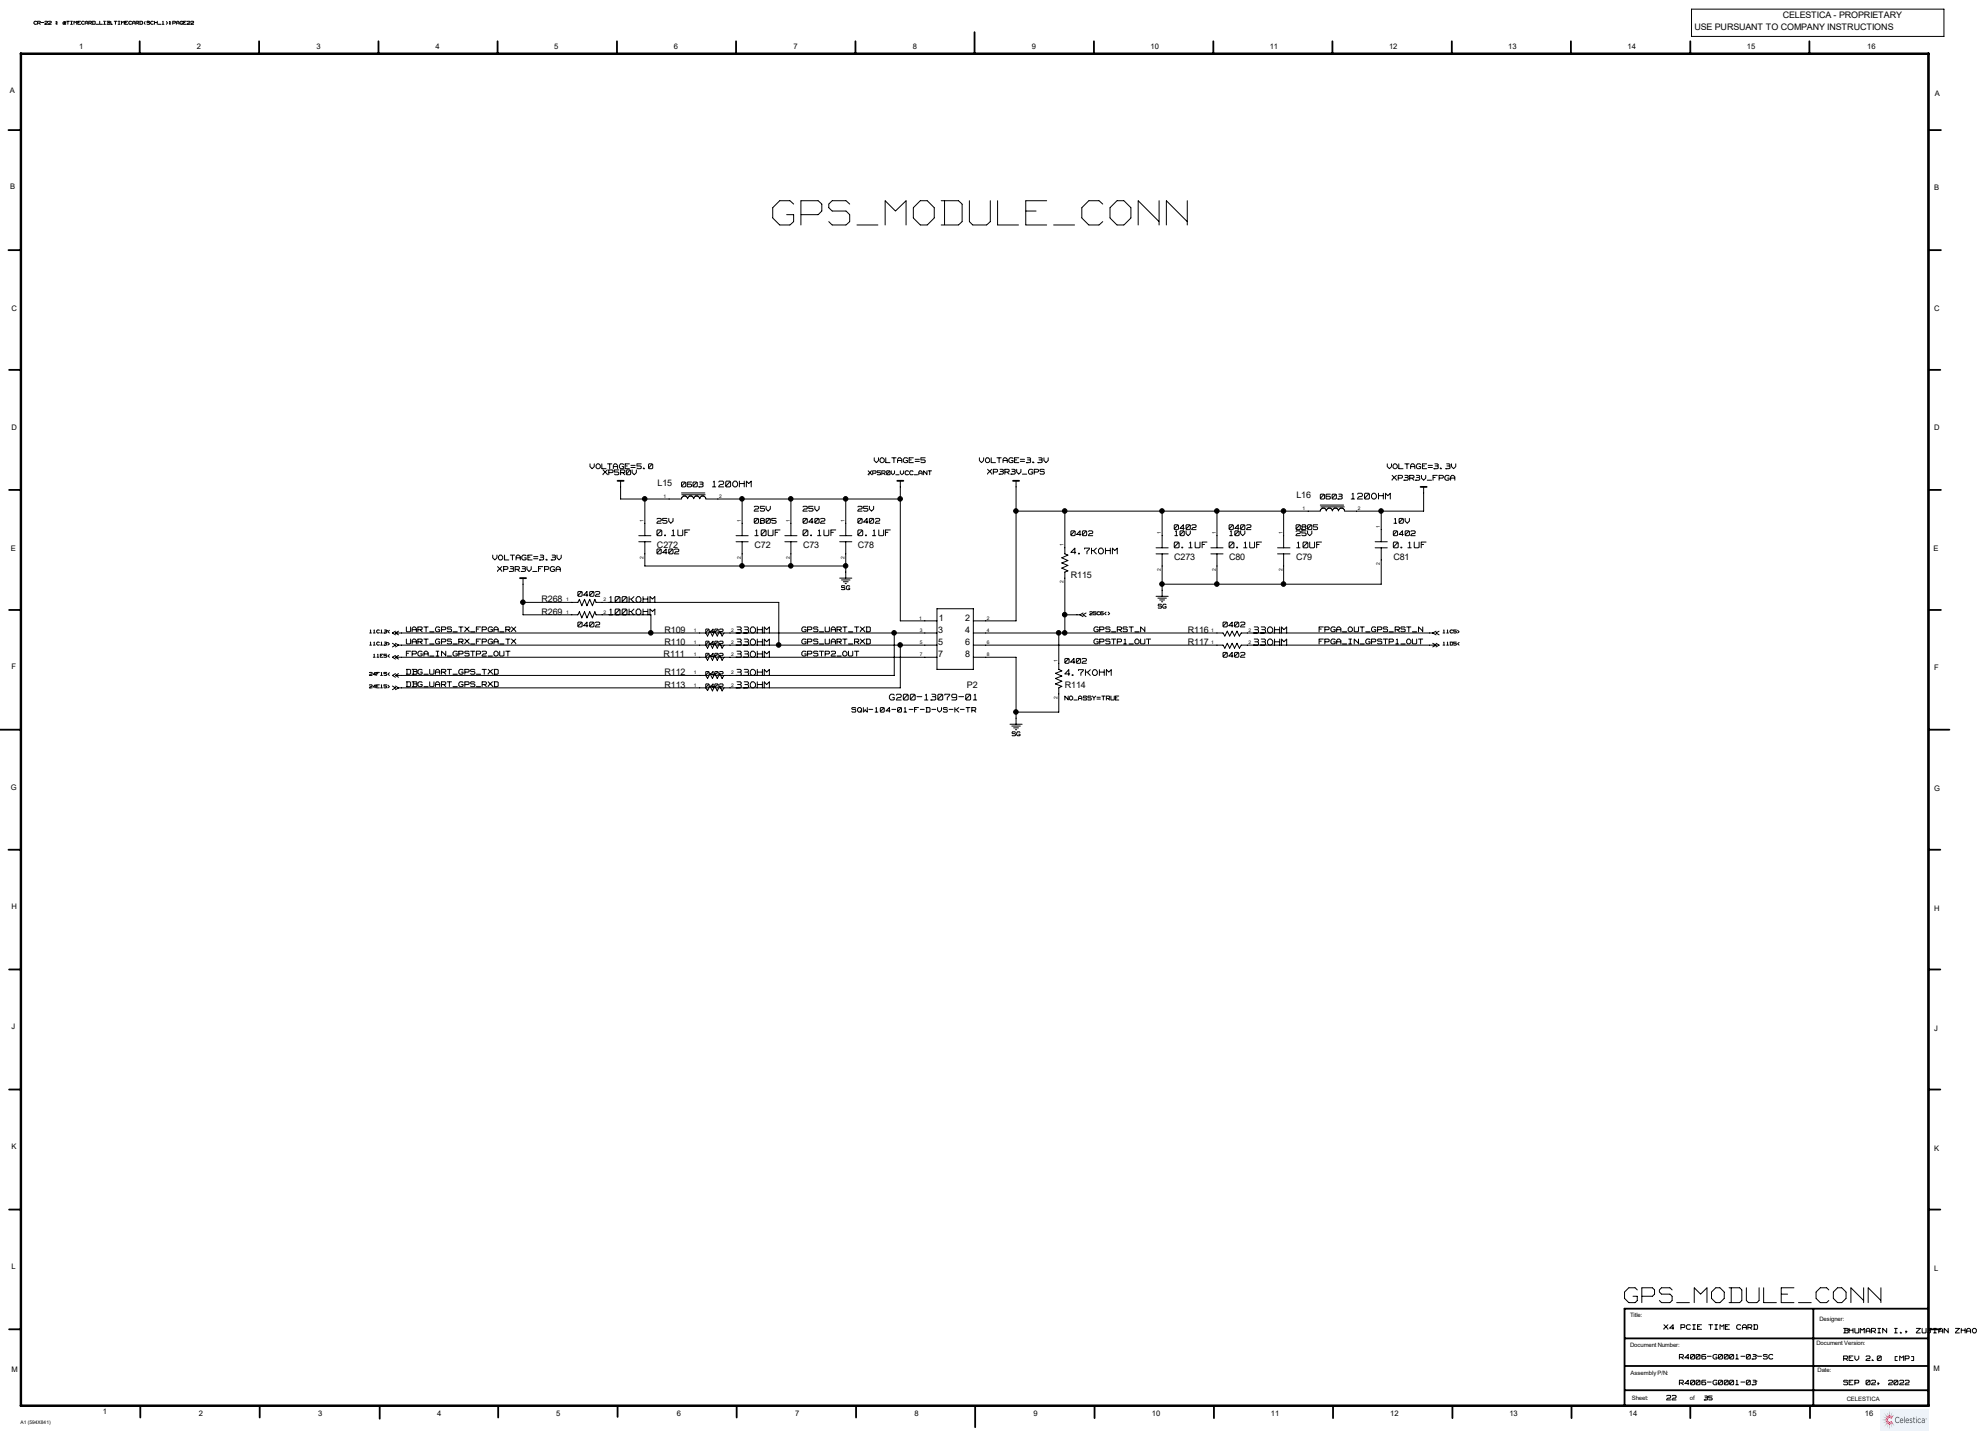
[picture p260: page 22]

Title: | Designer:

Document Number: R4006-G0001-03-SC | Document Version:

# SMA_CONN

0.1UF

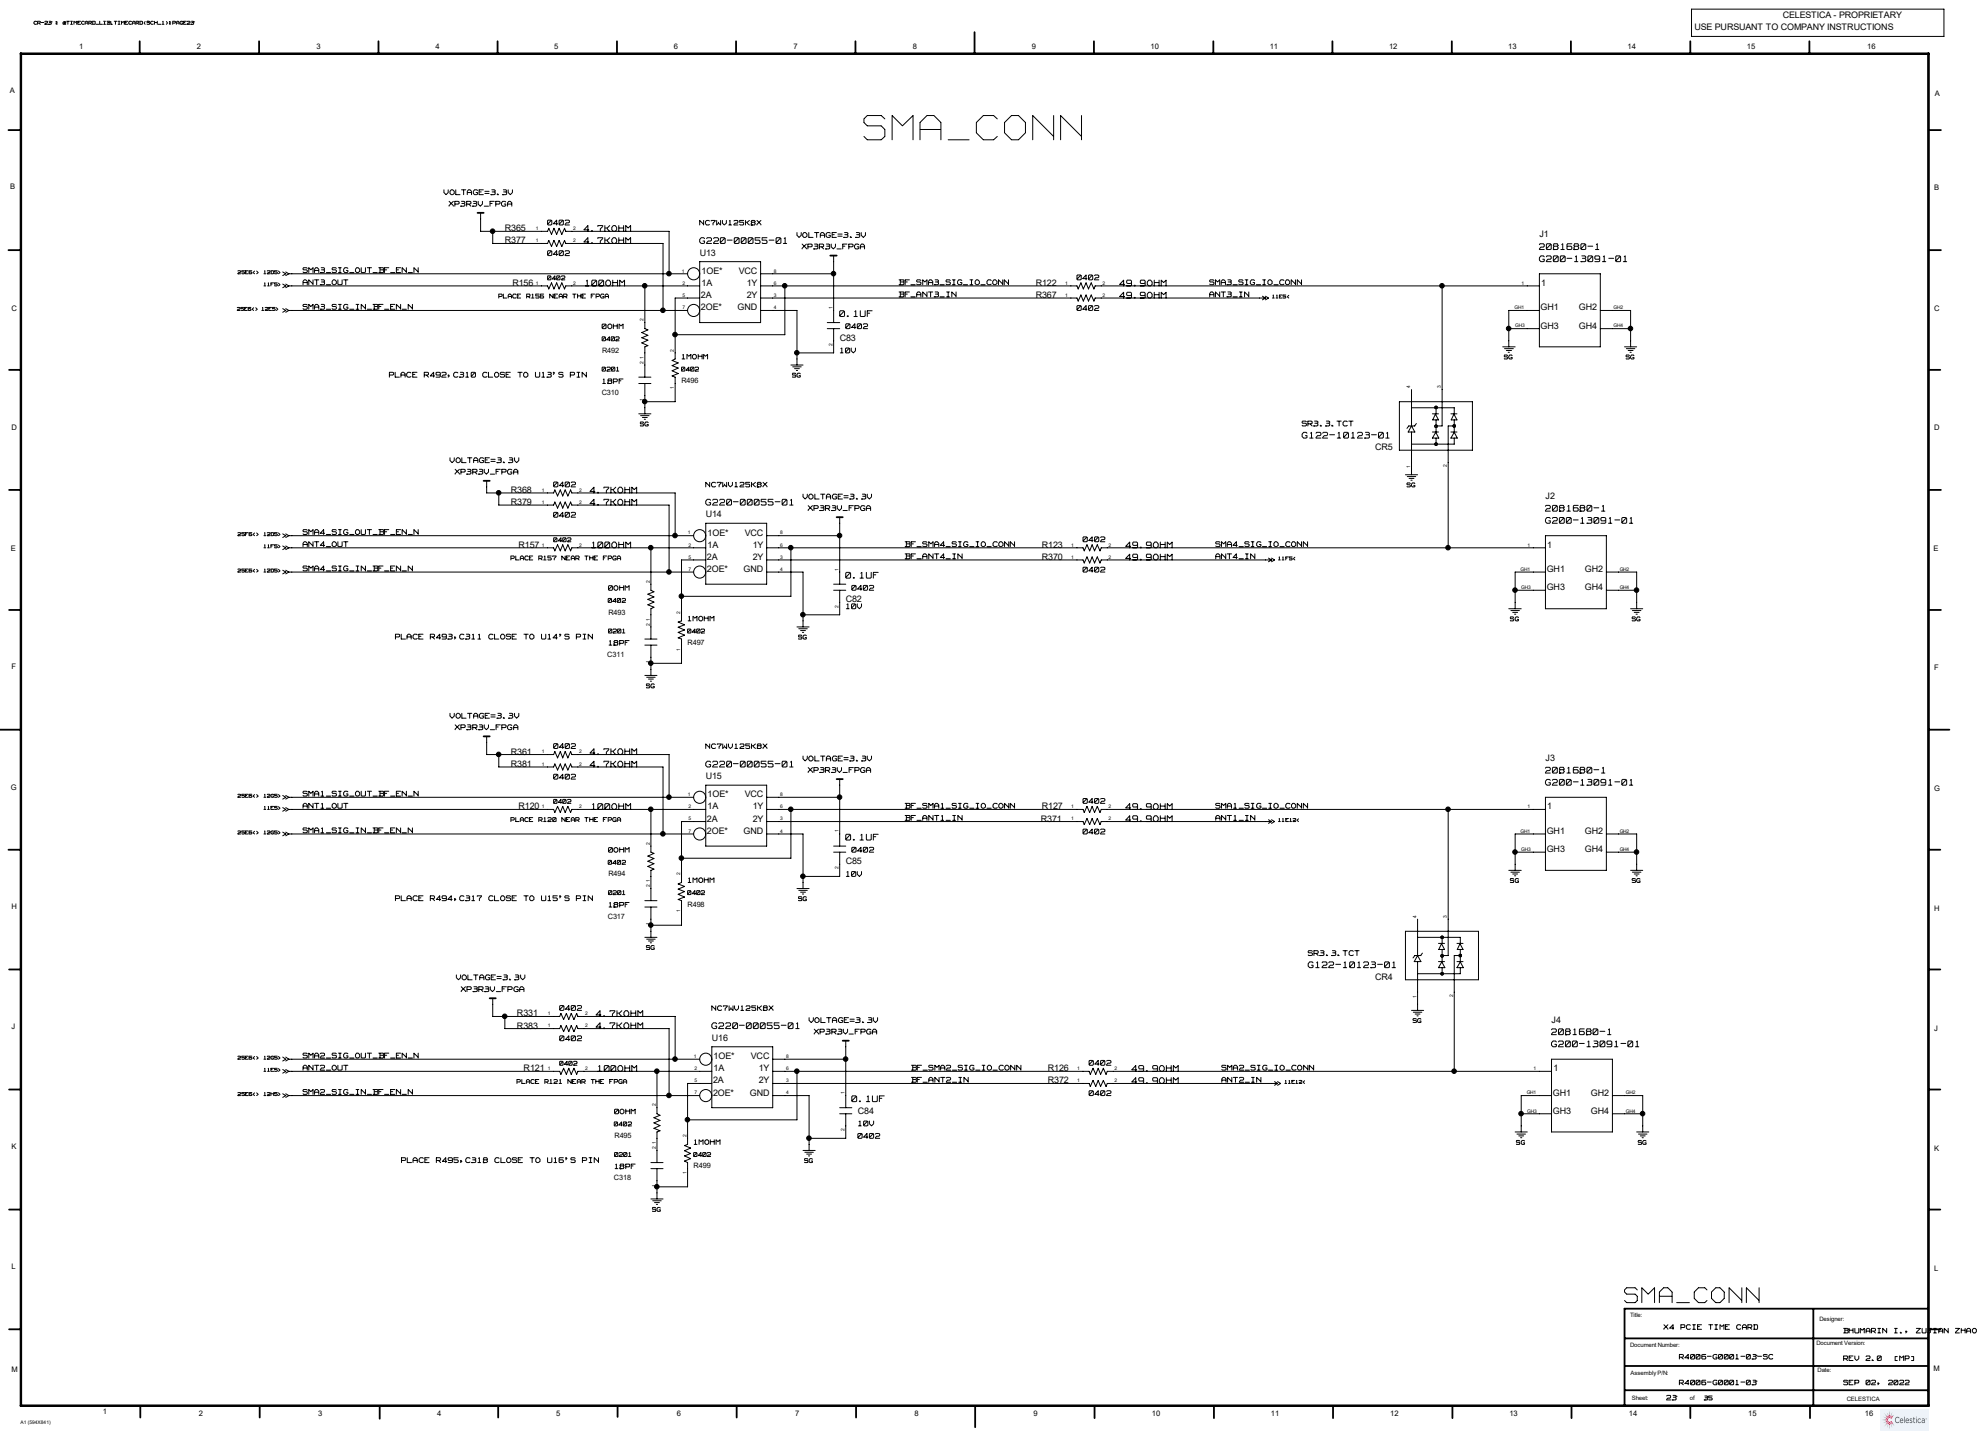
[picture p261: page 23]

PLACE R156 NEAR THE FPGA

PLACE R492,C310 CLOSE TO U13'S PIN

PLACE R157 NEAR THE FPGA

PLACE R493,C311 CLOSE TO U14'S PIN

PLACE R120 NEAR THE FPGA

PLACE R494,C317 CLOSE TO U15'S PIN

PLACE R121 NEAR THE FPGA

PLACE R495,C318 CLOSE TO U16'S PIN

Title: | Designer:

Document Number: R4006-G0001-03-SC | Document Version:

USB<>I2C CONNECT TO I2C_SW & EEPROM.

## USB-C CONN

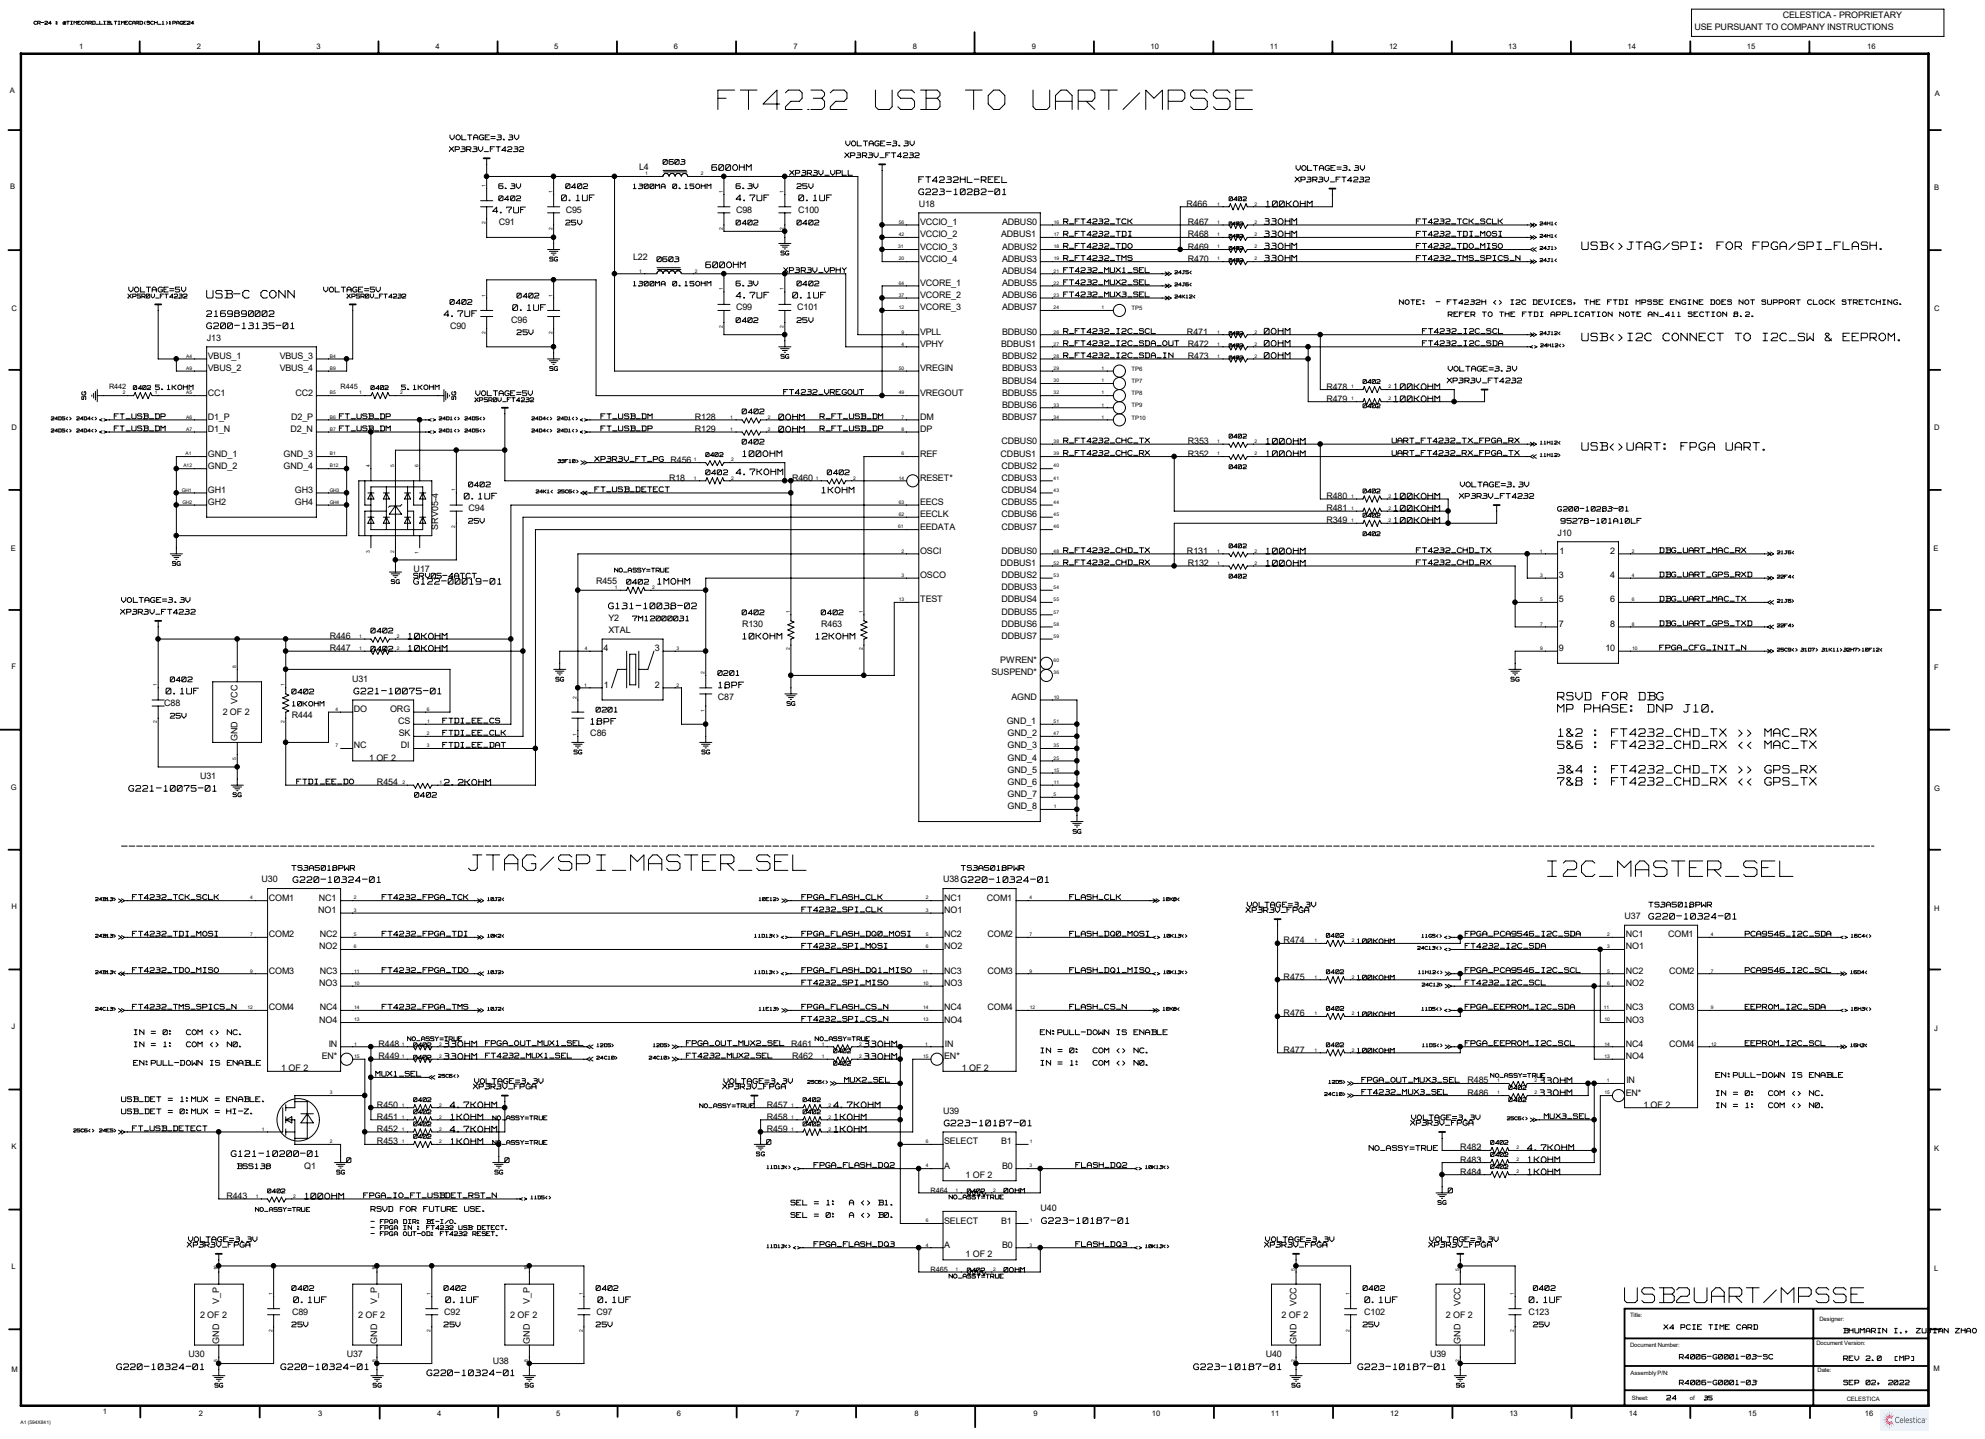
[picture p262: page 24]

FT4232 USB TO UART/MPSSE

USB<>JTAG/SPI: FOR FPGA/SPI_FLASH.

REFER TO THE FTDI APPLICATION NOTE AN_411 SECTION 8.2.
FT4232_I2C_SCL
FT4232_I2C_SDA

USB<>UART: FPGA UART.

EN:PULL-DOWN IS ENABLE
IN = 0: COM <> NC.

IN = 1: COM <> N0.

RSVD FOR FUTURE USE.
- FPGA DIR: BI-I/O.
- FPGA IN : FT4232 USB DETECT.
- FPGA OUT-OD: FT4232 RESET.

Title: | Designer:

Document Number: R4006-G0001-03-SC | Document Version:

# TEST POINT

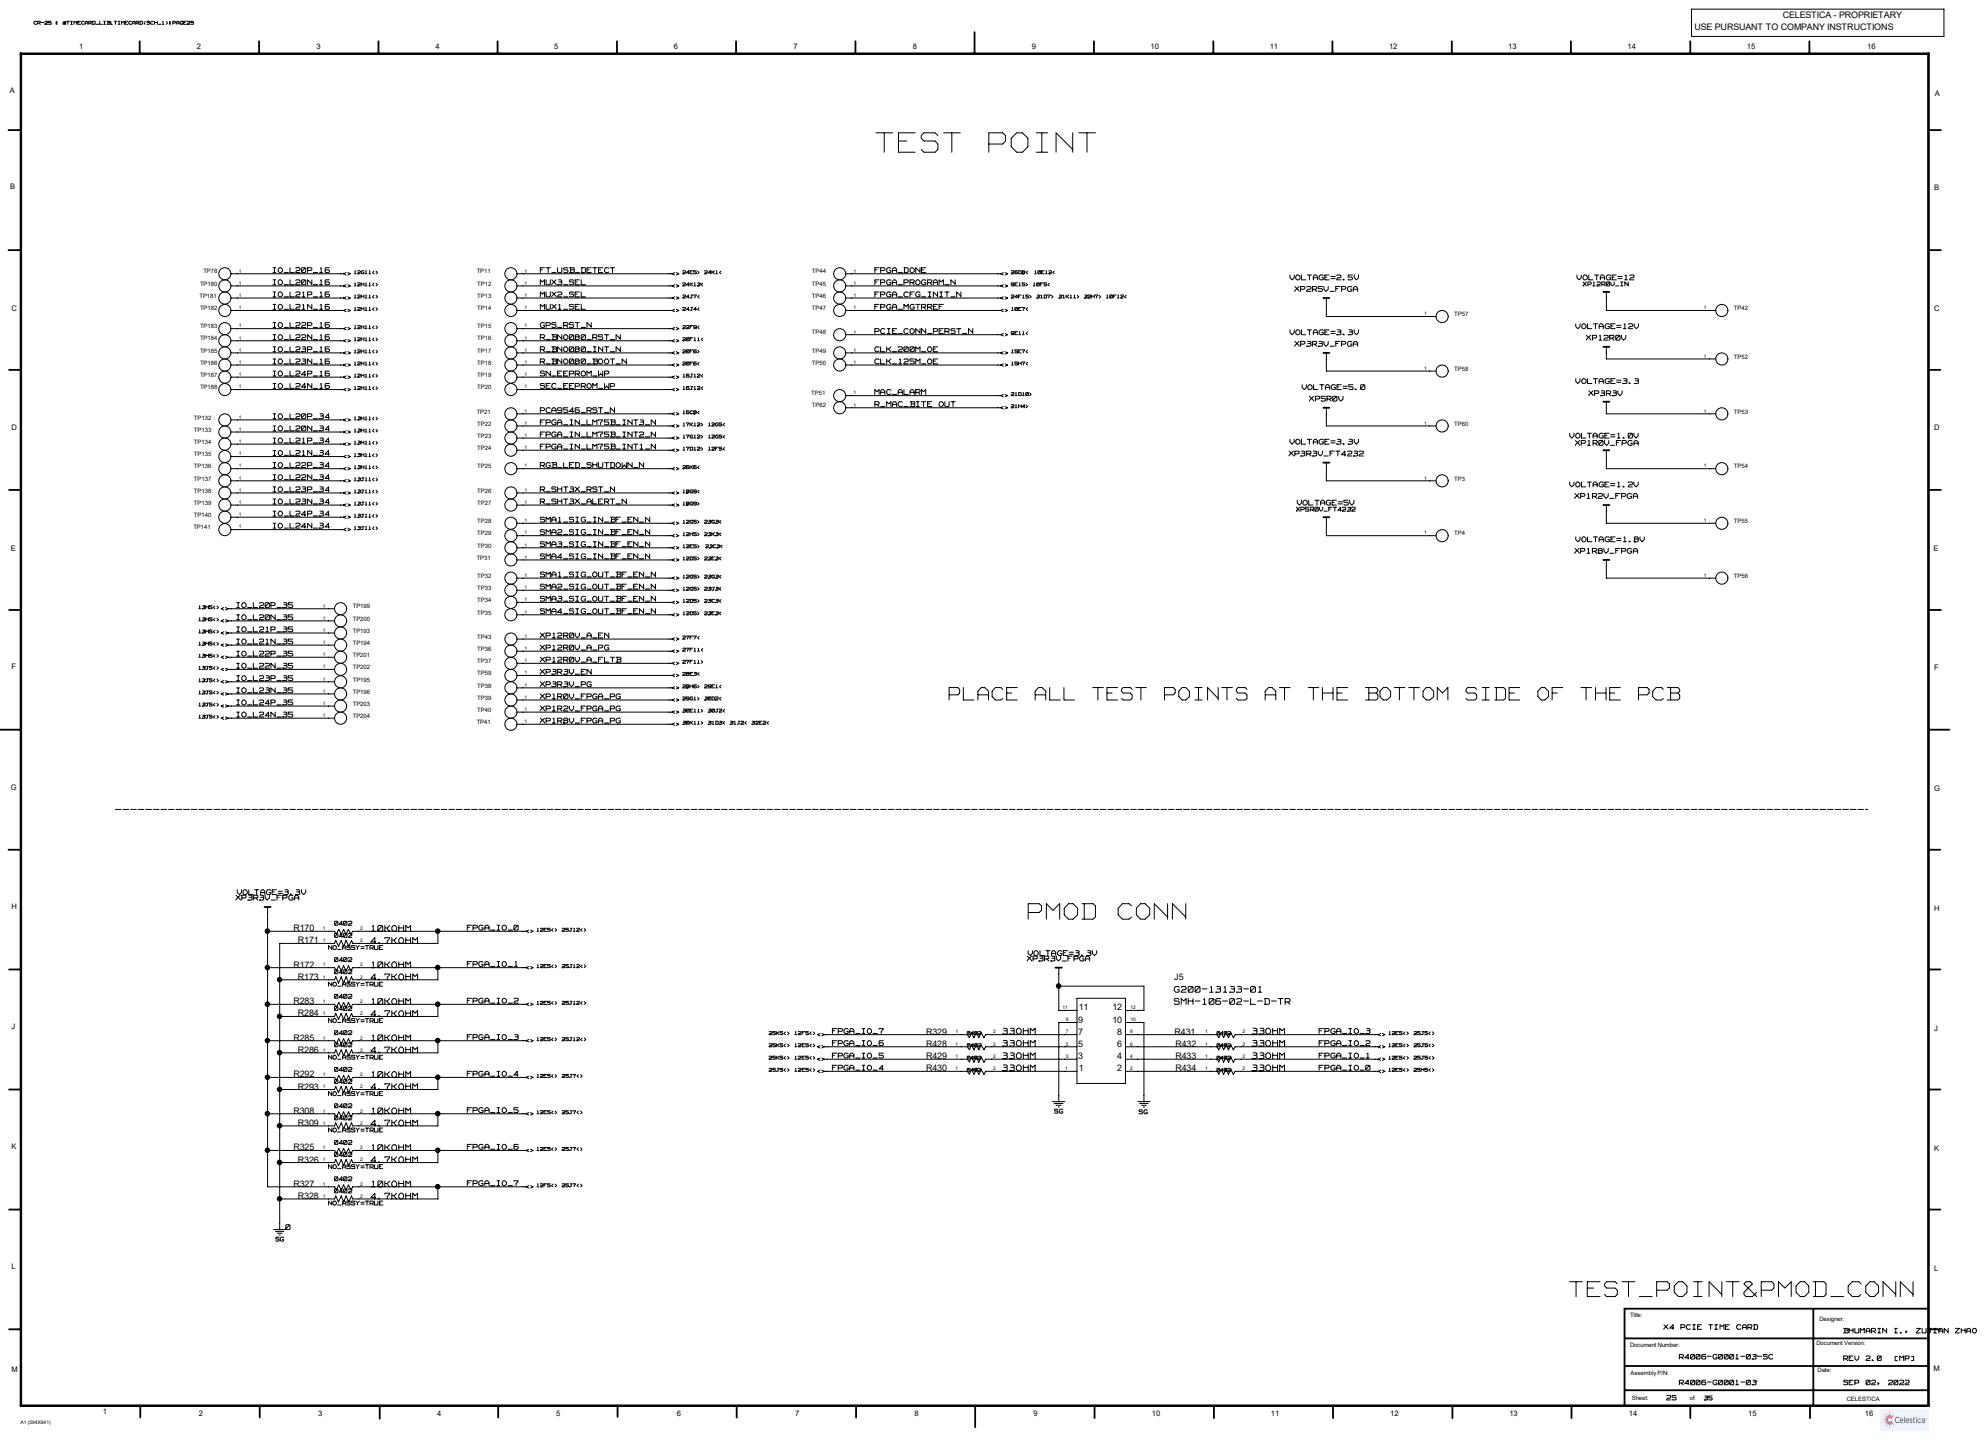
[picture p263: page 25]

PLACE ALL TEST POINTS AT THE BOTTOM SIDE OF THE PCB

Title: | Designer:

Document Number: R4006-G0001-03-SC | Document Version:

# USR_LED_STATUS

# RGB_LED_STATUS

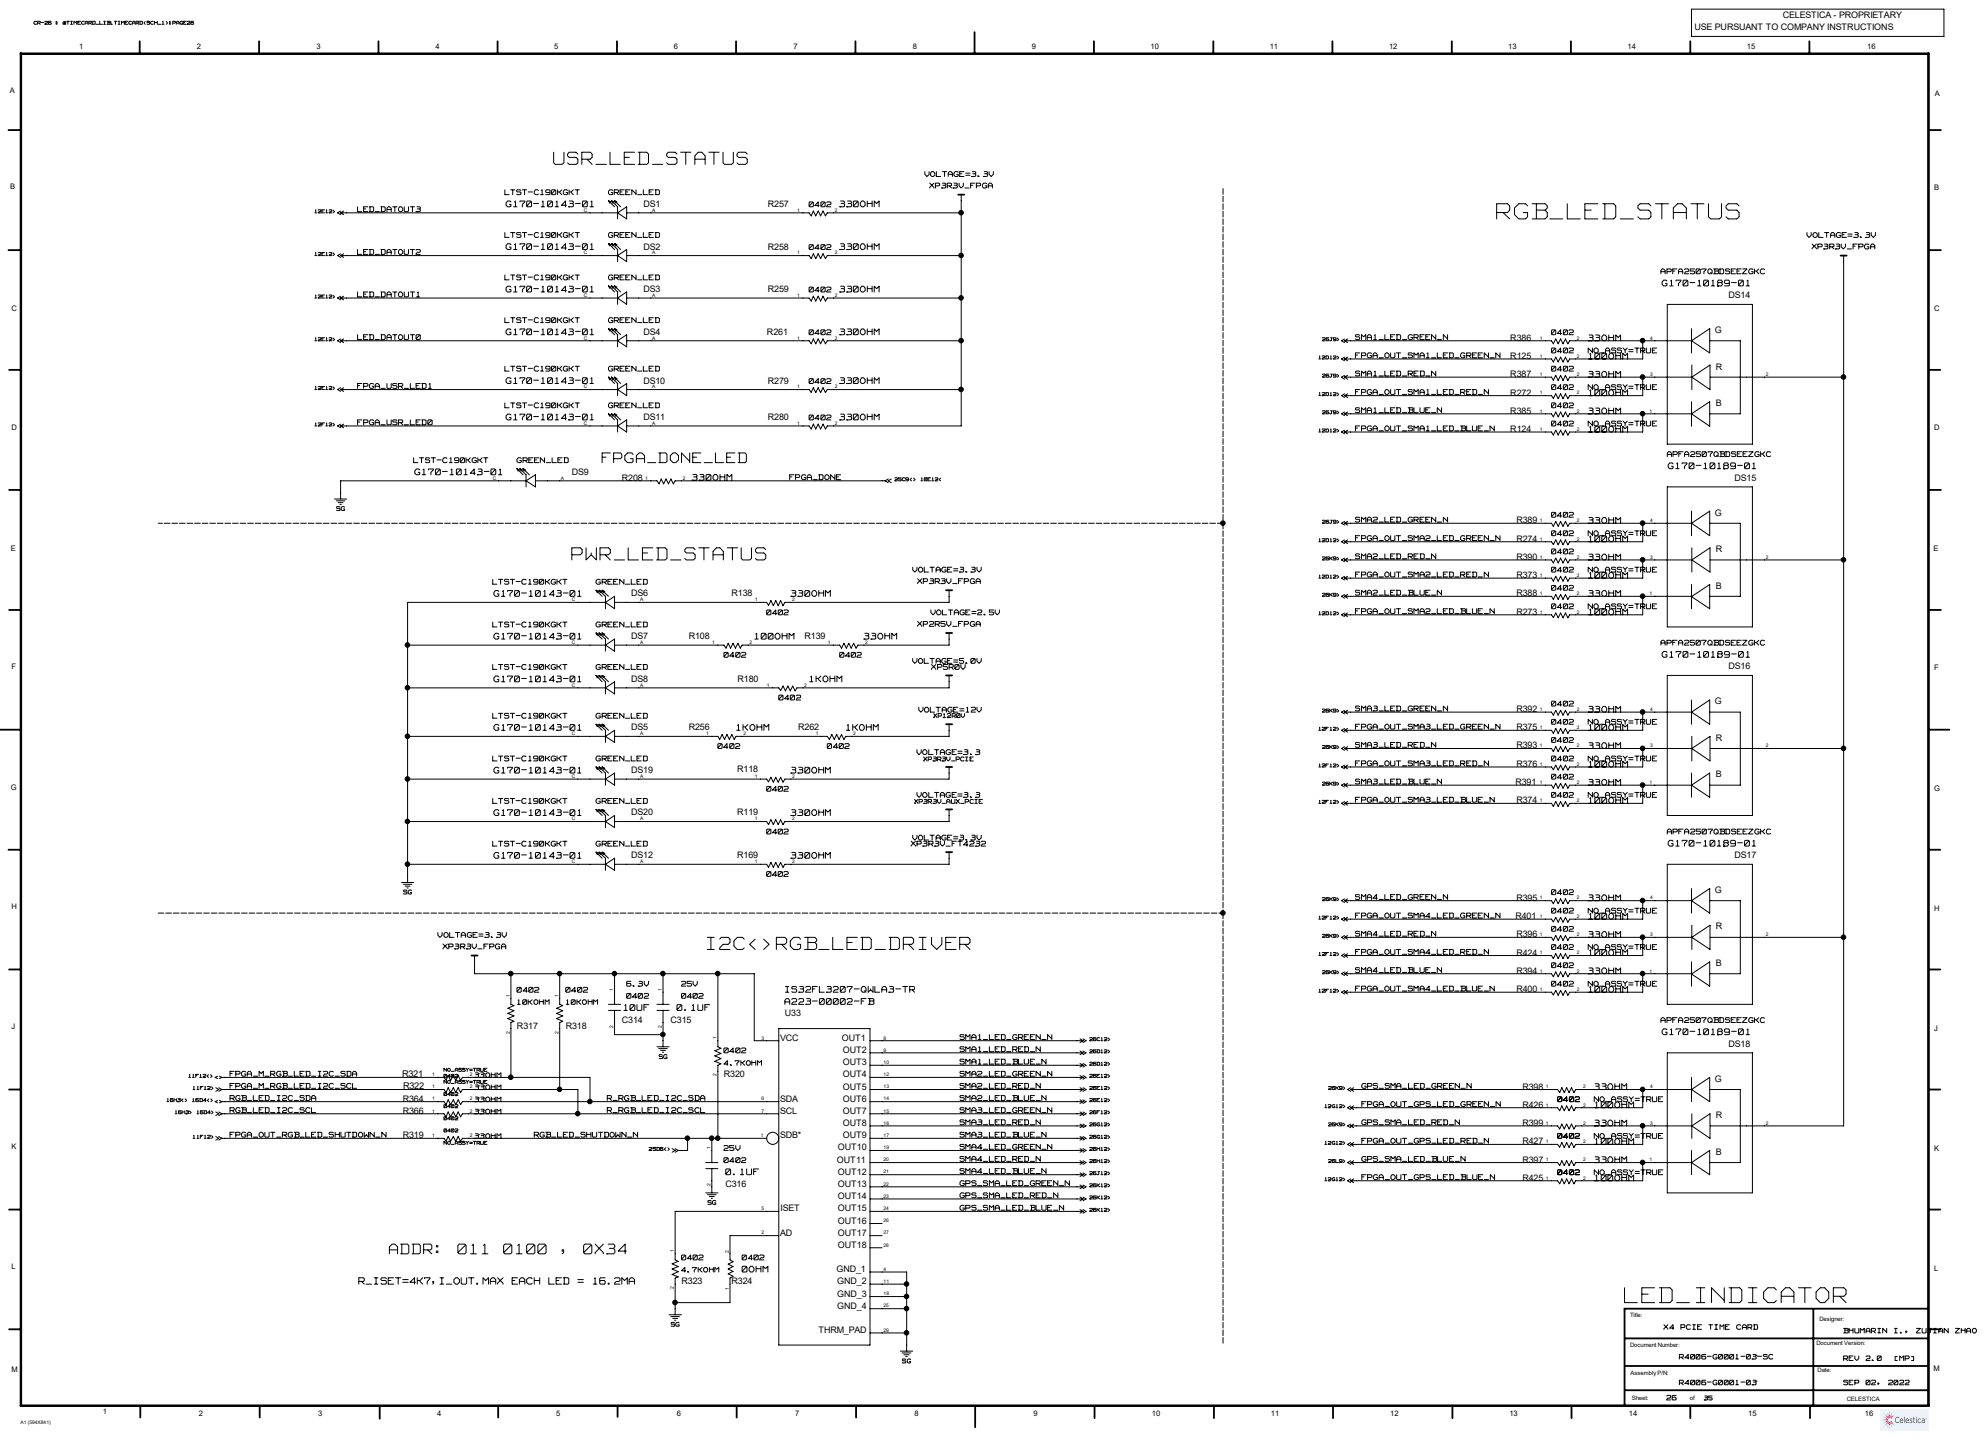
[picture p264: page 26]

Title: | Designer:

Document Number: R4006-G0001-03-SC | Document Version:

# XP12R0V INPUT

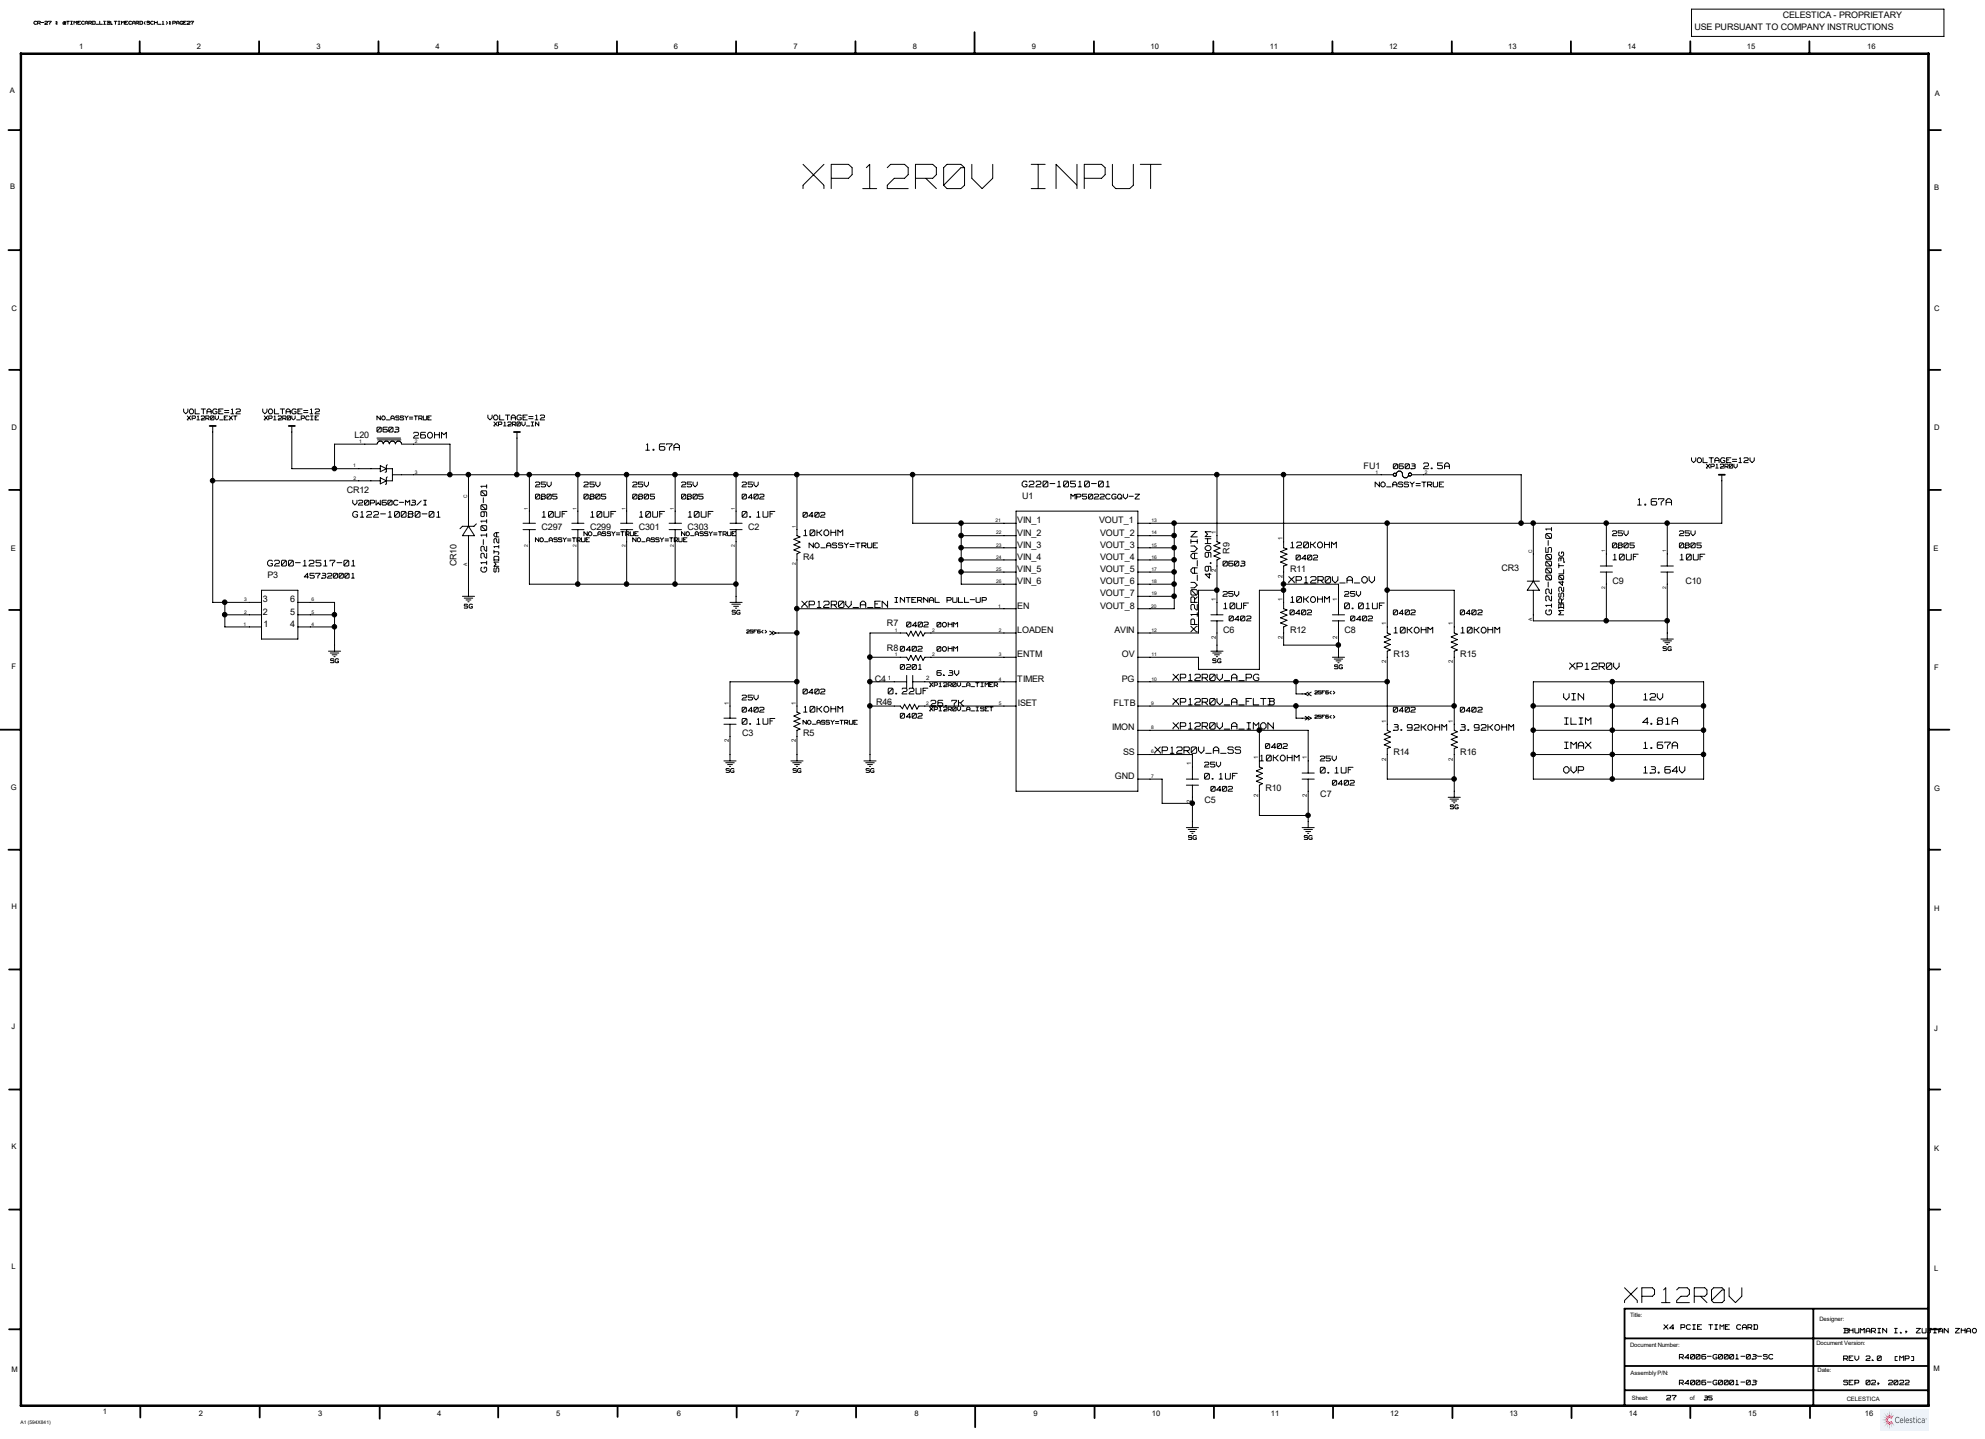
[picture p265: page 27]

Title: | Designer:

Document Number: R4006-G0001-03-SC | Document Version:

# XP3R3V

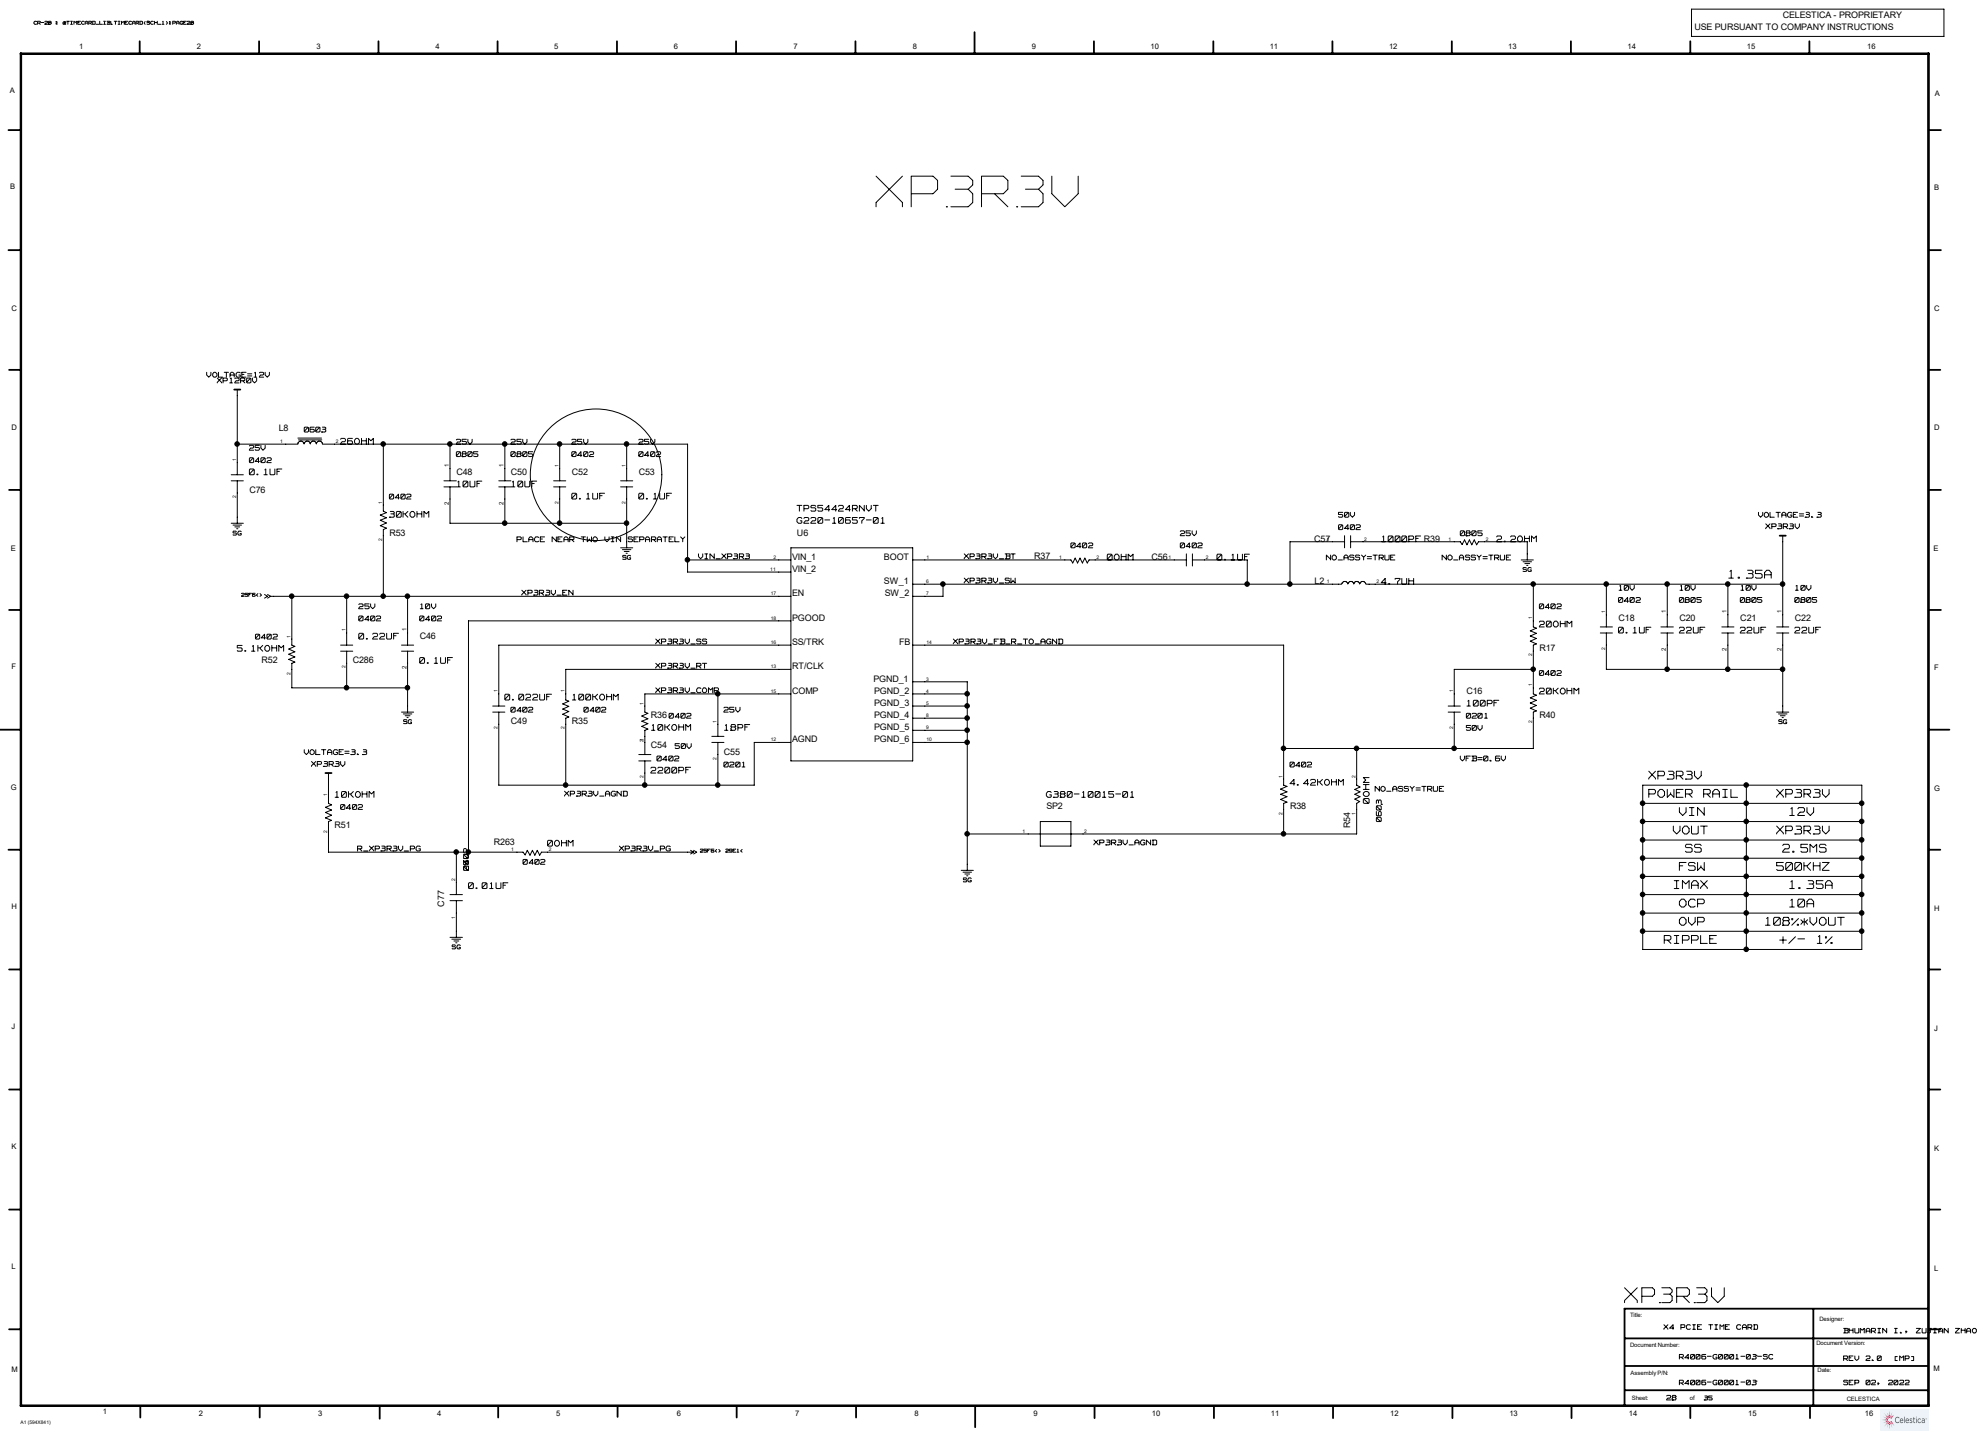
[picture p266: page 28]

PLACE NEAR TWO VIN SEPARATELY

Title: | Designer:

Document Number: R4006-G0001-03-SC | Document Version:

# XP1R0V_FPGA

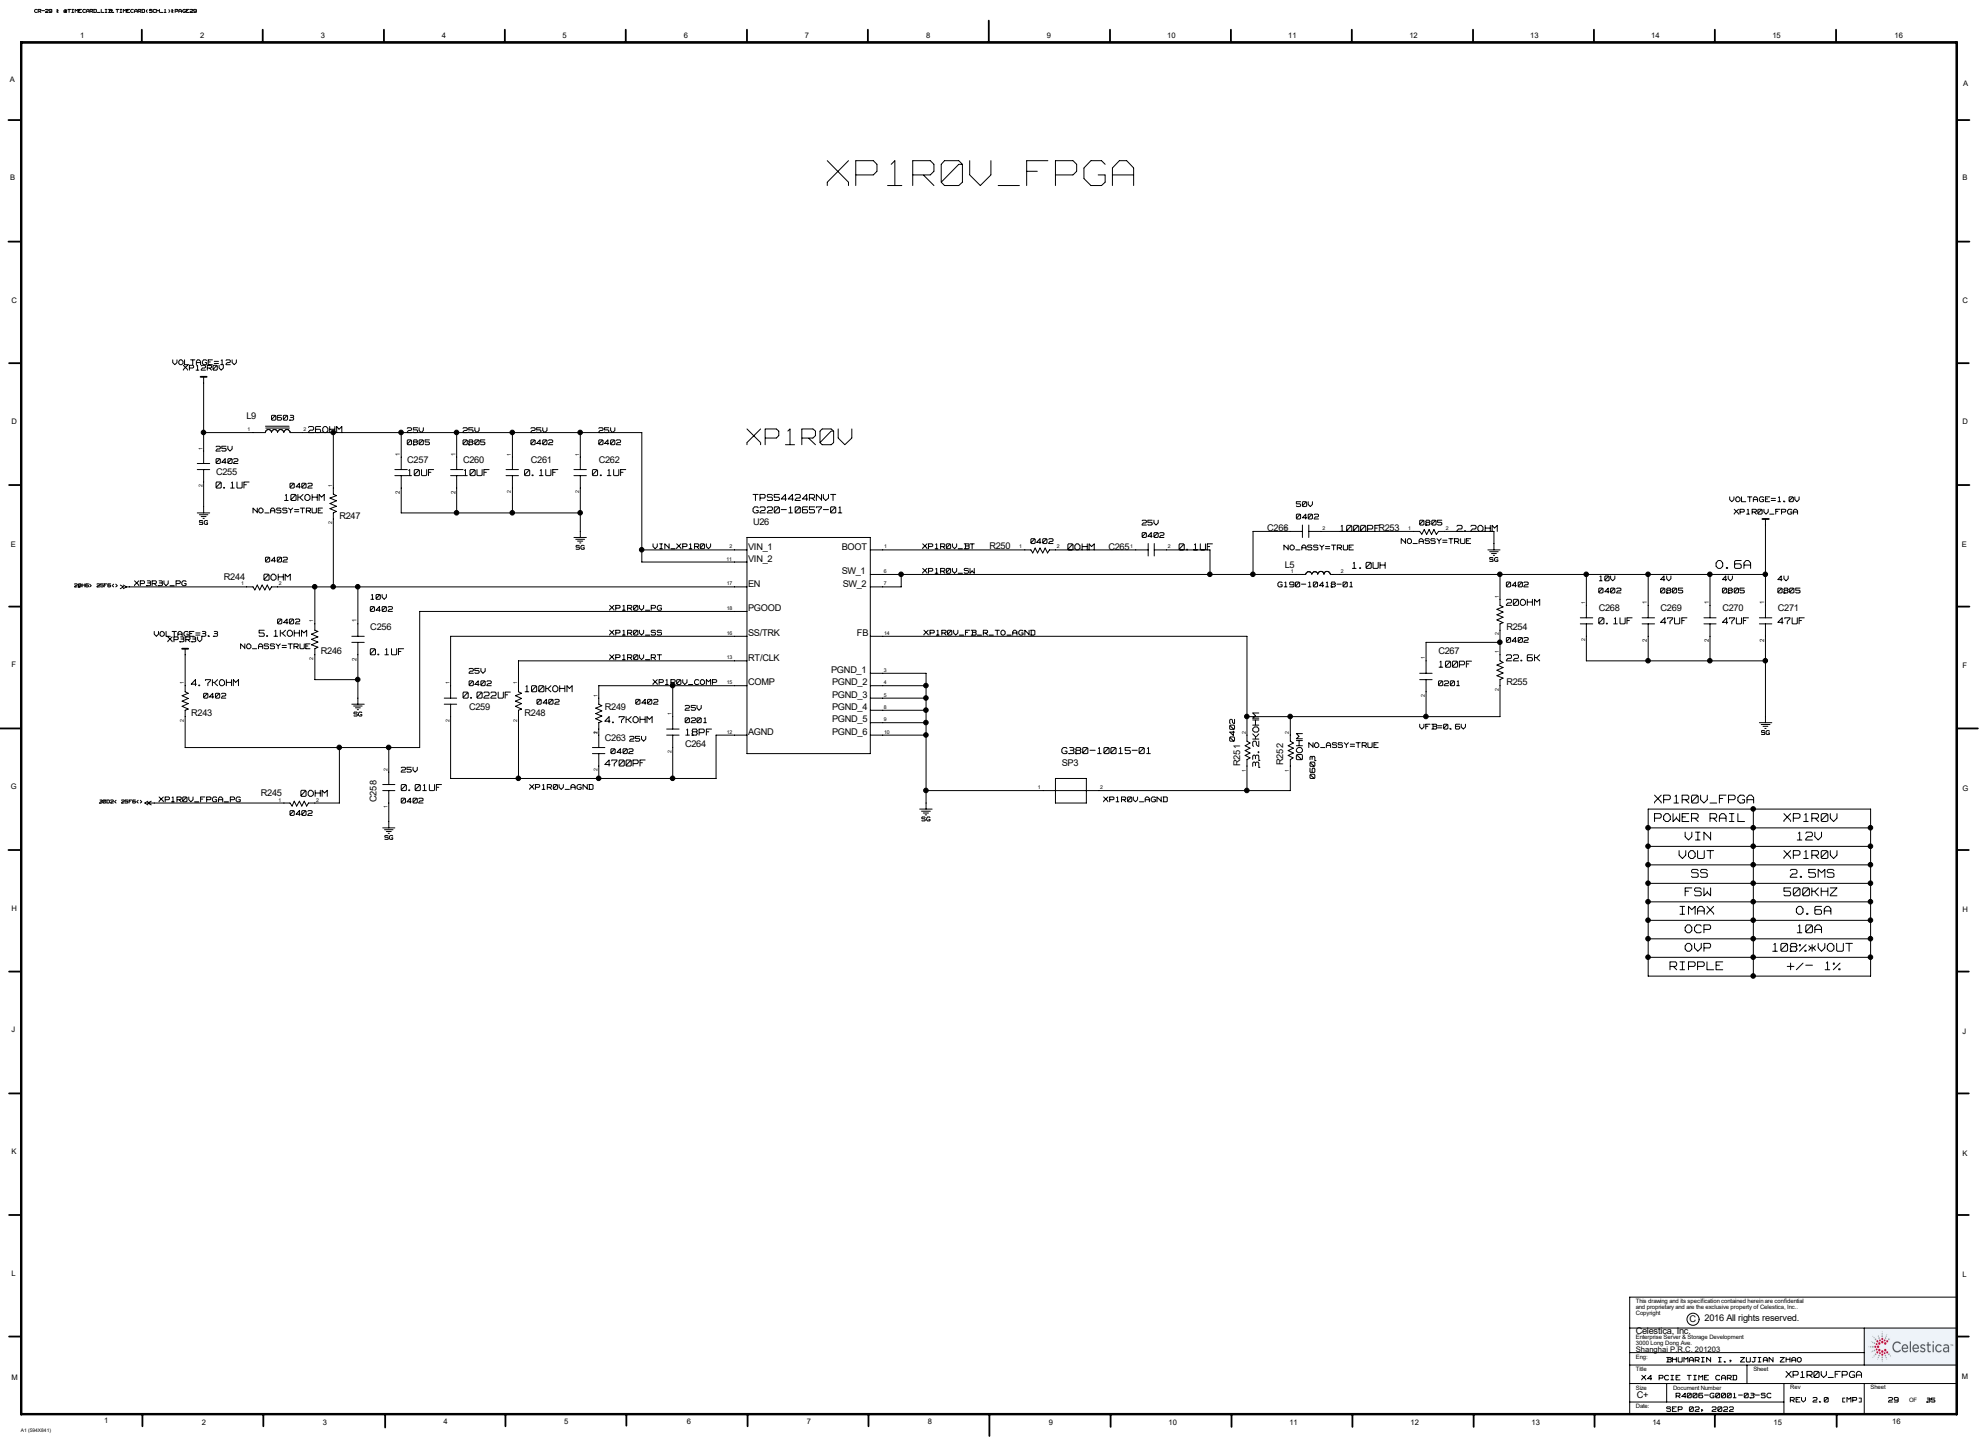
[picture p267: page 29]

This drawing and its specification contained herein are confidential
and proprietary and are the exclusive property of Celestica, Inc..
Copyright
Celestica, Inc.
Enterprise Server & Storage Development
3000 Long Dong Ave.
Shanghai P.R.C. 201203
Eng:

# XP1R2V_FPGA

0.065A

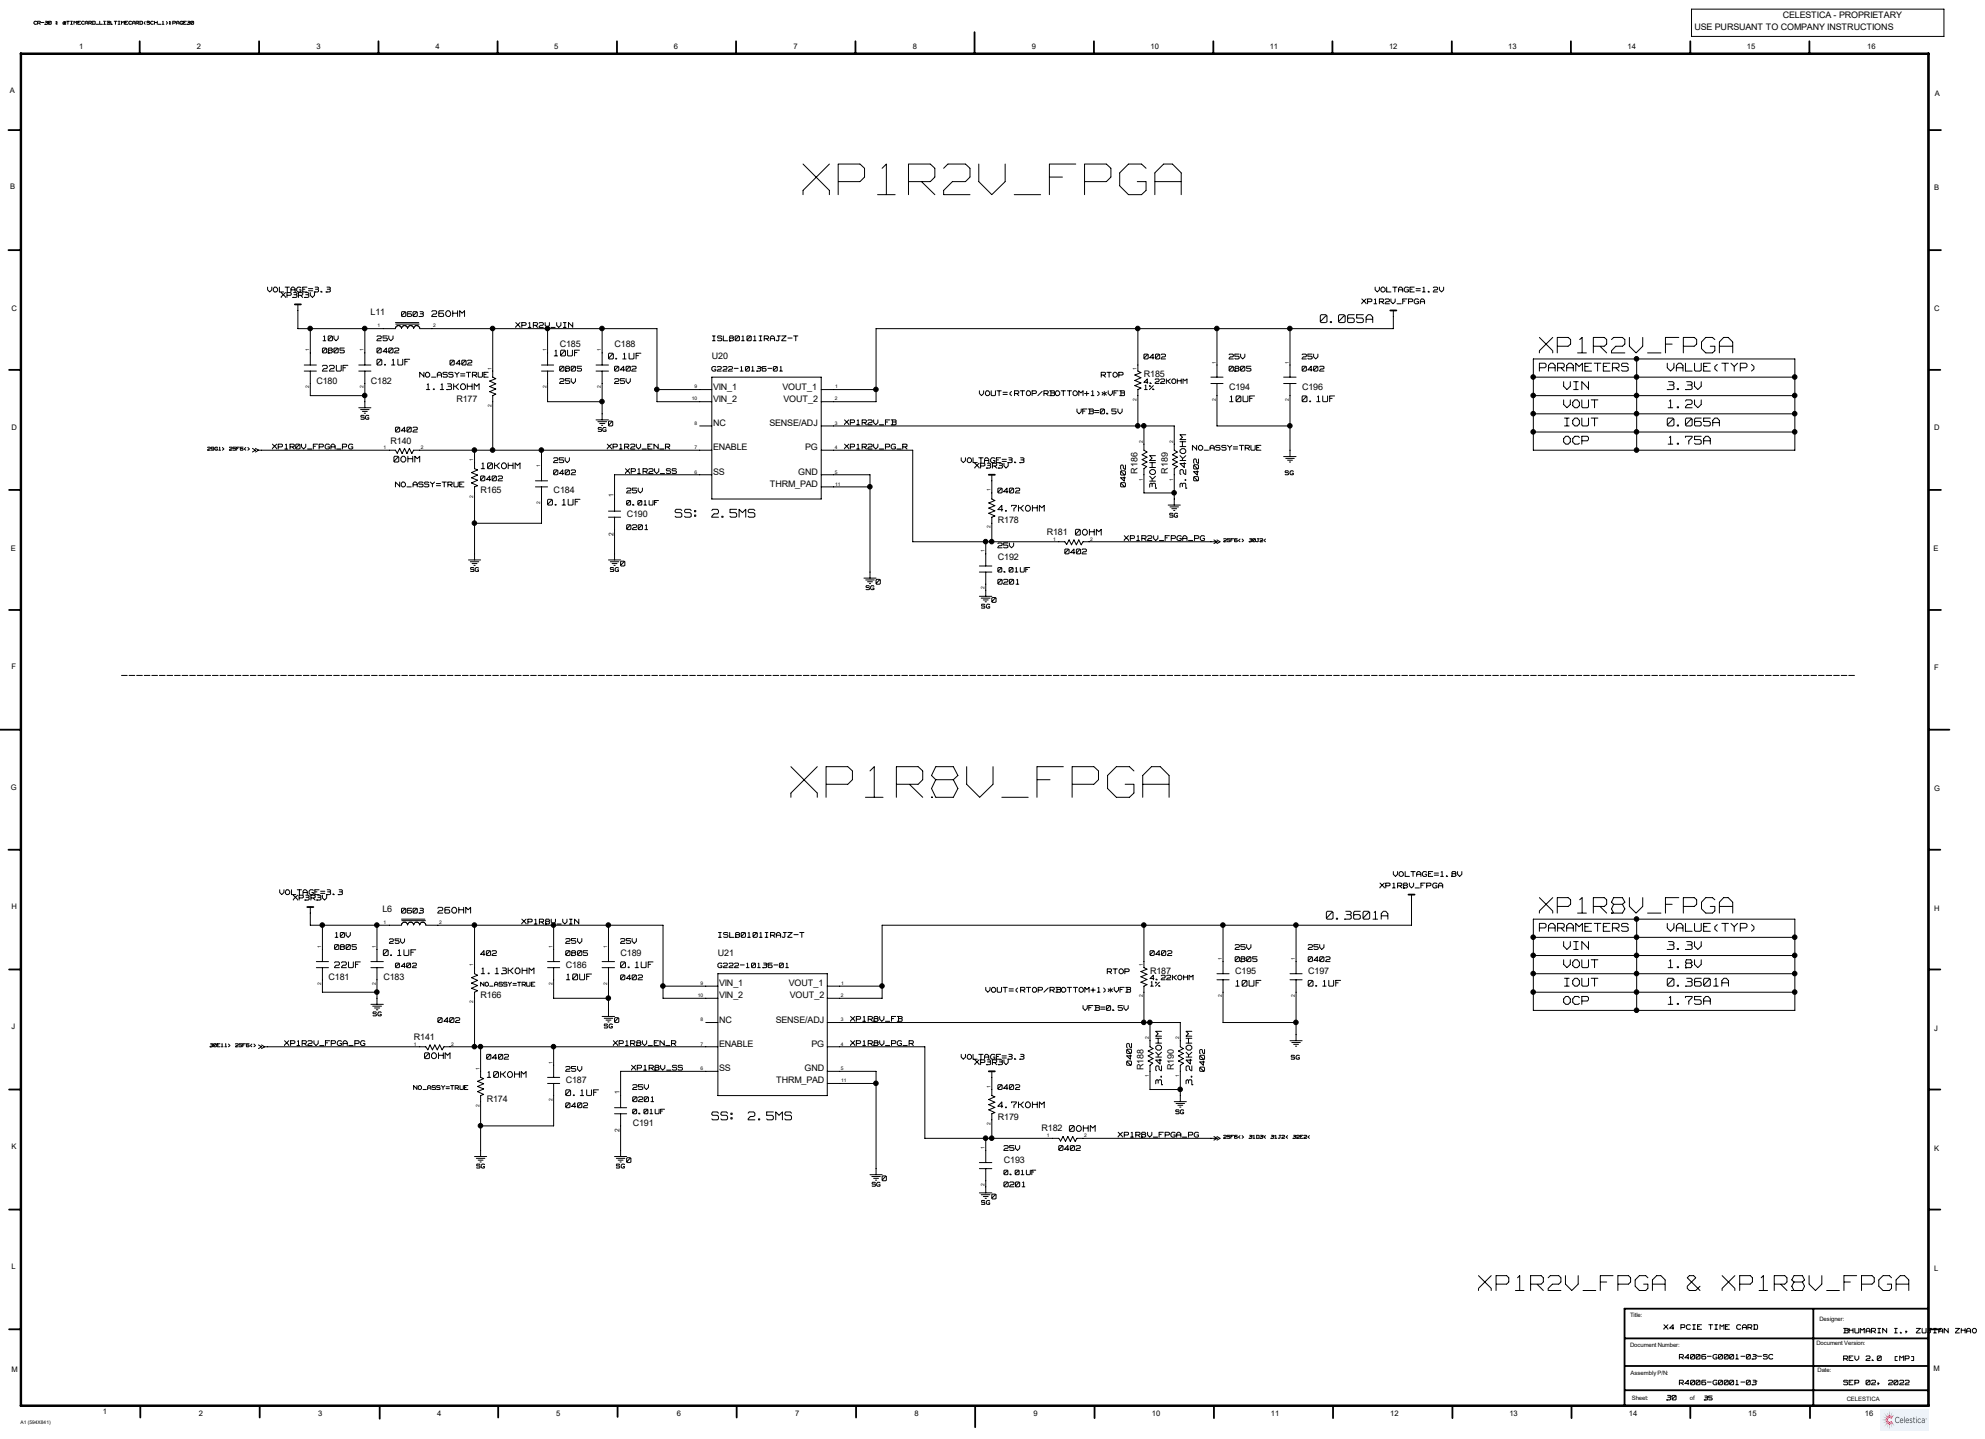
[picture p268: page 30]

VOUT=(RTOP/RBOTTOM+1)*VFB

Title: | Designer:

Document Number: R4006-G0001-03-SC | Document Version:

# XP3R3V_FPGA

### 1KOHM

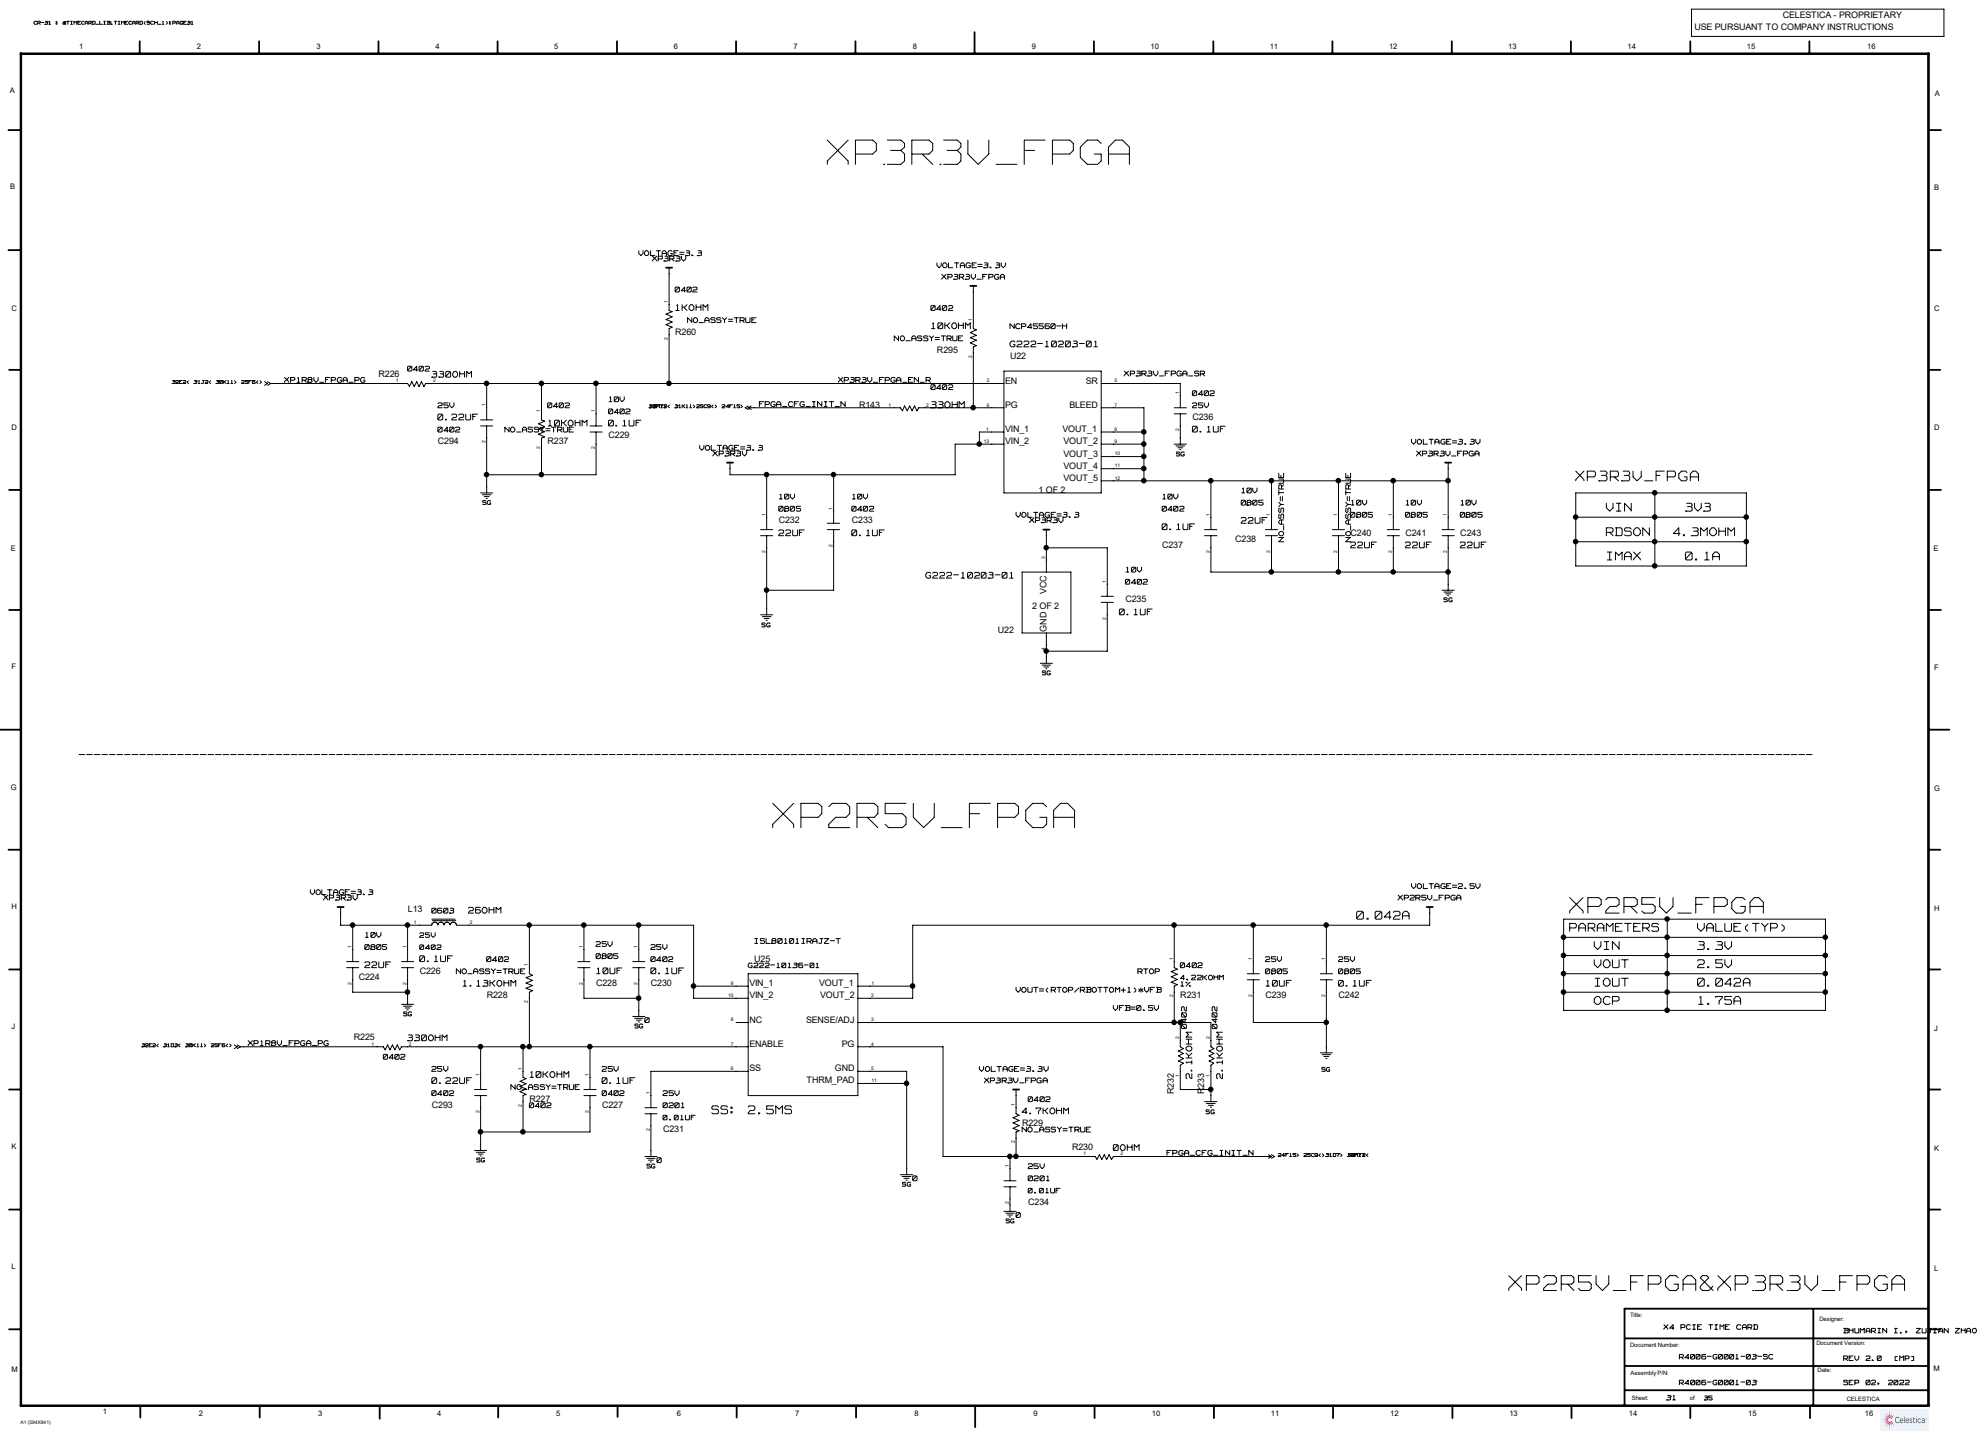
[picture p269: page 31]

VOUT=(RTOP/RBOTTOM+1)*VFB

Title: | Designer:

Document Number: R4006-G0001-03-SC | Document Version:

# XP5R0V

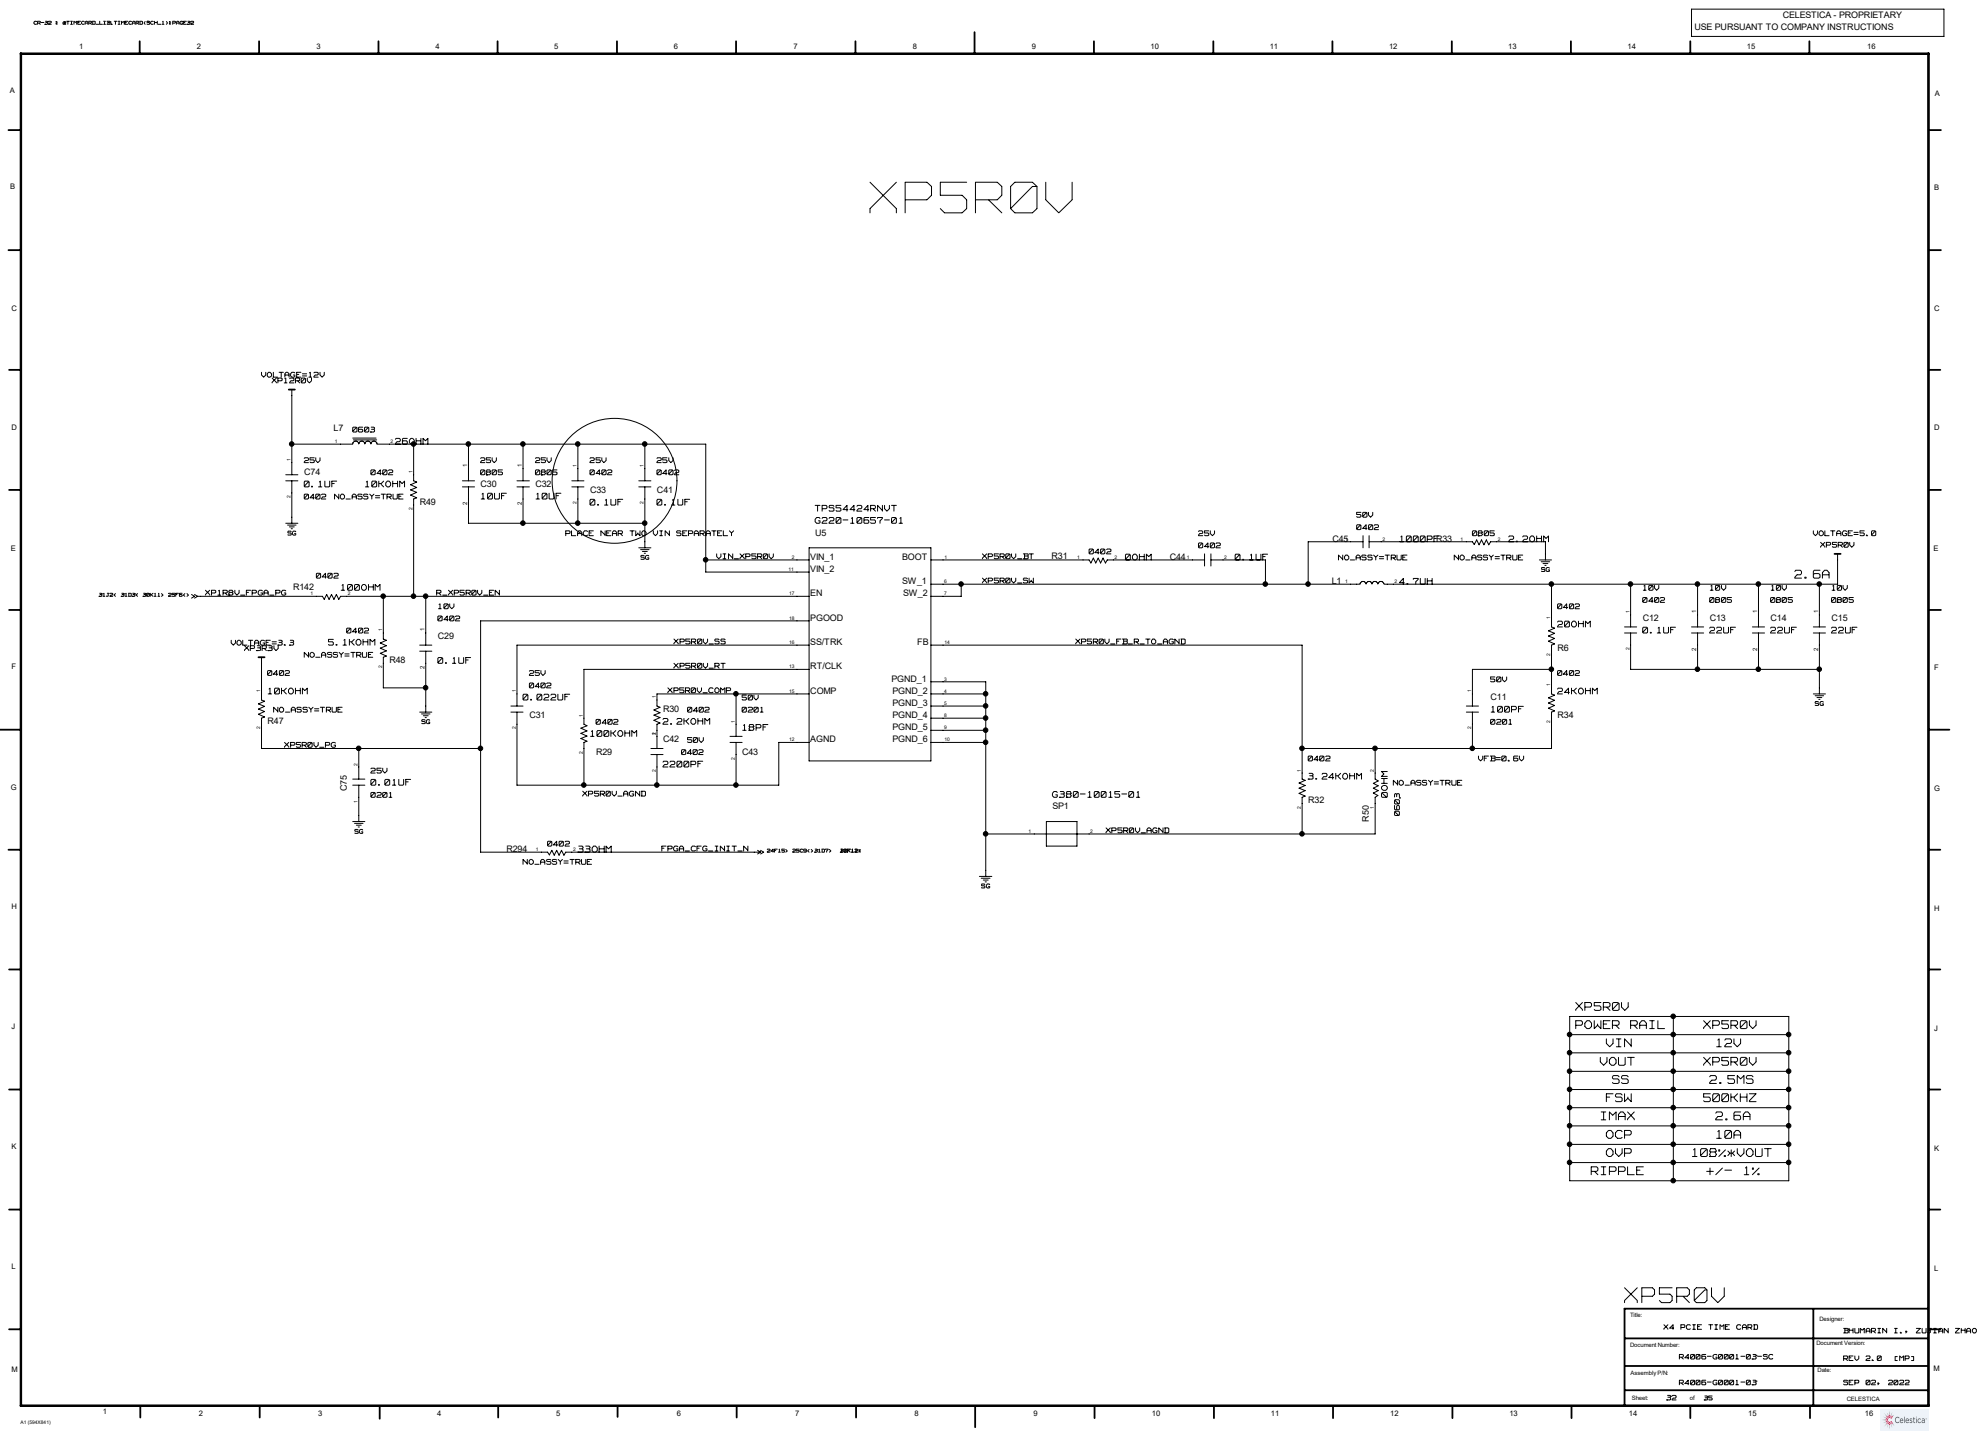
[picture p270: page 32]

PLACE NEAR TWO VIN SEPARATELY

Title: | Designer:

Document Number: R4006-G0001-03-SC | Document Version:

# XP3R3V_REG_FT

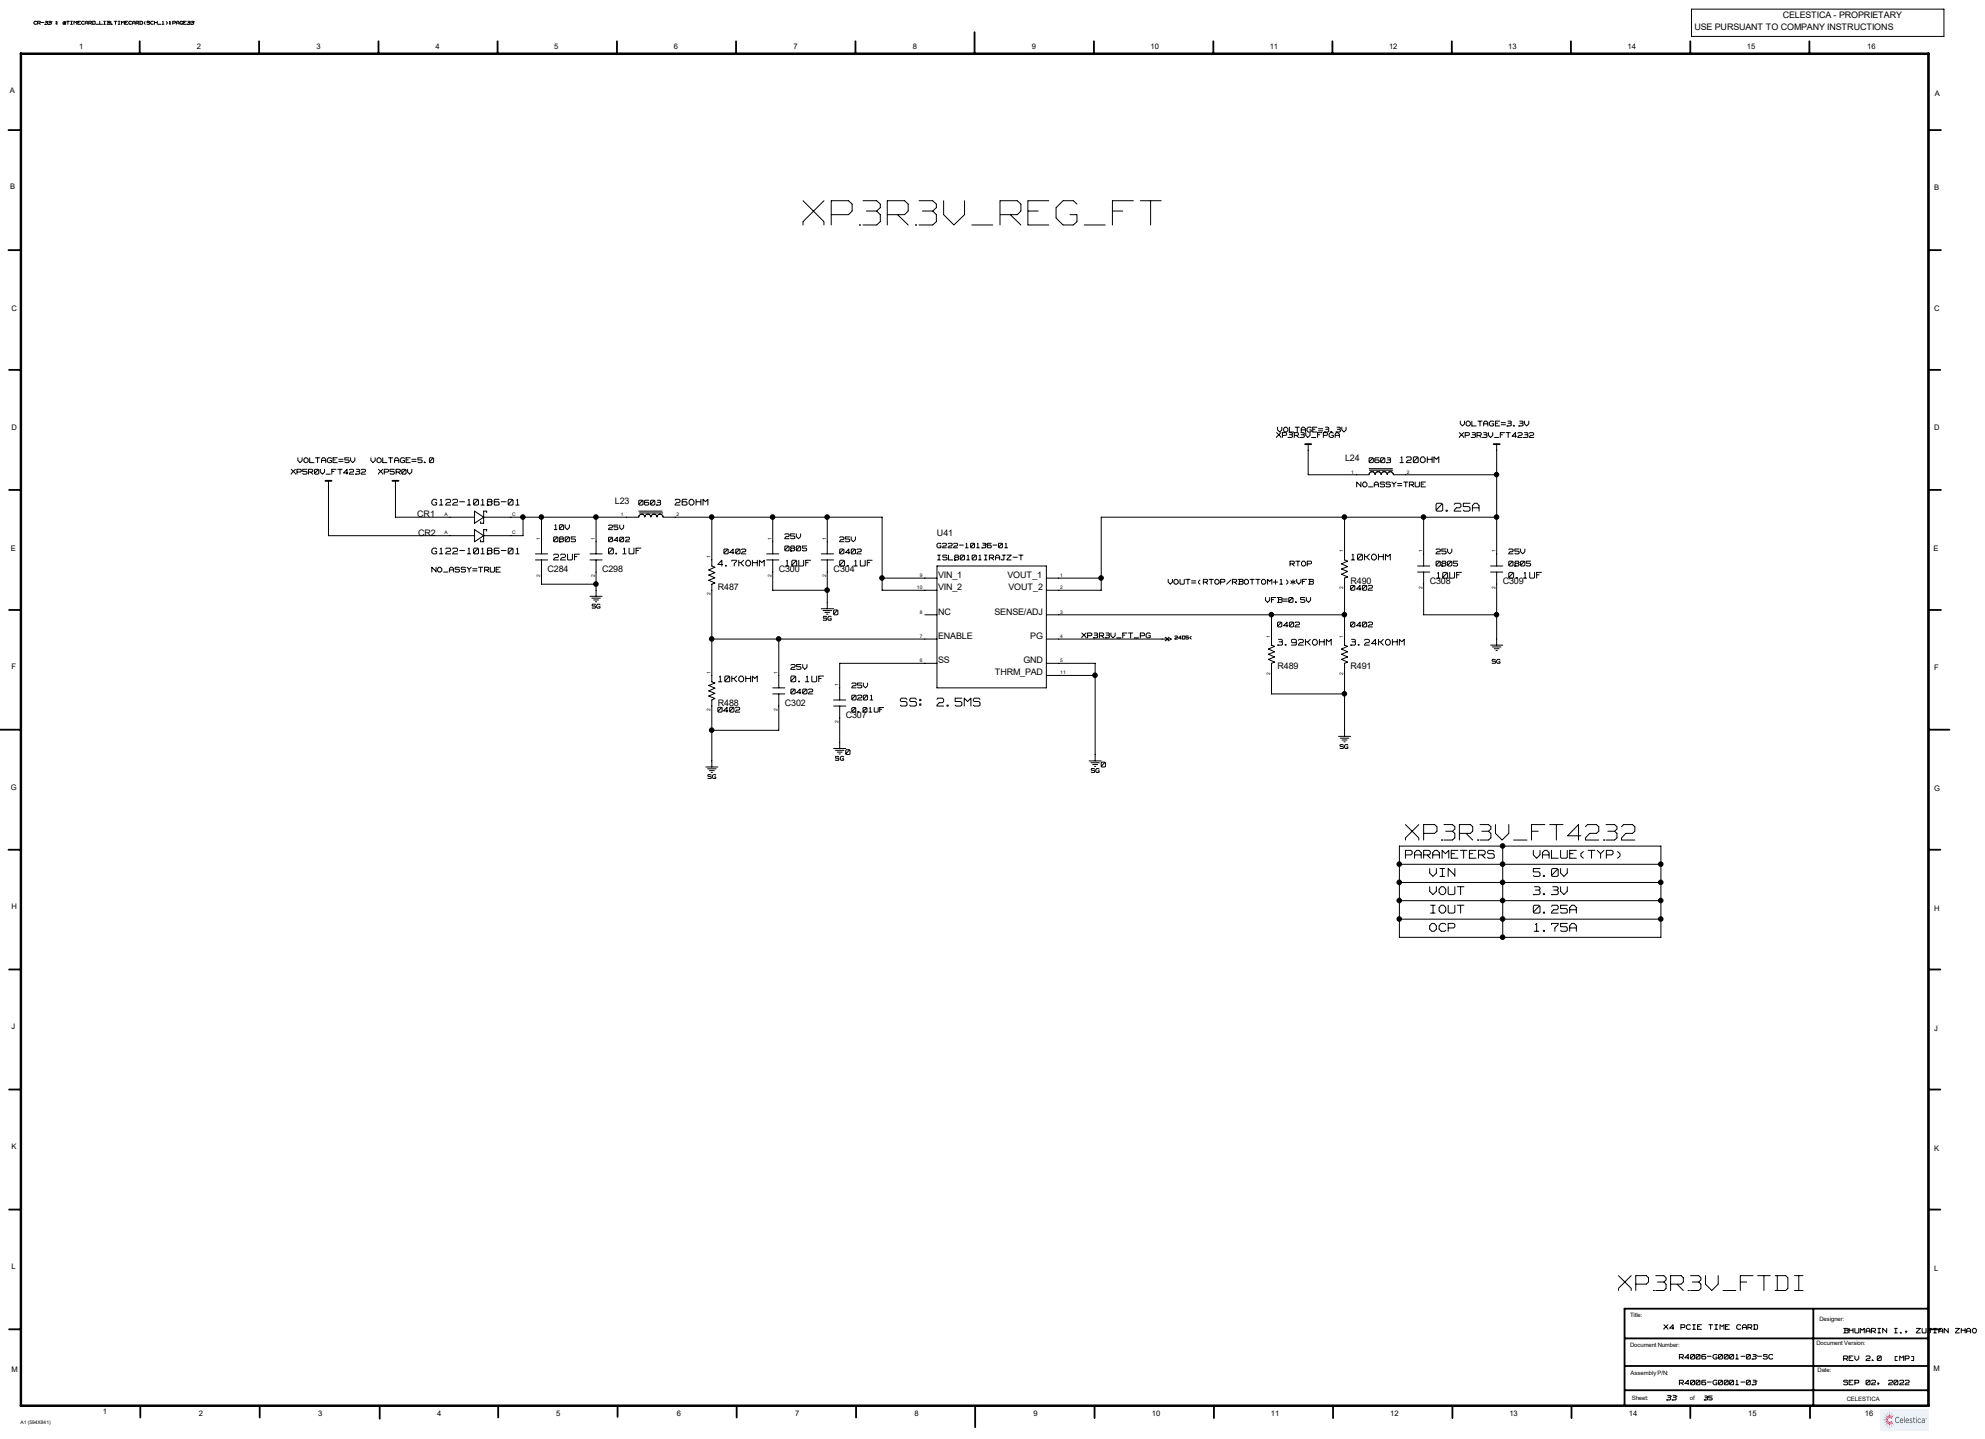
[picture p271: page 33]

VOUT=(RTOP/RBOTTOM+1)*VFB

Title: | Designer:

Document Number: R4006-G0001-03-SC | Document Version:

STANDOFFS FOR GPS MODULE.

MOUNTING HOLES FOR MAC MODULE.

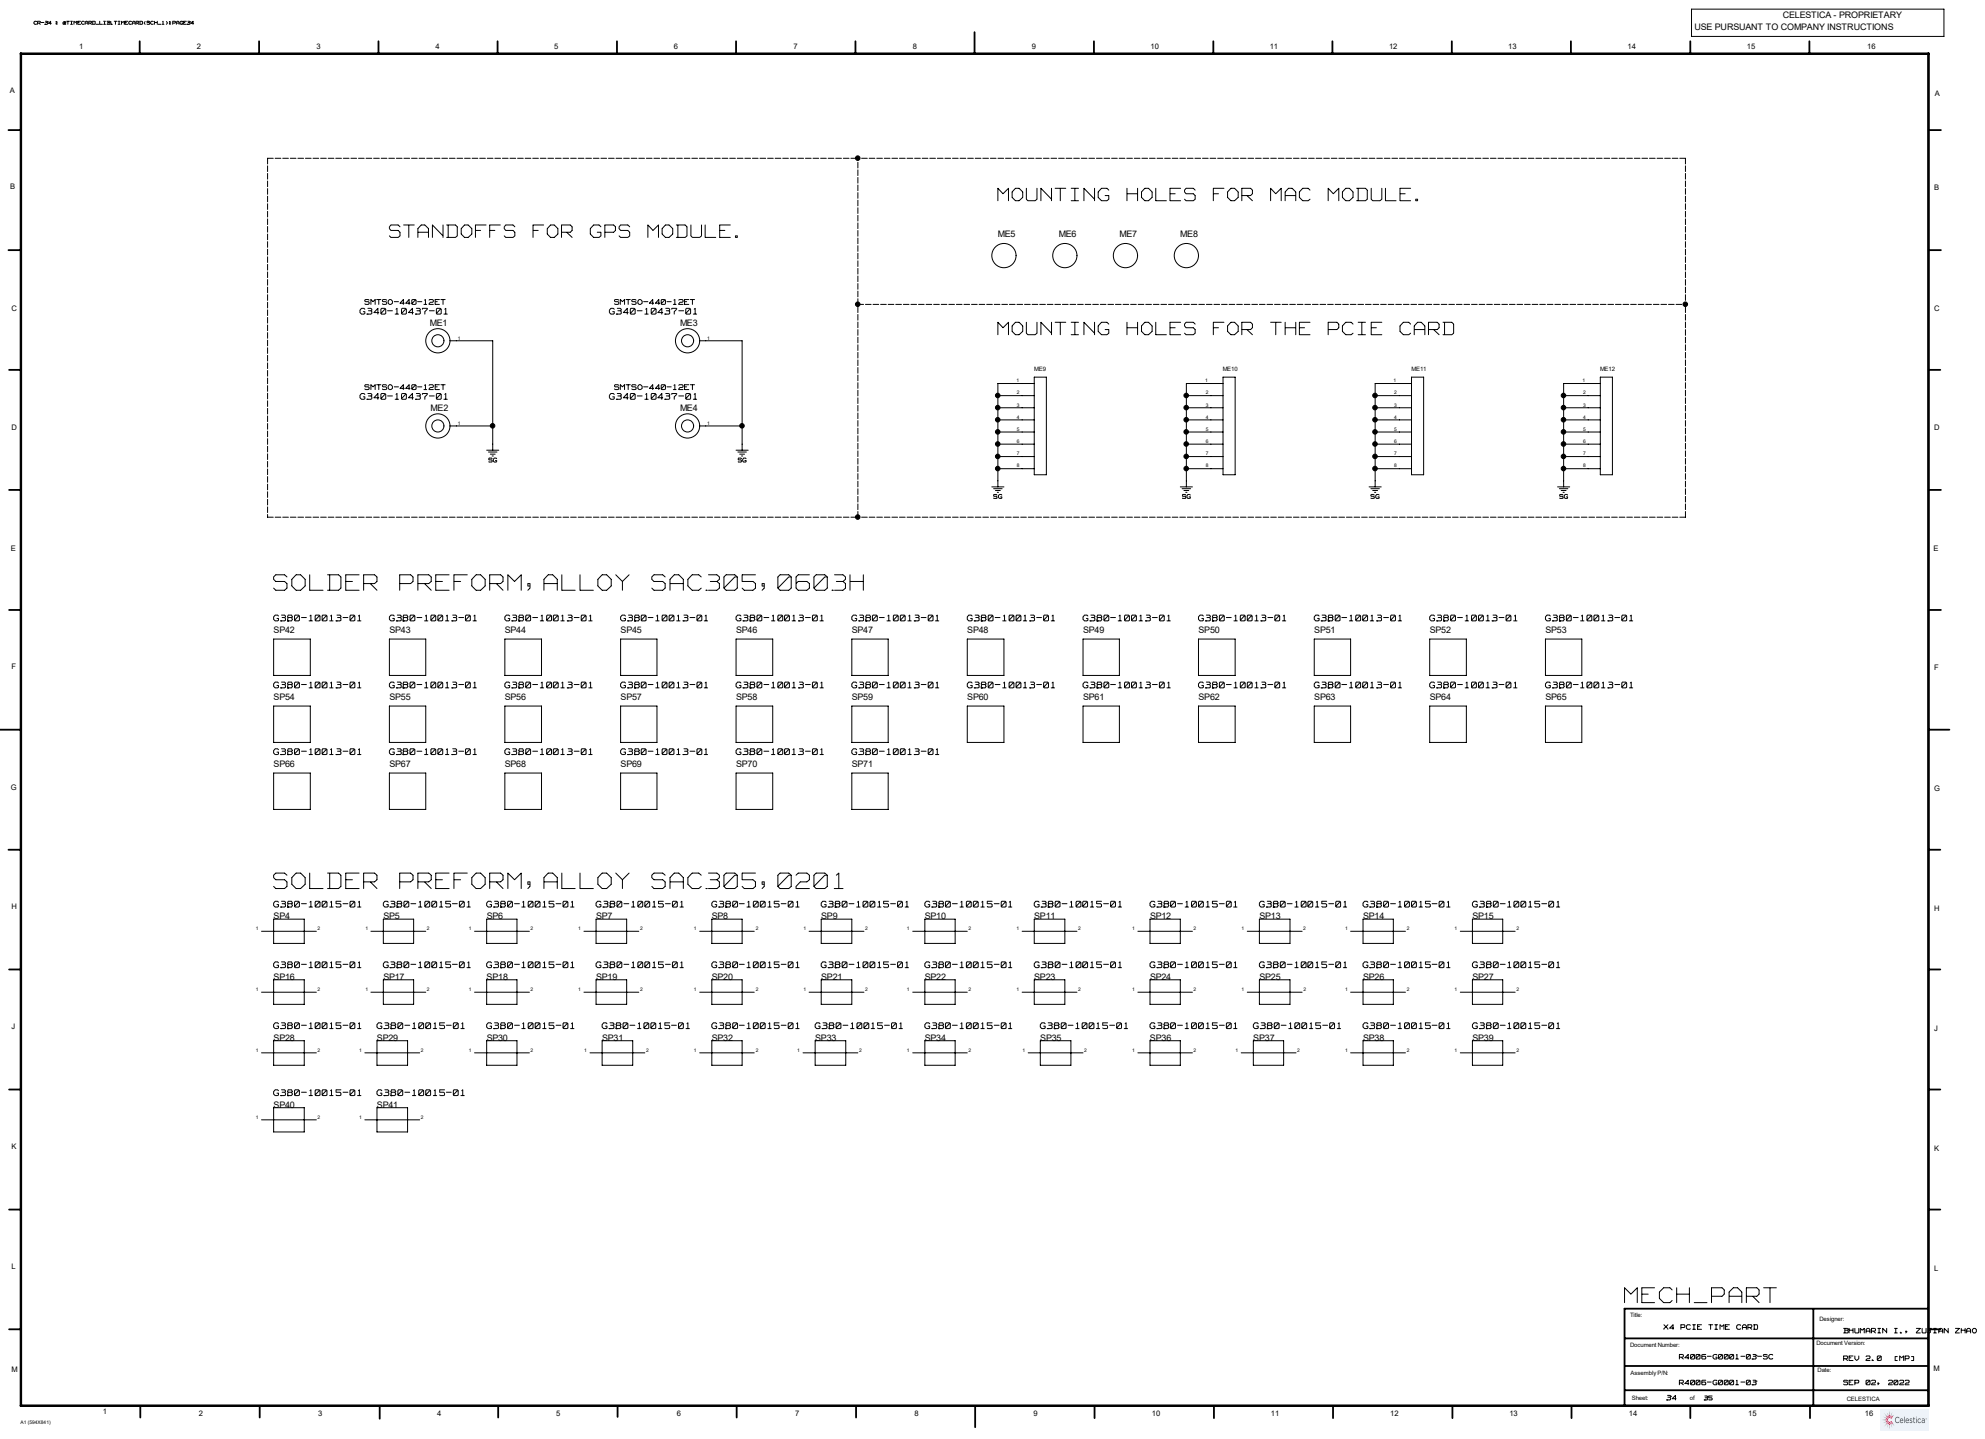
[picture p272: page 34]
CR-34 : @TIMECARD_LIB.TIMECARD(SCH_1):PAGE34; X4 PCIE TIME CARD; BHUMARIN I., ZUJIAN ZHAO; SMTSO-440-12ET; SMTSO-440-12ET G340-10437-01; MECH_PART

MOUNTING HOLES FOR THE PCIE CARD

SOLDER PREFORM,ALLOY SAC305,0603H

SOLDER PREFORM,ALLOY SAC305,0201

Title: | Designer:

Document Number: R4006-G0001-03-SC | Document Version:

## R4006-G0001-01-SC

## CR-35 : @TIMECARD_LIB.TIMECARD(SCH_1):PAGE35

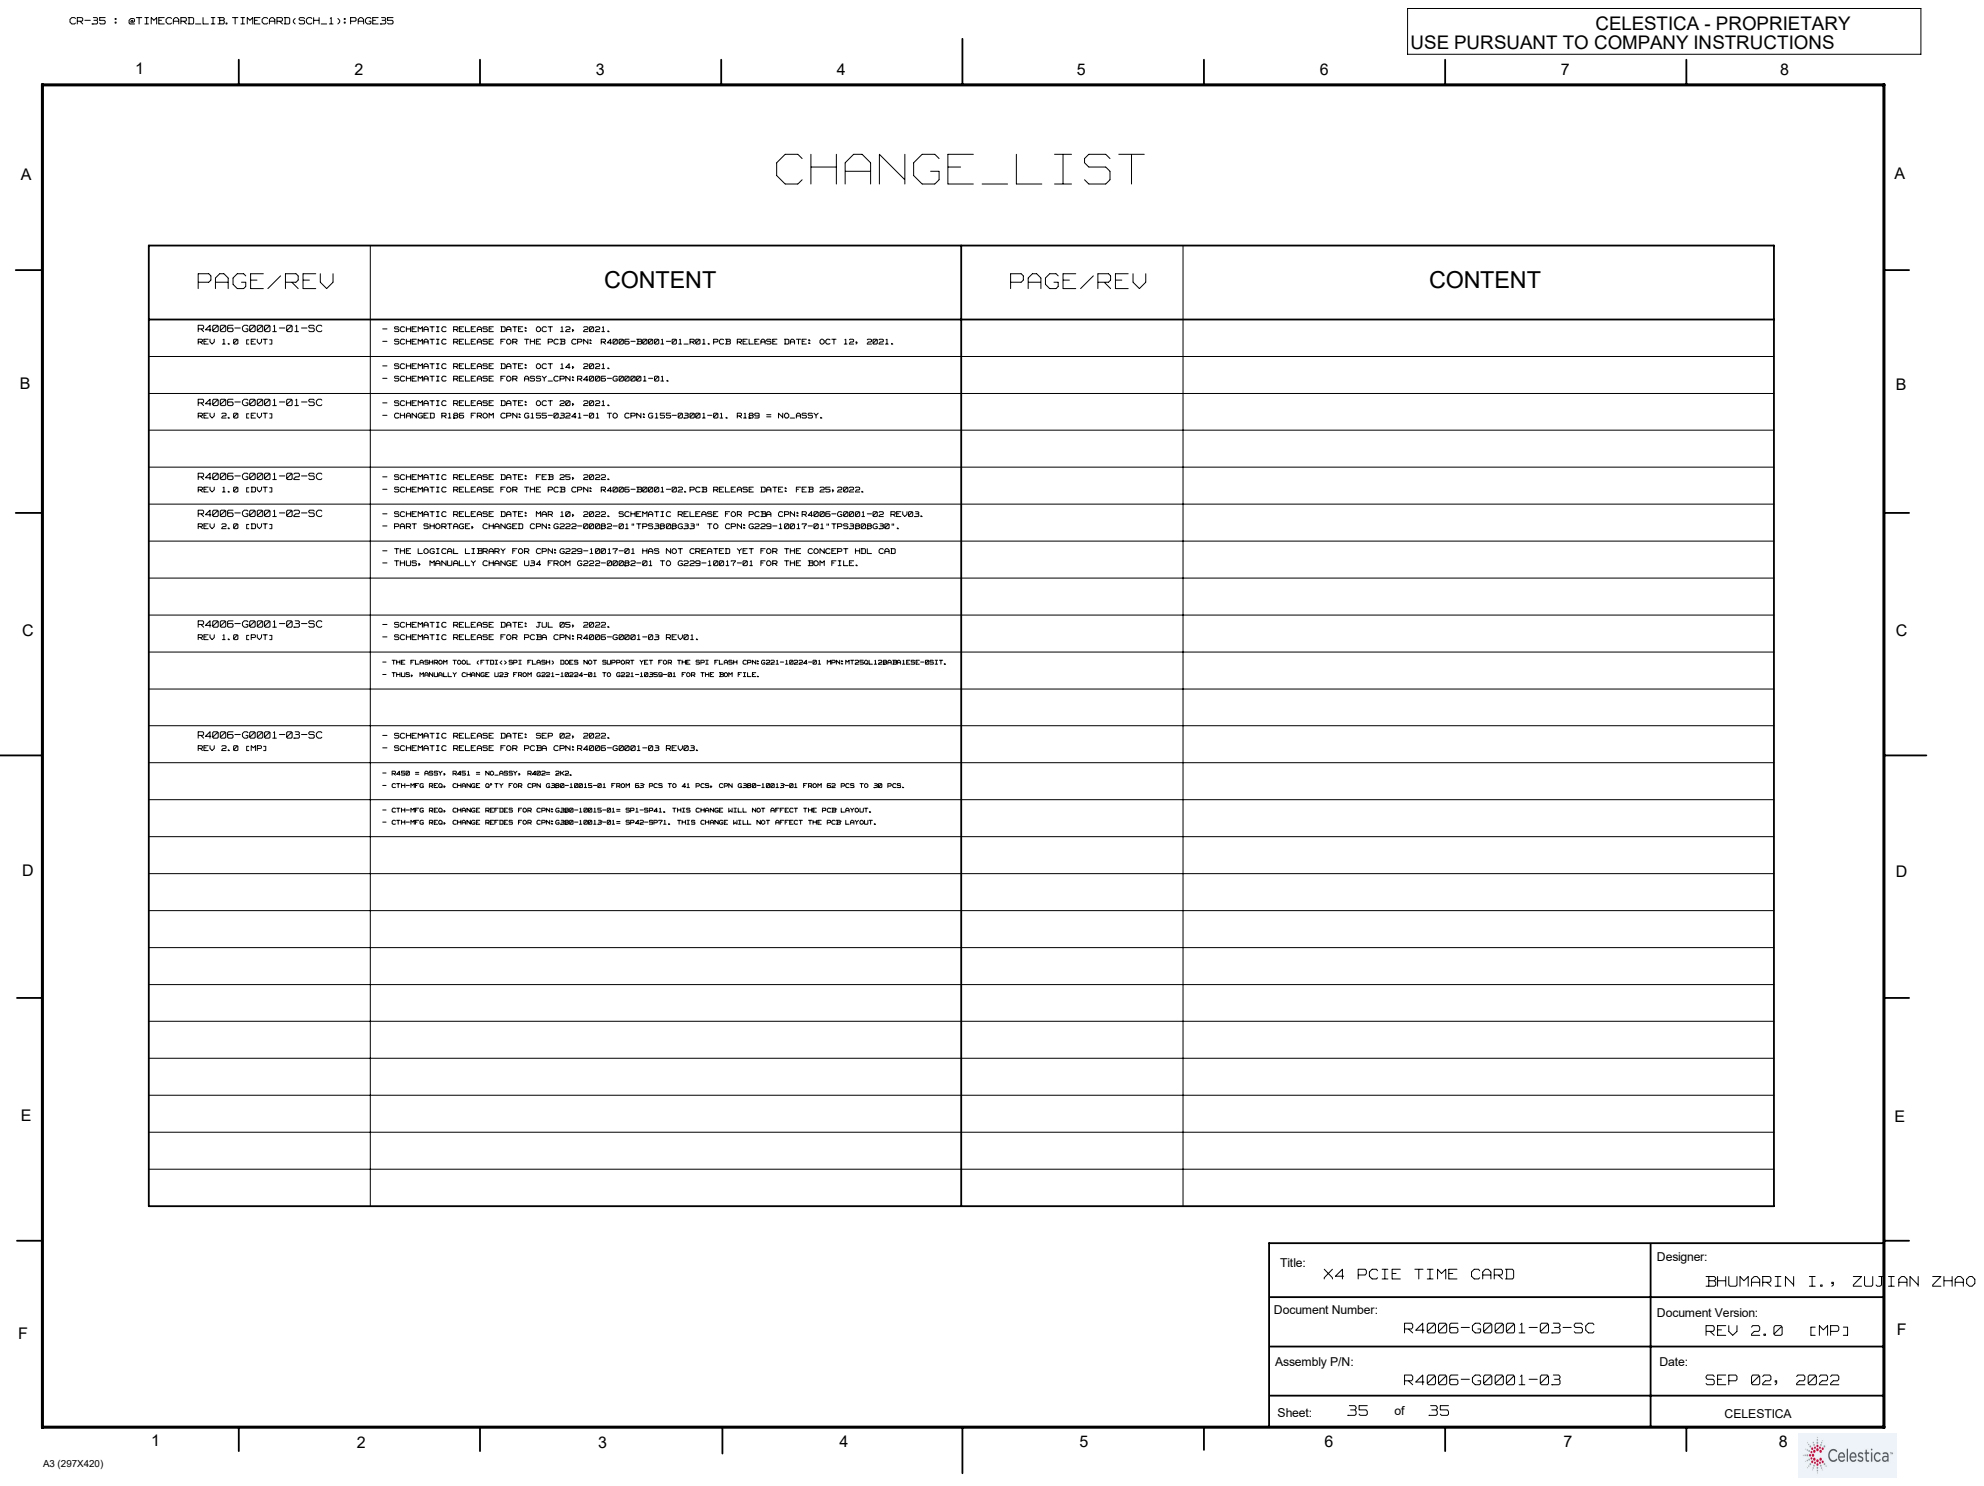
[picture p273: page 35]
REV 2.0 [EVT]; - CHANGED R186 FROM CPN:G155-03241-01 TO CPN:G155-03001-01. R189 = NO_ASSY.; REV 2.0 [MP]; REV 1.0 [PVT]; REV 2.0 [DVT]; REV 1.0 [EVT]; REV 1.0 [DVT]; CHANGE_LIST; PAGE/REV; CONTENT

- SCHEMATIC RELEASE DATE: OCT 12, 2021.
- SCHEMATIC RELEASE FOR THE PCB CPN: R4006-B0001-01_R01.PCB RELEASE DATE: OCT 12, 2021.

- SCHEMATIC RELEASE DATE: OCT 14, 2021.
- SCHEMATIC RELEASE FOR ASSY_CPN:R4006-G00001-01.

- SCHEMATIC RELEASE DATE: OCT 20, 2021.

- SCHEMATIC RELEASE DATE: FEB 25, 2022.
- SCHEMATIC RELEASE FOR THE PCB CPN: R4006-B0001-02.PCB RELEASE DATE: FEB 25,2022.

- SCHEMATIC RELEASE DATE: MAR 10, 2022. SCHEMATIC RELEASE FOR PCBA CPN:R4006-G0001-02 REV03.
- PART SHORTAGE, CHANGED CPN:G222-00082-01"TPS3808G33" TO CPN:G229-10017-01"TPS3808G30".

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

- SCHEMATIC RELEASE DATE: JUL 05, 2022.
- SCHEMATIC RELEASE FOR PCBA CPN:R4006-G0001-03 REV01.

- THE FLASHROM TOOL (FTDI<>SPI FLASH) DOES NOT SUPPORT YET FOR THE SPI FLASH CPN:G221-10224-01 MPN:MT25QL128ABA1ESE-0SIT.
- THUS, MANUALLY CHANGE U23 FROM G221-10224-01 TO G221-10359-01 FOR THE BOM FILE.

- SCHEMATIC RELEASE DATE: SEP 02, 2022.
- SCHEMATIC RELEASE FOR PCBA CPN:R4006-G0001-03 REV03.

- R450 = ASSY, R451 = NO_ASSY, R402= 2K2.
- CTH-MFG REQ, CHANGE Q'TY FOR CPN G380-10015-01 FROM 63 PCS TO 41 PCS, CPN G380-10013-01 FROM 62 PCS TO 30 PCS.

- CTH-MFG REQ, CHANGE REFDES FOR CPN:G380-10015-01= SP1-SP41. THIS CHANGE WILL NOT AFFECT THE PCB LAYOUT.
- CTH-MFG REQ, CHANGE REFDES FOR CPN:G380-10013-01= SP42-SP71. THIS CHANGE WILL NOT AFFECT THE PCB LAYOUT.

Title: X4 PCIE TIME CARD | Designer:

BHUMARIN I., ZUJIAN ZHAO

Document Number: R4006-G0001-03-SC | Document Version: REV 2.0 [MP]

Assembly P/N: R4006-G0001-03 | Date: SEP 02, 2022

Sheet: 35 35 of
