opencomputeproject/Time-Appliance-Project/GNSS/UBlox/M2-ZED-F9T/M2_ZED-F9T_MODULE.pdf

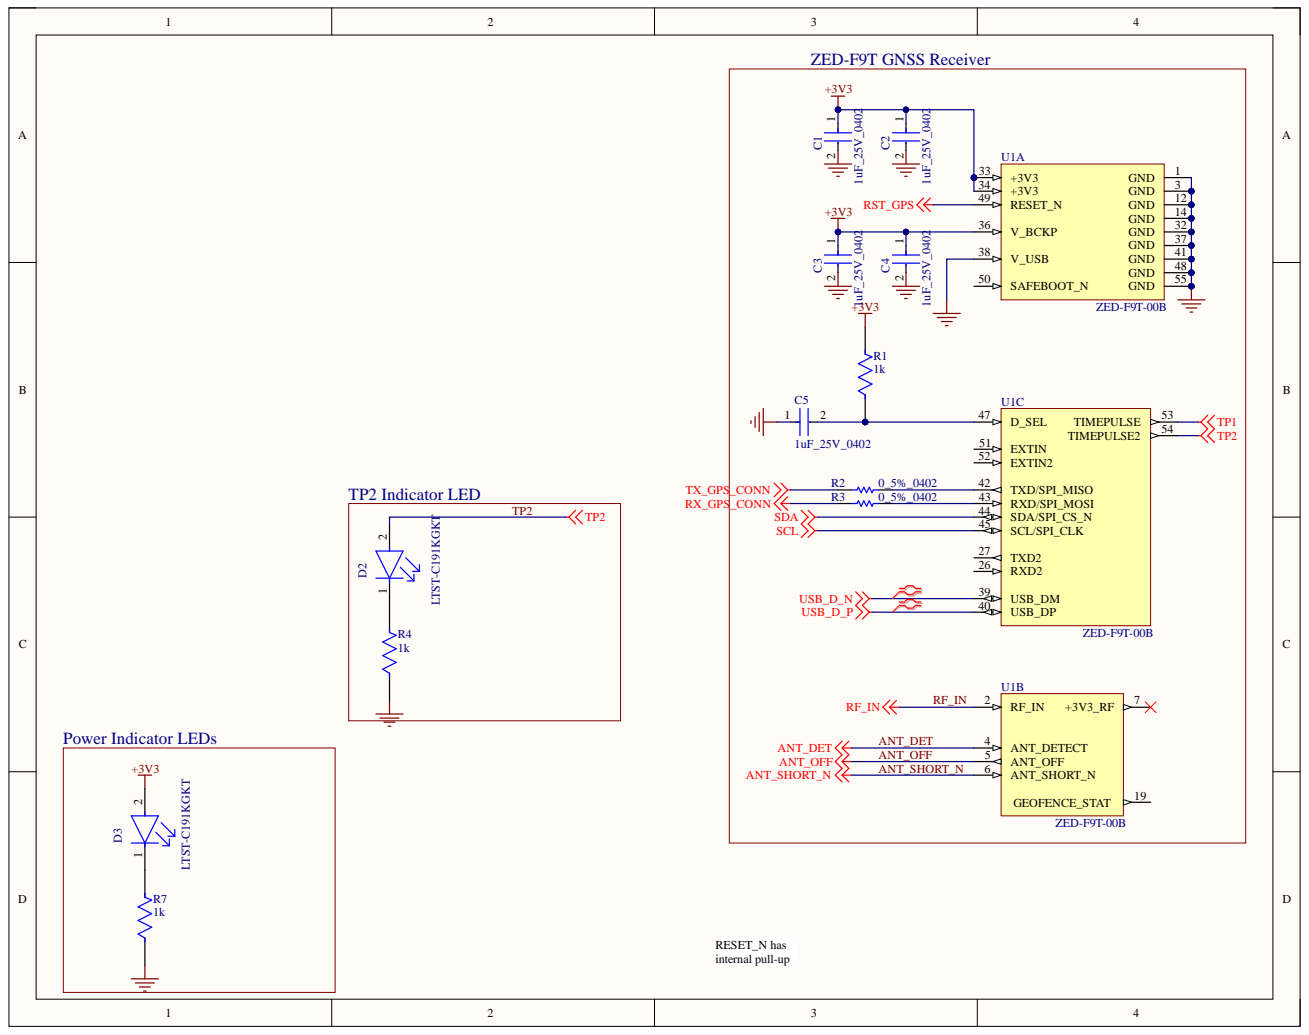
[picture p274: page 1]

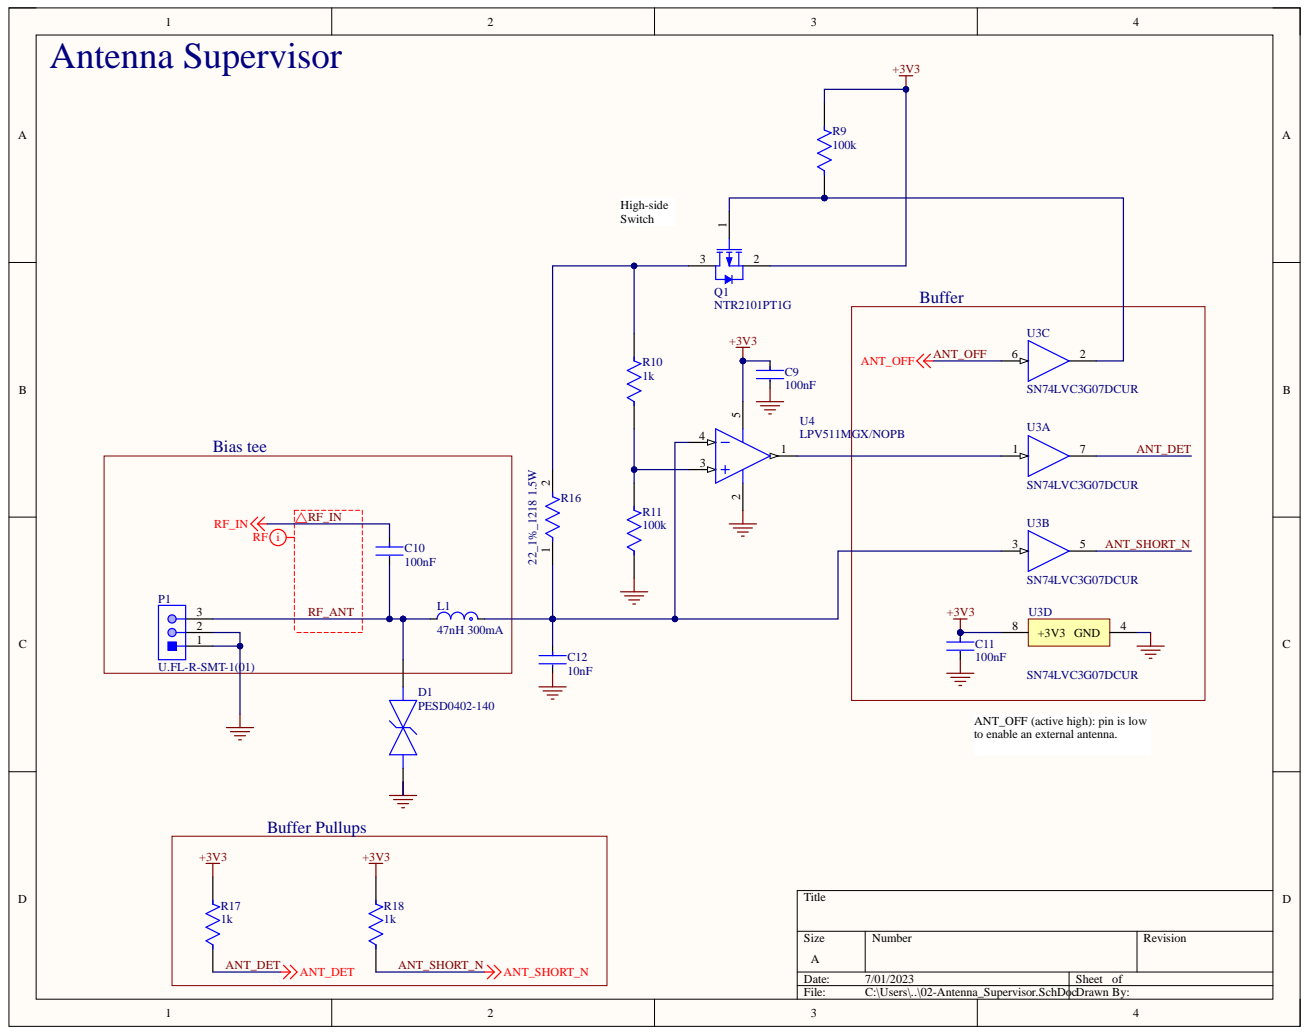
[picture p275: page 2]

RF_ANT

ANT_OFF (active high): pin is low
to enable an external antenna.

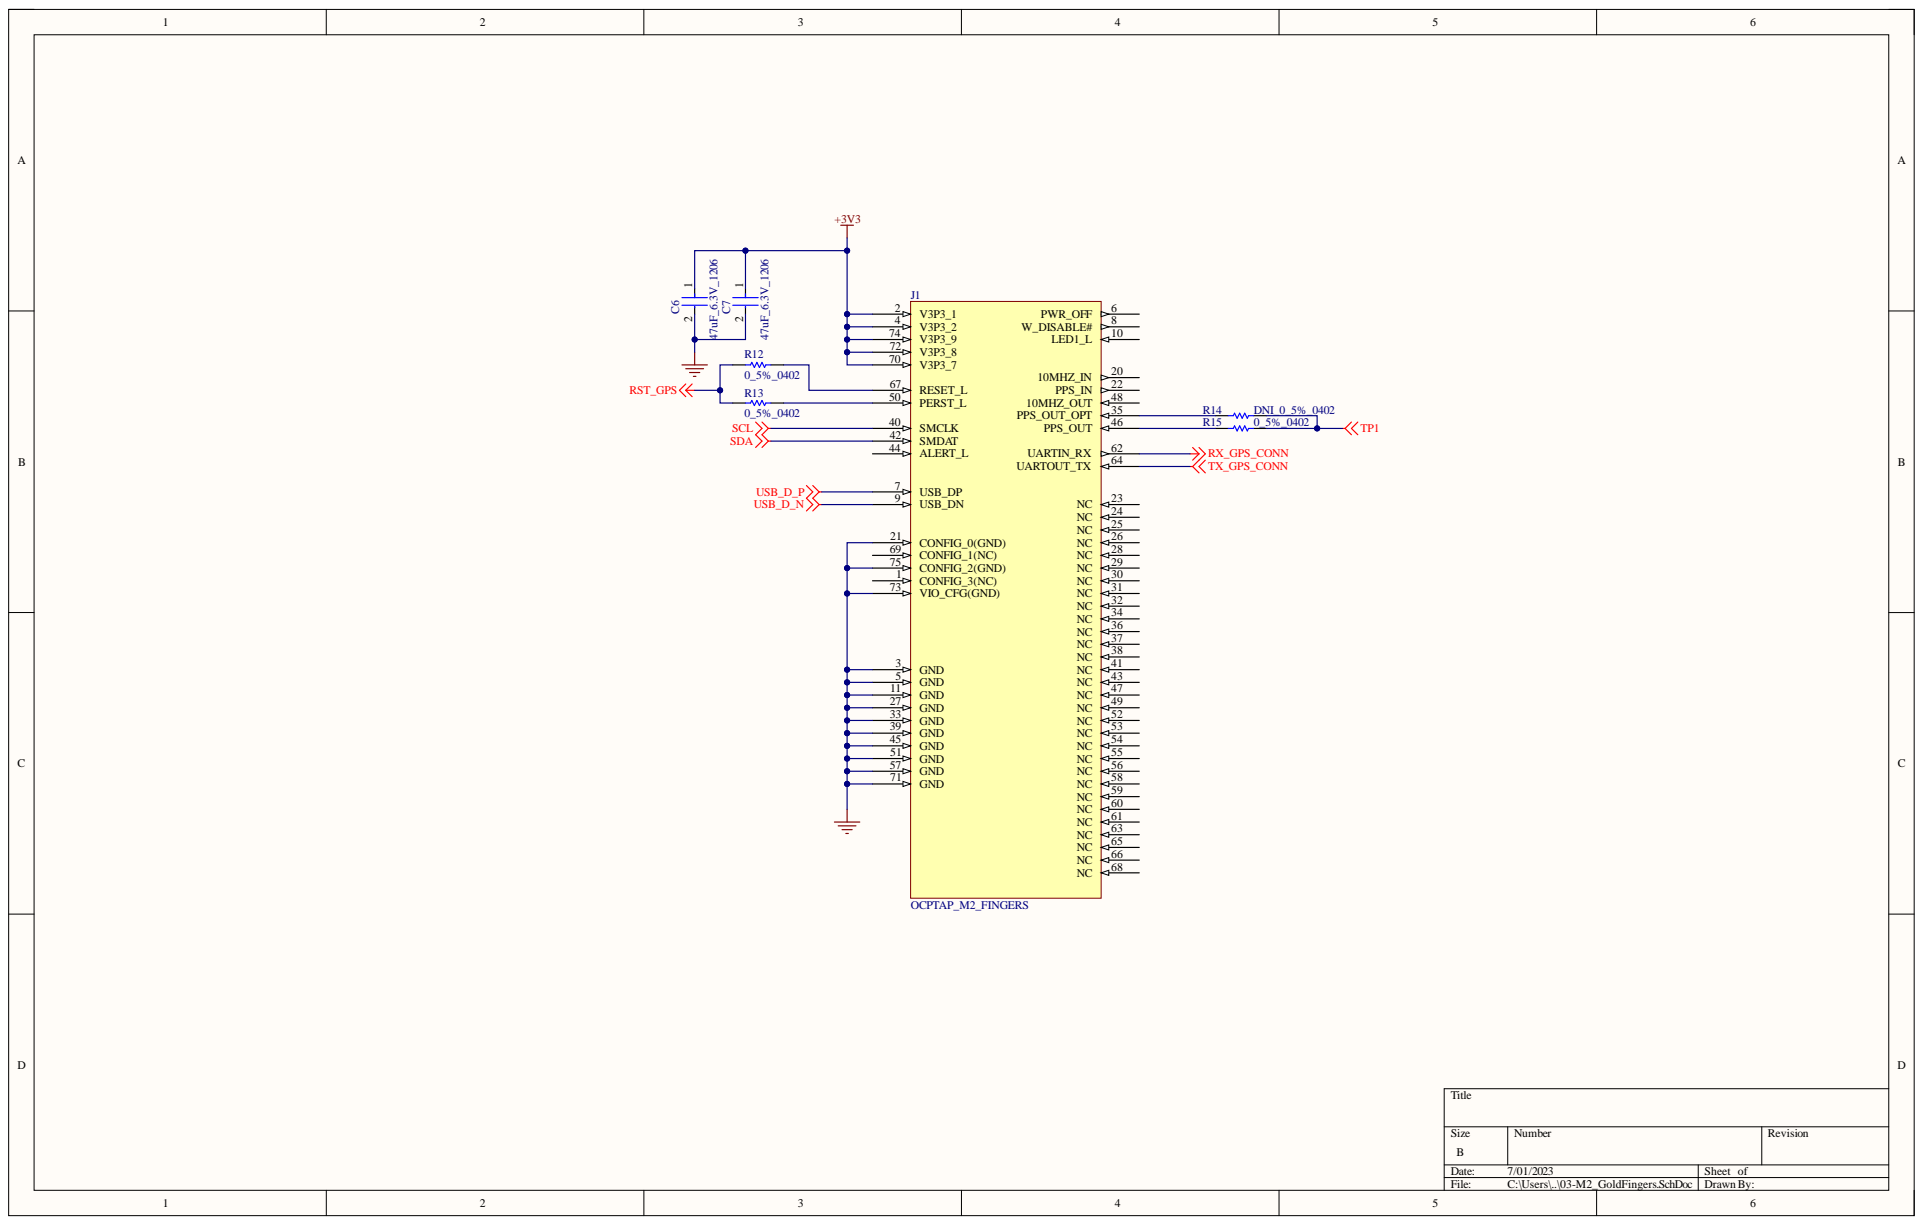
[picture p276: page 3]

CONFIG_1(NC) 69

CONFIG_3(NC) 1

Size B | Number | Revision

Date: 7/01/2023 | Sheet of
File: C:\Users\..\03-M2_GoldFingers.SchDoc | Drawn By:
