opencomputeproject/Time-Appliance-Project/OSC/OCXO Daughtercard/ECAD/OCXO_DaughterCard.pdf

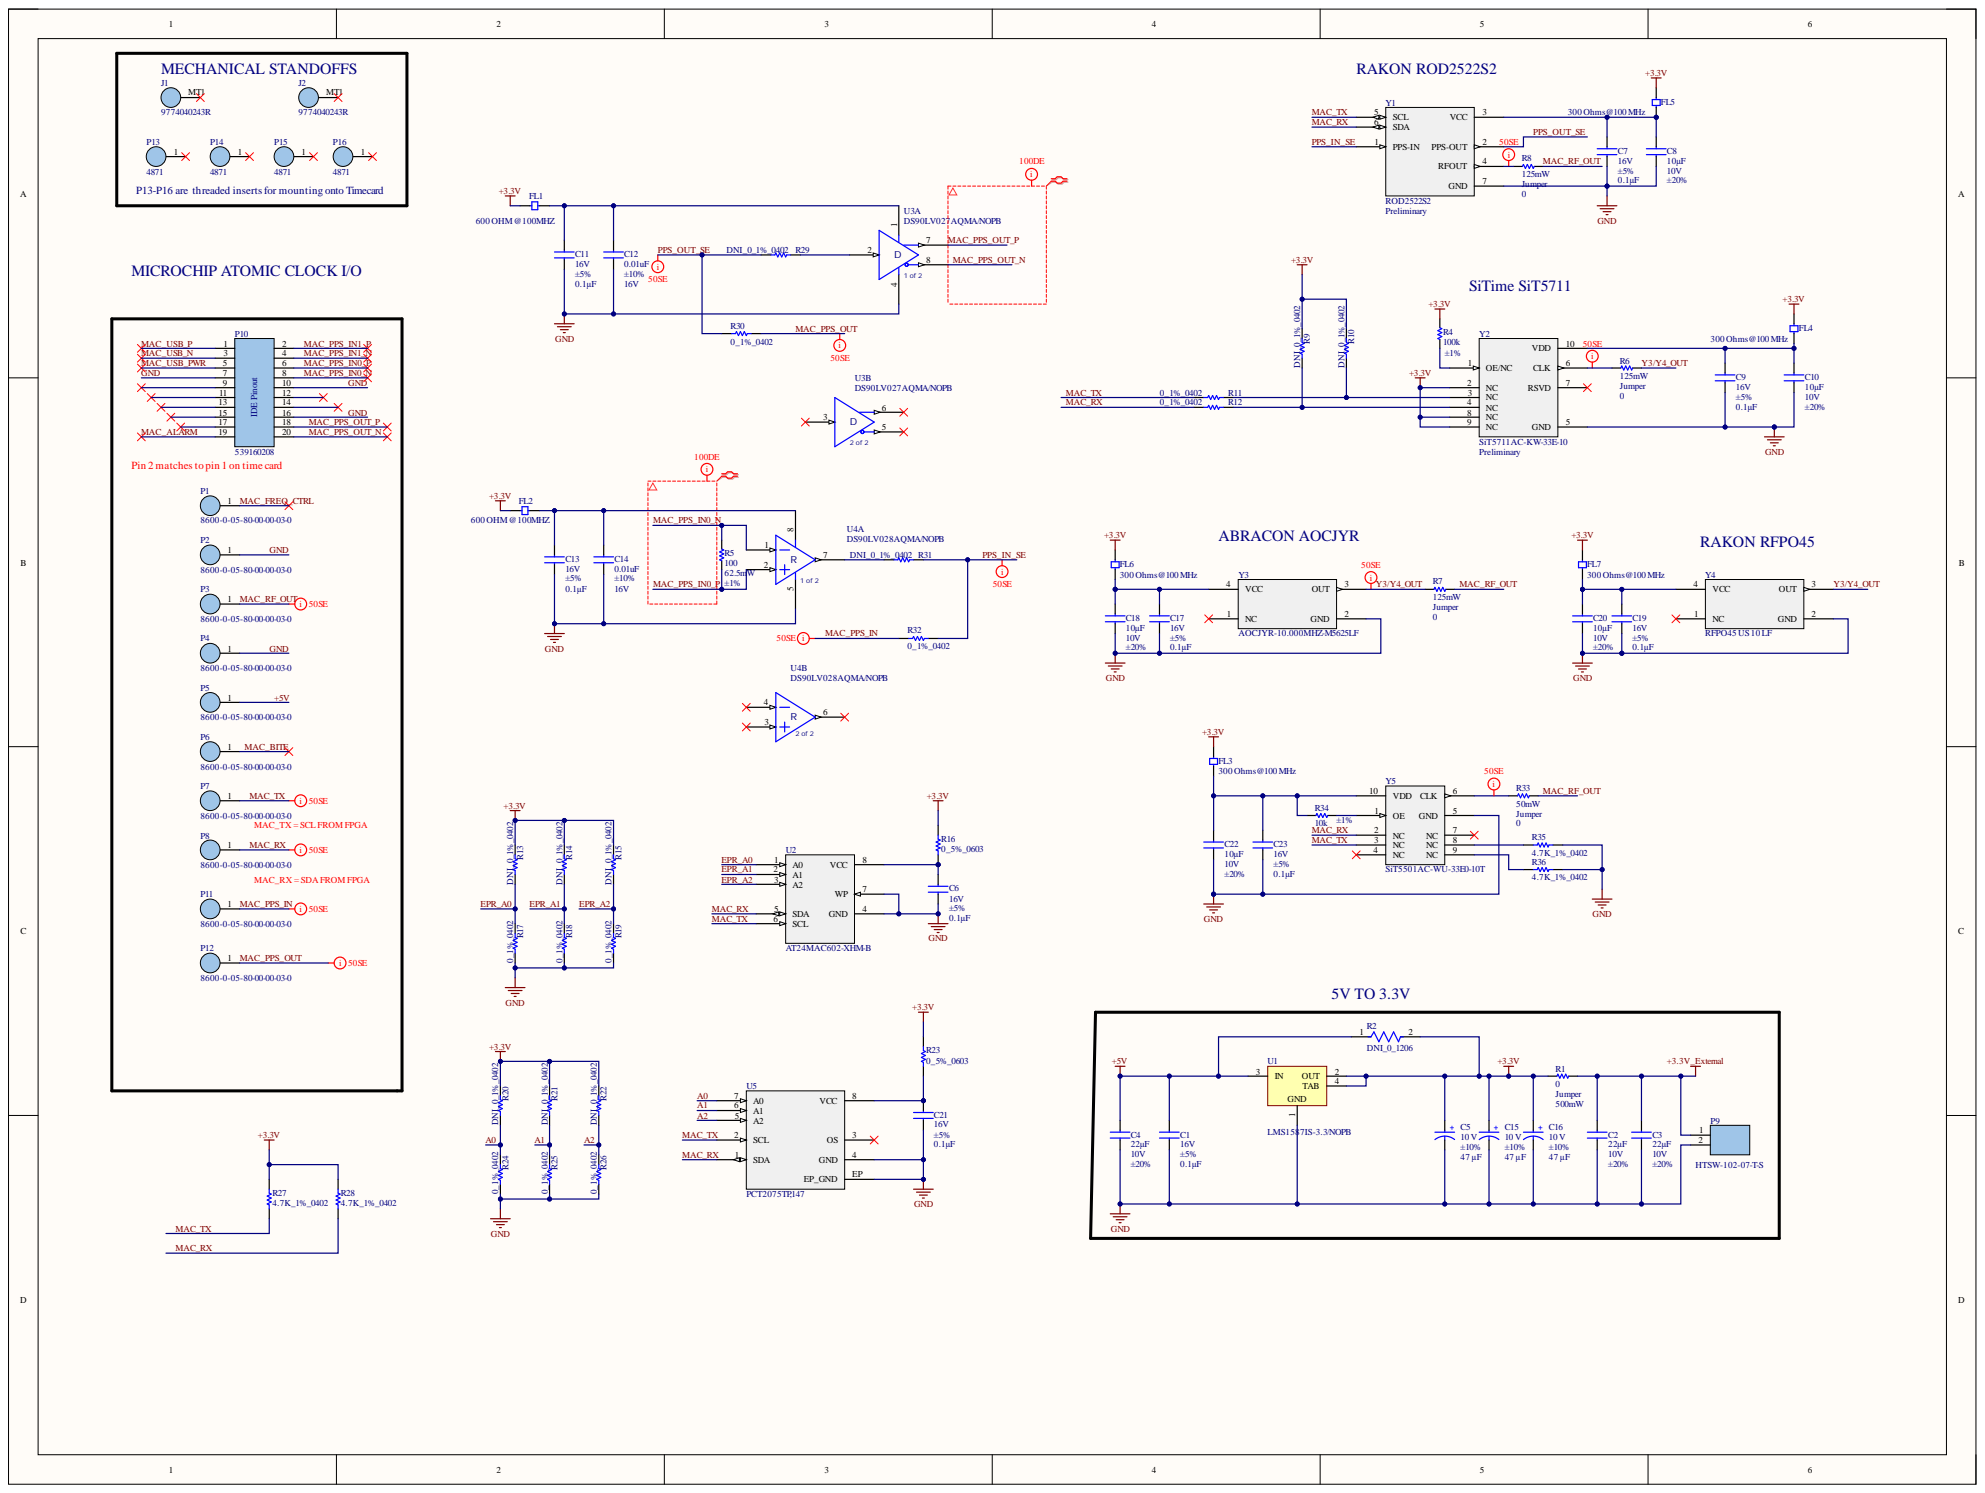
[picture p277: page 1]

P13-P16 are threaded inserts for mounting onto Timecard

Pin 2 matches to pin 1 on time card
