opencomputeproject/Time-Appliance-Project/HW/MCAD/PCIE Bracket V4/timecard_bracket_v4.pdf

A

1 | 2 | 3 | 4 | 5

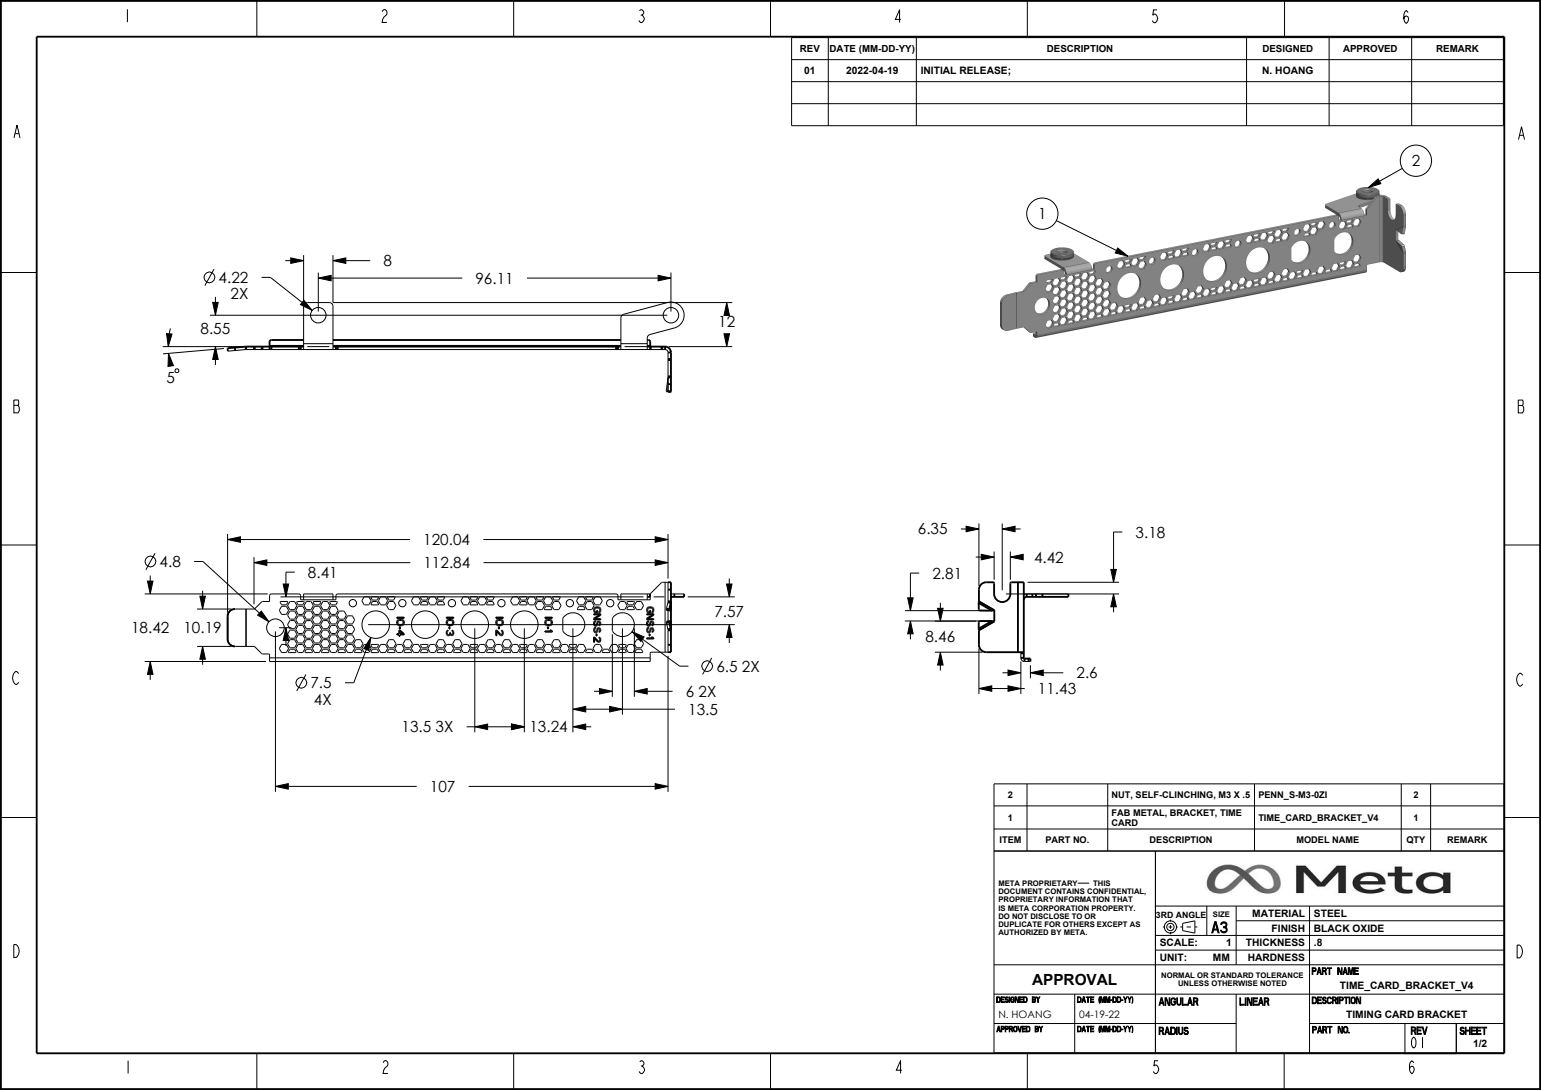
[picture p278: page 1]
PART; NAME; PART NO.; DESCRIPTION; ANGULAR; RADIUS; LINEAR DESIGNED; DATE (MM-DD-YY); REV

REV | DATE (MM-DD-YY) | DESCRIPTION | DESIGNED | APPROVED | REMARK
01 | 2022-04-19 | INITIAL RELEASE; | N. HOANG

2 | | NUT, SELF-CLINCHING, M3 X .5 | PENN_S-M3-0ZI | 2
1 FAB METAL, BRACKET, TIME | | CARD | TIME_CARD_BRACKET_V4 | 1

ITEM | PART NO. | DESCRIPTION | MODEL NAME | QTY | REMARK

META PROPRIETARY THIS DOCUMENT CONTAINS CONFIDENTIAL, PROPRIETARY INFORMATION THAT IS META CORPORATION PROPERTY. DO NOT DISCLOSE TO OR DUPLICATE FOR OTHERS EXCEPT AS AUTHORIZED BY META.

3RD ANGLE | SIZE A3 | MATERIAL | STEEL

FINISH | BLACK OXIDE

SCALE: 1 | | THICKNESS | .8
UNIT: MM | | HARDNESS

APPROVAL | NORMAL OR STANDARD TOLERANCE UNLESS OTHERWISE NOTED | TIME_CARD_BRACKET_V4

DATE (MM-DD-YY)

N. HOANG | 04-19-22 | | | TIMING CARD BRACKET
APPROVED BY | | | | | 01 | SHEET 1/2

A

1 | 2 | 3 | 4 | 5

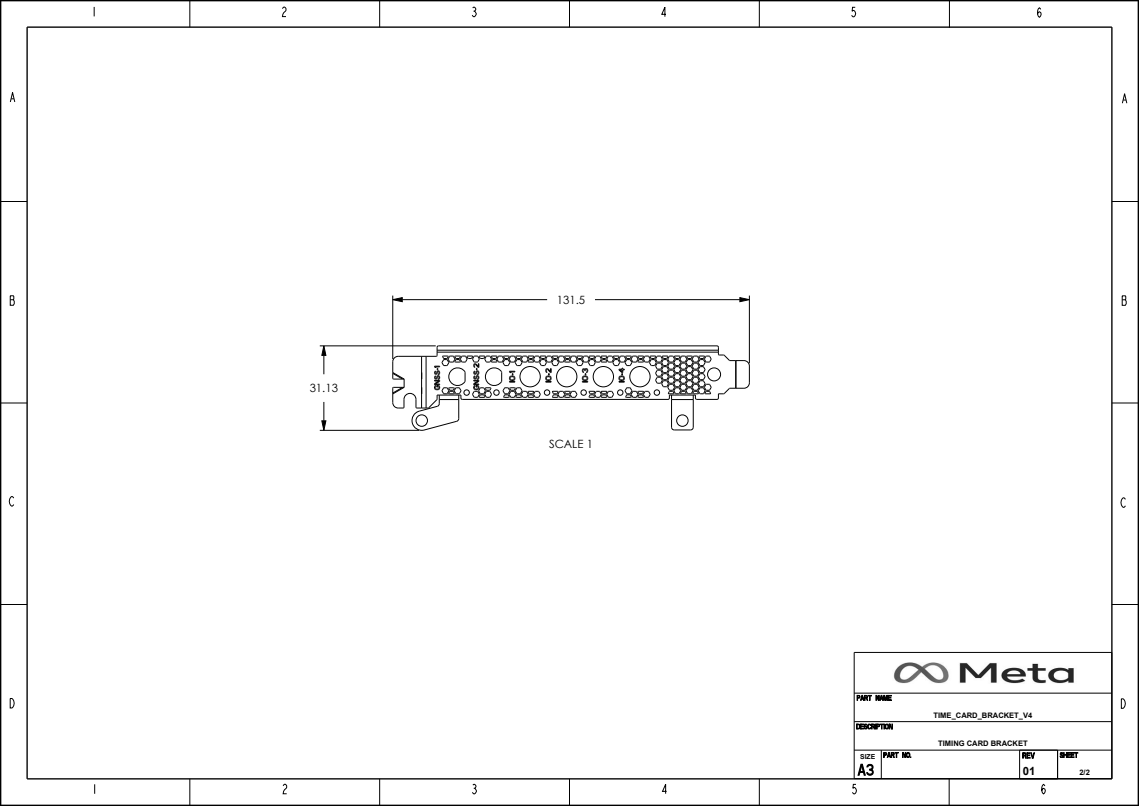
[picture p279: page 2]
DESCRIPTION; PART; PART NAME; SHEET; REV; TIME_CARD_BRACKET_V4; SIZE; SCALE 1

TIMING CARD BRACKET
