opencomputeproject/Time-Appliance-Project/OSC/Microchip/SA45/Latest/SCH_SA45_DaughterCard.pdf

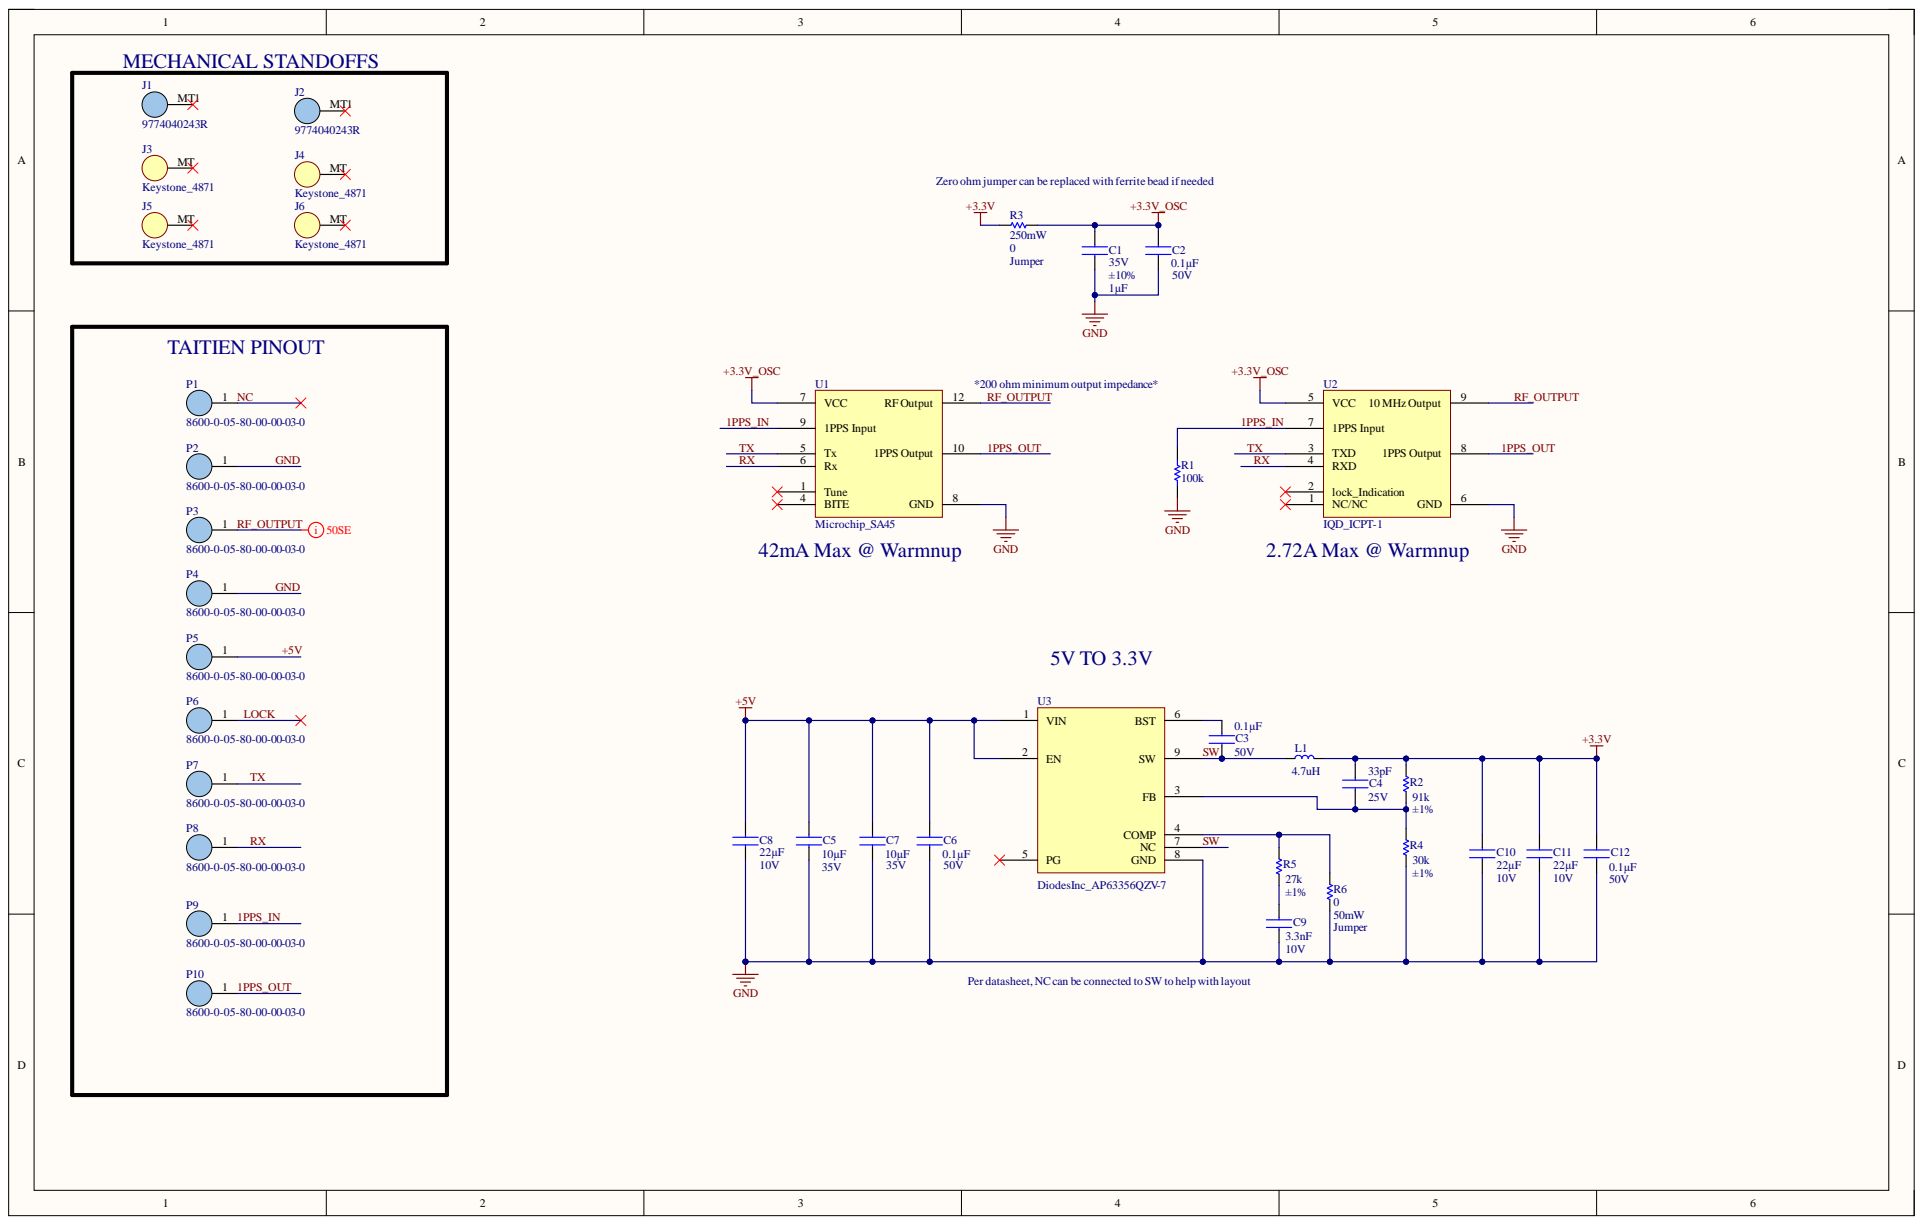
[picture p280: page 1]

Zero ohm jumper can be replaced with ferrite bead if needed

*200 ohm minimum output impedance*
RF_OUTPUT

Per datasheet, NCcan be connected to SW to help with layout
