opencomputeproject/Time-Appliance-Project/GNSS/UBlox/RCB-F9T/Altium/GPS_MODULE_ZED-F9T-00B.pdf

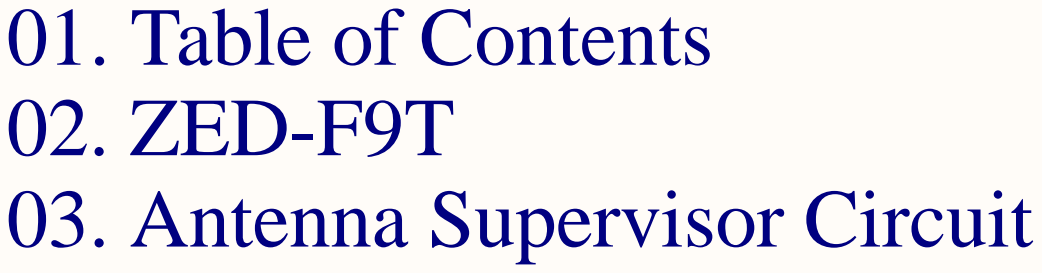
[picture p281: page 1]

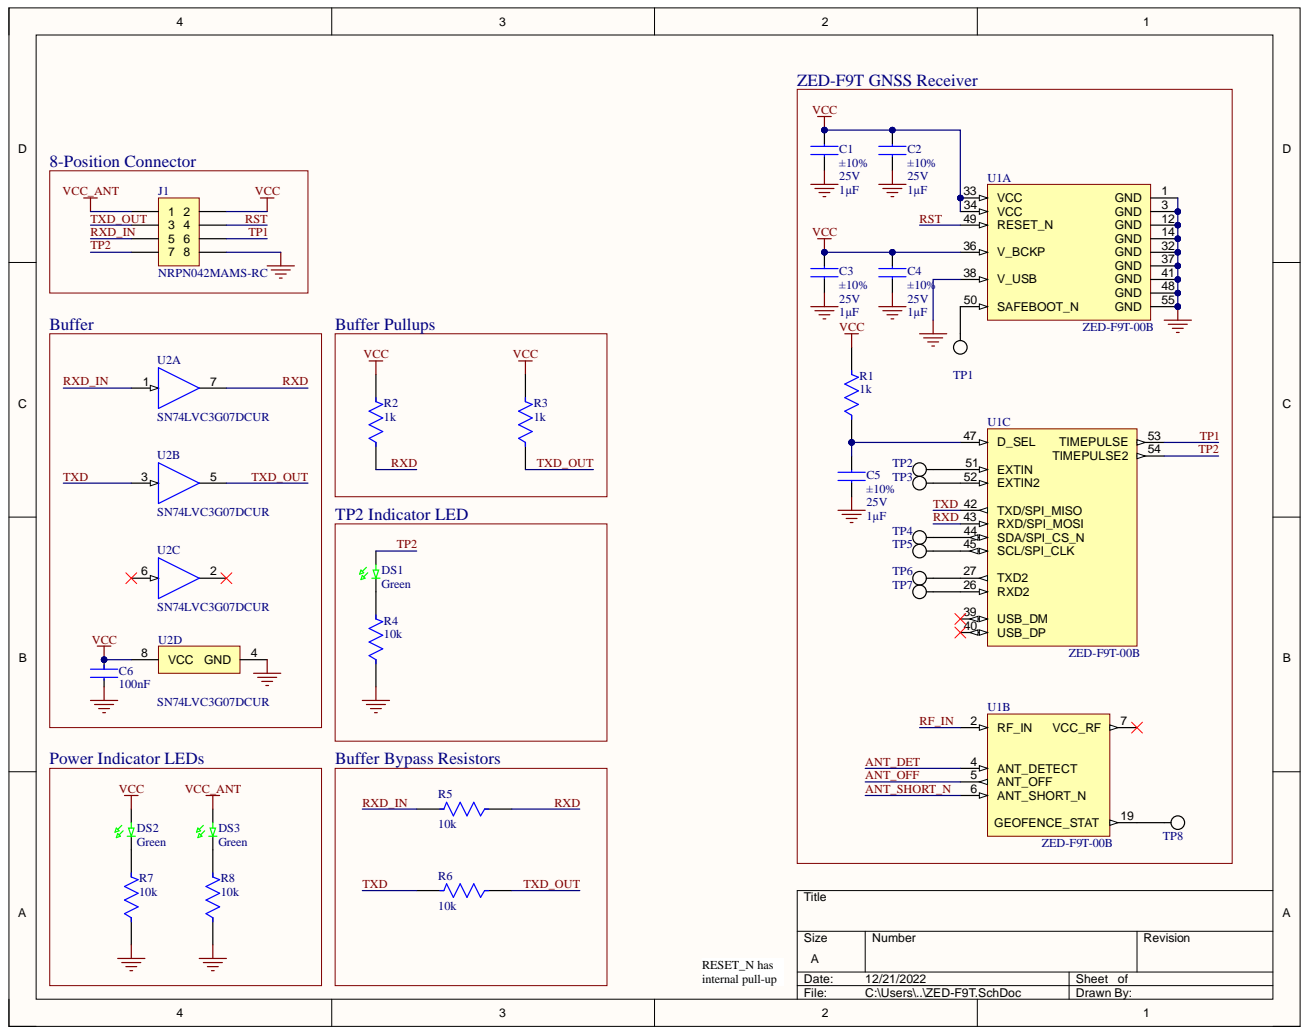
[picture p282: page 2]

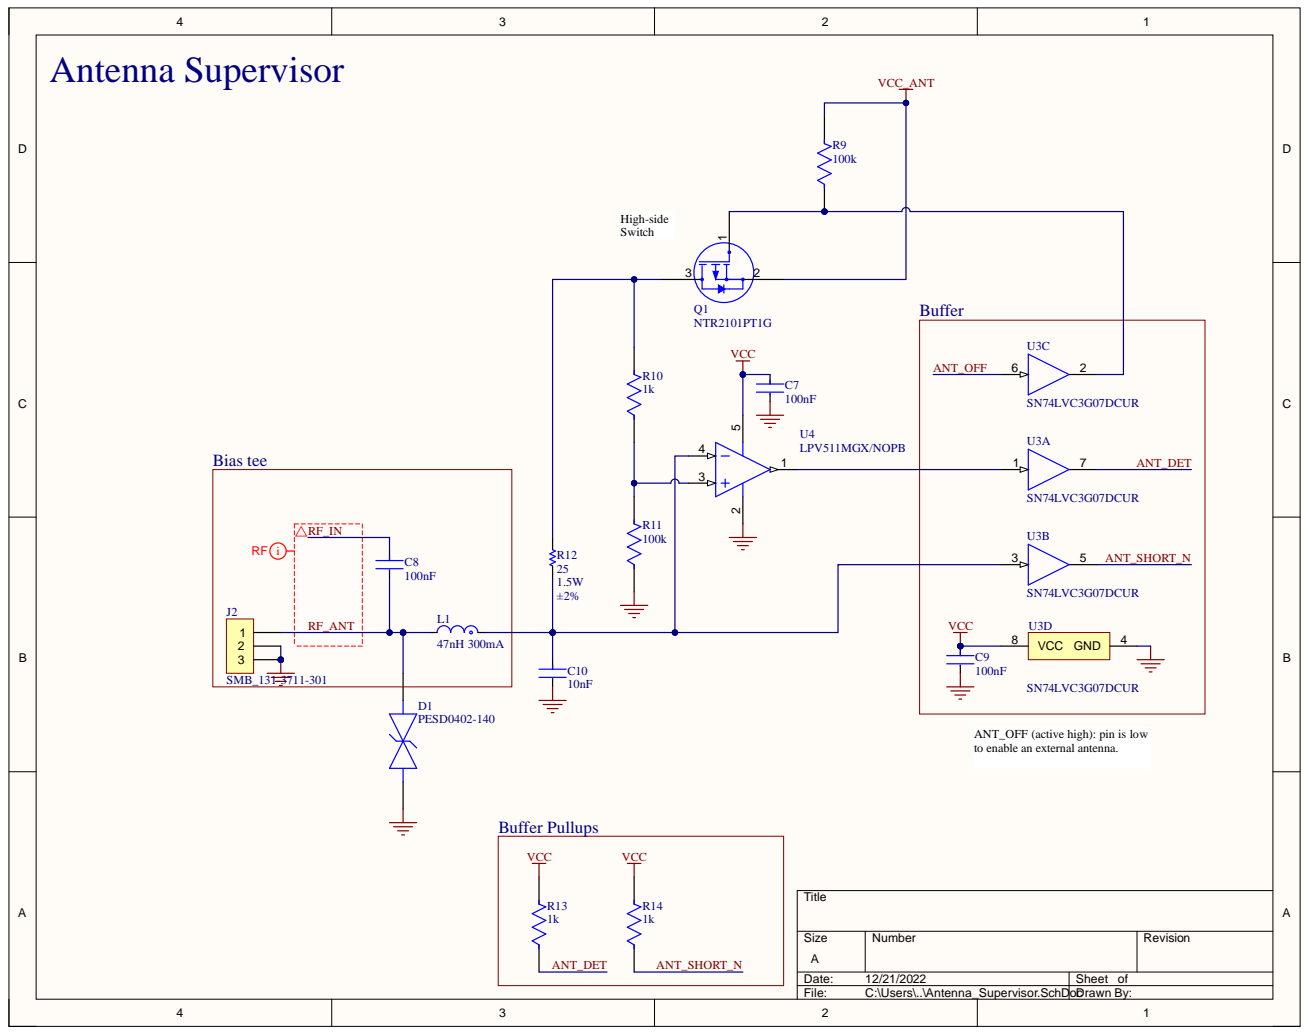
[picture p283: page 3]

ANT_OFF (active high): pin is low
to enable an external antenna.
