opencomputeproject/Time-Appliance-Project/Time-Card/HW/MCAD/PCIe Bracket V3/PCIe Bracket for Timing Card V3.pdf

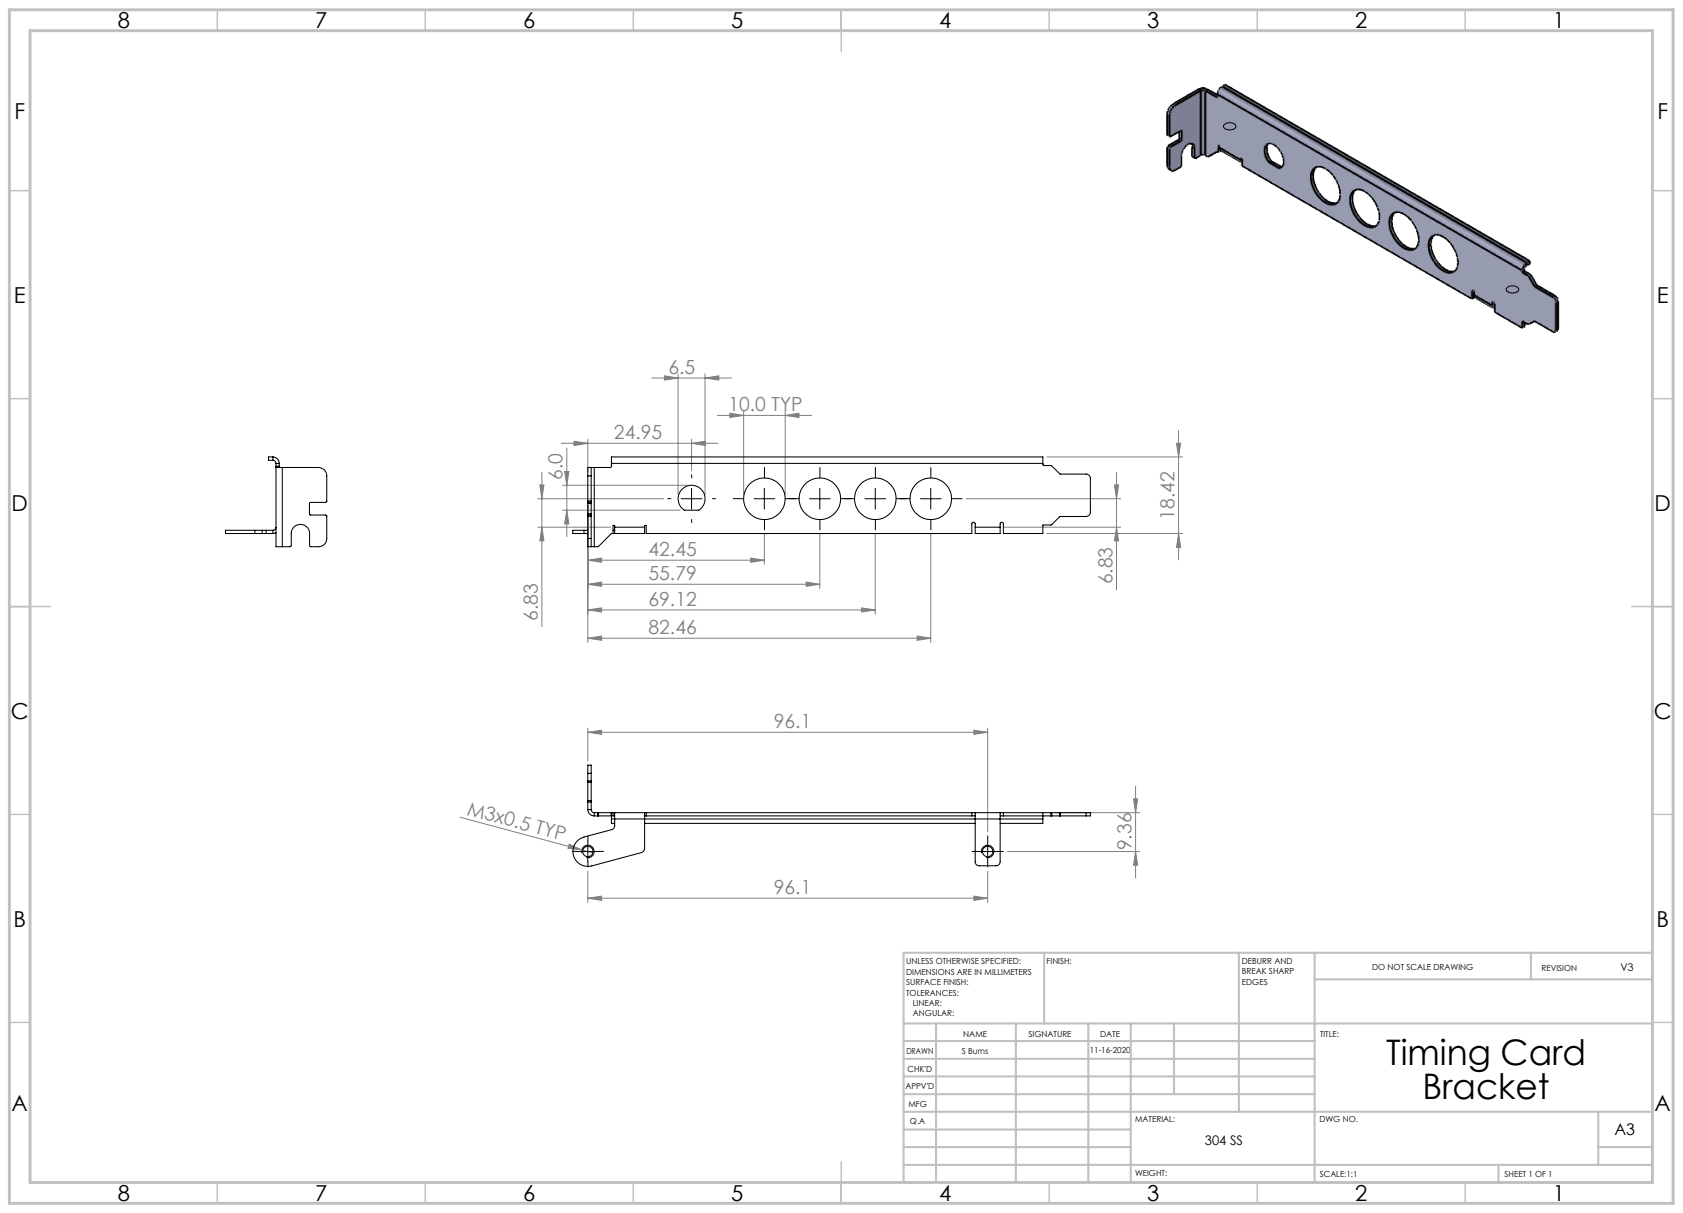
[picture p284: page 1]
10.0 TYP; M3x0.5 TYP; FINISH:; DEBURR AND; BREAK SHARP; DO NOT SCALE DRAWING; REVISION; SCALE:1:1; SHEET 1 OF 1

UNLESS OTHERWISE SPECIFIED:
DIMENSIONS ARE IN MILLIMETERS
SURFACE FINISH:
TOLERANCES:
LINEAR:
ANGULAR:

DRAWN | S Burns | | 11-16-2020

NAME | SIGNATURE | DATE | | | | TITLE: Timing Card Bracket

CHK'D
APPV'D
MFG
Q.A | | | | MATERIAL: | DWG NO. | A3 304 SS
