opencomputeproject/Time-Appliance-Project/DOC/Artwork/timecard_2_final.pdf

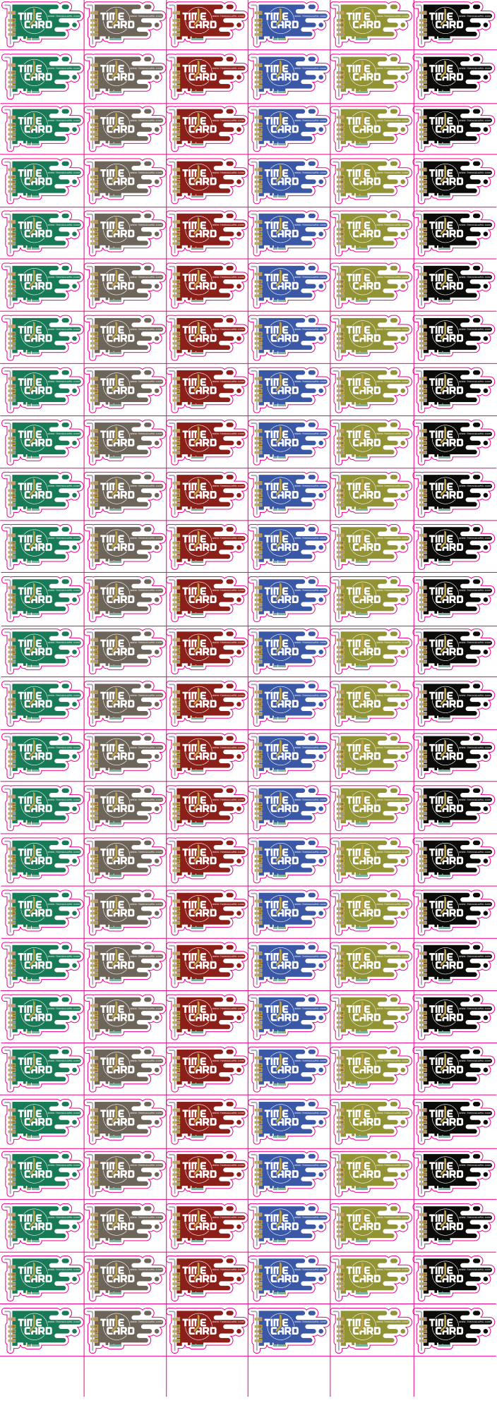
[picture p286: page 1]

www.timingcard.com
