opencomputeproject/Time-Appliance-Project/DOC/Artwork/timecard_2.pdf

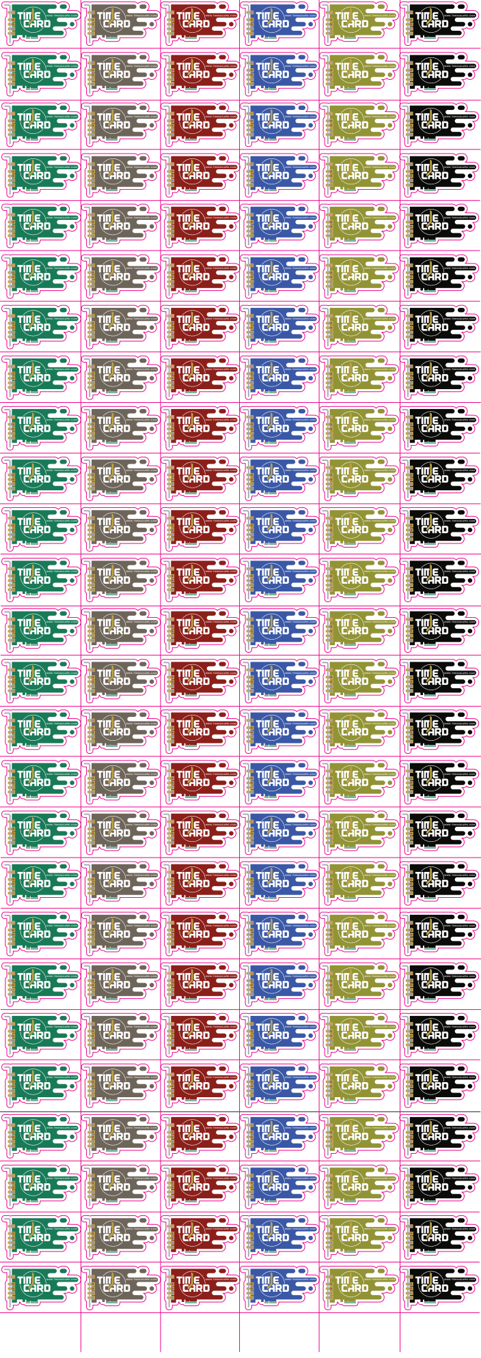
[picture p287: page 1]

www.timingcard.com
