opencomputeproject/Time-Appliance-Project/DOC/Artwork/Time-Card-sticker.pdf

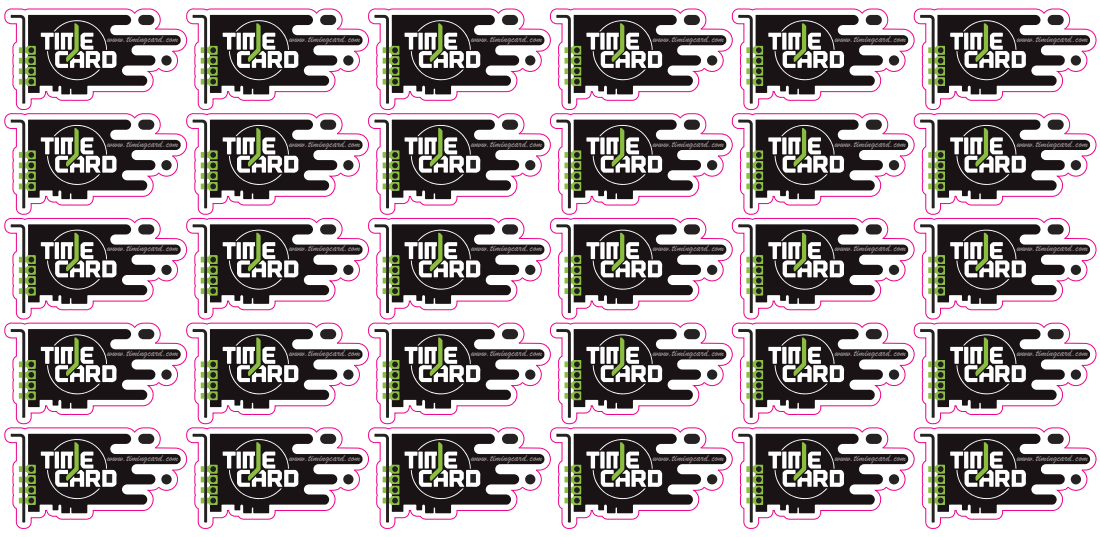
[picture p288: page 1]
www.timingcard.com
