opencomputeproject/Time-Appliance-Project/DOC/Artwork/TIMECARD.pdf

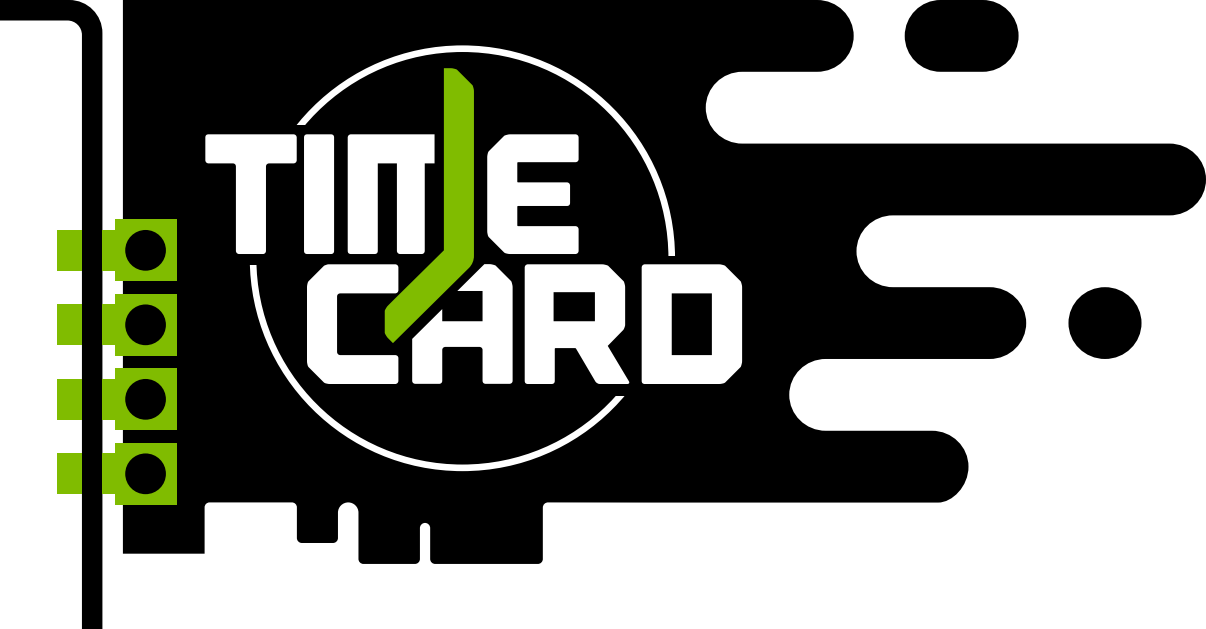
[picture p289: page 1]
