opencomputeproject/Time-Appliance-Project/GNSS/UBlox/M2-NEO-M9N/M2_NEO-M9N_MODULE.pdf

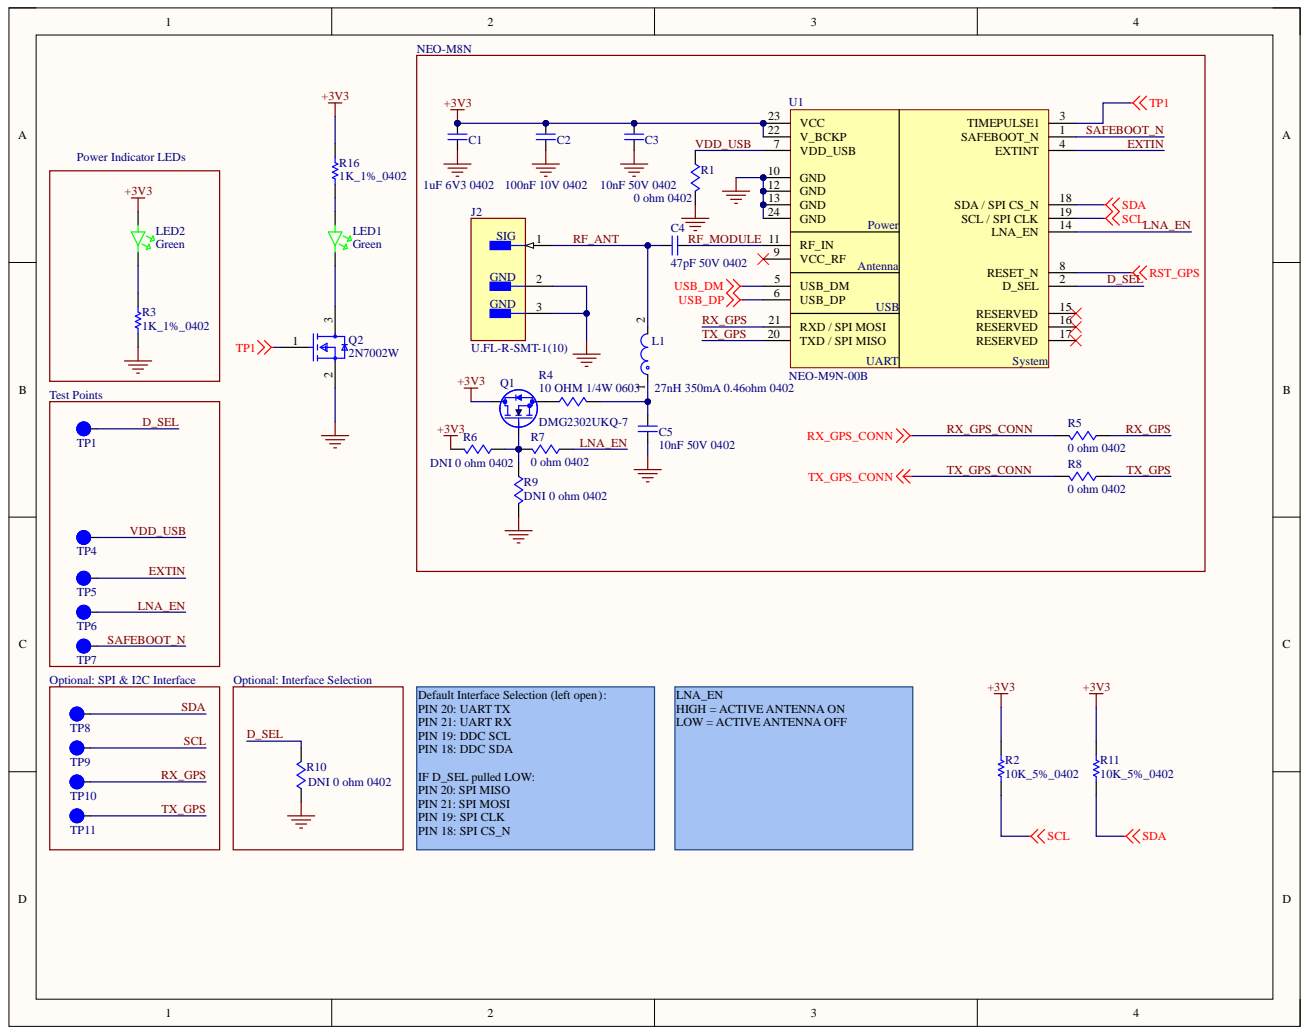
[picture p290: page 1]

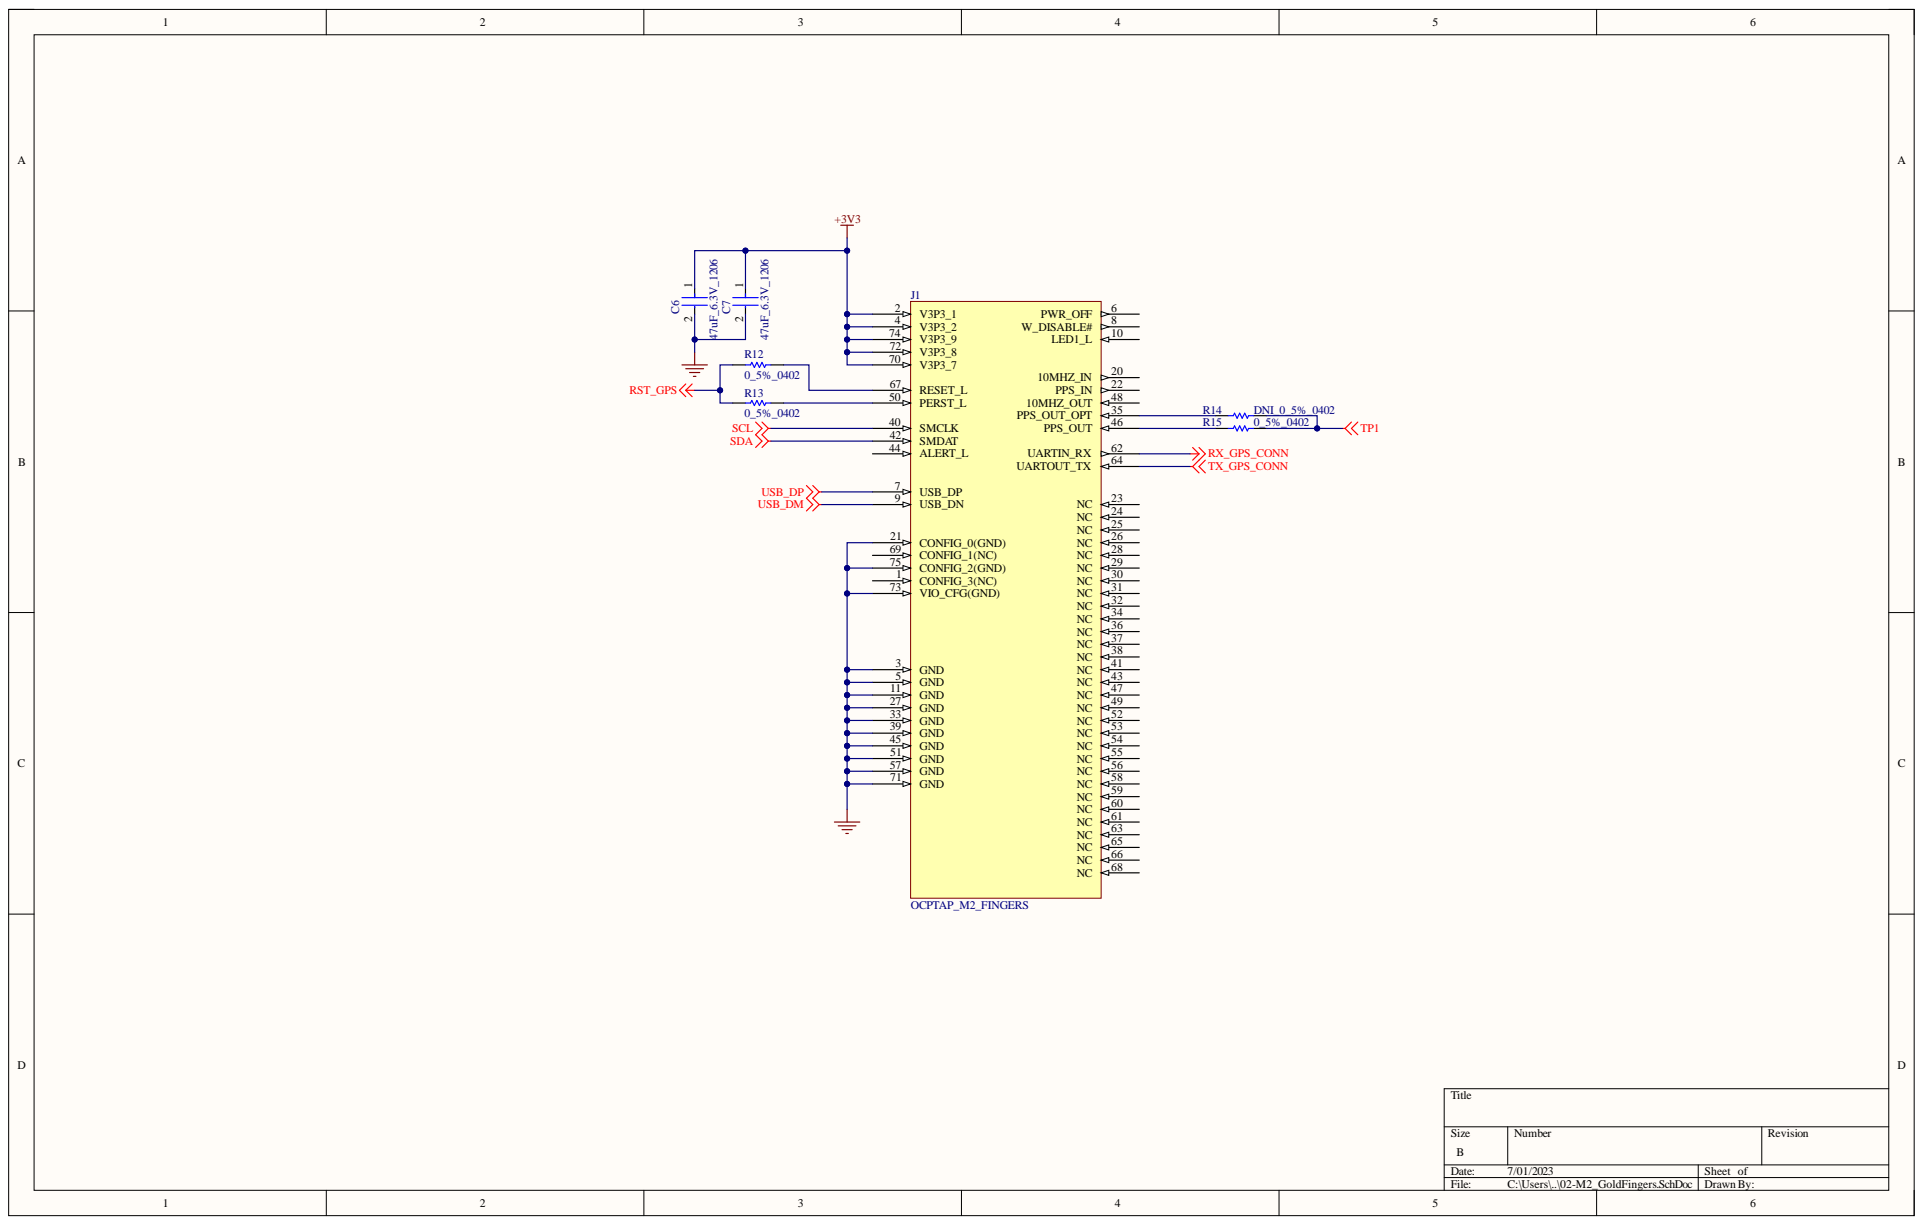
[picture p291: page 2]

CONFIG_1(NC) 69

CONFIG_3(NC) 1

Size B | Number | Revision

Date: 7/01/2023 | Sheet of
File: C:\Users\..\02-M2_GoldFingers.SchDoc | Drawn By:
