opencomputeproject/Time-Appliance-Project/FPGA/Open-Source/Implementation/Xilinx/TimeCard_Production/Constraints/GoldenImageConstraint.xdc

#GENERAL
#GOLDEN Image
set_property BITSTREAM.GENERAL.COMPRESS TRUE [current_design]
set_property BITSTREAM.CONFIG.CONFIGRATE 50 [current_design]
set_property BITSTREAM.CONFIG.SPI_BUSWIDTH 4 [current_design]
set_property BITSTREAM.CONFIG.UNUSEDPIN PULLNONE [current_design]
set_property BITSTREAM.CONFIG.CCLKPIN PULLNONE [current_design]
set_property BITSTREAM.CONFIG.CONFIGFALLBACK ENABLE [current_design]
set_property BITSTREAM.CONFIG.NEXT_CONFIG_ADDR 0x0400000 [current_design]
set_property BITSTREAM.CONFIG.NEXT_CONFIG_REBOOT ENABLE [current_design]
set_property BITSTREAM.CONFIG.TIMER_CFG 0x0007a120 [current_design]
set_property CONFIG_MODE SPIx4 [current_design]
