opencomputeproject/Time-Appliance-Project/FPGA/Open-Source/Ips/PpsGenerator/PpsGenerator.vhd

--*****************************************************************************************
-- Project: Time Card
--
-- Author: Ioannis Sotiropoulos, NetTimeLogic GmbH
--
-- License: Copyright (c) 2022, NetTimeLogic GmbH, Switzerland, <contact@nettimelogic.com>
-- All rights reserved.
--
-- THIS PROGRAM IS FREE SOFTWARE: YOU CAN REDISTRIBUTE IT AND/OR MODIFY
-- IT UNDER THE TERMS OF THE GNU LESSER GENERAL PUBLIC LICENSE AS
-- PUBLISHED BY THE FREE SOFTWARE FOUNDATION, VERSION 3.
--
-- THIS PROGRAM IS DISTRIBUTED IN THE HOPE THAT IT WILL BE USEFUL, BUT
-- WITHOUT ANY WARRANTY; WITHOUT EVEN THE IMPLIED WARRANTY OF
-- MERCHANTABILITY OR FITNESS FOR A PARTICULAR PURPOSE. SEE THE GNU
-- LESSER GENERAL LESSER PUBLIC LICENSE FOR MORE DETAILS.
--
-- YOU SHOULD HAVE RECEIVED A COPY OF THE GNU LESSER GENERAL PUBLIC LICENSE
-- ALONG WITH THIS PROGRAM. IF NOT, SEE <http://www.gnu.org/licenses/>.
--
--*****************************************************************************************

--*****************************************************************************************
-- General Libraries
--*****************************************************************************************
library ieee;
use ieee.std_logic_1164.all;
use ieee.numeric_std.all;
use ieee.math_real.all;

--*****************************************************************************************
-- Specific Libraries
--*****************************************************************************************
library TimecardLib;
use TimecardLib.Timecard_Package.all;

--*****************************************************************************************
-- Entity Declaration
--*****************************************************************************************
-- The PPS Generator generates a Pulse Per Second (PPS) aligned to the local clock's     --
-- new second. The local clock is provided as input. The core can be configured by an    --
-- AXI4Light-Slave Register interface. A high resolution clock is used for the pulse     --
-- generation to reduce the jitter.                                                      --
-------------------------------------------------------------------------------------------
entity PpsGenerator is
    generic (
        ClockPeriod_Gen                             :       natural := 20;  
        CableDelay_Gen                              :       boolean := false;
        OutputDelay_Gen                             :       natural := 0;       
        OutputPolarity_Gen                          :       boolean := true;        
        HighResFreqMultiply_Gen                     :       natural range 4 to 10 := 5;
                                
        Sim_Gen                                     :       boolean := false
    );          
    port (          
        -- System           
        SysClk_ClkIn                                : in    std_logic;
        SysClkNx_ClkIn                              : in    std_logic := '0';
        SysRstN_RstIn                               : in    std_logic;
                
        -- Time Input                       
        ClockTime_Second_DatIn                      : in   std_logic_vector((SecondWidth_Con-1) downto 0);
        ClockTime_Nanosecond_DatIn                  : in   std_logic_vector((NanosecondWidth_Con-1) downto 0);
        ClockTime_TimeJump_DatIn                    : in   std_logic;
        ClockTime_ValIn                             : in   std_logic;
                
        -- Pps Output                       
        Pps_EvtOut                                  : out   std_logic;
                
        -- Axi                  
        AxiWriteAddrValid_ValIn                     : in    std_logic;
        AxiWriteAddrReady_RdyOut                    : out   std_logic;
        AxiWriteAddrAddress_AdrIn                   : in    std_logic_vector(15 downto 0);
        AxiWriteAddrProt_DatIn                      : in    std_logic_vector(2 downto 0);
                
        AxiWriteDataValid_ValIn                     : in    std_logic;
        AxiWriteDataReady_RdyOut                    : out   std_logic;
        AxiWriteDataData_DatIn                      : in    std_logic_vector(31 downto 0);
        AxiWriteDataStrobe_DatIn                    : in    std_logic_vector(3 downto 0);
                
        AxiWriteRespValid_ValOut                    : out   std_logic;
        AxiWriteRespReady_RdyIn                     : in    std_logic;
        AxiWriteRespResponse_DatOut                 : out   std_logic_vector(1 downto 0);
        
        AxiReadAddrValid_ValIn                      : in    std_logic;
        AxiReadAddrReady_RdyOut                     : out   std_logic;
        AxiReadAddrAddress_AdrIn                    : in    std_logic_vector(15 downto 0);
        AxiReadAddrProt_DatIn                       : in    std_logic_vector(2 downto 0);
                
        AxiReadDataValid_ValOut                     : out   std_logic;
        AxiReadDataReady_RdyIn                      : in    std_logic;
        AxiReadDataResponse_DatOut                  : out   std_logic_vector(1 downto 0);
        AxiReadDataData_DatOut                      : out   std_logic_vector(31 downto 0)
    );
end entity PpsGenerator;

--*****************************************************************************************
-- Architecture Declaration
--*****************************************************************************************
architecture PpsGenerator_Arch of PpsGenerator is
    --*************************************************************************************
    -- Procedure Definitions
    --*************************************************************************************

    --*************************************************************************************
    -- Function Definitions
    --*************************************************************************************

    --*************************************************************************************
    -- Constant Definitions
    --*************************************************************************************
    -- High resolution constants
    constant HighResClockPeriod_Con                 : natural := (ClockPeriod_Gen/HighResFreqMultiply_Gen);
    constant RegOutputDelay_Con                     : natural := ((3 * ClockPeriod_Gen) + HighResClockPeriod_Con);
    -- The total output delay consists of 
    --     - the configurable output delay compensation(generic input), due to output registers
    --     - the cable delay compensation, provided by AXI reg, if enabled by the generic input
    --     - the internal register delay compensation for the clock domain crossing
    constant OutputDelaySum_Con                     : integer := (OutputDelay_Gen + (ClockPeriod_Gen/2) + RegOutputDelay_Con);

    constant OutputPulseWidthMillsecond_Con         : natural := 500;
    
    -- PPS Generator version
    constant PpsGenMajorVersion_Con                 : std_logic_vector(7 downto 0) := std_logic_vector(to_unsigned(0, 8));
    constant PpsGenMinorVersion_Con                 : std_logic_vector(7 downto 0) := std_logic_vector(to_unsigned(1, 8));
    constant PpsGenBuildVersion_Con                 : std_logic_vector(15 downto 0) := std_logic_vector(to_unsigned(0, 16));
    constant PpsGenVersion_Con                      : std_logic_vector(31 downto 0) := PpsGenMajorVersion_Con & PpsGenMinorVersion_Con & PpsGenBuildVersion_Con;
    
    -- AXI regs                                                       Addr       , Mask       , RW  , Reset
    constant PpsGenControl_Reg_Con                  : Axi_Reg_Type:= (x"00000000", x"00000001", Rw_E, x"00000000");
    constant PpsGenStatus_Reg_Con                   : Axi_Reg_Type:= (x"00000004", x"00000001", Wc_E, x"00000000");
    constant PpsGenPolarity_Reg_Con                 : Axi_Reg_Type:= (x"00000008", x"00000001", Rw_E, x"00000000");
    constant PpsGenVersion_Reg_Con                  : Axi_Reg_Type:= (x"0000000C", x"FFFFFFFF", Ro_E, PpsGenVersion_Con);
    constant PpsGenPulseWidth_Reg_Con               : Axi_Reg_Type:= (x"00000010", x"000003FF", Rw_E, x"00000000"); -- unused
    constant PpsGenCableDelay_Reg_Con               : Axi_Reg_Type:= (x"00000020", x"0000FFFF", Rw_E, x"00000000");

    constant PpsGenControl_EnableBit_Con            : natural := 0;
    constant PpsGenStatus_ErrorBit_Con              : natural := 0;    
    constant PpsGenPolarity_PolarityBit_Con         : natural := 0;

    --*************************************************************************************
    -- Type Definitions
    --*************************************************************************************

    --*************************************************************************************
    -- Signal Definitions
    --*************************************************************************************
    signal Enable_Ena                               : std_logic;
    signal Polarity_Dat                             : std_logic;
    signal PulseWidth_Dat                           : std_logic_vector(9 downto 0);
    signal CableDelay_Dat                           : std_logic_vector(15 downto 0);
    
    -- Time Input           
    signal ClockTime_Second_DatReg                  : std_logic_vector((SecondWidth_Con-1) downto 0);
    signal ClockTime_Nanosecond_DatReg              : std_logic_vector((NanosecondWidth_Con-1) downto 0);
    signal ClockTime_TimeJump_DatReg                : std_logic;
    signal ClockTime_ValReg                         : std_logic;

    -- count the high resolution ticks
    signal PpsShiftSysClk_DatReg                    : std_logic_vector((HighResFreqMultiply_Gen-1) downto 0);
    signal PpsShiftSysClk1_DatReg                   : std_logic_vector((HighResFreqMultiply_Gen-1) downto 0) := (others => '0');
    signal PpsShiftSysClkNx_DatReg                  : std_logic_vector(((HighResFreqMultiply_Gen*2)-1) downto 0) := (others => '0');
    
    signal PpsError_Reg                             : std_logic;
    signal Pps_Reg                                  : std_logic;
    signal PulseWidthCounter_CntReg                 : integer;
    
    -- AXI signals and regs
    signal Axi_AccessState_StaReg                   : Axi_AccessState_Type:= Axi_AccessState_Type_Rst_Con;
    signal AxiWriteAddrReady_RdyReg                 : std_logic;       
    signal AxiWriteDataReady_RdyReg                 : std_logic;   
    signal AxiWriteRespValid_ValReg                 : std_logic;
    signal AxiWriteRespResponse_DatReg              : std_logic_vector(1 downto 0);   
    signal AxiReadAddrReady_RdyReg                  : std_logic;          
    signal AxiReadDataValid_ValReg                  : std_logic;
    signal AxiReadDataResponse_DatReg               : std_logic_vector(1 downto 0);
    signal AxiReadDataData_DatReg                   : std_logic_vector(31 downto 0);
                
    signal PpsGenControl_DatReg                     : std_logic_vector(31 downto 0);
    signal PpsGenPolarity_DatReg                    : std_logic_vector(31 downto 0);
    signal PpsGenStatus_DatReg                      : std_logic_vector(31 downto 0);
    signal PpsGenVersion_DatReg                     : std_logic_vector(31 downto 0);
    signal PpsGenPulseWidth_DatReg                  : std_logic_vector(31 downto 0); -- unused
    signal PpsGenCableDelay_DatReg                  : std_logic_vector(31 downto 0);
    
--*****************************************************************************************
-- Architecture Implementation
--*****************************************************************************************
begin

    --*************************************************************************************
    -- Concurrent Statements
    --*************************************************************************************
    AxiWriteAddrReady_RdyOut                        <= AxiWriteAddrReady_RdyReg;        
    AxiWriteDataReady_RdyOut                        <= AxiWriteDataReady_RdyReg;   
    AxiWriteRespValid_ValOut                        <= AxiWriteRespValid_ValReg;
    AxiWriteRespResponse_DatOut                     <= AxiWriteRespResponse_DatReg;   
    AxiReadAddrReady_RdyOut                         <= AxiReadAddrReady_RdyReg;          
    AxiReadDataValid_ValOut                         <= AxiReadDataValid_ValReg;
    AxiReadDataResponse_DatOut                      <= AxiReadDataResponse_DatReg;
    AxiReadDataData_DatOut                          <= AxiReadDataData_DatReg;

    Polarity_Dat                                    <= PpsGenPolarity_DatReg(PpsGenPolarity_PolarityBit_Con);
    Enable_Ena                                      <= PpsGenControl_DatReg(PpsGenControl_EnableBit_Con);
    PulseWidth_Dat                                  <= PpsGenPulseWidth_DatReg(9 downto 0);
    CableDelay_Dat                                  <= PpsGenCableDelay_DatReg(15 downto 0);

    --*************************************************************************************
    -- Procedural Statements
    --*************************************************************************************
    
   -- Pulse generation on the clock domain of the high frequency clock
    SysClkNxReg_Prc : process(SysClkNx_ClkIn) is
    begin
        if ((SysClkNx_ClkIn'event) and (SysClkNx_ClkIn = '1')) then
            PpsShiftSysClk1_DatReg <= PpsShiftSysClk_DatReg;
            if (PpsShiftSysClk_DatReg /= PpsShiftSysClk1_DatReg) then
                PpsShiftSysClkNx_DatReg <= PpsShiftSysClkNx_DatReg(((HighResFreqMultiply_Gen*2)-2) downto (HighResFreqMultiply_Gen-1)) & PpsShiftSysClk_DatReg; -- copy the high resolution clock periods
            else
                PpsShiftSysClkNx_DatReg <= PpsShiftSysClkNx_DatReg(((HighResFreqMultiply_Gen*2)-2) downto 0) & PpsShiftSysClkNx_DatReg(0); -- retain the last value
            end if;
            if (Polarity_Dat = '1') then
                Pps_EvtOut <= PpsShiftSysClkNx_DatReg((HighResFreqMultiply_Gen*2)-1);
            else
                Pps_EvtOut <= not PpsShiftSysClkNx_DatReg((HighResFreqMultiply_Gen*2)-1);         
            end if;
        end if;
    end process SysClkNxReg_Prc;
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
