opencomputeproject/Time-Appliance-Project/FPGA/Open-Source/Ips/PpsSlave/PpsSlave.vhd

--*****************************************************************************************
-- Project: Time Card
--
-- Author: Ioannis Sotiropoulos, NetTimeLogic GmbH
--
-- License: Copyright (c) 2022, NetTimeLogic GmbH, Switzerland, <contact@nettimelogic.com>
-- All rights reserved.
--
-- THIS PROGRAM IS FREE SOFTWARE: YOU CAN REDISTRIBUTE IT AND/OR MODIFY
-- IT UNDER THE TERMS OF THE GNU LESSER GENERAL PUBLIC LICENSE AS
-- PUBLISHED BY THE FREE SOFTWARE FOUNDATION, VERSION 3.
--
-- THIS PROGRAM IS DISTRIBUTED IN THE HOPE THAT IT WILL BE USEFUL, BUT
-- WITHOUT ANY WARRANTY; WITHOUT EVEN THE IMPLIED WARRANTY OF
-- MERCHANTABILITY OR FITNESS FOR A PARTICULAR PURPOSE. SEE THE GNU
-- LESSER GENERAL LESSER PUBLIC LICENSE FOR MORE DETAILS.
--
-- YOU SHOULD HAVE RECEIVED A COPY OF THE GNU LESSER GENERAL PUBLIC LICENSE
-- ALONG WITH THIS PROGRAM. IF NOT, SEE <http://www.gnu.org/licenses/>.
--
--*****************************************************************************************


--*****************************************************************************************
-- General Libraries
--*****************************************************************************************
library ieee;
use ieee.std_logic_1164.all;
use ieee.numeric_std.all;
use ieee.math_real.all;

--*****************************************************************************************
-- Specific Libraries
--*****************************************************************************************
library TimecardLib;
use TimecardLib.Timecard_Package.all;

--*****************************************************************************************
-- Entity Declaration
--*****************************************************************************************
-- Timestamp the incoming event and evaluate its period and pulse width, If it is        --
-- accepted as PPS input, calculate its offset and drift, which are sent to the          --
-- corresponding PI servos.                                                              --
-------------------------------------------------------------------------------------------
entity PpsSlave is
    generic (
        ClockPeriod_Gen                             :       natural := 20;  
        CableDelay_Gen                              :       boolean := false;
        InputDelay_Gen                              :       natural := 0;             
        InputPolarity_Gen                           :       boolean := true;        
        HighResFreqMultiply_Gen                     :       natural range 4 to 10 := 5;

        DriftMulP_Gen                               :       natural range 0 to 1024 := 3;
        DriftDivP_Gen                               :       natural range 0 to 1024 := 4;
        DriftMulI_Gen                               :       natural range 0 to 1024 := 3;
        DriftDivI_Gen                               :       natural range 0 to 1024 := 16;
        OffsetMulP_Gen                              :       natural range 0 to 1024 := 3;
        OffsetDivP_Gen                              :       natural range 0 to 1024 := 4;
        OffsetMulI_Gen                              :       natural range 0 to 1024 := 3;
        OffsetDivI_Gen                              :       natural range 0 to 1024 := 16;

        Sim_Gen                                     :       boolean := false
    );
    port (
        -- System
        SysClk_ClkIn                                : in    std_logic;
        SysClkNx_ClkIn                              : in    std_logic := '0';
        SysRstN_RstIn                               : in    std_logic;

        -- Time Input
        ClockTime_Second_DatIn                      : in    std_logic_vector((SecondWidth_Con-1) downto 0);
        ClockTime_Nanosecond_DatIn                  : in    std_logic_vector((NanosecondWidth_Con-1) downto 0);
        ClockTime_TimeJump_DatIn                    : in    std_logic;
        ClockTime_ValIn                             : in    std_logic;

        -- Pps Input
        Pps_EvtIn                                   : in    std_logic;

        -- Servo Parameters
        Servo_ValIn                                 : in    std_logic := '0';
        ServoOffsetFactorP_DatIn                    : in    std_logic_vector(31 downto 0) := (others => '0');
        ServoOffsetFactorI_DatIn                    : in    std_logic_vector(31 downto 0) := (others => '0');
        ServoDriftFactorP_DatIn                     : in    std_logic_vector(31 downto 0) := (others => '0');
        ServoDriftFactorI_DatIn                     : in    std_logic_vector(31 downto 0) := (others => '0');

        -- Offset Adjustment Output
        OffsetAdjustment_Second_DatOut              : out   std_logic_vector((SecondWidth_Con-1) downto 0);
        OffsetAdjustment_Nanosecond_DatOut          : out   std_logic_vector((NanosecondWidth_Con-1) downto 0);
        OffsetAdjustment_Sign_DatOut                : out   std_logic;
        OffsetAdjustment_Interval_DatOut            : out   std_logic_vector((AdjustmentIntervalWidth_Con-1) downto 0);
        OffsetAdjustment_ValOut                     : out   std_logic;
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
